ZiadAbdelati/waveshare-boost-gauge/docs/regression-ledger.md

# Regression ledger (full history)

The operating manual lives in [../AGENTS.md](../AGENTS.md). This file is the
verbatim chronological record of bugs, experiments, measurements and the
guards they produced; it was extracted from AGENTS.md on 2026-08-14 so the
manual could stay short while nothing was lost. Do not add new rows here unless
you are also reflecting the resulting invariant in the condensed guard rails in
AGENTS.md.

Many rows below are executable through the regression runners: the host suite
in `tools/tests/` (run via `python3 tools/test_suite.py`) and the hardware
release gates (`python3 tools/check_hardware_gates.py`). See
[`tools/tests/README.md`](../tools/tests/README.md) for the row -> test mapping.

The ledger table below has one row per entry: | Sequence | Symptom / finding | Root cause | Fix | Guard now required |.

## Chronological regression ledger

| Sequence | Symptom / finding | Root cause | Fix | Guard now required |
|---|---|---|---|---|
| iOS companion round 4: theme-specific settings moved to Themes-tab dropdowns, 5-minute logs window on both transports, landscape two-pane layouts (2026-08-26, iOS 26.3 simulator AF01E940 + host xcodebuild: 61 unit tests + 8 SimAcceptance green, Round4ScreenshotUITests portrait+landscape to /tmp/boostgauge-shots, vision QA PASS) | (1) Settings → Theme & demo still carried the three THEME-SPECIFIC toggles (Vault needle red, Vault needle tail, Big digit static bg) that `apps/PARITY.md` moved into the Themes-tab editor dropdowns; (2) the Logs graph defaulted to `limit=300` and then a background task re-fetched the FULL one-hour ring (`readLogSamples(limit: 18_000)`) — that payload times out over BLE into the 8-sample BGL1 fallback and an hour of dense sweep rendered as meaningless top/bottom bands; (3) every screen was single-column portrait-stacked, wasting the extra width in landscape. | The pre-PARITY Settings page combined global and theme flags; `LogsViewModel` was written when the app still offered a full-hour HTTP history surface (round-3 ledger), so it defaulted small then upgraded to 18,000; no orientation branching existed in the SwiftUI views (the Info.plist already declared landscape — the project had no orientation lock to lift). | (1) Removed the three toggles from `SettingsView.themeFlagsSection` and stripped `vaultNeedleRed`/`vaultNeedleTail`/`bigDigitStaticBg` from `SettingsViewModel` (published vars, `saveThemeFlags()` body, `applyThemeFlags()` decode) — the Theme & demo PUT now sends only demoMode/demoFastSweep/rotation/regionDBuf/teSync/teScanline/pixelShift(+interval) and can never clobber theme settings. The three settings already lived in the Themes editor dropdowns with their established labels (vault-tec: "Red needle"/"Counterweight tail", big-digit: "Static background"); bindings/save paths unchanged. (2) `LogsViewModel.load()` now fetches `GET /logs?limit=1500` (5 min at the 5 Hz log rate, `graphLimit`) as the PRIMARY on both paths — HTTP transport, or the derived HTTP host for BLE, or the BLE Control /logs route on the simulator — with NO 18,000 background fetch; the 8-sample BGL1 window (`readLogSamples(limit: 8)`) is a last-resort degraded error state ("BLE diagnostic window · 8 samples" + "5-minute history unavailable: …"). Copy updated: "Full history · N" → "Last 5 minutes · N samples". `SimBleTransport` now honors `?limit=` on `/logs` (no limit = the 18,000 ring; 1500 = the last 5 minutes) and `readLogSamples`/`readLog` always return the capped 8-sample window, mirroring the real Log characteristic. (3) Landscape via `@Environment(\.verticalSizeClass)`: StatusView lays the gauge card beside a TPMS/sensors/OBD2 stack in compact-vertical (landscape); ThemesView shows the circular preview in a 360 pt sidebar beside the theme List; Logs and Settings stay single-column. Same cards, colors, bezels, typography — no stretching. | Settings → Theme & demo is global/demo/debug flags ONLY (PARITY.md); theme-specific settings live exclusively in the Themes-tab editor dropdowns and the Settings save must never send them. The Logs graph fetches `/logs?limit=1500` on both transports and NEVER defaults to the 18,000 ring; the 8-sample BGL1 window is an error state only. Landscape layouts branch on `verticalSizeClass == .compact`; a capture quirk note for future sim work: rotating via `XCUIDevice.shared.orientation` makes the app lay out landscape (AX window 844×390) but the simulator framebuffer keeps the portrait buffer with the UI rotated 90°, so landscape screenshots must rotate the raw `app.windows.firstMatch.screenshot()` by 90° before review. |
| iOS companion round 5: single-series logs graph, graph readability (psi gridlines, time ticks, crosshair, window chips), width-relative landscape layouts (2026-08-26, iOS 26.3 simulators AF01E940 16e + C27D49FE Pro Max: build green, 65 unit tests + 10/10 SimAcceptance + 2/2 mock-backed UI tests green, Round5BScreenshotUITests portrait+landscape fresh captures to /tmp/boostgauge-shots/ios-round5b-*, Gemini vision QA PASS after one FAIL iteration) | (1) On a physical iPhone the logs graph drew TWO squiggly lines at a constant vertical offset; (2) the graph had no axis labels, no time ticks, no crosshair, and no window control — just a raw stroke; (3) round-4 landscape used fixed pt widths tuned on the small 16e sim, so on the Pro Max landscape Status/Themes content cramped into the left third, and the Themes landscape sidebar painted a different background below its pane boundary (a List-vs-custom-background seam). Vision QA additionally caught: landscape captures rotated the wrong way (180° off) and the five full "HH:mm:ss" time-tick labels collided on narrow portrait plots. | (1) The chart previously reduced each display column to a per-column MIN and MAX pair and stroked BOTH extrema as separate cyan lines — on the demo fast-sweep triangle (symmetric ±12 psi) the two extrema sit ~6 psi apart, so a dense sweep rendered as two parallel squiggles at constant offset. (2) The chart was a bare `Path` stroke with no axis furniture. (3) `StatusView`'s compact HStack and `ThemesView`'s 360 pt preview sidebar were content-sized or fixed-width, so they did not span a wide landscape screen; the Themes preview pane had no grouped-background treatment, so the List's own background ended at the pane boundary. The landscape raw window capture is stored by the simulator in a portrait buffer rotated 90°, and `sips -r 90` was the wrong direction (needs 270°). | (1) `LogPressureChart.series()` now reduces each column to ONE representative value (the column's last raw sample) and the chart strokes exactly one cyan line; psi is the only series drawn (peakPsi never enters the chart). Regression tests pin it: `testLogPressureChartSeriesIsOneValuePerColumn` (never a min/max envelope pair), `testLogPressureChartSeriesPreservesFastSweepExtremes` (full raw extent, no second track), `testLogPressureChartSampleIndexMapsColumnToRawSample`. (2) Graph readability added in `LogsView`: left psi gridlines with values (`chartDomain` snaps to nice steps, always includes 0), bottom time ticks (compact "HH:mm", collision-dropped when the plot is too narrow to fit five), a tap/drag crosshair showing psi + timestamp in a cyan pill that clears on release (fixture-pinned by `-e2eCrosshair` for screenshots), window chips 1m/5m/15m → `/logs?limit=300/1500/4500` with 5m default (`LogWindow`, `graphLimit` 1500). (3) Landscape: StatusView branches on `verticalSizeClass == .compact` into two `.frame(maxWidth: .infinity)` panes; ThemesView uses a width-relative preview pane via `containerRelativeFrame` (clamped 40% / 300-420 pt) beside the theme list, with `.scrollContentBackground(.hidden)` + `Color(.systemGroupedBackground)` on the preview pane so both panes share one grouped background (no seam). Landscape captures are host-rotated by `sips -r 270`. | The logs graph renders ONE psi series per display column — never a min/max envelope or a second peakPsi track, or the fast sweep draws twin parallel lines. The graph keeps the 5-minute default (`/logs?limit=1500`, never the 18,000 ring) and its window chips must stay 1m/5m/15m → 300/1500/4500. Time-tick labels must never overlap: compact "HH:mm" plus drop labels that collide on narrow plots. Landscape layout must be width-relative (GeometryReader/containerRelativeFrame/`.frame(maxWidth:.infinity)`) on BOTH device sizes — never fixed-pt panes — and any pane beside a List must share the List's grouped background so the shade never changes partway. The simulator landscape capture is a portrait buffer rotated 90°; host rotation must be 270°. Re-run: unit suite, SimAcceptance, and the Round5B screenshot capture before committing; verify fresh screenshots with the multimodal QA agent. |
| Android companion round 5: single-series logs graph, graph readability (psi gridlines, time ticks, crosshair, window chips) — iOS round-5 parity (2026-08-26, emulator-5554 simBle on demo fast-sweep triangle: compileDebugKotlin + testDebugUnitTest green with 56 unit tests incl. 9 new LogsChartReductionTest, assembleDebug + install green, portrait/landscape/crosshair captures to /tmp/boostgauge-shots/android-round5-logs-{portrait,landscape,crosshair}.png, Gemini vision QA PASS after one FAIL iteration on the landscape fold) | (1) The Android logs chart rendered the same two-line bug the iOS chart just fixed: it downsampled each display column to a per-column MIN/MAX pair and stroked BOTH the smoothed minima and maxima as separate cyan lines, so the demo fast-sweep triangle (symmetric ~±10-15 psi) drew as two parallel squiggles at a constant offset. (2) The chart had no psi gridlines/value labels, no time ticks, no crosshair, and no window control. (3) Round-4 Android chips were capped at {300,1500} and there was no 1m/5m/15m chip group or `/logs?limit=300/1500/4500` mapping; the graph also had no anchor-based absolute time labels. | Android `LogPressureChart` in `LogsScreen.kt` used `downsample()` returning `(mins, maxs)` per column and drew `trace(smoothMins,…)` AND `trace(smoothMaxs,…)` as two cyan `drawPath` strokes — the exact envelope pattern that renders as twin parallel lines under a dense sweep. There were no axis/gesture layers and `LogsViewModel` had no window enum or `/state` anchor for wall-clock labels. | (1) `LogPressureChart` now reduces each column to ONE representative value — the column's LAST raw sample (`chartSeries()`) — and strokes exactly one cyan path; `downsample`/`smoothEnvelope`/`smooth` deleted. Pinned by 9 new `LogsChartReductionTest` cases (one value per column, fast-sweep extremes preserved, sample-index mapping, nice-step domain, tick labels, collision-dropped axis ticks). Verified against the LIVE board fast sweep (`http://192.168.50.102/api/v1/logs?limit=1500`, raw -14.49/9.99 psi): 988 display columns, one value each, series extremes identical to raw — a single line, never an envelope. (2) Ported the iOS `LogsView.swift` furniture: horizontal psi gridlines with right-aligned value labels in the left gutter (`chartDomain` nice-step bounds, zero included), dashed zero line, bottom HH:mm time ticks collision-dropped when the plot is too narrow (46 dp min spacing), and a tap/drag crosshair (dashed cyan vertical line + dot + cyan pill "X.X psi · HH:mm:ss") that clears on release, anchored to absolute wall-clock via `repository.status` epoch/uptime/offset with a relative "-M:SS" fallback. `--ez e2eCrosshair true` fixture mirrors iOS `-e2eCrosshair` for deterministic captures. (3) `LogWindow` enum added (1m/5m/15m → 300/1500/4500, default 5m/1500) with cyan-highlighted capsule chips in the card header; source label reads the window scope. Chart geometry is density-consistent (single `plotRectPx` shared by draw and pointer mapping) so the crosshair column snap matches the drawn columns. | The logs graph renders ONE psi series per display column — never a min/max envelope or a second track, or the fast sweep draws twin parallel lines. Keep the graph's 5-minute default (`/logs?limit=1500`, never the 18,000 ring) and the chips at 1m/5m/15m → 300/1500/4500. Time-tick labels must never overlap (compact HH:mm + collision drop on narrow plots). The crosshair must clear on release and the psi gridlines/time ticks must stay legible in both orientations; Logs is a scrolling list in landscape, so captures must scroll the chart clear of the bottom nav bar (a swipe starting on the chart is consumed by the crosshair gesture, matching iOS). Re-run: Gradle compile/unit tests with `--rerun-tasks`, fresh emulator captures, and the multimodal QA agent before committing. |
| Android companion round 4: theme-specific settings moved out of Settings, 5-minute logs window on both transports, landscape two-pane layouts (2026-08-26, host + emulator-5554 simBle, vision QA) | (1) Settings → Theme & demo still carried the theme-specific toggles (Vault needle red, Vault needle tail, Big digit static bg) that PARITY.md moved into the Themes-tab editor dropdowns; (2) the logs graph defaulted to `limit=300` and BLE-without-LAN silently graphed the 8-sample BGL1 diagnostic window as if it were history; (3) all screens were single-column, wasting the extra width in landscape. | The pre-PARITY Settings page combined global and theme flags; `LogsViewModel` defaulted to 300 and `GaugeApi.getLogs` fell back to `readLog()` (8 samples) when the device-info STA IP was unreachable; no orientation branching existed in the Compose screens. | (1) Removed `vaultNeedleRed`/`vaultNeedleTail`/`bigDigitStaticBg` from `SettingsViewModel.FieldState` and the `saveThemeFlags` patch; Theme & demo now saves only demoMode/demoFastSweep/rotation/regionDBuf/teSync/teScanline/pixelShift(+interval). The three settings live only in the Themes editor dropdown with the iOS labels (Red needle, Counterweight tail, Static background — Android previously said "Needle tail"). (2) Logs default to `limit=1500` (5 min at the 5 Hz log rate, `LogsViewModel.LOG_WINDOW_SAMPLES`); chips capped at {300, 1500}; source label reads "Last 5 minutes · N samples". `GaugeApi.getLogs` on BLE prefers the LAN HTTP host from device-info, then a transport-served window (the emulator sim), else throws — an 8-sample BGL1 band is never graphed (error state only). (3) Landscape: Dashboard splits into two scrolling panes (hero+sensors | TPMS+OBD+error+footer); Themes becomes a square preview pane left of the scrolling theme list, capped to the pane's shorter side so it never overflows the short viewport; Settings stays single-column. Colors/bezels/typography unchanged. | Settings → Theme & demo is global/demo/debug flags ONLY; theme-specific settings appear exclusively inside the matching theme's editor dropdown with labels identical to iOS. The logs graph is the last 5 minutes (`/logs?limit=1500`) on BOTH transports and the 8-sample BGL1 window is a last-resort error state, never graph data. Landscape must use the extra width (side-by-side panes), never letterbox/stretch, and keep the portrait style identical. |
| iOS companion settings restructured to the canonical PARITY.md IA; sim transport made the scheme-default launch (2026-08-26, iOS 26.3 simulator AF01E940 + host xcodebuild, vision QA PASS) | The iOS Settings view had drifted from `apps/PARITY.md`: the psi range fields were duplicated on the "Display" page (Display should be brightness + dim schedule only), `appBle` had no spec home, and the default Xcode/simulator run showed no live data (no sim transport). Two latent defects surfaced while wiring it: (1) `project.yml` used `launchArguments:` (not a real XcodeGen key) so the scheme XML had an EMPTY LaunchAction command-line block; (2) when `commandLineArguments` was added to the top-level scheme, the BoostGauge TARGET's `scheme: testTargets:` block shadowed the top-level scheme, so the generated LaunchAction STILL had no `-e2eSimBle`; and once the arg finally landed, the 9 AppSessionTests broke because app-hosted unit tests inherit the scheme's Run-action launch args (`PROCESS_ARGS=...App|-e2eSimBle` proven in a scratch project), so `AppSession.init` saw `-e2eSimBle` and forced `SimBleTransport` for every test. SimBleTransport also lacked `tpms/config`, so the Settings root showed a spurious "TPMS: The selected gauge is no longer in range" error banner. | (1) XcodeGen only recognizes `commandLineArguments: {arg: enabled}` under run/test/profile; `launchArguments` is silently ignored. (2) A target-level `scheme:` block and a same-named top-level `schemes:` entry collide, and the target scheme wins (drops the run args). (3) `ProcessInfo.processInfo.arguments` in a hosted XCTest process contains the scheme's LaunchAction arguments, so E2E launch-arg flags leak into unit tests. (4) `SimBleTransport.get/send` handled only state/themes/config/calibration/logs — not `tpms/config`. | SettingsView: Display = brightness high/low + dim schedule + start/end + `appBle` (kept per "keep all bindings identical"; PARITY table omits it — intentional exception) + Save; Range = psiMin/psiMax/psiOverboost/zeroAngle + Save; TPMS BLE link moved off Theme & demo onto the TPMS page; root order Connection → Display → Range → Theme & demo → Clock & timezone → TPMS. project.yml: removed the redundant target-level `scheme:` block, added `run.commandLineArguments: {"-e2eSimBle": true}`, aligned target `IPHONEOS_DEPLOYMENT_TARGET` to 17.0 (the app already used iOS-17 `contentMargins`), regenerated with xcodegen (verified `argument = "-e2eSimBle"` in the scheme LaunchAction). AppSession init gates `-e2eSimBle`/`-hardwareBleE2E` on `NSClassFromString("XCTestCase") == nil` so hosted unit tests never inherit the sim/hardware E2E mode. SimBleTransport now serves GET/PUT `tpms/config`. SimAcceptanceUITests `testSettingsSubPagesAndTimezonePicker` updated to the new Display/Range/Theme&demo/TPMS pages (was asserting the removed "Gauge" page) and now also asserts root row ORDER and that TPMS BLE link lives only on TPMS; `SettingsAppBleUITests` navigates Display for the `appBle` toggle. | Keep the settings IA byte-for-byte with `apps/PARITY.md` (root order + exact titles; `tpmsBle` only on TPMS; `appBle` kept on Display as the single recorded exception). The scheme run args are `commandLineArguments` (never `launchArguments`), there must be no same-named target `scheme:` block shadowing the top-level scheme, and any `-e2eSimBle`/`-hardwareBleE2E`-style launch-arg flag MUST be ignored under XCTest (hosted unit tests inherit LaunchAction args). SimBleTransport must mirror the real API surface so the Settings root never shows a spurious not-in-range banner. Re-run: 61 unit tests green, full SimAcceptanceUITests green, vision QA on the four Settings screenshots PASS. |
| iOS companion themes-editor polish: expanded options panel aligned to the theme title, full-width Apply button, TPMS row icon (2026-08-26, iOS 26.3 simulator, vision QA PASS) | The expanded theme options (DisclosureGroup content) were visibly off-center: the panel content sat ~20 pt right of the theme title leading (x≈52 vs x≈32), the borderedProminent "Apply … options" button rendered as a content-hugging ~172 pt pill (`.frame(maxWidth: .infinity)` had no effect inside List DisclosureGroup content) centered in the shifted panel (x≈205 vs screen center 195), and "Reset to default colors" was left-aligned on a different axis below it. Separately the Settings TPMS row used a generic `car` glyph. | SwiftUI `List` indents `DisclosureGroup` content ~20 pt below the label, and a `Button` + `.frame(maxWidth: .infinity)` inside that content does NOT expand (the proposal resolves to the ideal width) — the pill only fills if the max-width goes on the button's LABEL. | `themeOptions` content gets `.padding(.leading, -20)` so the panel shares the theme title's leading axis; the Apply button uses `Button { } label: { Text(...).frame(maxWidth: .infinity) }` so the borderedProminent style fills the full panel (measured x 109..281 → 32..357); Reset stays flush-left on the same axis. Settings TPMS row icon changed `car` → `tirepressure`. SimAcceptance themes editor test still green (chevron, color wells, Apply button, no stray layout menu). Vision QA (rounds 1-3 + themes) PASS with zero defects. | Keep disclosure-content styling aligned to the title leading axis and make any full-width button apply `maxWidth: .infinity` to the label (not the button) inside List DisclosureGroup content. TPMS is a tire, not a car. Re-run: themes UI test + unit suite green before committing. |
| Android companion settings and theme preview parity pass (2026-08-26, host/emulator-verified) | Android settings previously combined Gauge controls, placed theme flags on Gauge, called the page TPMS & OBD2, and rendered the theme preview as a square. Clock sync also used a secondary row and descriptive copy. Two follow-ups surfaced during round-3 verification: the first canonical-render pass could land on a 0-size backing canvas (app.js resizes asynchronously), leaving the preview face solid black, and a duplicate inner pod treatment crept into `CanonicalGaugePreview`'s modifier chain, producing a doubled ring. | Android UI structure had not been split to the canonical `apps/PARITY.md` page inventory and the preview WebView had no circular pod treatment; the WebView's first `drawGauge` raced the app.js canvas resize (a later resize clears the 0-size canvas) and the rogue edit added a second pod inside the component modifier. | Android now exposes Connection, Display, Range, Theme & demo, Clock & Timezone, and TPMS in canonical order; theme flags and firmware-backed controls are grouped on their own page; clock sync is one full-width single-line "Sync timezone to gauge" button with an in-button saving spinner (timezone-only, phone zone like iOS); the preview is a padded circular pod (`ThemePreviewPod`: 1 dp dark rim + 8 dp `#0c0e12` ring + hairline rim, transparent corners, no shadow). `CanonicalGaugePreview`'s modifier is plain again (one pod, owned by the screen) and its `onPageFinished` re-runs the render at +400 ms/+1200 ms so the first paint is deterministic at the final backing size. Range field labels are the exact firmware keys (psiMin/psiMax/psiOverboost/zeroAngle); Theme & demo toggles use iOS wording; `appBle` toggle lives on Display (matches iOS; PARITY table omits it — intentional exception). | Keep Android page titles/order, field names, `tpmsBle` ownership, and circular transparent-corner preview aligned exactly with `apps/PARITY.md`; the preview pod ring lives ONLY in the screen composable (`CanonicalGaugePreview` modifier stays plain). Re-run Gradle compile/unit tests and emulator screenshot review after future UI changes. Evidence: `./gradlew compileDebugKotlin testDebugUnitTest assembleDebug` green (43 unit tests incl. `saveThemeFlagsRoundTripsNewFieldsThroughServer`), emulator-5554 simBle screenshots `/tmp/boostgauge-shots/android-round3-{themes,settings-root,display,range,themedemo,clock}.png`, Gemini visual QA PASS on all six after the render fix. |
| The DS3231 never became the clock authority: every read reported "time never set" even after a successful Sync, so the RTC always fell back to NVS (2026-08-17, built + flashed + hardware-verified) | After a clean software reboot (VCC never dropped) with a freshly seeded RTC, the boot log still showed `DS3231 detected at 0x68 (time never set - clock not trusted)` and `clock falls back to NVS/sync`; `/state.epochMs` was minutes stale on every reboot. This was true for the old DS3231 AND a replacement unit - so the chip was exonerated. | `boost_sensors_rtc_write()` wrote only the time registers (0x00-0x06); on the DS3231 writing the time does NOT auto-clear the oscillator-stop flag (status 0x0F bit 7). The seed path is gated on a clean read, so with OSF still set every read returned `ESP_ERR_INVALID_STATE` and the RTC never became trusted - it permanently fell back to the NVS epoch checkpoint. | `boost_sensors_rtc_write()` now clears OSF explicitly after the time burst: read status 0x0F, clear bit 7, write it back, all under the same bus-admin lock. Hardware-verified: after seed + software reboot the log reads `clock seeded from DS3231 (...)`, no OSF, no NVS fallback. (The earlier "battery doesn't hold time" conclusion was confounded by this bug - the RTC was losing its trusted state to a persistent OSF, not necessarily to a dead coin cell.) | A DS3231 write MUST clear the OSF bit explicitly (read-modify-write status 0x0F under the bus-admin lock); unlike some RTCs it is never auto-cleared by a time write, and a write that leaves it set keeps the RTC permanently on the NVS fallback. |
| The dashboard clock flickered 1 hour (17:44 <-> 18:44) while loading; `/state.timezoneOffsetMinutes` flip-flopped between the DST-effective and standard offset (2026-08-17, built + flashed + hardware-verified) | On web load the device clock readout rapidly alternated between an hour-apart pair of times, then settled. Polling `/state` showed `timezoneOffsetMinutes` flickering between the DST-effective value (-180 for a UTC-3 DST zone) and the stored standard (-240). | `s_state.timezone_offset_minutes` was written by four paths with conflicting semantics: `boost_model_refresh_status()` (16 ms loop) wrote the DST-EFFECTIVE value, but `boost_model_publish_sample()` (same 16 ms loop, right before) and the config-load/set_time paths wrote the STANDARD config value. Every tick publish_sample clobbered the effective value with standard and refresh_status overwrote it back, so `/state` GET (which just copies `s_state`) caught either - a sustained 1-hour clock flip in the UI. | `boost_model_publish_sample()` no longer touches `timezone_offset_minutes` (not a per-sample value; refresh_status owns it). `boost_model_set_time()` and the config-load path now write the effective offset via `boost_model_utc_offset_minutes_at(...)` so there is no standard-offset window after a sync or at boot. Hardware-verified: 30 rapid `/state` polls all report the single effective offset (-180), no flapping. | `/state.timezoneOffsetMinutes` is owned by `boost_model_refresh_status()` as the DST-EFFECTIVE value; the 16 ms `boost_model_publish_sample()` and the set_time/config-load paths must never clobber it with the stored standard offset, or the dashboard clock flickers 1 hour across DST. |
| Full-frame GIF push was ~10 ms over the wire floor (2026-08-17, built + flashed) | 466x466 full-frame push measured 21 ms in-loop against a ~13 ms wire floor; the perf push mean was 23.5 ms. Instrumented breakdown showed the byte-swap copy taking 16.2 ms (79% of the push) and DMA only ~4-6 ms. | The fused swap loop loaded/stored every pixel through `gif_u32_alias_t`, a `__aligned__(1)` typedef. Xtensa has no unaligned 32-bit load (`l32i` faults on a non-4-aligned address), so every nominal word access compiled to 4 byte loads + combines: ~10x the instructions of a plain memcpy (16.2 ms vs 5-7 ms for the same 434 KB stream). The `__aligned__(1)` alias is the anti-optimisation: it tells the compiler the pointer may be byte-aligned, so it can never emit word access. | Split the copy from the swap: one `memcpy` per strip (full-width strips collapse to a single contiguous copy; narrower strips keep per-row copies), then a tight 64-bit in-place byte-swap on the internal DMA buffer. The xfer buffers are now allocated with `heap_caps_aligned_alloc(8, ...)` (MALLOC_CAP_DMA alone only guarantees 4-byte alignment, which would make the direct `uint64_t*` access UB). A memcpy-per-8-byte variant of the swap measured ~2x worse (42 ms) from per-word call overhead and must not be reintroduced. Hardware-verified: full-frame push 21 ms -> 15.5 ms in-loop (copy 16.2 -> 7.9 ms, wire DMA ~6 ms), perf push mean 23.5 -> ~17.7 ms, cadence at 30 ms delay ~18.7 -> ~21 FPS. Colors unchanged, no panics, web healthy. | Do not reintroduce a per-pixel/per-word byte-swap through `gif_u32_alias_t` (or any `__aligned__(1)` type): on Xtensa it compiles to byte-wise access and costs ~10x a memcpy. The push strip copy must be memcpy-first then an aligned in-place swap on the internal DMA buffer. |
| GIF playback could run faster than the authored frame delay (2026-08-16, built + flashed) | Asked whether a GIF can play faster than intended: yes. The pipelined path set the timer period to `delay − last_push`, so a frame's on-screen time was `D − last_push + next_push`. A heavy full-frame push (large `last_push`) followed by a tiny delta push (small `next_push`) displayed that full frame for e.g. 13 ms against a 30 ms authored delay (~2.3x faster). A secondary race: `ms_delay_next` was read after `sem_next_decode` was given, so the Core-1 decoder could overwrite it with frame N+2's delay before the read. | The `D − last_push` compensation assumed every push takes the same time; variable push durations (full vs delta frames) made the compensation overshoot. | Deadline pacing: the next push now starts no earlier than `end_of_this_push + D`. Since the timer period is measured from the callback start and the just-completed push took `last_push_us`, the period is `D + last_push` — guaranteeing on-screen ≥ D (never faster; on average one push-duration slower, the accepted tradeoff). The frame delay is captured before waking the decoder. Hardware-verified: bulb.gif plays at its authored 30 ms cadence, 120/120 direct pushes, no panic. | The pacing guard is `period = D + last_push`, never `D − last_push`. Capture `ms_delay_next` before `xSemaphoreGive(sem_next_decode)`. |
| Post-audit fix round for the GIF playback branch (2026-08-16, built; hardware soak pending) | An independent audit of the `gif-playback-fps` diff found: (H1) the `initialize()` re-open teardown kept the double-free + fixed-15 ms decode-race the destructor fix had removed (latent — no caller re-opens a loaded widget); (H2) the `is_full_opaque` canvas-copy skip read the PREVIOUS frame's rect, so a partial/transparent frame after a full-opaque frame composited over a two-cycles-stale buffer; (H3) `sem_next_decode` was given before the push rect was read, so the Core-1 decoder could overwrite `gif->iX/iY/iW/iH` for frame N+2 while Core-0 pushed frame N+1 with a mismatched window; (M4) the LVGL fallback could not blend the RGB565_SWAPPED source (`LV_DRAW_SW_SUPPORT_RGB565_SWAPPED` = 0) so a refused direct push (e.g. regionDBuf toggled off, which frees the scratch strips) rendered a blank GIF; (M5) the fused LZW 8-pixel-wide stores could run up to 7 pixels past the framebuffer on the final string; (M6) an odd canvas origin (centered GIF < 466 px) made `r_fx` negative and the `read_fb` source offset wrap. | (H1) `initialize()` copied the pre-fix teardown; (H2) the skip keyed on stale geometry; (H3) the semaphore ordering race; (M4) the branch pre-swapped the palette to big-endian (RGB565_SWAPPED) but LVGL's sw renderer has no SWAPPED blend path, so the fallback path diverged from main; (M5) unbounded wide stores; (M6) round-down clamp below an odd origin. | (H1) `initialize()` now mirrors the destructor (snapshot fb0/fb1 before free, NULL `pFrameBuffer`, `decode_done` handshake). (H2) the canvas copy is now unconditional. (H3) the decoded rect is snapshotted into `gifobj->last_fx/fy/fw/fh` before `sem_frame_ready` and `invalidate_frame` takes the snapshot. (M4) reverted to a little-endian RGB565 framebuffer: palette loads store LE, the widget uses `LV_COLOR_FORMAT_RGB565`, and the direct push re-added the fused LE→BE byte-swap (restoring main's proven fallback; the swap cost is proportional to the dirty rect, so delta frames keep 60 FPS). (M5) framebuffers now carry a 16-pixel pad (`GIF_FB_PAD_BYTES 32`) while `imgdsc.data_size`/stride stay exact. (M6) the clamp rounds up to the next even >= origin and zero-area rects fall back to LVGL. Clean build. | The decoder must emit little-endian RGB565 (the direct push swaps; the LVGL fallback does not). The push must read the snapshot rect, not live `gif->iX/iY/iW/iH`. The canvas copy before each decode is unconditional. Fused wide stores stay within the padded framebuffer. Odd origins round up to even. Re-open teardown must use the `decode_done` handshake and snapshot-before-free. |
| Deleting the GIF crashed the board: it vanished, came back at max brightness, web down (2026-08-16, flashed + measured) | Clicking Delete in the web UI made the GIF disappear, then the board rebooted, the GIF auto-reloaded at boot brightness (100% during the day), and the web was unreachable during the reset. `DELETE /api/v1/media` panicked with `Guru Meditation` (double free) in `lv_gif_destructor`. | The dual-buffer pipeline sets `gif->pFrameBuffer = gifobj->framebuffers[idx]`, but `lv_gif_destructor` freed and NULLed `framebuffers[0]/[1]` BEFORE the ownership guard `framebuffer != framebuffers[0]` compared against them. With both pointers NULL the aliased `pFrameBuffer` slipped past the guard and was `lv_free`'d a second time -> double free -> panic -> reboot. A secondary race: the decode-task teardown used a fixed 15 ms delay, shorter than a mid-frame ~25 ms decode, so a frame in flight could touch freed framebuffers. | Snapshot `framebuffers[0]/[1]` ownership pointers before freeing them so the alias check stays meaningful, `gif->pFrameBuffer = NULL` before the pipeline frees (separate buffers still freed exactly once), and replace the 15 ms delay with a `decode_done` flag set by the decoder before `vTaskDelete` so the destructor waits out a full frame. Verified: DELETE returns 200 `present:false`, no panic in serial, board holds continuous uptime (200 s+) afterwards. | The destructor must never free an aliased pipeline framebuffer twice; snapshot ownership pointers before NULLing them and wait out any in-flight decode before freeing decoder-owned memory. A delete that reboots the board (GIF auto-reloads at boot brightness) is the failure mode to watch for in any future media-teardown change. |
| BLE disconnected retry loop saturated the radio and stalled the web when the stored peer was absent (2026-08-16, flashed + measured) | With `tpmsBle` on and the FD+ adapter not reachable (bench), the web UI periodically froze for seconds and HTTP latency spiked (p95 191 ms, max 291 ms, occasional timeouts); the physical screen briefly showed white/green streak artifacts during the worst window. Serial showed `connect failed: status=0x000d` then a 3 s discovery scan repeating every ~13 s. | The disconnected retry loop is fixed 10 s backoff + 3 s scan forever when the stored peer never answers, and the connect attempt runs a full 5 s. These periodic BLE bursts saturate the ESP32-S3's single 2.4 GHz radio, which also carries STA + SoftAP. (BLE code is identical to main; the aggression shows whenever the adapter is absent, e.g. bench, not when connected in the car.) | Exponential inter-scan backoff (`OBD_RECONNECT_MS 10000`, `OBD_RECONNECT_MAX_MS 120000`): after each failed scan/connect cycle the delay doubles (10 → 20 → 40 → 80 → 120 s cap), resetting to 10 s on any connect and on a manual re-enable. A dropped *connected* link keeps the fast 10 s retry. Measured with BLE on: p95 191 → 118 ms, max 291 → 169 ms, 0 timeouts. The prior GIF worktree regression (decode task priority starving httpd/ws on Core 1) is separate and fixed in `f548306`. | An unreachable stored peer must back off exponentially (cap ~2 min) so an absent adapter stops hammering the radio; present peers are still found within one scan period and a dropped connected link keeps a fast retry. Do not reintroduce a fixed ~13 s scan loop for the disconnected state without re-measuring web latency. |
| Fused Turbo LZW + direct big-endian RGB565 emission + Core 1 decode pinning (2026-08-16, flashed + measured) | Decode was taking ~25.2 ms due to separate 8-bit LZW decompression into `pTurboBuffer` followed by a second memory pass in `DrawCooked()` (converting 217 KB to 434 KB in PSRAM). Direct push was also taking ~18.5 ms due to scalar byte swapping in `boost_display_push_bitmap()`. | (1) Two sequential PSRAM passes (write indices -> read indices -> write RGB565) incurred unnecessary PSRAM cache line fills. (2) `boost_display_push_bitmap` performed per-pixel byte swapping instead of 32-bit paired transfers. (3) `gif_decode_task` was competing with LVGL on Core 0. | (1) Pre-swapped the 256-entry palette to big-endian RGB565 wire format during palette load. (2) Fused Turbo LZW dictionary emission directly into 16-bit RGB565 framebuffer writes (`LZWCopyBytesFused`) on full-width opaque frames, eliminating the second memory pass. (3) Replaced scalar byte swaps in direct push with 32-bit direct `memcpy` into `s_region_xfer_bufs`. (4) Pinned `gif_decode_task` to Core 1 at priority 5 and preserved the 40,960 B BLE DMA internal RAM pre-init guard. Hardware verified on 466x466 fixture (1,889,384 B, 101 frames): decode mean 24.3 ms (15.5 ms on deltas), push dropped 18.5 ms -> 13.8 ms (at the ~13.5 ms physical QSPI floor), 0 push fallbacks, 0 panics, cadence guard passing (dyno-cell demo 61 FPS). | Fused LZW palette emission applies to contiguous full-width opaque frames; partial/transparent frames retain `DrawCooked()` fallback. Direct panel push requires big-endian wire format RGB565. Keep Turbo LZW table allocations in PSRAM to prevent starving BLE/DMA internal memory pool. |
| Turbo LZW + 32-bit paired stores + dual-core pipelined decode accelerates GIF playback to 30+ FPS (2026-08-16, flashed + measured) | GIF playback on the 466x466 fixture was decode-bound at ~37.3 ms per frame, limiting serial direct-push playback to ~18 FPS regardless of transfer throughput. | (1) Standard LZW decode performed per-pixel reverse stack walks and linked-list traversals across PSRAM memory. (2) `DrawCooked()` used individual 16-bit stores for every pixel. (3) `DecodeLZWTurbo` was previously compiled out because upstream turbo required a `pfnDraw` callback with 2 planes. (4) Decode on Core 1 was serialized with panel DMA transfers. | (1) Enabled `GIF_SUPPORT_TURBO` in `boost_gif_dec.h/.c` adapted to direct-to-framebuffer `DrawCooked()`. (2) Allocated `pTurboSymbols` (16 KB) and `pTurboLengths` (8 KB) from fast internal RAM (`MALLOC_CAP_INTERNAL`) for single-cycle table access. (3) Accelerated `DrawCooked()` with 32-bit paired pixel stores (`uint32_t`) and 8-byte batch reads (`INTELLONG64`). (4) Implemented dual-core pipelining: a background `gif_decode_task` on Core 0 decodes frame N+1 into double-buffered PSRAM canvas (`framebuffers[2]`) while Core 1 transfers frame N to panel via DMA. Measured on hardware: decode dropped 37.3 ms -> 25.2 ms (-32%, and down to 13.1 ms on deltas), push 16 ms, 119 direct pushes per 120 frames, 0 fallbacks. | Turbo LZW symbol/length tables (24 KB) must stay in internal RAM for single-cycle access. Double-buffered framebuffers in PSRAM allow Core 0 decode to overlap Core 1 DMA panel transfers without data hazard. |
| Direct-push delta GIF frames suffered horizontal image shifting and streaking (2026-08-16, flashed + measured) | While full-frame GIF colors were correct, occasional partial/delta frames caused the image to visibly jump horizontally (shift to the left) and leave visual streaking artifacts across the panel. | The CO5300 AMOLED QSPI controller hardware requires CASET (column) and RASET (row) window boundaries to be 2-pixel word aligned (even x1/y1 and odd x2/y2 in inclusive coordinates, or even x0/y0/x1/y1 in exclusive coordinates). In the LVGL render path, `rounder_event_cb()` enforces this on all invalidated areas. The direct-push bypass in `boost_gif.c` passed unrounded delta frame coordinates (`img_area.x1 + fx`, `fw`, etc.) straight to `boost_display_push_bitmap()`. When a delta frame had an odd column or row start, the CO5300 hardware window misaligned with the 32-bit QSPI pixel stream, shifting the pixel data horizontally by 1 pixel. | `main/gif/boost_gif.c` now rounds the dirty rectangle coordinates to even `x1/y1` and odd `x2/y2` (matching `rounder_event_cb` and clamping to canvas bounds), computing `r_fx, r_fy, r_fw, r_fh` so that both the panel window and the `src` offset into `pFrameBuffer` are strictly 2-pixel aligned. Pushed exclusive coordinates `dirty.x1`, `dirty.y1`, `dirty.x2 + 1`, `dirty.y2 + 1` are all guaranteed even. Hardware verified: 119/120 direct pushes, 0 fallbacks, clean playback with zero horizontal shifting or streaking. | Any direct panel push path must strictly obey the CO5300 2-pixel even/odd boundary constraint (`dirty.x1` even, `dirty.x2` odd / exclusive `x1` even). Never send unrounded delta/partial coordinates directly to `esp_lcd_panel_draw_bitmap()`. |
| Direct-push GIF frames arrived color-scrambled with artifacts ("horror edit"); occasional single correct frame per loop (2026-08-16, flashed + measured) | First hardware run of `boost_display_push_bitmap()` showed fully corrupted colors and random flashing on the GIF; once per animation loop one frame looked correct. | The adapter bridge byte-swaps every RGB565 pixel to big-endian before the panel sees it (`lvgl_bridge_v9.c` `display_bridge_v9_flush_default`: `lv_draw_sw_rgb565_swap` for `ESP_LV_ADAPTER_PANEL_IF_OTHER` + RGB565, applied BEFORE the `custom_draw_bitmap` hook). The CO5300 QSPI wire format is big-endian RGB565; the GIF decoder's framebuffer is little-endian (`GIF_PALETTE_RGB565_LE`). The direct push bypassed the bridge entirely and sent little-endian pixels straight to the panel - red/blue channels swapped and the 5-bit green field misaligned. The once-per-loop correct frame was the `force_full_invalidate` LVGL fallback (which goes through the bridge swap). This is also why `region_dbuf_writeback()` must NOT swap: its strips arrive pre-swapped from the hook. | `boost_display_push_bitmap()` now byte-swaps each 20-line scratch strip after the row copy (before `esp_lcd_panel_draw_bitmap`), leaving the source framebuffer untouched little-endian LVGL image data. Hardware-verified: colors correct, 119/120 direct pushes, 0 fallbacks; push mean 18.2-18.7 ms (up from 15.7-17.6 pre-swap; the per-pixel swap costs ~2.6 ms/full frame), decode unchanged ~38 ms. | Any path that feeds `esp_lcd_panel_draw_bitmap()` directly MUST byte-swap RGB565 to big-endian first (or prove the source is already swapped); the LVGL/region-dbuf strips are pre-swapped by the bridge, direct sources are not. When adding a direct panel path, A/B against the bridge's flush (`display_bridge_v9_flush_default`) for format, stride compaction, and swap - the hook receives transformed data, not raw LVGL buffers. | | The 466x466 fixture (`IMG_5325-ezgif.com-optimize.gif`, 1,889,384 B, 101 frames, 98% full-frame dirty rects) played at 14-20 renders/s through the LVGL widget path (baseline, README). The user asked for 30 FPS minimum, 60 if possible. | Per-frame cost was serial on the LVGL task: (1) `GIF_playFrame` decode ~36.4-37.7 ms (LZW + palette LUT + PSRAM framebuffer composition), (2) LVGL render re-blit of the frame rect into internal-DMA strips (~3.16 Mpx/s measured, ~69 ms/217k px full-frame equivalent budget share), (3) QSPI transfer 13.6 ms floor. The re-blit is redundant: the decoder's framebuffer already holds panel-ready RGB565 for exactly the frame rect. | New `boost_display_push_bitmap()` in `main/boost_display.c` (exported in `boost_display.h`): pushes an RGB565 rect straight from the caller's buffer (arbitrary row stride) to the panel in the same 20-line chunks + one `te_wait_for_region_spans()` TE wait as `region_dbuf_writeback()`, reusing the region-dbuf internal DMA scratch strips (no new internal RAM; refuses with `ESP_ERR_NOT_SUPPORTED` when region-dbuf strips are unallocated, rotation != 0, or args are invalid, so the caller falls back to LVGL). `main/gif/boost_gif.c` `invalidate_frame()` now tries the direct push first under the same bounded-placement conditions as the bounded LVGL invalidation (1:1 blit, no rotation/scale); success skips the LVGL invalidation entirely, failure falls back. Timing instrumentation added (`perf:` rate-limited log): decode us and push us means/last per 120-frame window. **Measured on hardware**: 119/120 direct pushes, 0 fallbacks; decode mean 36.4-37.7 ms, push mean 15.7-17.6 ms (vs 13.6 ms pure-transfer floor; TE wait included); ~18.7 FPS on this worst-case 98%-full-frame fixture (vs 14-20 baseline). Upload 1,889,384 B in 9.52 s; delete/resume verified (gauge 61 FPS post-teardown); dyno-cell demo cadence guard min 57 / median 61 PASS; serial clean (no `ESP_ERR_NO_MEM`, no `send color data failed`). | Direct push is valid ONLY under: display lock held (LVGL task context during media), rotation 0, 1:1 bounded placement, region-dbuf scratch strips allocated. Off-by-one contract: x1/y1 end-EXCLUSIVE (a first flash measured 115/120 fallbacks because `+fw+1` sent 467 > 466 and every full-width frame fell back - the perf log caught it). Decode is now the dominant cost; the next levers are pipelining decode against push and turbo LZW, both requiring this instrumentation. The `perf:` line must stay available (BOOST_GIF_LOG_DIRTY_RECT) for any future playback work. |
| Wall clock depended on Wi-Fi; a DS3231 on the sensor bus now makes it battery-backed offline (2026-08-17, OTA via /api/v1 + API-verified on hardware) | The clock only ever came from a browser Sync over Wi-Fi; unreliable connectivity left the device on a frozen NVS clock with the dim schedule disabled. User fitted a DS3231 (0x68) on the sensor I2C bus (GPIO18/17, port 0). | There was no RTC/NTP anywhere: `boost_model_set_time()` (web `POST /api/v1/time`) was the only settimeofday source, and a power cycle froze the NVS epoch because the monotonic checkpoint dies with it. The DS3231 is a third device on the already-owned sensor bus. | DS3231 driver lives in `boost_sensors.c` (same bus, reset, admin lock, 100 kHz): `boost_sensors_rtc_read/write`, probe 0x68 in `detect_sensors()` (idempotent handle teardown before re-detect), OSF/BCD/range validation so a fresh part never seeds `2000-01-01`, 24-hour-mode burst writes. `boost_model_seed_clock_from_rtc()` (new) seeds `settimeofday`, sets `s_clock_trusted = true` and refreshes the NVS epoch checkpoint as a warm fallback; `main.c` runs sensors init + seed BEFORE `boost_model_boot_brightness()`/`boost_display_start()` so a night boot with an RTC comes up dim with no Wi-Fi. `boost_model_set_time()` additionally writes the RTC, making Sync the calibration action. No-RTC/OSF/read-failure falls back to the previous frozen-NVS + untrusted behavior. Web UI: `timezoneOffsetMinutes` (DS3231 keeps UTC) and Sync Time remain; the cockpit numeric offset box is now a fixed-offset Time zone dropdown (39 entries, `tools/embed_web.py` regenerated) that is set once and is no longer overwritten by the browsers live offset on refresh. | The DS3231 (0x68, sensor bus) is the battery-backed clock authority when present; its read must reject OSF/garbage/implausible time and the seed must run before boot brightness is decided. Never move sensors/seed back after `boost_display_start()`, and keep `s_clock_trusted` false for a frozen NVS restore so the no-RTC path still boots bright. Re-verify over `/api/v1` after OTA: `epochMs` current with no sync; `sensors/scan` lists 0x68; a night-boot dims without Wi-Fi; `POST /time` then power-cycle still shows current time (RTC persisted). **Verified 2026-08-17:** OTA boots v0.7.1-65-gb14e8e4; `sensors/scan` lists 0x68; `epochMs` matches the host within a second with no browser sync; the dim schedule engaged (brightness 25%) when the window was temporarily bracketed around now, then restored; `POST /time` then reboot re-seeded from the RTC (delta <1 s) proving the write path. A stale `POST /time` from a browser with a 10-min-slow clock wrote the RTC 611 s off and the next boot seeded that stale value - the RTC only stores what the last Sync wrote, so the dashboard dropdown is the fix for the timezone, and a clock check before Sync is the user side. ADS1115 (0x48) was absent from the bus at this verification while 0x68/0x76 were present - unrelated wiring, noted for the other session. |
| A browser with a 10-min-slow clock wrote the DS3231 ~611 s off and the next boot seeded that stale time; the RTC "trusted whatever wrote it" (2026-08-17, built; OTA/API verification pending) | A browser whose system clock was 10 minutes slow sent `POST /api/v1/time` on a dashboard refresh; the device accepted it, wrote the DS3231, and the next boot seeded the stale epoch, leaving the whole clock 611 s wrong. The RTC is the battery-backed authority, so a wrong client was silently corrupting it. | `boost_model_set_time()` validated only `epoch_ms > 0`; the RTC WRITE path had no plausibility or authority check, while the READ path already rejected OSF/garbage/<2023. Any `POST /time` (refresh auto-sync or manual Sync) could therefore write any epoch to the RTC. | `boost_model_set_time()` now enforces the shared `BOOST_RTC_EPOCH_MIN_MS` floor (>=2023) and, when a valid DS3231 is present and readable, rejects a client epoch more than `BOOST_RTC_SYNC_TOLERANCE_MS` (5 min) from the RTC with `ESP_ERR_INVALID_STATE`, mapped by `time_post` to HTTP 409 `clock_rejected` - evaluated BEFORE settimeofday/NVS/RTC write, so a rejected sync corrupts nothing. OSF/unreadable/absent RTC falls through (first seed / battery change). The DS3231 drifts ~63 s/year, so a >5-min client gap is a wrong client, not a correction; corruption within the window self-heals on the next correct sync, beyond it pull the battery to reset OSF. Web `syncTime` maps `clock_rejected` to a clear message. | The RTC is the WRITE authority once valid: reject any client sync more than 5 min from it (409 `clock_rejected`, before the system clock/NVS/RTC are touched); accept any plausible epoch only when the RTC is OSF/unreadable/absent. Re-verify: wrong epoch -> 409 + RTC unchanged; correct epoch -> 200 + RTC recalibrated; fresh part -> seeds. |
| I2C bus diagnostics: the ADS "dropped off" the scan without hardware changes, and a rapid scan burst wedged httpd (2026-08-17, source; OTA/API verification pending) | `/api/v1/sensors/scan` went `found:[]`, then `["0x48","0x68","0x76"]`, then `["0x68","0x76"]` with no hardware touched; later a burst of rapid scans left the board ping-alive but httpd-dead (not rebooting). | (1) The 4-ACK scan filter is a weak witness on this documented-marginal bus (a real device measured 0-4/32 ACKs, row 98) and the reader hammers the ADS at 62.5 Hz, so the ADS is the systematically most-likely false negative; an intermittent bus sampled 3x reads exactly like this. (2) `i2c_master_bus_reset()` takes no internal lock, and the DS3231 read/write were the only bus users outside the bus-admin mutex, so a recovery reset could FSM-abort a mid-burst RTC transaction. (3) `bus_recover()` ignored the ADS/BMP re-config returns - a failed ADS reconfig silently reads 0 V "successfully" (fresh timestamps, no fault). (4) Presence was a single-probe boot lottery never re-probed, so a device absent at boot stayed absent until reboot. (5) The scan held the bus-admin lock for up to ~22 s on a hung bus (112 x 4 x 50 ms), so queued scans starved the single httpd task. | (1) Scan capped to `SCAN_TIME_BUDGET_US` (5 s) so a hung bus cannot wedge httpd. (2) `boost_sensors_rtc_read/write` now hold the bus-admin mutex (bounded 500 ms `RTC_LOCK_WAIT_MS`), serializing against reset/scan like every other non-reader path. (3) `bus_recover()` logs re-config failures (a silent 0 V false-good is now surfaced) and calls `reprobe_absent()` to re-probe devices that were absent at boot - presence is no longer frozen forever. | Every I2C path outside the reader must hold the bus-admin mutex (the reset takes no lock); the live scan is a weak witness and must be time-capped so it cannot wedge httpd; recovery must honor re-config returns and re-probe absent devices. Re-verify over the API: a long scan on a hung bus returns within ~5 s and httpd stays responsive. |
| A DST-region user must re-pick the offset twice a year because the timezone was a fixed offset; the device now stores a POSIX TZ string and localtime() handles DST (2026-08-17, source; host build; OTA/API verification pending) | The timezone was a single fixed `timezoneOffsetMinutes`; a user in a DST region had to re-pick their zone each season, and the device clock/dim schedule/CSV were 1 h off during DST. | All UTC->local conversion did manual minute arithmetic with one fixed offset, so it could not know DST. The firmware had no timezone concept beyond that integer. | `boost_config_t` gains `timezone_tz[48]` (POSIX TZ string, e.g. `EST5EDT,M3.2.0/2,M11.1.0/2`), migrated in place from the prior layout (`boost_config_v2_t`); `boost_model_apply_timezone()` does `setenv("TZ")+tzset()` at boot and on change. The dim schedule and CSV now use `localtime_r()`, so DST is automatic. Because newlib has no `tm_gmtoff`/`timegm`, the effective offset is derived by comparing localtime vs gmtime via days-from-civil (`boost_model_utc_offset_minutes_at`); `/state` reports it (DST-aware) for the dashboard clock, while `/config` keeps the stored standard `timezoneOffsetMinutes` for the dropdown. The web dropdown carries the POSIX TZ string per option (US/CA/Europe/AU/NZ DST rules verified against GNU date; non-DST zones synthesize `UTC±H`); `/time` and `/config` accept `timezoneTz`. Legacy configs without a TZ string fall back to a synthesized fixed offset. Web assets + mock_server regenerated. | The timezone is a POSIX TZ string applied via `setenv("TZ")+tzset()`; every UTC->local conversion (dim schedule, CSV, effective offset) must go through `localtime()`/`localtime_r()` - never manual offset arithmetic - and the effective offset must be derived without `tm_gmtoff`/`timegm` (compare localtime vs gmtime). Re-verify on hardware: `POST /time` with an Eastern TZ string shows the correct DST-effective `timezoneOffsetMinutes` in `/state` and the right local CSV timestamps. |
| MX-5 ND TPMS DIDs answered but were rejected as `undecoded`; the parser assumed a two-byte value (2026-08-15, flashed + measured) | On the Miata (CAN) the TPMS module answered every `22 2A xx` read with a valid UDS positive response, but no tire data reached the dashboard. Serial showed `DID 2A05: undecoded '622A058C'`. | The module answers these DIDs with a SINGLE data byte (`0x62 DID-hi DID-lo value`, a 4-byte response), while `boost_tpms_protocol_parse_uds_response()` hard-required `length == 5` (two-byte raw value). The `RAW_TO_KPA 1.373` scale (=350/255) is correct for the byte: 0x8C=140 -> 192 kPa ~= 28 psi. | `boost_tpms_protocol_parse_uds_response()` now accepts both `length == 4` (one-byte value, raw = `payload[3]`) and `length == 5` (two-byte value). `tools/test_tpms_protocol.c` gained a 4-byte case and the former 4-byte "wrong length" case became a 3-byte rejection. Verified on the car: `DID 2A05 = 127`, `2A07 = 131`, `2A06 = 143`, `2A08 = 145` (~25-29 psi, plausible for a stationary cold car). | The MX-5 ND TPMS pressure DIDs return a one-byte value; the parser must not hard-require a two-byte raw. Re-verify on the car that all four DIDs decode to plausible kPa/psi. |
| SoftAP starved by the zero-backoff STA reconnect loop; the dashboard was slow/unreachable on AP-only (2026-08-15, flashed + measured) | With a saved SSID out of range, the web UI over the SoftAP was very slow to load; once the STA associated, the AP was fast again. Serial showed `STA disconnected reason=201` every ~2.8 s. | AP and STA share one radio; the disconnect handler called `esp_wifi_connect()` immediately on every `WIFI_EVENT_STA_DISCONNECTED`, so an out-of-range SSID looped `scan -> fail -> reconnect` and repeatedly yanked the radio off the AP channel, starving the AP's beacons. | A one-shot FreeRTOS timer back-off (`WIFI_RECONNECT_DELAY_MS 10000`): the disconnect handler now resets the timer instead of reconnecting directly, and `IP_EVENT_STA_GOT_IP` stops it. The initial boot connect and user-initiated reconnect/config-change stay immediate. Measured: `reason=201` spacing went ~2.8 s -> ~10-15 s. | The STA auto-reconnect must back off (never reconnect immediately on every disconnect) or a persistent out-of-range SSID starves the SoftAP; the timer is the only auto-retry path, user-initiated paths stay immediate. |
| `demoFastSweep` did not survive a reboot; the Settings linear-sweep choice silently reverted to the organic waveform (2026-08-15, host build) | The dashboard demo selector offers Off / Demo / Demo + linear sweep, but the linear-sweep arm was transient: every boot came up on the organic sine sweep regardless of what the user last selected, while every other setting in the same panel persisted. | `s_fast_sweep` lived only in `boost_sim.c` and `boost_sim_init()` explicitly reset it to `false` every boot; nothing in the theme NVS store read or wrote it, and the web PUT only poked the runtime flag (`boost_sim_set_fast_sweep()`) with no `persist()`, so the choice was never saved. | The flag stays in `boost_sim.c` (single source of truth); `boost_theme.c` owns persistence exactly like `demo_mode`. New NVS key `demo_fast_sweep` in the same `boost` namespace, written in `persist()` from `boost_sim_fast_sweep()` and loaded in `boost_theme_init()` (applied via `boost_sim_set_fast_sweep`). `boost_sim_init()` no longer resets the flag, so the boot-time load (main.c runs `boost_theme_init()` at line 101 before `boost_sim_init()` at line 128) survives into ticking. New `boost_theme_set_demo_fast_sweep()` is the single write path (runtime set + persist); the web PUT calls it instead of poking the sim directly, and the GET already reads `boost_sim_fast_sweep()`. Stored and toggled independently of `demo_mode` - it only has an effect while demo mode is on. Comments updated in `boost_sim.h/.c`, `boost_web.c`, `web/settings.html` (hint no longer claims transient) and `tools/bench_fast_motion.py` (cleanup still restores the organic waveform after a run); web assets regenerated. | `demoFastSweep` must persist across reboot exactly like `demo_mode` (NVS `demo_fast_sweep`, loaded by `boost_theme_init` before the sim ticks). Never reintroduce a `s_fast_sweep = false` reset in `boost_sim_init()` - the boot value comes from the theme store load. Keep the two flags separate; a persistence change to one must not couple the other. |
| Mode-01 PIDs read 0 on the K-line Camry mule; header switching applied CAN IDs to ISO 9141-2 (2026-08-14, flashed + measured) | In the 2003 Toyota Camry (ISO 9141-2 K-line, engine running) the FD+ links up and `ATRV` reads ~13.5 V, but rpm/speed/coolant all read 0 in the web UI. Serial (USB-JTAG `/dev/ttyACM0`) showed the ELM init completes, the `0100` prime **succeeds** (`protocol primed: 0100='4100BE1FA811'`), and then every mode-01 PID and TPMS DID returns `NO DATA` forever. | The prime runs on the ELM's auto-detected default header, which is correct for K-line. But the poll loop then unconditionally switches the header to `ATSH 7DF` for mode-01 PIDs (and `ATSH 720` for TPMS DIDs). `7DF`/`720` are ISO 15765 CAN identifiers; issued as `ATSH` on ISO 9141-2 they replace the correct K-line header with garbage, so the ECU never answers and every request returns `NO DATA`. The init-time `ATDP` also read `AUTO` because it was queried before `ATSP0` had locked anything, so the code had no locked-protocol signal to gate on. | The header switch is now **CAN-only**. `boost_obd.c` re-queries `ATDP` once after the `0100` prime (the point where the protocol is actually locked) and sets `proto_is_can = strstr(reply, "CAN") != NULL`. Only when `proto_is_can` does the loop set `ATSH 720`/`ATSH 7DF`; on a legacy K-line/J1850 bus it keeps the auto-detected default header for the mode-01 PIDs (so the Camry reads rpm/speed/coolant) and skips the Mazda TPMS DID phase entirely (no such module on that bus; `pending_mask` never fills, so TPMS correctly ages to STALE/DISCONNECTED). `proto_is_can`/`proto_checked` reset on link drop so a reconnect re-detects. The Miata path (CAN) is byte-for-byte unchanged. | The header-switch guard must key off the LOCKED protocol (an `ATDP` after the prime), never the init-time `AUTO` read; and `ATSH 7DF`/`720` must never be sent on a non-CAN bus. **Verified on the Camry** (built + flashed on a native ESP-IDF 5.5.1 Linux host, USB-JTAG): `ELM protocol locked: AUTO, ISO 9141-2 (CAN=0)` then live decodes — `PID 010C = 667.8..708.5` rpm (idling), `0105 = 85.0` coolant, `010D = 0.0` speed (parked), `010F = 55.0` IAT, `0111 = 15.7` throttle, `0110 = 3.7` MAF; only `010B`/`012F` return `NO DATA`, matching the Camry's `BE 1F A8 11` support bitmask (MAP/fuel genuinely unsupported). Still required before claiming the MX-5 works: re-run on the ND (CAN) to prove the TPMS DIDs still decode with `ATSH 720`. |
| Boot dim schedule trusted a frozen clock; a board synced last night booted dim the next day (2026-08-14, built) | User powered up during daytime and the panel came up dim, outside the dim-schedule hours. | The dim schedule evaluated the wall clock via `epoch_ms_now()`, but across a full power cycle that clock is only a frozen NVS restore: `load_config` advances the saved epoch by the monotonic delta only when `now_mono_ms >= saved_mono_ms`, which a power cycle always fails (the RTC timer resets), so the clock stays pinned at the last Sync. A board last synced at night therefore read as "night" the following afternoon and booted at `brightness_low`. | `s_clock_trusted` (file-static bool) is set true only by `boost_model_set_time()` (a browser Sync) or by a boot restore whose monotonic delta survived (soft reset). `boost_model_schedule_wants_low()` returns false when `!s_clock_trusted`, so an unknown/frozen clock defaults to bright and the schedule engages only after the next Sync (the cockpit refresh auto-syncs, or manual Sync Time). `epoch_ms_now()`, CSV timestamps and `/state.epoch_ms` still report the best-effort restored clock, unchanged. | A dim-schedule decision must never treat a frozen NVS-restored clock as authoritative; the only times the schedule may trust the clock are after a Sync this session or a monotonic-preserving soft reset. Re-verify on hardware: power up during the day after a prior night-time sync -> boots bright; power up at night -> bright until the dashboard syncs, then dims. The night-boot "brief bright until Sync" is the accepted cost of no RTC/NTP, not a regression to patch over. |
| Two-finger hold → AP-join QR; CST9217 two-point touch vendored; panel boots dark then ramps (2026-08-14, flashed; on-glass pending) | User wanted a two-finger tap-and-hold to summon an AP-join QR, distinct from the 1 s hold-to-dim, a fresh boot that obeys the dim schedule without a bright/white flash, and a faster boot. | (1) The first two-finger attempt failed on glass because the read was wrong: the stock `waveshare/esp_lcd_touch_cst9217` driver caps the CST9217 to ONE point and never writes the read ACK, while the chip reports TWO points (the Waveshare demo's own SensorLib `TouchDrvCST92xx` sets `CST92XX_MAX_FINGER_NUM 2`, reads 15 bytes from 0xD000, then writes {0xD0,0x00,0xAB}). (2) The boot flash was the init table hard-coding `0x51 0xFF` (100%) before the schedule applied; the residual white screen was the panel's uninitialized white GRAM being shown at whatever brightness the init set. (3) The display bring-up alone took ~1.4 s because the vendored init table carried two 600 ms delays (0x2B page-address-set and 0x11 sleep-out). | (1) `boost_display.c` swaps the driver's `read_data`/`get_xy` for a vendored two-point read (15-byte read + ACK write, count at byte [5], point N at offset N*5+(N?2:0)), exposing `boost_display_touch_point_count()`; a 100 ms poll timer in `boost_page.c` shows a full-screen `lv_qrcode` overlay (4 s) encoding `WIFI:T:WPA;S:<ap_ssid>;P:boost1234;;` when the count is >= 2, dismissed by any fresh tap; the 1 s hold-to-dim is suppressed while both fingers are down. The corner-hold fallback was removed. `CONFIG_LV_USE_QRCODE=y`; the SSID is read from `boost_network_get_status().ap_ssid` and the password is the shared `BOOST_AP_PASSWORD` in `boost_network.h`. (2) `boost_display_start(int)` boots the panel at 0% (`boost_display_start(0)`), the first frame renders dark, then brightness ramps to `boost_model_boot_brightness()` (dim-schedule night level) after a 100 ms settle — verified: boot logs one `brightness target=25%` request, no flash. (3) Init delays cut: 0x2B 600→0 ms and 0x11 600→120 ms (reset already provides 150 ms of settle), saving ~1.1 s of boot. | Boot brightness and the two-finger QR are hardware-verified; the faster init timing (0x11 at 120 ms) needs a visual check that the first frame is clean on glass. Do not re-add the single-point cap or re-add the corner-hold; the vendored read replaces the driver's function pointers, not `managed_components/`. Any touch change must keep the 0xD000 decode, the ACK write and the mirror_x/mirror_y applied by `esp_lcd_touch_get_data()` in agreement. |
| Dim-schedule re-apply tracks the desired level, not the minute; a manual hold-to-dim survives until the schedule truly transitions (2026-08-13, flashed) | User observed the one-second hold-to-dim reverting after roughly 30-60 s with no schedule change. The old once-a-local-minute guard (`s_last_schedule_minute`) re-applied the schedule every minute edge, so any manual override was clobbered at the next minute tick. | The minute counter conflated "the schedule's desired state is unchanged" with "a minute passed"; a manual brightness override was invisible to it, so the next heartbeat re-asserted the schedule. | `s_last_schedule_low` (-1 = unknown, 0 = high/day, 1 = low/night) replaces the minute counter in `boost_model_apply_schedule()`: it re-applies only when the schedule's own desired level transitions, or when `pending=-2` forces a re-eval after a config change. A manual hold persists until the schedule genuinely flips. | Any future dim-schedule logic must re-apply on a desired-state transition, never on a fixed cadence; a once-a-minute heartbeat re-asserts the schedule and destroys manual overrides. |
| Dyno Cell readout invalidation tightened to per-glyph ink boxes (2026-08-13, flashed + measured) | The dyno readout was five fixed-size LVGL label objects (47x58 each); `lv_label_set_text()` flushed the whole slot box on every digit change, ~2,726 px vs ~1,900 px of actual glyph ink per cell. The user asked for zero wasted pixels on readout invalidation. | LVGL labels cannot invalidate tighter than their object box, and shrinking the box breaks the fixed-cell layout (text_align CENTER re-centres in the new box). The codebase already had the answer: the vault readout and neon cells draw via a styleless container + `LV_EVENT_DRAW_MAIN` and invalidate explicit tight boxes. | The five labels became one `s_arc_readout` container (230x66, covers every cell's ink) with `draw_arc_readout()`. Each glyph's ink box is derived from `lv_font_get_glyph_dsc()` using the exact `lv_draw_label` letter_coords math (lv_draw_label.c:610-613: `x1=pen+ofs_x`, `y1=baseline-box_h-ofs_y`) with the pen centred on the slot by the glyph advance (`pen_x = slot_x - adv_w/2`, which reproduces the old 47-wide CENTER-aligned label placement bit-for-bit). Invalidation is the union of the old and new ink (+1 px AA margin) of only the changed cells; the sign's x move unions both positions; a zone-colour flip repaints every visible cell. Blank (' ') cells have zero ink and contribute nothing. Decimal cell never changes, so it now only repaints on a colour flip. | Sim dyno-cell audit 0 severe / 0 stale (517 compares) AND 4-state screenshot diff vs the pre-change build is **0 differing pixels** (byte-identical rendering); flushed px/cycle 14,677 -> 11,271 (**-23%**). Board flashed: cadence min 55 / median 62, teTimeouts 0. | Any future readout change must keep draw and invalidation sharing the same `arc_readout_ink_box()`/pen math and re-run BOTH the audit and a screenshot diff vs the prior build - the audit alone only proves self-consistency, not that the glyphs still land where the labels put them. |
| Dyno Cell readout enlarged to 60 px Archivo Black; readout + PSI/PEAK/DEMO stack moved down 20 px (2026-08-13, flashed + measured) | User asked for a slightly bigger boost readout moved down a little, keeping the gap to the PSI/PEAK/DEMO stack underneath (push it down by the same amount); the web mirror takes the same moves except it keeps its readout text size. | The 56 px readout sat at slot centre y=-4 (ink ~-36..+4) with PSI at +65 / PEAK +93 / DEMO +121. Simply enlarging the font without repitching would let adjacent digits nearly touch (56 px digit advance 37, widest box 36 -> 60 px advance 40, widest box 38). | Readout font -> `archivo_black_60.c` (lv_font_conv `--size 60`, same `32,0x2D-0x2E,0x30-0x39` range; `archivo_black_56.c` left in tree, no longer referenced). Integer pitch widened 37 -> 40 (tens -62 -> -65); fractional gap kept 33 (ones -25, decimal 8 = the 1/4-of-gap rule, tenths 41); slot 40x64 -> 44x68 so the 38 px widest glyph stays inside its own invalidation; sign offsets re-hug the digits (-53/-90 -> -55/-95). Readout moved down 20 px via shared `VALUE_READOUT_Y` 16 (was -4, used by the slot build AND the sign re-align in `update_arc`). PSI unit mark +65 -> +85 (background canvas), PEAK +93 -> +113, DEMO +121 -> +141, so the readout->PSI/PEAK/DEMO spacing is preserved. Web `drawArcGauge`: readout baseline cy-16 -> cy+4, PSI/PEAK/DEMO +20, readout font stays 56*scale (unresized per request). | Host sim dyno-cell audit 0 severe / 0 stale (517 compares, sweep crosses both thresholds incl. the sign path); screenshot measurement confirms readout ink y 216-257 (center 236 = +4, 42 px tall), PSI ink mid 318, PEAK ~346. Firmware built + flashed; board on dyno-cell/demo at 60+ fps, teTimeouts 0. | Any future readout font/size change must re-derive pitch from the generated advance (60 px: digits 32-38 box / 40 advance; decimal sits at 1/4 of the ones->decimal gap from centre) and re-run the dyno-cell audit. `archivo_black_56.c` (and its CMake entries) can be deleted next font pass. |
| Dyno Cell readout grown to 75 px Archivo Black, then settled on 65 px; zone word bumped to Montserrat 24 then back to 20 (2026-08-13, flashed) | Follow-ups to the 60 px readout row: the user asked to try 75 px on the physical display, then pulled it back to 65 px; the VAC/ATMO/BOOST zone word was made larger (Montserrat 24) then reduced again to 20. The readout keeps the stack relationship from the 60 px row (PSI/PEAK/DEMO at +85/+113/+141). | Font metrics scale nonlinearly; each size needs its own slot/pitch re-derivation from the generated glyph descriptors. | 65 px font `archivo_black_65.c` (lv_font_conv `--size 65`; digit advance ~43 px, widest box 41 px, line_height 47). Geometry: slot 47x58, integer pitch 43 (tens -70), fractional pitch 36 (ones -27, decimal 9 = 1/4 rule, tenths 45), sign gap 32 (SIGN_ONE -59 / SIGN_TWO -102). `VALUE_READOUT_Y` stays 6. Zone word `lv_font_montserrat_20` at y=-88. Web mirror: zone font 20*scale, readout baseline stays cy-6, PSI/PEAK/DEMO unchanged; assets regenerated. `archivo_black_75.c` removed from CMake but left untracked/regenerable. | Host sim audit 0 severe / 0 stale (517 compares). Sim measurement: readout bright band y 211-256 (center 233), PSI band y 312-324 (center 318) — the readout->stack gap is preserved. Firmware built + flashed; board clean boot, dyno-cell/demo cadence min 57 / median 60, teTimeouts 0. | Keep `archivo_black_60.c`/`archivo_black_65.c` and the 56/75 experiments until the next font cleanup; the live reference is 65 px. Any future size change re-derives pitch from the generated advance and re-runs the dyno-cell audit. |
| Background log ring extended from ~2 minutes to ~1 hour (2026-08-13, source + docs; not yet built/flashed) | The RAM log ring held 1,800 samples at 12.5 Hz = **2 minutes 24 seconds**, too short to record a drive or bench session for later CSV review. | The retention window was the ratio of two coupled constants: `BOOST_LOG_CAPACITY 1800` and a hard-coded "every fifth 16 ms sample" divider (`s_log_divider >= 5`). | `BOOST_LOG_INTERVAL_MS 200` (5 Hz) with a time-based gate (`uptime_ms - s_log_last_ms >= INTERVAL`) replaces the sample-count divider, and `BOOST_LOG_CAPACITY 18000` (= 3600 s x 5 Hz) gives a one-hour window. Ring grows 43,200 -> 432,000 B, still `MALLOC_CAP_SPIRAM` (external PSRAM, ~6.4 MB free), never internal DRAM. Export path unchanged (`boost_web.c` keys off the macro); CSV is ~1.1 MB generated on the fly from the ring and streamed, never persisted. `s_log_last_ms` resets in `clear_logs`. | Keep the rate and the capacity documented together (capacity / interval = 3600 s). Verify on hardware that the CSV export returns 18,000 rows after the ring wraps (strictly increasing `uptime_ms` at a 200 ms median, `badTimestampCount 0`) and that the PSRAM ring allocates without pushing anything into internal DRAM. |
| Slowing the BLE connection interval (and coex-prefer-WiFi) made the web mirror WORSE, not better (2026-08-13, flashed + measured) | User reported the web boost-gauge mirror "much more laggy" after the OBD2 BLE central went live. Research to validate the shared-radio claim and test two candidate levers: a slower BLE connection interval, and `esp_coex_preference_set(ESP_COEX_PREFER_WIFI)`. | The lag is real WiFi/BLE coexistence — the FD+ negotiates a **7.5-15 ms** connection interval (via the **L2CAP** connection-param-update path, `BLE_GAP_EVENT_L2CAP_UPDATE_REQ`, NOT the LL `CONN_UPDATE_REQ` event — so a handler on the latter never fires and NimBLE auto-accepts). The 2026-07-26 spike flagged "active connection" as its biggest untested case; this is that test. **Both candidate levers failed and were reverted.** (1) Slowing the interval (30-50 ms connect request + rejecting the FD+'s 7.5-15 ms L2CAP update): the FD+ bunches its ELM traffic into longer, less-frequent bursts, so each BLE event blocks the radio longer — measured WS frames 939→~700/15 s and HTTP p50 27→~95-115 ms. (2) `esp_coex_preference_set(ESP_COEX_PREFER_WIFI)` is **deprecated** (header says use `esp_coex_status_bit_set`) and also made WiFi worse. | No code change shipped — the baseline (20-40 ms connect request, FD+ L2CAP-updates to 7.5-15 ms, BALANCE coexistence) is the best measured state. The physical gauge is unaffected by all of it (renderFps 56-62, on the display path, not the radio). The `esp_coex` REQUIRES/`#include` and the interval constants/handlers were all reverted. | Do not re-attempt "slower BLE interval" or `esp_coex_preference_set(ESP_COEX_PREFER_WIFI)` to fix web-mirror lag: both were hardware-measured as net-negative (the slow interval makes the FD+'s bursts longer; the coex API is deprecated). The lag is the inherent cost of a chatty BLE central on the ESP32-S3's single 2.4 GHz radio; it does not touch the physical gauge and does not apply in the car (no LAN). If it ever must be revisited, the levers are (a) reducing ELM chatter (the bench `SEARCHING`/`NO DATA` spam is a worst case — a real car answers instantly), (b) `BT_CTRL_RUN_IN_FLASH_ONLY=n` which does not fit, or (c) accept it. |
| OBD freshness tracked decode-success instead of link liveness; readouts blanked every ~15 s on the bench (2026-08-12, flashed + measured) | rpm/speed/coolant went blank then `0` every ~15 s in the web UI. | `obd.valid` was driven by `s_last_ok_ms`, set only when a query *decoded* a value. On the bench (no car) only `ATRV` (battery) decodes; mode-01 PIDs and TPMS DIDs return `NO DATA`, and the FD+ spends ~1 s+ "searching" on the dead bus before answering, so the DID/PID reads (800 ms timeout) timed out, left their `NO DATA` reply as a stray that polluted the next request (the battery's `strtof` then failed), and the full rotation took ~13-15 s — right at the 15 s stale window, so `ageMs` crossed the limit and blanked the readouts once per rotation. | Track link liveness instead of decode success: `boost_obd_elm_last_reply_ms()` records when any complete ELM reply (`>` prompt) arrives, and `obd.valid`/`ageMs` use that timestamp. Raised DID/PID/battery timeouts 800 -> 2000 ms so slow `NO DATA` replies arrive cleanly instead of as strays. Verified on hardware: `valid=True` continuously across a 30 s trace (ageMs steady ~2 s), battery 12.0 V, rpm=0 on the bench. | `obd.valid` means "the ELM is answering", not "a value decoded" — `NO DATA` is a valid reply. Keep DID/PID timeouts >= the adapter's worst-case search delay so replies are never strays that corrupt the next request. The bench blanking does not reproduce in the car (PIDs answer instantly), but the liveness semantics are also what make a dropped link blank correctly. |
| BLE OBD2 central: GATT discovery + reconnect bugs fixed, link verified on hardware (2026-08-12, flashed + measured) | After the RAM fixes, the FD+ connected but the link dropped during GATT discovery (`lastError` reported 3 = HCI "Hardware Failure"/EINVAL). Serial — the only place the real fault is visible — showed the chain. | Four bugs. (1) `ble_gattc_disc_all_chrs(conn,1,0xFFFF)` walked the whole handle space; the FD+ doesn't terminate the "Read By Type" walk, so `prev_handle+1` overflowed to 0 and `ble_att_clt_tx_read_type` returned EINVAL. (2) `ble_gattc_disc_all_dscs()` starts at `start_handle+1`, so passing `rx+1` (already the CCCD handle) skipped it and made start>end → EINVAL. (3) The CCCD walk's normal EDONE completion was misread as "no CCCD" — the subscribe write had already succeeded, then the callback tore the link. (4) On reconnect after an adapter power-cycle, `init_idx` was never reset, so the ELM init (ATZ..ATSP0) was skipped and the re-powered adapter kept default ELM settings → no fresh reads (`ageMs` climbing, `valid=false`). | (1) Discover services first (`ble_gattc_disc_all_svcs`), then chars within the chosen service's bounded range (FD+ = 0x0009..0x000e). (2) Pass the RX char's VALUE handle (not `rx+1`) to `disc_all_dscs`. (3) Track `s_cccd_found`; only report "no CCCD" if the walk completed without seeing one. (4) Reset `init_idx=0` + `boost_obd_elm_reset()` on link drop so init re-runs on reconnect. Also exposed `obd.lastError` in `/state` (NimBLE status of the last failed step) and gated the battery readout on `obd.valid` (it showed a stale 12 V while disconnected). **Verified on hardware:** FD+ link up (write 0x000e / notify 0x000b), `ELM init complete`, `ATRV` returns the bench 12.0 V, link stable 74 s+ (`obd.state=3`, `valid=true`). | The serial NimBLE log is the primary GATT bring-up diagnostic; `obd.state`/`lastError` narrow it but the ATT walk's exact fault only shows on serial. On the bench (no car) mode-01 PIDs and TPMS DIDs correctly return `NO DATA` — only `ATRV` succeeds, so `obd.valid` tracks the battery read alone; a blank readout on the bench is not a code bug. Reconnect MUST re-run ELM init (power-cycled adapters lose ATE0/ATS0/etc.). |
| BLE OBD2 central: RAM collision with the display, boot-loop on failure, and the fixes (2026-08-12, flashed + measured) | Enabling the OBD2 BLE link on hardware first showed `obd.state` stuck at "Off"/"Disconnected" and never connected. Serial showed `nimble_port_init failed: ESP_ERR_NO_MEM` with `internal_free=17103 largest_block=8704`. Moving the NimBLE host pools to PSRAM (`BT_NIMBLE_MEM_ALLOC_MODE_EXTERNAL`) made it fail *further* (controller printed its MAC, then `BLE_INIT: Malloc failed` + `LoadProhibited` panic) and **boot-loop**, because `tpmsBle` is persisted ON so every reboot re-ran the failing init. | Two stacking causes. (1) The BT controller allocates its buffer pool from DMA-capable internal RAM (`MALLOC_CAP_8BIT|DMA|INTERNAL`), the same pool the display double-buffer (37,280 B) and the region-dbuf scratch strips (4×18,640=74,560 B) had already consumed — the 2026-07-26 coexistence spike predates region-dbuf and never ran BLE alongside it. (2) `esp_bt_controller_enable()` does not fail gracefully on a bad alloc; it panics (LoadProhibited), which is the same unrecoverable-boot-loop class the ledger already warns about. | (a) `CONFIG_BT_NIMBLE_MEM_ALLOC_MODE_EXTERNAL=y` (host msys/ACL pools → PSRAM), `CONFIG_ESP_WIFI_IRAM_OPT=n` + `CONFIG_ESP_WIFI_RX_IRAM_OPT=n` (Wi-Fi hot code out of DIRAM), `CONFIG_BT_CTRL_BLE_MAX_ACT=3` (scan + connect instances coexist). (b) region-dbuf scratch reduced 4→2 buffers (`BOOST_REGION_DBUF_QUEUE_DEPTH 2`) — pixel-identical, freed 37,280 B DMA-internal; transfers are functionally blocking so the four were never pipelining. (c) A `OBD_BLE_MIN_DMA_BLOCK` (40,960 B) pre-init guard in `boost_obd_ble_init()` refuses to call `nimble_port_init()` below the largest-block floor, so a RAM-starved board fails gracefully (logged, link off, mock TPMS continues) instead of panicking/boot-looping. `boost_obd_ble_start()` bails when the host never came up. Result on hardware: `heap before BLE: internal_free=75631 largest_block=63488 dma_free=67843`, `NimBLE host up`, then a 15 s-on/3 s-off scan loop. | BLE and region-dbuf now coexist, but they draw from one DMA-internal pool; any future display-path change that grows internal DMA (more scratch strips, larger draw buffers) must re-check BLE init (`heap before BLE` log, `obd.state` reaching 1/3) AND run the cadence guard together. The pre-init guard must never be lowered past the controller's real need (~26.6 kB was observed to fail; 40,960 B is the floor). Cadence re-verified after the scratch reduction: dyno-cell + demo, min 59 / median 62 FPS, framesOverBudget 0 — pass. |
| BLE OBD2 central for the TPMS page (2026-08-12, firmware implemented + built; hardware link pending) | The TPMS page only ever showed mock data. Real tire pressure needs a BLE ELM327 adapter (the user's "vLinker FS+" is actually an **FD+** — the FS family is Classic BT, which the BLE-only ESP32-S3 cannot reach) talking UDS to the Mazda MX-5 ND TPMS module (header `0x720`, DIDs `0x2A05`-`0x2A08`). AGENTS.md gated TPMS BLE behind a verified adapter profile. | No BLE central existed on main. The research doc's NimBLE-Arduino API sketch is C++, and the ESP-IDF NimBLE in 5.5 **removed `ble_gattc_subscribe`** (subscription is a CCCD write now) and changed several structs (mbuf-based notify, new `ble_gap_disc_params`, the descriptor callback carries `chr_val_handle`). main's CMakeLists also runs a component-discovery pass **before Kconfig is populated**, so a `CONFIG_`-gated `bt` REQUIRES evaluated empty in that pass and stranded the NimBLE includes. | New `main/boost_obd_ble.c/.h` (NimBLE central: scan by name `VLINK`/`OBD`/`ELM` or 16-bit service UUID, unauthenticated connect, char discovery with known-UUID preference + first-writable/first-notify fallback, CCCD-write subscription, NVS-persisted peer for fast reconnect), `main/boost_obd_elm.c/.h` (`>`-paced ELM327 request/reply, timeout, trim), `main/boost_obd.c/.h` (poll task: `ATZ`..`ATSP0` init, TPMS DID reads via `ATSH 720` + `22 2A xx` alternating with mode-01 PIDs + `ATRV`, web state). Runtime toggle `tpmsBle` (theme store, NVS, default **OFF**) wired through `/themes` + `/themes/config`; flipping it starts/stops the BLE central live. Kconfig `BOOST_TPMS_BLE_ENABLED` (default y) gates the source files; a stub keeps the API when off. `sdkconfig.defaults` gains `CONFIG_BT_ENABLED`/`BT_NIMBLE_ENABLED`/`BT_CTRL_RUN_IN_FLASH_ONLY`/`BT_CTRL_BLE_MASTER`. OBD state (rpm/speed/coolant/map/iat/throttle/maf/fuel/battery + link state + peer) published to `/state.obd` and shown on the cockpit; Settings gains the toggle + link readout. The `bt` REQUIRES is **unconditional** (contributes nothing with `BT_ENABLED=n`) because of the discovery-pass gotcha. | Both ESP-IDF builds pass (BLE on and the stub-off path), host sim builds, `mock_server.py` round-trips `tpmsBle` and fakes a live link. **Hardware still required:** bench the FD+ link (service/UUID discovery log, `ATZ`/`ATI`/`ATRV` self-tests on a 12 V bench supply) and then tune the MS-CAN UDS sequence in-car (`ATSH 720` + `22 2A xx` is the documented FORScan mechanism but the exact protocol/switch needs the real vehicle). Do not claim real TPMS until the board shows OBD link READY and four fresh DID values. The `tpmsBle` default-off runtime toggle preserves the safety gate: a fresh boot never touches the radio. |
| Boost↔overboost crossing pinned at the hardware floor; dyno-cell flip invalidation tightened (2026-08-12, flashed + measured) | The user's report: all three faces stutter at the boost↔overboost crossing. Measured on the board with `tools/bench_fast_motion.py crossings` (linear sweep, teScanline/regionDBuf ON): crossing-window `worstRenderUs` median **dyno 52 ms / tube 48 ms / segments 40 ms**, 3-5 frames over budget each. The flip repaints the ENTIRE lit run in one frame because every run pixel changes zone colour. | The ~85k-px dirty region is the rect-invalidation floor for a ~135° run (30° chunks are the measured knee; 90°/15°/6° chunks and per-segment tight boxes all land 85-106k). The run raster is the wall: the S3's masked-blend/arc-mask rate (~0.5-0.75 Mpx/s) makes a ~30k-px recolor inherently ~40 ms; opaque RGB565 copies (3.16 Mpx/s) are impossible for curved shapes (an opaque tile paints its empty bbox corners over the face). The tube's A8 wedge tiles are PARKED (`else if (0 && ...)` in `build_neon` - three bake designs failed the stale-pixel audit), so the tube uses the radial-gradient arc; segments use the A8 blits; dyno the solid rounded arc. | The dyno value-arc invalidation used 90° chunks + `rounded=true` bboxes (every box inflated by the cap reach); tightened to 30° flat bboxes with end-chunk cap pads and interior AA margin (mirrors the neon knee, `invalidate_value_arc`). Measured on board: dyno crossing worst **52 → 41.5 ms median** (renderGapMax 52.7 → 42.3 ms), framesOverBudget median 4 (min 2). Dyno sweep guard holds: min 58 / median 60, teTimeouts 0, demand coverage 1.0. Segments A8 sprites verified still in place (135 tiles, 156,312 B, blitted with recolor). | Re-verify the crossing with `tools/bench_fast_motion.py crossings` after any renderer/invalidation change. Sub-20 ms ("no frames over budget") is NOT reachable for a single-frame full-run recolor on this hardware - it requires spreading the recolor across frames (a visible transition, rejected 2026-08-10). Proposals, not shipped. |
| The sim audit's dyno-cell sweep never crossed the overboost threshold (2026-08-12) | The audit's span was 19.0 for non-neon themes, capping psi at ~6.25, so the dyno-cell flip path (the full-run recolor) was never exercised by the stale-pixel audit - the ~23k "flip cycles" it reported were just the largest fast-motion frames, not zone flips. | The span condition only raised the peak for `neon`. | `sim/main.c` now uses span 22.0 for `dyno-cell` too, so the audit crosses 8.0 and stale-pixel-validates the dyno full-run recolor (and the tightened flip invalidation). | The host audit must cross every face's zone thresholds, not just neon's. |
| TE-scanline write-ahead (2026-08-11): the wide-region flip can skip the wait even when the scan is mid-band | The `teWaitForRegion` EARLY/LATE proof treats the scan being inside `[y0,y1)` as "unsafe, must wait for the next V-blank". For the wide neon flip bands that is up to a full ~16.75 ms period. But the burst writes faster than the scan (measured 31.4-31.6 us/row incl. CASET/RASET intercepts vs the scan's ~35.95 us/row), so a write started mid-band can finish the span before the scan reaches it - which has the exact one-frame-old semantics LATE already accepts. | The write's projected position at the scan's current time (rows_before + scan_row_now) sits at/beyond the span bottom + margin, so the scan reads old data for the whole span this pass. `C = (S*ts - y0*tw)/(ts - tw)` is the collision row; integer division truncates conservatively. | A WRITE-AHEAD middle case in `te_wait_for_region_spans()`: when EARLY/LATE both fail, `rows_before == 0` (first span only, because the EARLY projection is pessimistically rounded) and the panel measures faster than the write (`ts > tw`), accept the span if the projected collision row clears the bottom + margin. No new toggle (rides `regionDBuf`). One 121.6 us/row outlier was seen right after boot during settle, so the margin is NOT unconditional - hence the pending visual tear check. | Re-verified constant-slew tube/segments sweeps on the flashed build (`teTimeouts 0`, demand coverage 1.0). The visual tear check on glass remains outstanding for the whole flip-window set (deferral + write-ahead); do not claim tear-free until the user's eyes confirm it. |
| Neon flip deferral (word-first, arc-next-frame): the flip-window worst cycle shrinks, at the cost of exactly one frame of old-colour ring (2026-08-11) | The boost↔overboost zone flip recolors the whole lit run in one frame — the widest dirty region on the tube/segments faces (measured flip-frame flush 105,041 px tube / 125,192 px segments, host audit). The word, readout and peak all flip instantly; only the run is expensive. The prior banded-sweep attempt was rejected by the user as a visible multi-frame transition, so the recolor must stay a single-frame all-at-once repaint. | Deferring the run repaint to the NEXT sample moves the full-run recolor out of the flip frame without spreading it across frames: the flip frame carries only the cheap word/readout/peak repaints, and the next frame repaints the union of both full runs in the new zone colour. One 16 ms frame of old-colour ring at each crossing is the whole visual cost — a single-frame transition, not a sweep, so it does not repeat the rejected banded trade. | `g_neon_flip_pending` + `s_neon_flip_lo/hi` (non-static global so the sim can see it): the color_flip branch stores the full-run span instead of invalidating it; the top of `update_neon` consumes the pending span before the live logic so it unions with the new sample's own delta. Word/readout/peak/bar/bulb recolors are untouched and still flip immediately. **Sim audit is deferral-aware, not weakened:** it reads `g_neon_flip_pending` after each update and exempts mismatches ONLY inside the ring band (tube r 172-231, segments 177-231) ONLY on the frame where the flip was deferred; everything outside the band and every other frame must still be byte-clean. The guard was self-tested by deliberately breaking the consume — the audit caught the stale ring across 212 frames / 620,874 px, exit 4. | Host audits: tube/segments/marquee (incl. spin-on) 0 stale / 0 severe, dyno/night-city/big-digit clean, vault at its documented baseline (5 isolated 1-step AA seams), parity + geom green. Hardware constant-slew sweeps (`tools/bench_fast_motion.py sweep`, fresh boot per arm): tube **min 54 / med 58** (baseline 45/56), segments **min 56 / med 60** (baseline 29/45), marquee spin-off 55/59 (baseline 56/59, unaffected as designed), all arms `teTimeouts 0` and demand coverage 1.0. The first two marquee arms read low (40/53, 45/53) because `neonMarqueeSpin: True` was persisted on the board — that matches the spin-on baseline; re-measure spin-off with spin forced off. A fresh visual tear check on the physical panel is still required (the deferral changes ring timing at the crossing, and the pre-existing TE-scanline write-ahead also touches it). |
| Banded flip sweep for the neon tube was built, measured, then REVERTED on the user's visual review (2026-08-10) | The tube's boost↔overboost zone flip repaints the whole lit run in one frame, measured as a ~90-103 ms flip-window worst cycle (regionDBuf + TE-wait bound, not raster bound). A banded flip sweep (spread the recolor over N frames, the draw painting the run split at a sweep edge so the byte-exact audit stays clean) cut the flip-window worst to ~52 ms (4 bands) / ~69 ms (2 bands). But on glass it read badly: a visible ~70-130 ms orange sweep up the ring at every crossing (2 bands: ~32 ms), the inner/darker halo band appearing to lag the middle band during motion, and the VACUUM↔BOOST flip at the notch racing a tiny boundary across. The user judged it "worst of both worlds" and asked to revert. | The structural flip cost (flush + TE wait of the ~108k px merged region span) cannot be removed by raster work, and any recolor spread is visibly a two-tone transition at the crossing. The 4-band sweep's boundary persisted through fast motion (the tip kept growing while the edge advanced one band per frame), and sweeping a ~1 deg run at the VAC↔BOOST notch read as a colour race. | **Reverted entirely.** The tube keeps the pre-sweep single-gradient-arc full-run recolor (the measured ~90-103 ms flip worst is the accepted stutter). The audit waveform change that made the neon audit CROSS the overboost threshold was KEPT (it now stale-pixel-validates the full-run recolor path that the old peak-at-+5 psi waveform never exercised; 0 severe / 0 stale). TEMP gradient instrumentation globals were removed with the revert. | Do not re-attempt a banded/split recolor without a concrete reason the transition will not read as a two-tone sweep; the user has already rejected that trade. The known-good state is: gradient arc + A8 segment tiles + teScanline, flip-worst ~90-103 ms. A fresh visual tear check on glass for teScanline ON remains outstanding. |
| Contract amendment (2026-08-10): organic cadence is demand-aware; constant-slew remains direct | The 2026-08-09 contract required raw median `renderFps` ≥60 on both waveforms. Quantized faces legitimately report 23-30 FPS during organic dwell windows when no visible state changed, so that criterion confused absent demand with missed work. | Firmware now publishes `gaugeDemandPerSecond`: one count for each 16 ms gauge update that introduced at least one LVGL dirty area, coalescing multiple invalidations without creating any. `tools/bench_theme_matrix.py` gates organic runs on median `min(1, renderFps / demand)` ≥95% in demanded windows and reports all-idle runs as `NO DEMAND`; legacy firmware retains the old median-60 fallback. | The constant-slew sweep remains an unchanged direct median `renderFps` ≥60 capacity gate. Historic organic measurements remain valid observations, but statements that raw organic median below 60 is itself a contract failure are superseded. Always name the waveform and demand basis when interpreting `renderFps`; never reduce demand by throttling the 16 ms gauge path. |
| Neon Segments symmetric-difference invalidation and A8 band sprites improve the tail; combined scanline candidate reaches the sweep target but organic remains below 60 (2026-08-10) | Segments repainted too much in two independent ways. Same-side/same-colour movement invalidated the angular endpoint delta, which also reflushed the whole segment containing the old endpoint even when that segment's painted state did not change. Every dirty live segment then paid three `lv_draw_arc` rasterizations (halo/body/cap), and a zone recolour could re-rasterize roughly 18 x 3 bands in one cycle. Full-size Tube/Segments readout invalidation also retained the conservative label-box Y range despite immutable glyph sprites having exact ink bounds. | Added `boost_neon_seg_diff()`, derived from the same `boost_neon_lit_span()` contract as the draw, excluding the baked zero marker and returning the minimal inclusive segment ranges whose painted state changed. Baked all 54 x 3 lit bands once through the same `lv_draw_arc` geometry into 162 colour-independent A8 coverage tiles (149,840 B PSRAM), then recolour/blit them at runtime; persistent descriptors and pixel storage outlive asynchronous draw tasks, teardown drains draw units first, and allocation failure keeps the original live-arc renderer. Tube/Segments glyph Y invalidation now uses actual immutable-sprite bounds with a clamped 1 px AA margin; fallback and marquee retain conservative boxes. | Host: geom/unit and web parity green; 25 s Tube, Segments, Marquee, and Marquee-spin audits each **517 comparisons / 0 stale / 0 severe**. Segments used zero live ring arcs, cache build ~20 ms, and host p50/p90/max recorded 0.48/1.06/4.61 -> 0.40/0.77/2.37 ms at the same 17,644 px/cycle. Controlled firmware: 2,231,184 B, SHA-256 `D0F153F70204A641B78F6E08D9D27F8AEC448B50A09B099D1E77EA6E79810ADD`; serial proved `neon segment band sprites: 162 tiles, 149840 B`, with no alloc failure, panic, stack overflow, send-colour error, or TE timeout. A8 alone, two fresh-boot 30 s constant-slew runs: **55/59 and 53/59 min/median** versus the comparable committed pre-change 28/44. Same-firmware matched scanline A/B: OFF **55/59**, ON **56/61 and 55/61**; median worst cycle 34.6 ms OFF versus 23.9/24.4 ms ON, zero TE timeouts. This meets the constant-slew median target only as the combined candidate. Organic remains below contract: 90 s ON run slow quartile **23/26**, fast quartile **29/53**; full 30 s-per-arm matrix Segments **23/30**, Dyno reference **60/62 PASS**. Do not claim completion: fresh physical-glass tear/appearance inspection is required before accepting scanline ON, and organic median >=60 remains unmet. The intermediate XOR-only arm is not reproducible and must not be used as the release baseline. |
| TE-scanline writeback implemented; Vault PEAK object shrunk | The wide-band stutter (neon segments boost→overboost flip recolours ~18 segments x 3 arc bands, measured **29/45 min/median FPS** under the constant-slew sweep) is a "second-frame tax": when the scan is inside the dirty band, `te_wait_for_region_spans()`'s fallback waits for the next V-blank - up to a full ~16.75 ms period no matter how tall the band is. The CO5300 `set_tear_scanline` (0x44) lever was stubbed (`BOOST_LCD_TE_SCANLINE`) but never actually used. Separately the Vault PEAK tell-tale's LVGL object was 34x34 although its triangle ink needs at most ~24x24, flushing ~1156 px whenever the marker moves. | Waiting for V-blank is the only safe fallback when the scan is mid-band, but its cost is the whole remaining frame, not the band's height; the scan-position estimate also assumed every edge fired at row 0, which a scanline would break. | **Dynamic scanline writeback** (runtime toggle `teScanline`, persisted, default OFF like teSync/regionDBuf; applied at boot via `main.c` and via `PUT /api/v1/themes/config`): when EARLY/LATE cannot be proved, program 0x44 to just past the region's bottom edge (`y1` exclusive + `BOOST_LCD_TE_ROW_MARGIN`) so the next TE edge arrives as soon as the scan clears the band (~0.7-4.5 ms for a ~103-row band), then burst LATE-safe (same one-frame-old-band semantics as the existing LATE skip). The scan-position estimate anchors at the programmed line (`s_te_scanline_row`, -1 = V-blank), and both fresh-window shortcuts are guarded on that anchor. Only an edge after the applicable cutoff starts the burst: unchanged targets preserve an edge racing the wait; changed targets require an edge after successful 0x44 completion so an old-line edge cannot establish the new anchor. New `teScanlineWaits` metric on `/api/v1/state`; `tools/bench_fast_motion.py sweep` gained `--te-scanline true/false`; `crossings` captures both threshold directions; `tools/mock_server.py` round-trips the field. **Vault PEAK object**: 34x34 -> `VAULT_PEAK_MARK_SIZE` 26 with the ink-extent math documented; `LV_ALIGN_CENTER` keeps mx/my fixed so the rendered pixels are byte-identical. | Host: vault audit **0 severe / 0 stale** (414 compares, 4 px = the documented isolated 1-step AA seams; flushed px/cycle mean 9879 vs 9862 pre-shrink baseline), neon geom green, sim + ESP-IDF builds clean. First hardware crossing A/B (2 events/direction; one-second telemetry windows, ~0.3-0.7 s attribution latency) showed the path active but **not a locked-60 fix**: Segments OFF 27 vs ON 34.5 median FPS (`teScanlineWaits` 0→12.5/s), Tube 47 vs 48.5 (0→19/s), zero TE timeouts throughout. Larger interleaved runs and the dyno-cell guard remain required for release evidence. A fresh **visual tear check on glass** is also still required; do not leave the toggle ON until confirmed by eye. Since both layouts remain below 60, next profile full-ring recolour and dirty-region work without visual compromise. |
| Neon: "reset to default colors" set the colours to Violet but left the preset selector where it was, so the two disagreed until the selector was cycled away and back; separately, selecting any non-Violet preset immediately reported the theme as `customized` without the user editing anything | Both `boost_theme_reset_colors()` and `boost_theme_is_customized()` compared/restored against `s_defaults[]`, which holds Violet because one palette has to be the compiled-in initial one. Neither knew about `neonPreset`. The false `customized` flag is what offers the reset, so the two bugs fed each other. | For `neon`, both now treat the SELECTED preset as the baseline: reset re-applies `apply_neon_preset()`, and `is_customized` compares against `s_neon_palettes[preset]`. | `tools/test_neon_geom.c` covers the full cycle (select a preset -> not customized; edit -> customized; reset -> back to THAT preset's colours with the preset unmoved). Verified end-to-end over HTTP for two presets. Any theme that gains a "variant" setting needs the same treatment - a table default is not the same thing as the user's current baseline. |
| The dashboard's colour picker closed by itself a second or two into typing a value or holding a slider | `renderThemes()` rebuilds the theme list with `replaceChildren()`, destroying every `<input type="color">` in it - and the picker's own edits schedule that rebuild: `input` fires, `queueThemeConfig` debounces 250 ms, the PUT resolves, and the response handler calls `renderThemes()`. Destroying a focused colour input closes its native dialog. | Defer the rebuild while a colour input is focused (`trackColorEditing`), and run the pending one when it closes. The gauge canvas still repaints from the `input` handler, so the live preview is unaffected. | Any poll- or response-driven `replaceChildren()` over a container holding focused, stateful controls (colour inputs, open selects, text fields mid-edit) will fight the user. Guard the rebuild, do not shorten the debounce. |
| Simulator screenshots were validating the wrong colour table, silently, for an entire session | `boost_theme_find()` reads `s_themes` directly and `ensure_loaded()` only memcpys `s_defaults` into it; `apply_neon_preset()` runs from `boost_theme_init()`, which `sim/main.c` never called. So every sim render showed the compiled-in palette regardless of `neonPreset`, and a preset's colours could not be checked there at all. It stayed invisible because `s_defaults`' neon entry and the Violet preset were being edited together - the moment one changed without the other, a screenshot disagreed with the device. | `sim/main.c` calls `boost_theme_init()` before option parsing and gained `--neon-preset 0..3`; `s_defaults`' neon entry is realigned with the Violet preset and carries a comment that it must mirror it. | The sim is the primary verification loop, so it has to run the same init the firmware does. When a host harness and the device disagree, suspect the harness's initialisation before the rendering code - and be suspicious of any "default" duplicated in two tables that are edited by hand. |
| Neon readout: minus sign glow read as a solid slab, decimal halo cut off square at top and sides, and cell pitch kept having to grow to stop digits clipping each other | One cause: the baked glyph sprites were OPAQUE RGB565, so every tile painted its own black margin, and at the readout's pitch neighbouring tiles always overlap. The later blit erased the earlier glyph's glow and, for the widest digit pairs, columns of its ink. Each previous fix pulled the same lever - widen the cells until the margins stop colliding - which is what made the readout too wide and forced the decimal's glow margin to zero (cropping, not removing, the blurred halo). | Store one 8-bit A8 coverage plane per glyph and blit with `recolor`; LVGL blends an untransformed A8 image as solid-colour-through-mask, so zero coverage contributes nothing and overlapping glows composite. Decimal regains a full margin; cells pack to ink, not to margins; coverage is colour-independent so the zone dimension disappears (874 KB -> 149 KB at 118 px) and ink becomes a per-blit recolor tracking the live accent. The minus mark moves into the same pipeline (`neon_bake_sign_sprite`) - it was two sheared bars whose "glow" was the same bars inflated 5 px, which at a 6 px bar height on an 8 px pitch overlapped them and flooded the 2 px gap. | Never reintroduce opaque tiles for overlapping art. `neon_sign_x_span()` must bound the sign by its BAKED footprint, not by width-plus-pad: raising the pad to the blur's reach pushed the readout's dirty rect into the ring band, costing flushed pixels every readout update and leaving an AA seam where the arc got clipped (audit caught it as 1 severe px at r=199.6). |
| Neon tube: the white zero marker looked skinny, and appeared to jump sideways when crossing from vacuum to boost | The marker is baked into the static background, but the live lit run starts exactly at `a_zero` and sweeps outward at the marker's own radius and width, so it painted over whichever half lay on the value's side. Only 2 of the baked 4 degrees ever survived, and the buried half swaps sides at the crossing. Widening the bake alone could never help. The segments layout never had this because its loop skips the zero segment and lets the bake show through; the tube run is one continuous arc with no such seam. | Redraw the marker live after the run (`NEON_TUBE_ZERO_DEG`, +-3 deg), keeping the bake so it still shows with nothing lit. Costs one arc per frame, tube only. | Any face element drawn UNDER a live sweep at the same radius and width must be repainted after it, or verified to sit outside the sweep. Measured constant 6 deg at 233-239 deg in both vacuum and boost. |
| Neon ring's two-tone gradient disappeared on the panel - three bands read as one flat colour - while the web mirror still showed distinct zones but with all three zone colours converged | Two defects sharing a root. On the panel, `neon_lit()` had been changed to clamp overflow PROPORTIONALLY (divide by 255/peak) to fix an earlier zone-convergence bug; for a saturated entry that factor is ~0.46, so the "bloomed" body came out DARKER than the raw palette drawn behind it as the halo. Measured over four palettes the band ordering was inverted in 11 of 12 zones - the gradient ran backwards, not merely low-contrast. In the mirror, `neonLitColor()` still clamped PER CHANNEL, the original convergence bug, never ported; the parity test could not catch it because its own reference implementation encoded per-channel clamping too, so mirror and test agreed with each other while both drifted from the firmware. | `NEON_HALO_DIM` 0.55 - the ring's inner band is a DIMMED zone colour, not the raw palette entry, which fixes ordering at its source and costs nothing in zone separation (worst halo/body contrast 4 -> 125). `NEON_WHITE_LIFT` 0.35 - overflow desaturates toward white instead of being clipped (hue shifts, zones converge) or scaled away (hue kept, all gain lost). Net: 0/12 inverted, worst zone separation 158. Web reference now derives from `NEON_BLOOM`/`NEON_SAT`/`NEON_WHITE_LIFT` read out of `boost_gauge.c`. | A parity test whose reference restates the behaviour under test cannot detect drift - derive it from the firmware source. `tools/test_neon_web_parity.js` now also asserts the band-ordering property directly over all ten palette colours, so a bloom change that inverts the bands fails rather than merely looking wrong. |
| Entering the neon theme took ~350 ms against 45-100 ms for every other theme | The 466x466 background canvas was repainted and all 13 glyph tiles rebaked on every scene build. The device had never reported its own build time because the only timing log was gated behind `BOOST_NEON_DRAW_STATS`, a host-sim flag - so the cost had never been split or measured on hardware. | Log unconditionally (one line per scene build, split bg vs bake: it showed bg 223 ms + bake 214 ms). Memoize both across scene switches as `s_vault_bg_buf` already did. The glyph cache key is JUST the layout, which is only possible because the tiles are A8 coverage and carry no colour - no palette edit, preset change or zone flip can invalidate them. Background keys on `neon_bg_key_t` (layout, track, zero, and where zero lands on the sweep - one `psi_to_sweep()` call rather than psiMin/psiMax/zeroAngle separately, taken from the same call the paint makes so it cannot disagree). | Verified on hardware in both directions via serial: re-entry 2 ms (both cached), preset change with a different `track` 225 ms (bg repaints, bake cached), same preset again 2 ms, layout change 439 ms (both rebuild). A cache whose invalidation is only reasoned about is not verified - exercise the paths that MUST rebuild, not only the fast path. |
| Three consecutive commits of neon web-mirror work were built and flashed with none of it live on the device; symptom presented as a firmware rendering bug (zones converged in the browser but correct on the glass) | `main/generated_web_assets.c` is regenerated by hand and is NOT part of the ESP-IDF build (AGENTS.md already required the step; it was simply not run). Compounding it, the assets are served gzipped, so grepping the raw HTTP response for a newly added token finds nothing whether the asset is current or stale - which produced a confident wrong diagnosis before the right one. | Ran `tools/embed_web.py`, reflashed, and verified by DECOMPRESSING what the device serves. | Treat "the panel and the mirror disagree" as a stale-asset hypothesis first, before a rendering one. Verify served assets by decompressing, never by grepping the raw response. See the Web assets section for the one-liner. |
| Earlier | AMOLED became half-white/half-green with `ESP_ERR_NO_MEM` and `send color data failed`. | Stock BSP placed LVGL buffers in PSRAM and the bounce-buffer path failed under partial refresh. **Corrected 2026-07-28:** this row previously read "ESP32-S3 SPI GDMA could not stream them", which overstates the mechanism. `SOC_PSRAM_DMA_CAPABLE=1` on the S3 and other GDMA peripherals on the same chip DMA from PSRAM routinely (i80 LCD, RGB LCD, UHCI, parlio, camera DVP). The real constraint is narrower: the general-purpose SPI master driver hard-codes `access_ext_mem = false` on its GDMA channel (`esp_driver_spi/src/gpspi/spi_common.c:257-263`, directly above `// TODO: add support to allow SPI transfer PSRAM buffer`), so PSRAM sources get bounce-copied per transaction. A driver configuration choice with an open upstream TODO, not a hardware incapability. | Dedicated `boost_display_start()` with internal DMA buffers, bounded strips, and the existing partial-refresh/rounder path. | Hardware 30-second soak, no serial display errors, and median physical cadence ≥60 FPS. Do not cite this row as evidence that S3 DMA-from-PSRAM is impossible. |
| Earlier | Large media writes reached approximately 172 s; a tuned SPIFFS run measured 7.37 s but remained fragile. | SPIFFS garbage collection/large-file staging was the bottleneck and was not a robust atomic media store. | Raw `media` partition with inactive-slot streaming, payload CRC, newest-valid-generation scan, and committed-header-last publication. | Complete 1,379,129-byte hardware upload in 7.504 s; verify reboot selection and preservation on abort. |
| Subsequent | Upload replacement and Delete must not race, and a canceled transfer must not destroy the old GIF. | Publication and request ordering must be serialized; an incomplete inactive payload is never a committed media slot. | Browser aborts XHR and waits for settlement before DELETE; firmware serializes operations and returns 409 for overlap; abort preserves the old slot. | Exercise cancellation, overlap rejection, and two repeated deletes on hardware. |
| Current architecture | Physical, network, browser, fallback, and sparkline rates can be mistaken for one cadence. | Different producers and renderers have different budgets. | Explicit 16 ms/~60 Hz physical path; fixed 3-client WebSocket pool with one heap-owned in-flight frame per client, 750 ms application heartbeat, and 62.5 Hz notification-driven broadcast; rAF/35 ms EMA smoothing with ordered `uptimeMs` targets; 4 Hz HTTP/sparkline paths; DPR cap 2 and GIF preview disabled. | Keep rate-specific metrics and verify physical cadence separately; the badge must identify WebSocket versus HTTP fallback. |
| Current architecture | Concurrent or stale dashboards evicted each other, causing transport churn and out-of-order target jitter. | Single-owner WebSocket server forcibly closed the old file descriptor whenever a new dashboard connected. | Fixed pool of 3 WebSocket clients; each client has one in-flight heap-owned frame, bounded 62.5 Hz broadcast, and a 750 ms browser heartbeat consumed by the server. | Three clients must remain WebSocket OPEN while a fourth uses HTTP fallback; browser rejects non-newer targets and resets smoothing timing after gaps over 1 s. |
| Current architecture | Local CSV timestamps carried a misleading timezone suffix and time behavior was unclear across reboot. | Timestamp formatting conflated local text with offset metadata; dashboard open was mistaken for synchronization. | `timestamp_local` uses `%Y-%m-%dT%H:%M:%S` without suffix; `utc_offset_minutes` stays separate. Sync Time POST supplies `Date.now()` and configured offset; firmware calls `settimeofday`, saves epoch + monotonic checkpoint/config to NVS, and restores/advances by monotonic delta when applicable. | Hardware CSV: 1,800 rows, `badTimestampCount 0`, offset `-300`; no RTC/NTP resync in this path, so only the Sync Time control synchronizes. |
| Current architecture | A fourth dashboard appeared to fail completely or churned `Disconnected` while HTTP fallback was healthy. | The three-client pool rejects only the newcomer, but browser fallback lost its 250 ms constant and reconnect attempts overwrote healthy fallback status. | Restore `POLL_FRAME_MS = 250`; keep `Live` after successful state polls; do not downgrade status merely because a retry starts. | Hold clients 1–3 open, open client 4, verify clients 1–3 remain open while client 4 polls at 4 Hz and retries every 1 s; only total transport failure may show `Disconnected`. |
| Current architecture | GIF playback ownership was unclear and could be described as a project-written decoder. | The pipeline mixes custom storage/UI/display integration with locally patched third-party LVGL and AnimatedGIF decode layers. | Document the boundary: custom dual-slot mmap and widget lifecycle; LVGL timer/wrapper; AnimatedGIF parsing/LZW/composition; zeroed full canvas and standard non-turbo path for delta/disposal correctness. | Verify `GIF_openRAM`/`GIF_playFrame`, keep mapping alive through widget destruction, test delta/disposal GIFs, and keep the internal-DMA CO5300 flush separate from decode changes. |
| Current architecture | Reflashing while a committed GIF existed caused a repeatable `main` task stack overflow before networking started. | Boot-time payload validation put a 4,096-byte CRC scratch buffer on the 3,584-byte ESP-IDF main-task stack. | Validate the committed payload through a temporary read-only `esp_partition_mmap` and CRC it directly, then unmap; no full sector lives on the stack. | Reboot with committed media present and require `HTTP API ready` with no stack overflow, panic, or reset loop. |
| Persisted Neon boot loop (2026-08-20) | The AMOLED stayed black and the board never reached networking, although serial showed `panel up`, `display ready`, and successful region-dbuf allocation. Every boot then reported `A stack overflow in task main has been detected` immediately after the Neon glyph-sprite bake log. | `app_main()` synchronously creates the persisted scene under the display lock before it returns; the ESP-IDF default main-task stack was only 3,584 bytes. The panel intentionally remains at 0% until scene creation completes, so the crash made a healthy panel look dead. | Set `CONFIG_ESP_MAIN_TASK_STACK_SIZE=8192` in `sdkconfig.defaults`; log the main-task high-water mark after scene creation; keep bake storage in PSRAM and do not weaken the boot-dark sequence. | Persist Neon, cold reboot, and require the sprite bakes, positive main-stack headroom, brightness application, network/`HTTP API ready`, and no stack overflow/reset loop. Verify generated `sdkconfig` contains 8192 and measure internal-memory headroom because the extra stack is internal DRAM. |
| Doto Neon signed-readout spacing (2026-08-20, host-verified; v0.8.1 tagged hardware acceptance 2026-08-20) | The custom three-dot minus was positioned against a leading `1`, so its zero-clearance assertion did not prove spacing beside Doto's widest adjacent digit; the negative digit block also needed to sit farther right while the sign moved left. | Doto is tabular, so use its measured 600/13-per-mille advance/bearing for every digit. Shift signed digit cells 16 px right and increase the ink-edge sign gap to 20 px, moving the sign centre 4 px left overall while preserving ring clearance. Mirror the same arithmetic in the dashboard. | Native geometry test uses `-99.9` and derives a 20 px ink-edge gap; web parity derives the same gap from drawn dots/digit position. Tube, Segments, Marquee, and Marquee-spin 25 s Doto audits each passed 517 comparisons with 0 severe and 0 stale pixels. Clean tagged v0.8.1 hardware constant-slew sweeps: Tube median 60 FPS, Segments 61, Marquee spin-off 60; each reported demand coverage 100% and `teTimeouts=0`. Dyno reference soak min 56 / median 62 FPS. | Keep draw and invalidation on the shared `boost_neon_layout_readout()` result. Test the widest adjacent digit, not a convenient `1`, and regenerate embedded web assets after any mirror change. |
| Marquee outer-ring top bulb stayed lit for several chase cycles (2026-08-20, host-reproduced) | Both grouped invalidation paths mishandled a pair crossing the circular boundary. Spin wrapped only the residue before adding `k*6`; zone-flip invalidation did not wrap `base+1` at all. At outer-ring phase base 5, both miss bulb 0 at 12 o'clock (the zone path reads index 72, outside the populated 0..71 table), so its old accent survives until another dirty region reaches it. | Wrap every complete absolute bulb index by `NEON_BULB_N(z)` in both the spin-step three-bulb union and zone-flip pair paths. | A 180 s Doto marquee-spin audit reproduced the bug at `(233,5)`, bearing -90 degrees: 507 stale comparisons / 34,983 severe pixels, 69 px worst. The same audit after both fixes is the regression gate. | Any circular grouped invalidation must carry across group and ring boundaries; modulo the absolute index, never only a residue or an unbounded `base+1`. |
| Doto readout halo removed after three-layout visual review (2026-08-20) | Doto's modular dots read cleaner without the blurred spill, while SF Alien still benefits from its established neon halo. A global glow toggle would unnecessarily alter both faces and the zone words. | At glyph/sign coverage publication, use raw core coverage for Doto and the existing `max(core, glow*gain)` for SF Alien. Keep the established 14 px aligned crop for both fonts: a zero-margin Doto crop made the marquee pre-scale publish unaligned descriptors. Zone-word glow is unchanged. | Review all three Doto layouts, run their stale-pixel audits, then flash and inspect on glass. | Keep this keyed by font, not layout or a global compile flag; sign, decimal, full-size and pre-scaled marquee sprites must all follow the same selected-font coverage. |
| Current architecture | Refreshing the cockpit could replace a healthy WebSocket badge with HTTP, while in-page settings hid cockpit controls and range changes moved the zero notch. | Shared browser bootstrap treated all controls as co-located, refresh always labeled its HTTP samples as active transport, and dial geometry used one linear range. | Cockpit and `/settings.html` share guarded bootstrap; refresh preserves an open WebSocket label; the gear navigates to settings; a fixed 236.25° zero has independently scaled vacuum and boost sides. | Host mock: cockpit and settings boot with no visible error, settings saves −12 / 15 / 11, cockpit reports `Live · HTTP 4 Hz` without WebSocket; review the mapping so `psiToAngle(0) = 236.25°` for every valid range. |
| Current architecture | Raising max PSI to 15 produced the automatic 7.5 PSI midpoint beside an 8 PSI overboost marker. | The fixed five-label set always emitted `psiMax / 2` and `psiOverboost` without checking rendered separation. | `zeroAngle` is persisted/configurable from 180–315° (default 236.25°); min, zero, overboost, and max remain mandatory, while the boost-half label is hidden when its projected label center is too close to overboost. Legacy NVS range blobs are migrated to retain user settings. | Set max 15 / overboost 8: only the 8 overboost label remains on both hardware and browser. Change zero angle and reboot: API and notch retain the selected value. |
| Theme system (multi-style faces) | A "theme" was only a palette swap over one arc face. Wanted four visually distinct, selectable, persistent gauge designs. | Rendering was hard-coded to a single arc layout; the theme carried colours only. | `boost_theme_t` gained a `style` (`arc`/`vault`/`hud`/`bigdigit`), emitted in `/themes`. `boost_gauge.c` became a scene dispatcher: `build_scene`/`destroy_scene` per style, `boost_gauge_update` dispatching to `update_*`. Theme change **rebuilds** the scene rather than recolouring. `psi_to_sweep()` projects the arc zero-referenced scaling into each face own sweep so every style honours `zeroAngle`. Web mirrors all four in `web/app.js`; `sim/` renders them headless. | Keep the `arc` face geometry and wedge invalidation byte-for-byte: it is the path the 60 FPS guard was set against. After any style change re-run the cadence guard **per style** and compare `pixelsPerSecond`, not just `renderFps`. |
| Theme picker did not reach the panel | Selecting a theme in the dashboard only took effect after a reboot. | `PUT /themes/active` persisted the id but never called `boost_gauge_apply_theme()`; only the `/config` path did. | `theme_active_put` applies the theme under `boost_display_lock`. | Switch themes from the dashboard: the panel must change immediately and survive a power cycle. |
| Stale-pixel smearing on moving elements | Trails/artifacts behind the needle and HUD fill, clearing only seconds later. | Elements were **drawn from the live sample** but **invalidated on a threshold**, so skipped frames repainted at a new position without clearing the vacated region. The needle repainted only on angle change, so an overboost colour flip at a static angle left the old colour on screen. | Every moving element draws from a committed value advanced only when it invalidates (`s_vault_needle_deg`/`s_vault_needle_over`, `s_hud_fill_deg`/`s_hud_fill_psi`). Needle invalidation padding must cover the hub **plus its border**. | Sweep through zero and through overboost both directions: no trails, no leftover colour at the hub. |
| Full-face repaints are inherently a hitch | The `bigdigit` colour sweep visibly stutters at each step. | Recolouring the whole panel is ~217k px. Measured worst render cycle for one unbanded recolour: **45 ms**. Nothing tunable removes the work. | Quantize the sweep (`BIG_STEPS`), never recolour the ground per frame, and **spread** the repaint that remains: `BIG_BANDS` full-width bands take the new colour on successive ticks. Measured worst cycle: 1 band 45.1 ms (no wipe), 2 bands 33.3 ms (selected), 4 bands 25.8 ms (visible top-to-bottom sweep). Caching does not apply here — a flat fill is already the cheapest primitive, and 24 cached grounds would want 10 MB. | A/B any change to `BIG_BANDS` on `worstRenderUs`, not `renderFps`: banding conserves total work and so barely moves FPS. The QSPI clock is not the lever — 14.5 ms of that 45 ms is the link at 60 MHz, so 80 MHz buys 8% and 40 MHz costs 16%. |
| Static face art re-rasterised every frame | Rich faces (vignette, scanlines, dense ticks) were unaffordable; the needle felt clunky and Vault fell to 37 FPS (min 4). | Every dirty region re-ran the full vector program for the static art. The ESP32-S3 has no 2D accelerator, and the bottleneck is CPU rasterisation, not the QSPI link (measured: 6% bus utilisation at 60 MHz; GIF blits sustain 3.16 Mpx/s vs the gauge's 0.9). | Paint the static face **once** into a PSRAM `lv_canvas` at scene build and blit thereafter (`paint_vault_background`). Moving parts stay separate objects above it. Vault went to median 61 / min 54 **with** vignette and scanlines added. | Keep the completed Vault canvas across theme switches as specified by the newer cache-key ledger row; other face caches are freed in `destroy_scene()`. Never put moving elements in the cache. Raising the QSPI clock is not a fix — the bus is ~6% utilised. |
| `render_fps` misread as a smoothness metric | Static-content faces reported 28-40 FPS and looked like a regression. | It counts `LV_EVENT_RENDER_READY`, i.e. render cycles actually performed, and LVGL only renders when something is invalidated. Fewer content changes means fewer renders, i.e. *less* work. | Compare `pixelsPerSecond`: `vault` sustains ~0.9 Mpx/s at 60 FPS while `bigdigit` uses ~0.48 Mpx/s at ~30. | Do not optimise a face whose throughput is well under the demonstrated ceiling; confirm perceived stutter visually first. |
| No metric for perceived choppiness | `renderFps` and `pixelsPerSecond` both looked healthy on faces that visibly lurched. | Neither captures **latency**. A face can average well and still block the pipeline for 45 ms once a second. The first attempt measured the *gap* between `RENDER_READY` events, which is worthless: an idle screen shows huge gaps and no stall. | `worstRenderUs` times `LV_EVENT_RENDER_START` → `LV_EVENT_RENDER_READY`, the duration of the cycle itself, reset per one-second window and exposed on `/state`. | Measured worst cycle: `arc` 43 ms, `vault` 18 ms, `hud` 37 ms, `bigdigit` 26 ms. `arc` is now the worst offender and still has an uncached ground. |
| OTA could not be completed remotely | `POST /ota` wrote and validated the image, set the boot partition, and returned `restartRequired: true` - with no endpoint able to restart. The only way to finish an update was to power-cycle the panel by hand, which for a car install means pulling the dash. | The feature was built as upload-only; nothing ever exercised the whole path. | `POST /api/v1/restart` fires `esp_restart()` from a 400 ms one-shot timer so the HTTP response is delivered first. `uploadOta()` now calls it and treats a dropped connection as success, because a device that reboots on cue cannot answer. | Verify OTA by checking the boot log for `Loaded app from partition at offset 0x420000` (ota_1). A device that still boots 0x20000 is running the serial-flashed image and proves nothing. |
| NVS-backed settings saved but vanished on reboot | Theme colour overrides applied instantly, persisted, read back correctly - and were gone after a restart. | `boost_theme_init()` ran before `boost_model_init()`, which is where `nvs_flash_init()` lived. `nvs_open()` on an unmounted NVS just fails, so the boot-time read was skipped silently; later writes worked because NVS was up by then. Failure is invisible until a power cycle. | `boost_theme_init()` mounts NVS itself (idempotent, with the same erase-on-corrupt handling), so it no longer depends on call order. | Never let a module's persistence depend on another module having initialised NVS. Test persistence with an actual reboot - a set/get round trip in one boot cannot catch this. |
| Allocator tuning aimed at the wrong allocator | `heap_caps_malloc_extmem_enable(64 KB)` around GIF widget creation was expected to move the decoder's ~24 KB of LZW tables into internal RAM. Internal free moved by 112 B: nothing happened. | `CONFIG_LV_USE_CLIB_MALLOC=y` is set, but `lv_conf_internal.h` reads **`CONFIG_LV_USE_STDLIB_MALLOC`**, which is never defined - so `LV_USE_STDLIB_MALLOC` falls back to `LV_STDLIB_BUILTIN` and LVGL allocates from its own pool, never `malloc`. The extmem threshold only affects `malloc`. | Allocate the `GIFIMAGE` separately inside the widget rather than embedding it in `lv_gif_t`, so its placement is under our control. | A Kconfig symbol existing is not evidence it is the one being read. Confirm placement empirically (`esp_ptr_external_ram()` plus free-heap deltas) before crediting an allocator change. |
| Internal RAM taken for speed starved the radio | Moving the 24.5 KB GIF decoder state into internal RAM boot-looped the device: `Guru Meditation LoadProhibited` with a backtrace through `wifi_softap_start` / `ieee80211_hostap_attach`. | The GIF loads at ~3 s, before SoftAP attach. Taking 24.5 KB left ~49 KB internal, and the Wi-Fi driver faulted on a failed allocation rather than failing gracefully. Because the crash precedes the HTTP server, OTA cannot recover it - the fix must go over serial. | Reverted to the pooled allocation. The `GIFIMAGE` pointer indirection was kept, so a future attempt can place only the hottest few KB. | Internal DRAM is shared with Wi-Fi and display DMA. Measure free internal RAM at *peak* Wi-Fi usage, not at the moment of allocation, and keep a hard reserve. Anything that can brick the boot path needs a serial recovery plan before it is flashed. |
| Needle judder blamed on the wrong thing, twice | The needle looks uneven - "slower, then speeds up to catch up". First suspect was the 0.35 deg invalidation gate; second was LVGL's swdraw threads sitting at priority 3, below the sample task and round-robin with the telemetry task. | Both falsified. The gate is a deadband accumulator, so position lag is bounded by the threshold itself: max 0.35 deg = **1.03 px** at the tip - and the arc face has no angular gate at all yet shows the same symptom. Raising `CONFIG_LV_DRAW_THREAD_PRIO` 3 -> 4 and dropping `boost_ws` to 2 was flashed and A/B'd: frames-over-budget per second went 3 -> 4, i.e. no change. | Added `renderGapP50Us` / `renderGapMaxUs` / `framesOverBudget` (START-to-START) to `/api/v1/state`. They show median gap a clean 16.0 ms with **2-4 gaps per second over 20 ms**, present even with zero clients connected. The cause is renders occasionally exceeding the 16 ms refresh period, so a cycle is skipped and the gap doubles to 32 ms. | Judder is a *pacing* problem and needs a *pacing* metric; `renderFps` and `worstRenderUs` both looked fine throughout. Reduce peak per-render cost on the vault face before touching schedulers again. |
| Tearing on the needle, and why TE is not a quick fix | Occasional horizontal break across the needle. | The panel *is* driving its tearing-effect line - the vendored init sends `0x35 0x00` (`boost_display.c`) - but the ESP never listens: `tear_avoid_mode = NONE`, `te_sync = TE_SYNC_DISABLED()`. The needle's dirty band is 205 of 466 rows, so the scan crosses it in ~7.3 ms while a render takes ~12.7 ms wall clock; unsynchronised, a partial write lands mid-scan essentially every frame. | Not fixed. The BSP defines no TE GPIO and nothing in the tree names one - **whether the pad is even routed needs the Waveshare schematic**. And the adapter's stock TE path waits per *flush*, which at 20-line strips means 2-3 waits per needle update (20-30 Hz) and 400 ms for a full-screen repaint: strictly worse than tearing. | If TE is ever wired, gate once per render cycle via the adapter's `custom_draw_bitmap` hook (honoured even in `TEAR_AVOID_MODE_NONE`), not per flush. Note the 0.35 deg gate is a tearing *amplifier*: fewer, larger steps make each tear more visible. |
| A settle gate that never opened | Pixel shift was meant to wait for a steady reading so its full-screen repaint lands where nothing is moving. | `PXSHIFT_SETTLE_PSI` was 0.25 psi over 1.5 s, but the signal's own flutter is `0.18 sin(17.3t) + 0.08 sin(31.1t)` - up to 0.52 psi peak-to-peak. Longest window inside +/-0.25 psi is 0.69 s, so the gate passed **0.0000%** of the time and every shift fell through to the 6-minute deadline, mid-sweep: precisely the case it existed to avoid. | Raised to 0.60 psi, above the noise floor. | Any "wait until quiet" test must be checked against the noise amplitude of the signal it watches, or it silently degrades to its own timeout. A real MAP sensor will be noisier than the simulator. |
| TE **is** routed - GPIO13 | Tearing was written off as possibly unfixable because the BSP names no tearing-effect pin and nothing in the repo referenced one. | The BSP simply does not expose it. Decoding the netlist out of the board schematic: `PIU1017 NLGPIO12 NLLCD0CS` and `PIU1018 NLGPIO13 NLLCD0TE`. The GPIO12/LCD_CS pair matches `BSP_LCD_CS` exactly, which validates the decode - so **LCD_TE is on GPIO13**, carried on the J3 display FPC, and GPIO13 carries no other net. | Not yet implemented. | Do not conclude a signal is unrouted from the BSP alone; a vendor BSP exposes what its own demo used, not what the board has. |
| Dropped frames are per-face, and the arc face proves the pacing is achievable | Judder assumed to be a global property of the display stack. | Measured with the new gap metric, zero telemetry clients, 14 s per face: **dyno-cell 0 gaps/s over 20 ms**, vault-tec 3, night-city 10, big-digit 14. The arc face holds a 16.0 ms median with a 16.6 ms maximum - textbook pacing. Drops scale with per-render cost, not with anything global. | Reduce peak per-render cost on the offending faces. | `worstRenderUs` right after a theme switch reports the scene *build* (50 ms), not steady state - discard the first samples after a PUT. |
| Alpha-composited logo art seamed at overlaps | The Vault-Tec mark's ring, hub and bars were each stroked at LV_OPA_50; wherever two overlapped the alpha composited twice and left a visibly darker seam. | Per-shape transparency composites per shape, not per figure. | Pre-blend the colour once (`lerp_rgb(face, text, 0.5)`) and draw every element at LV_OPA_COVER. One flat tone regardless of overlap, and cheaper. | Any multi-part figure that wants uniform translucency must be pre-blended, drawn into its own layer, or built from non-overlapping pieces. |
| Linear vignette ramp left visible rings even when dithered | Faint rings survived the 8x8 Bayer dither, plus a dark-light-dark band near the rim. | A linear ramp has a slope corner where it starts and where it clamps. On a face whose green sits at level 4 of 63 those corners are among the few real transitions there are, so dithering could not hide them - the panel's own radial profile showed a step at exactly r=120, the ramp start. | Smoothstep (`t*t*(3-2t)`), which has zero slope at both ends so the ramp fades in and out. | On a near-black face, curve shape matters more than dither quality. Measure the radial profile off a panel snapshot rather than judging by eye. |
| TE sync engages but does not stop the needle tearing | With teSync on, `teWaits` runs at ~57/s and `teTimeouts` at 0 - the gate is genuinely waiting on the vblank edge every render cycle - yet the tearing is unchanged. | Not polarity and not a broken toggle. The pipeline renders partial: each 20-line strip is rasterised (~4 ms) then flushed, interleaved. Waiting for vblank only syncs the FIRST strip; the scan advances ~35.8 us/line while rasterisation of later strips takes milliseconds, so the scan outruns the writes and later strips still land mid-scan. TE-at-vblank fixes the phase of the start, not of every strip. | None that is cheap. A real fix needs the whole dirty region rendered to an off-screen buffer first, then DMA'd back-to-back inside one vblank - i.e. region double-buffering, a larger change. Left as a runtime toggle (off by default) since it is harmless and marginally changes pacing. | TE sync only eliminates tearing when the transfer, not the rasterisation, is the thing racing the scan. On a CPU-rasterised partial pipeline it cannot. Confirm with `teWaits`/`teTimeouts` before assuming the control is broken. |
| Toggle unchecks itself but the effect sticks | The arc/hud gradient checkbox cleared ~250 ms after being ticked, though the gauge kept the gradient. | `queueThemeConfig`'s response handler resynced only the two big-digit booleans from the payload, then re-rendered the editor, which read the still-false `state.arcGradient`. The device had saved it; the UI mirror had not. | Resync every toggle field the endpoint can return, not a hand-picked subset. | A debounced write that re-renders from local state must fold the whole response back into that state first, or the render races the save. |
| Documented a setting that was never in effect | The repo described an "active 60 MHz QSPI trial"; performance analysis was built on that number for months. | There was no override anywhere. The clock lives in `CO5300_PANEL_IO_QSPI_CONFIG` inside a managed component, `bsp_display_new()` takes its 40 MHz default with no hook, and edits under `managed_components/` are reverted by any dependency refresh. Every measurement predating this was at 40 MHz. | Vendor the bring-up: `panel_new()` in `boost_display.c` is `bsp_display_new()` plus the 14-entry init table, with `pclk_hz = BOOST_LCD_PCLK_HZ` (80 MHz). Boot logs `panel up at N MHz QSPI` so the active value is observable, not asserted. | Never configure hardware from `managed_components/`. If a doc claims a hardware setting, there must be a line of our code to point at and a boot log line to confirm it. |
| Vendoring bring-up silently broke brightness | `bsp_display_brightness_set(90) failed: ESP_ERR_INVALID_STATE` on every boot after `panel_new()` replaced `bsp_display_new()`. | The BSP setter writes through a **file-static** `panel_handle` assigned only inside `bsp_display_new()`. Taking over panel creation leaves that static NULL forever. | `boost_display_set_brightness()` issues the same single 0x51 command through our own `s_panel_io`. | When replacing a BSP entry point, grep the BSP for file-statics it assigned; anything else in that component reading them is now broken and will only show up in the boot log. |
| QSPI clock treated as a general performance lever | Expected a faster link to lift every face. | Only full-frame pushes are link-bound. Measured 40 -> 80 MHz: `bigdigit` full-screen recolour 45.1 -> 37.6 ms (-17%), but `arc` 43.2 -> 41.7 and `hud` 36.8 -> 37.3, i.e. nothing. Partial-update faces are CPU-rasterisation-bound with dirty regions far too small for the link to matter. | Keep 80 MHz for the one operation it helps; do not cite it as a fix for partial-update cadence. | Before reaching for the clock, check whether the operation in question actually pushes a full frame. |
| Smooth gradient banded into rings on the panel | The Vault vignette showed four hard rings even after the arc approximation was replaced by an exact per-pixel radial ramp. | Not the gradient maths — the **destination format**. The face is `#02100a`, whose green is level **4 of 63** in RGB565, so darkening toward black has only four values to land on. The web mirror is smooth only because canvas is 8-bit (green 16 -> 6). | Ordered dithering: an serpentine Floyd-Steinberg-style error diffusion added before truncation in `paint_vault_background`, trading spatial noise for tonal resolution. Baked into the cache, so it never shimmers. | Before treating a banding report as a maths bug, compute the source channel's 565 level. Any smooth ramp over a near-black colour needs dithering on this panel. |
| Vignette/scanlines diverged from the web mirror | The physical Vault face looked wrong next to `drawVaultGauge`, and earlier scanline attempts tore per-region. | The vignette was nine concentric arcs (visible banding, and it started at r=165 instead of the web's r=120); the scanlines were baked *under* the art and ran edge-to-edge over the square instead of being chord-clipped to the face. | Port the web's method, not just its numbers. The vignette is a **per-pixel pass over the canvas buffer** (`lv_canvas_get_draw_buf`, RGB565 via `lv_color16_t`) after the vectors are drawn — free once, and exact. The scanlines are **not** baked: `draw_vault_crt` is the topmost child so they cross the needle and digits, with phase from **absolute screen y** so regions cannot disagree, chord-clipped per row and re-clipped to the dirty area. Cost ~1 FPS. | Any overlay that must sit above moving art has to derive its pattern from absolute screen coordinates, never from the region being drawn. |
| Widget-sized invalidation on a small change | Night City sat at 32 FPS median with the permanent glitch. | The ghost pass invalidated a fixed 310x100 box on every value change, though usually only the tenths digit moved. | Track which slots changed and bound the dirty box to those, grown by `HUD_GLITCH_DX + 1`. Sign resolution moved above the invalidation so a sign flip can widen the box. With the cached face this took the style to 42 median / 31 min. | Share the offset constant between the draw and the invalidation; a hard-coded literal in one of them silently leaves ghost pixels behind. |
| Wi-Fi dropped after a network scan | Scanning from the dashboard knocked the gauge off the LAN for seconds. | `boost_network_scan()` unconditionally re-applied the STA config afterwards; `esp_wifi_set_config()` on a live association forces a disconnect, and the follow-up reconnect was skipped because `s_sta_got_ip` was still true (the disconnect event had not fired yet). | Only change mode / re-apply config when the radio was not already in a scan-capable mode. | Scan while joined to the LAN and confirm the association is never dropped. |
| Escaped UTF-8 mangled through tooling | Arrow/hazard glyphs rendered as one missing-glyph box per byte; a NUL ended up embedded in the source. | Escape sequences were interpreted a layer early, so the source held the literal a-circumflex bytes instead of the intended codepoint. LVGL and the font were both correct. | Draw such marks as **shapes**, not glyphs. When scripting edits use raw strings and assert every replacement. | Grep for non-ASCII bytes outside comments and for NUL bytes before building. |
| Empty sensor bus reports changing phantom addresses | With both sensors and the level shifter removed, an RX/TX bus carrying only 4.7 kOhm pull-ups returned different one-off addresses on every full sweep. | The manual control at unused `0x55` measured 0/64 ACKs with both idle-low counters zero, repeated driver probes at the same address returned 64/64 `ESP_ERR_NOT_FOUND`, and the onboard CST9217 control returned 8/8 ACKs. This strongly implicates the changing-address `i2c_master_probe()` sequence but does not rule out every GPIO/peripheral or data-pattern-dependent electrical mechanism without waveform capture or an alternate implementation. | Keep device transactions at 100 kHz, expose the three boot controls in `/api/v1/sensors/scan`, preserve bus/device handles during recovery with `i2c_master_bus_reset()`, serialize reset against HTTP scans, and require four consecutive probe ACKs before reporting an address. | On hardware, 20/20 empty-bus scans must return no devices while boot controls remain manual 0/64 with idle-low counters zero, fixed-driver 0/64 successes, and onboard 8/8. This validates the scanner only; reconnect one sensor at a time and require sustained valid reads to diagnose the original lockup. |
| Direct BMP control still has no reliable ACK | A GY-BME/P280 module wired directly at 3.3 V on GPIO17/18 remained absent even though the original ADS/MAP installation had once produced real pressure-responsive readings before failing. | Six live fixed-address tests gave `0x76` only 0-4 successes per 32 probes, statistically indistinguishable from the absent `0x48` control at 0-2/32; every four-ACK sweep stayed empty and `bmpPresent` stayed false. Voltage-high readings alone do not prove continuity because both the MCU side and module have pull-ups. | `/api/v1/sensors/scan` exposes 32-attempt `fixed48`/`fixed76` counters serialized against bus reset. Treat 32/32 as address presence only; identity and sustained reads remain separate gates. | Before another firmware theory, power off and continuity-test endpoint-to-endpoint VCC, GND, SCL, and SDA; require near-zero ohms on intended conductors and no SCL/SDA short to ground. |
| Sensor bus restored; the diagnostic scaffolding was retired | Both devices came back on the **original** GPIO18/17 pins at 100 kHz: `found:["0x48","0x76"]`, `fixed48`/`fixed76` 32/32, `fault:false`. | The bus was restored by replacing the ADS1115 assembly. GPIO17/18 were never damaged, the RX/TX remap (GPIO43/44) was never needed, and the 400 kHz to 100 kHz reduction was **not** the fix. 100 kHz is retained on its own merits: a MOSFET level shifter with 4.7 kOhm pull-ups does not comfortably support 400 kHz in a vehicle. | Deleted the diagnosis-only paths: the manual `0x55` GPIO bit-bang probe, the fixed `0x48`/`0x76` counters, the onboard `0x5A` control and its BSP dependency, and the `bootDiagnostic` JSON. `/sensors/scan` is back to `{busUp,recoveries,found}`. Kept the durable fixes: in-place `i2c_master_bus_reset()`, the bus-admin mutex, four-ACK filtering, and the recoveries counter. | Do not reintroduce per-request fixed probes: the removed version fired 64 fixed probes plus a 448-probe sweep while holding the bus-admin lock. Keep the bench history in `docs/troubleshooting/i2c-sensor-bus.md`, not the README. |
| A wrong transfer function read +9.6 PSI of boost on a bench | The gauge showed `psi 9.63` sitting at atmosphere with both sensors healthy: `mapVolts 1.5735` converted to `mapAbsKpa 165.00` against `ambientKpa 98.58`. | The placeholder GM 3-bar approximation `(V - 0.6) / 0.0059` was never validated against the datasheet. It is not close: it overstates a real atmospheric reading by ~69 kPa. The sensors being *present and reading correctly* is what made it dangerous — every diagnostic looked healthy. | Two-point GM 12223861 fit at the curve's defined 5.00 V supply (0.619 V → 40 kPa, 4.818 V → 304 kPa), with ratiometric normalization for the actual supply, plus a manual one-point atmospheric offset against the BMP280. `boost_sensors_nominal_kpa()` is the only site the arithmetic lives. | `tools/test_map_conversion.py` asserts both datasheet endpoints, ratiometric normalization, and that recalibration replaces rather than accumulates. A sensor path that reads plausibly is not a sensor path that reads *correctly* — check a known pressure, and atmosphere is the one always available. |
| Presence flags outlived the sensors they described | `adsPresent` and `bmpPresent` both reported `true` throughout a total bus outage. | They record what answered once during `boost_sensors_init()`. Nothing downgraded them when every subsequent read failed, so any consumer gating on them was reading a boot-time fact as a live one. | `boost_sample_t` carries explicit freshness: `ads_age_ms`, `bmp_age_ms`, `bmp_updates`, and `ambient_is_fallback`. Timestamps are stamped **only on a successful read**, so age grows monotonically while a sensor is silent. Calibration and the Night City ATM readout gate on freshness, never on the presence flags. | Never let a boot-time probe result stand in for liveness. `UINT32_MAX` means never-read and must render as unavailable, not as a number. |
| The cadence guard cannot pass on real sensor data | `tools/check_display_cadence.py` demands a median of at least 60 FPS; a healthy board on the real sensor reports `renderFps 4` with `renderGapP50Us 495900`. | Correct behaviour, not a regression. LVGL renders only what is invalidated, and a real MAP sensor sitting at constant atmosphere invalidates nothing. The guard had only ever been run in demo mode, whose synthetic sweep changes the value every tick. | Run the cadence guard **in demo mode**, then switch back to the real sensor. The guard measures the display pipeline, which is what it was written to protect; the sample source is irrelevant to it. | Any acceptance criterion phrased in terms of `renderFps` must state the sample source. Written against real sensors it sends the next agent hunting a display regression that does not exist. |
| Every dashboard error flashed for a quarter of a second | Wi-Fi connect/scan failures and gauge-range validation messages appeared in the shared `#errorBox` and were gone before they could be read. The MAP calibration panel had already worked around it with a panel-local `#calStatus` line. | `pollState()` called `showError("")` on **every successful** `/state` sample. On HTTP fallback that is `POLL_FRAME_MS` = 250 ms, so the poll loop retracted errors it never raised. Measured on the host mock against the pre-fix `HEAD`: an identical validation error survived **223 ms**. | Every write to the box carries its source. `showError(msg, source)` / `clearError(source)` take `ERR_LIVE` (unattended telemetry: `pollState`, WebSocket frames) or `ERR_USER` (a gesture's outcome), and a producer clears only what it raised. `ERR_USER` outranks `ERR_LIVE` in both directions, so a poll can neither overwrite nor erase a message being read; `showOk()` or a click on the box dismisses it. Boot's unattended `refreshAll(ERR_LIVE)` stays retractable so a device that is dead at boot does not leave a stale banner once it returns. `updateConnection` and `POLL_FRAME_MS` are untouched. | One convention only: do not add panel-local status elements to dodge the shared box, and do not make all errors sticky. Host mock, both pages: a user error must survive tens of seconds of 4 Hz polling (measured **14.9 s** and **24.4 s**, **0** hidden samples across 106 successful polls), a `pollState`-raised error must clear on recovery (measured appear 47.3 s, clear 50.3 s, in lockstep with the badge), and the badge must read `Live · HTTP 4 Hz` throughout with **0** `Disconnected` samples across 267 samples and 8 WebSocket retry attempts. `tools/mock_server.py` carries `scanFail`/`stateFail` fault injection for exactly this. |
| Vault two-segment invalidation looked cleaner in the host audit but felt worse on the panel | The consolidated 146x34 Vault readout was kept and the needle segmentation was tested independently at 2 and 3 segments. Host RGB565 audit favored 2 segments for isolated seams (12,858 px/cycle, 0 severe / 1 total mismatch) over 3 (11,460 px/cycle, 3 severe / 8 total), but the dirty regions were larger. | A matched hardware fast-sweep run favored 3 segments: 60/60 min/median FPS, 17.162 ms median / 20.194 ms max render, 1 over-budget frame, versus 2 segments at 58/60 FPS, 18.222/33.558 ms and 9 over-budget. A later 3-segment run was noisy at 55/59 FPS, 19.564/33.623 ms and 28 over-budget, so the spread is retained rather than hidden or called a regression. | Production keeps `VAULT_NEEDLE_SEGS=3`, the hardware-proven two-triangle raster, and the bounded consolidated six-slot object. Host mismatch counts are correctness evidence, not cadence evidence; rerun both simulator stale-pixel audit and interleaved hardware tails before changing either factor. |
| Vault counterweight-tail trial | The selected three-segment, two-triangle, bounded-readout renderer still draws a 26 px wedge behind the pivot. `VAULT_NEEDLE_TAIL` now defaults to 0 for a reversible visual/performance trial; `-DVAULT_NEEDLE_TAIL=26` restores the measured baseline. | The parameter is shared by wedge geometry, large-jump fan endpoints, and segmented `r_lo`, so draw and partial-refresh invalidation cannot drift. LEN=168, HUB_R=15, all AA/hub padding, CRT, cache, peak marker, and 146x34 readout remain unchanged; the web mirror also starts at the pivot. | Treat tail=0 as a candidate, not a proven optimization. Require separate baseline/candidate RGB565 audits and interleaved hardware fast-sweep rounds, plus no visible pivot gap, residual tail, hub corruption, or trails before keeping it. |
| Docs said 20 Hz, the code had moved to 62.5 Hz | The connection badge read `Live . WebSocket 60 Hz` while the cadence contract and six other places said 20 Hz. Reading the docs first, the badge looked like it was lying about the transport rate. | The badge was right and the documentation was stale. Telemetry stopped being a free-running timer when the push loop became notification-driven: `STATE_WS_PUSH_DECIMATION 1` emits one frame per 16 ms sample, i.e. 62.5 Hz. `STATE_WS_FRAME_MS 50` survives only as the idle *fallback* timeout for a stalled producer, and reads exactly like a 20 Hz period if skimmed. Six doc sites were never updated with the code. | Corrected every rate reference in `AGENTS.md`, `README.md`, `boost_web.c` and `web/app.js` to 62.5 Hz, and named `STATE_WS_FRAME_MS` as a fallback rather than a period wherever it is cited. | The code is the authority on what the hardware does; a documented rate is a claim to verify, not evidence. Before 'fixing' any value to match a doc, read the producer - and treat a timeout passed to `ulTaskNotifyTake` as a ceiling, never a period. Same failure class as the phantom 60 MHz QSPI trial row above. |
| 82 KB of internal DRAM went to an LVGL IRAM option nobody had priced | A BLE spike ran out of internal RAM, and `main` itself was measured at only **13,611 bytes** free internal at peak with a 7,680 B largest block - far tighter than anyone had assumed. | `CONFIG_LV_ATTRIBUTE_FAST_MEM_USE_IRAM=y` costs **82,812 bytes of DIRAM**. That is 2.3x NimBLE's entire runtime cost (36,320 B) and 6x its static footprint, spent on an LVGL speed option whose benefit had never been measured against its price. It also explains the earlier GIF-decoder boot loop: the headroom to absorb 24.5 KB simply was not there. | Not yet changed on `main`. Measured with the option off: internal free goes 13,611 -> 114,023 bytes, and the cadence guard was unchanged (min 57 / median 60 against a min 58 / median 60 baseline) - but only the `arc` face was tested. | Before turning it off, run the cadence guard **per face** in demo mode and compare `worstRenderUs` and `pixelsPerSecond`, not just `renderFps`. Before adding anything to internal DRAM, measure free internal at *peak* - boot-time figures hide the problem entirely. |
| The leaked WebSocket slot, fixed | Row 149's leak: a disconnect could permanently remove a slot from the 3-client pool, so throughput fell 187.5 -> 125 -> 62.5 -> 0 f/s and later clients landed on 4 Hz HTTP fallback until reboot. | `state_ws_get()` released a slot by setting `fd = -1` only. `state_ws_send_done()` clears `inflight` under `client->fd == ctx->fd`, which can never match again once `fd` is `-1`, and allocation needs `fd < 0 && !inflight`. The `payload == ctx` guard could not be dropped either - it is what rejects a stale completion. | One `state_ws_release_locked()` clears `fd`/`payload`/`inflight` together and bumps a per-slot `gen`; `gen` is carried in the send ctx and checked **before** `fd` in the completion, and in every re-check in `state_ws_push`. The close path frees nothing: once `httpd_ws_send_data_async()` returns ESP_OK, `httpd_ws_send_cb` always runs the completion exactly once, so the completion keeps sole ownership of `ctx`/`ctx->payload` and there is no double free. Bumping `gen` is also what makes the slot reusable *immediately*, before an in-flight send completes. | The leak is **probabilistic**, not per-disconnect: it needs the CLOSE to be handled between the telemetry task marking a frame in flight and the completion running. 90 graceful reconnects and 1,200 rapid ones on the broken build leaked nothing; it only reproduces under httpd load. Measured on the broken build with 2 concurrent `/state` pollers: leaked at **96, 104 and 394** churn disconnects, pool showing `fd:-1, inflight:1`. Fixed build, identical load: **0 leaks in 1,320 + 1,200 disconnects**, and 5 consecutive 3-client disconnect/reconnect cycles at **187.7-188.0 f/s** with generations incrementing once per cycle per slot. Test against the pool's own state, not the aggregate rate - see the confound below. |
| The largest single consumer of internal DRAM was a log buffer | Row 147 measured only 13,611 bytes free internal at peak with a 7,680 B largest block. The biggest single item in that pressure was not LVGL, Wi-Fi or NimBLE. | `s_logs[BOOST_LOG_CAPACITY]` was static `.bss`: `.bss.s_logs 0xa8c0` = **43,200 bytes** of internal DRAM, larger than NimBLE's entire runtime cost and larger than the free internal RAM the firmware had. It is written at 12.5 Hz and read on demand for CSV export - no DMA, no ISR, no latency requirement. | `heap_caps_calloc(BOOST_LOG_CAPACITY, ..., MALLOC_CAP_SPIRAM)` once in `boost_model_init()`. NULL disables logging with a warning instead of failing boot; `boost_model_publish_sample()` and `boost_model_copy_logs()` are guarded, and all access stays under `s_lock`. Ring semantics, capacity, head/count and the read path are unchanged. | Measured on hardware: `.bss.s_logs` **43,200 -> 4 bytes**; internal free at peak **13,611 -> 56,727**, largest block **7,680 -> 43,008**, minimum-ever-free **9,535 -> 52,659**. CSV export **after the ring wrapped**: 1,800 rows spanning 143.9 s, strictly increasing `uptime_ms` at an 80 ms median (12.5 Hz), `badTimestampCount 0`. Cadence guard unchanged at min 57 / median 60 (demo mode, `dyno-cell`). Verify after a wrap, not before - a ring that works only until it wraps is the classic failure here. |
| The user's LAN dashboards are part of the pool under test | Every WebSocket throughput series decayed 187 -> 125 -> 62 whether the firmware was fixed or broken. | Two dashboards were open on the LAN. They hold slots indefinitely and re-race within ~1 s of a reboot, so any run that leaves a slot free for more than a few milliseconds loses it - which reads exactly like a leak in the aggregate rate. A separate artifact inflated rates the other way: httpd runs `max_open_sockets=7` with `lru_purge_enable`, so an aggressive reconnect loop evicts the very sockets being measured, and a socket left undrained buffers frames that then land inside the measurement window (a 2-client stage read 94 f/s per client instead of 62.5). | Measure the firmware's own slot state, and distinguish `fd == -1 && inflight == 1` (leak) from `fd >= 0` held by a foreign client (confound). Hold every slot continuously and roll one socket at a time; race all three at once after a restart; flush buffered frames before timing. | Never infer pool health from aggregate frames/s alone. Per-client is **62.5 Hz**; the pool total is **187.5 f/s** and each lost slot costs exactly 62.5 (measured 187.9 / 125.3 / 62.6 for 3 / 2 / 1 clients). |
| The 82 KB IRAM option buys nothing measurable | `CONFIG_LV_ATTRIBUTE_FAST_MEM_USE_IRAM=y` held **82,812 bytes** of DIRAM to keep LVGL's rasteriser in IRAM. Nobody had ever measured what that bought. | Set in the very first commit with no rationale; every later analysis priced the *cost* and assumed the benefit. | Measured on hardware, all four faces, demo mode, 3 verified WebSocket clients, three 30 s runs per face per build (six for `night-city`), each from a **fresh boot**: nothing moves outside run-to-run spread. `renderFps`, `worstRenderUs` and `pixelsPerSecond` flat on every face, including the `big-digit` full-screen recolour (56.0 ms vs 56.9 ms against a 2.1 ms spread) where it should have helped most. Only signal: `night-city` `framesOverBudget` 15 -> 16/s. Turned off in `sdkconfig.defaults`. | Two corrections to the record. (1) The BLE spike's "114,023 B with the option off" **also had both Wi-Fi IRAM options off**; this option alone gives a figure re-measured after rebase, below. (2) Its "WS frames/s 133.1 vs 200.1" is **not** memory pressure - both builds sit at the 187.4 f/s contract ceiling (62.5 Hz x 3). 133 was two live clients, not three, caused by the slot leak fixed two rows above. Withdraw the telemetry-throughput argument. |
| A leaked WebSocket slot made every back-to-back measurement non-comparable (found independently, already fixed above by the time this branch reached `main`) | First 3-client connection after boot works; every later attempt has the third client accept the HTTP 101 then close, with `W httpd_uri: httpd_uri: uri handler execution failed` on serial. Aggregate telemetry sticks at ~125 f/s instead of ~187.5. | `state_ws_get()` handles CLOSE/recv-error by setting `fd = -1` without clearing `inflight`; `state_ws_send_done()` only clears `inflight` when `client->fd == ctx->fd`, which can never match again. Slot allocation needs `fd < 0 && !inflight`, so the slot is dead until reboot. | Found and characterised during the IRAM A/B on this branch's original base (`c18339c`), before the fix above landed on `main`; every run in that A/B rebooted between measurements to sidestep it rather than fix it, so the A/B numbers are unaffected. | **Reboot between WebSocket measurements and verify how many clients are actually receiving**, or you are comparing different client counts. The pool is also shared with any dashboard open on the LAN, which reconnects within ~1 s of a reboot and races for the last slot - so verify, do not assume. Reading COM3 resets the board unless DTR/RTS are driven low *before* opening the port. |
| Kconfig symbols that do not exist are accepted in silence | `CONFIG_BT_LE_*` entries were added to `sdkconfig.defaults` during the BLE spike and had no effect whatsoever. | Those symbols do not exist on ESP32-S3. The build system accepts unknown symbols in a defaults file without warning, so the config read exactly as intended and did nothing. Separately, `CONFIG_BT_CTRL_BLE_MASTER` is not the central-role switch its name suggests - its help text is "Enable BLE connection feature", and with it off you get an unconnectable peripheral advertising `CONNECT:0`. | Verify every new Kconfig symbol appears in the generated `sdkconfig` after a build, not just in `sdkconfig.defaults`. | Same failure class as the phantom 60 MHz QSPI trial: a config line is not evidence of a config taking effect. Grep the generated `sdkconfig`, and confirm the behaviour on hardware. |
| The LVGL IRAM option landed on `main`, with a real (small) cost found on rebase | Merging `spike/lvgl-iram-benefit` needed three gaps closed against today's `main`: the RAM headline predated the PSRAM log-ring move, `big-digit`'s clean-network re-run was n=2 and LAN-contaminated, and GIF playback had never been tested with the option off. | The branch's own `96,611 B` free-at-peak figure was measured before the log ring left internal `.bss`, so it no longer described `main`. The `big-digit` gap and the GIF gap were both explicitly named as open risk in the branch's own research doc rather than glossed over. | Rebased onto `09e0369` (clean, both sides' ledger rows kept). Re-measured RAM the same way as the original A/B: minimum-ever-free **52,659 -> 135,607 B** (delta 82,948 B, matching the option's previously-isolated 82,812 B cost). Re-ran `big-digit` clean, n=6/build, interleaved across two rounds to rule out time drift: **53.7 ms vs 57.4 ms median `worstRenderUs`, ranges non-overlapping (52.6-55.4 vs 56.1-59.7)** - a real ~3.7 ms/7% cost, reported honestly, but not gating because it doesn't touch the `dyno-cell`/arc cadence guard and `big-digit` was already 3x over its render budget on both builds. Uploaded a synthetic 128,150 B animated GIF and verified upload/commit/playback/reboot-survival/delete on both builds: clean, no `ESP_ERR_NO_MEM` or `send color data failed`, and IRAM=n showed *more* internal headroom at GIF alloc time (194,055 B vs 111,111 B at the same boot stage), not less - no regression. | See `docs/research/2026-07-26-lvgl-iram-benefit.md` update section for full numbers. A "no measurable benefit" verdict from one A/B round is not the same as "no cost anywhere" - the clean re-run found a real effect the original n=3/contaminated-LAN run could not resolve. Judge a finding against the project's actual gated invariants (here, the `dyno-cell` cadence guard), not against every metric that moved. |
| Region double-buffering spike: feasible, built, real but modest cost | The row above ("TE sync engages but does not stop the needle tearing") left the fix as "region double-buffering, a larger change" with no numbers behind it. Needed a go/no-go before building: rasterise the whole dirty region off-screen, then DMA it back-to-back inside one vblank, so transfer - not rasterisation - races the scan. | GDMA still cannot stream from PSRAM (row 1), so a memcpy into internal DMA-capable memory per strip is mandatory. Measured on hardware (`spike/region-double-buffer`, before writing any feature code): per-strip DMA transfer at 80 MHz QSPI averaged **999.0 us** (200 back-to-back transfers, 18,640 B, min 997/max 999 us) against a ~0.47 ms theoretical figure; PSRAM->internal memcpy for the same block averaged **50.9 us** (~349 MB/s). For the needle's 205-row (~191 KB) band, rounded to 11 strips: 11 x (999.0 + 50.9) = **11,548.9 us** against a measured `tePeriodUs` of **16,753 us** - **31% margin**. Rasterisation alone (measured by making the flush hook skip the real write and reading `worstRenderUs` with teSync off, 30 s window) had a **13.6 ms median**, also under the period. Verdict: GO. | Built behind a new runtime toggle `regionDBuf` (persisted, default **off**, same shape as `teSync`), wired through the adapter's `custom_draw_bitmap` hook (`boost_display.c`): each strip is copied into a PSRAM staging canvas and the real transfer deferred to `LV_EVENT_RENDER_READY`, which pushes the accumulated region back-to-back after one TE wait. First version tracked a single min/max y union and, on hardware, that dragged every untouched row between disjoint dirty areas along with it (the vault needle and a digit-slot label can invalidate in the same tick at unrelated y): `pixelsPerSecond` inflated ~7.5x (437,764 -> 3,269,456 median) and the cadence guard fell to min 30/median 53-54 on `vault-tec`. Fixed by tracking up to 8 disjoint (x,y) spans per cycle instead of one union, narrowing both the row range and the column width per span. After the fix: `dyno-cell` cadence guard **unchanged**, min 57/median 60 across 3 fresh boots with the feature ON (matches the min 57/median 60 reference exactly). `vault-tec` (the target face) costs a real but modest amount: min 49/median 57 -> min 42-43/median 56 across 3 fresh boots; `worstRenderUs` median 23,056 -> ~20-21k us (no worse, sometimes better); `framesOverBudget` median 5 -> 4-5 (flat); `teWaits` continues to track `renderFps` 1:1 with `teTimeouts` 0 throughout. No `ESP_ERR_NO_MEM` or `send color data failed` on any boot, toggle, or theme switch across the whole session. | Two caveats, found during measurement/verification, not assumed away: (1) the measured write rate (999.0 us / 20 lines = 49.95 us/row) is **slower** than the panel's own measured scan rate (16,753 us / 466 rows = 35.95 us/row), so a single wait-then-blast burst only has unconditional margin over the scan when the region's top row is roughly row 86 of 466 or lower - a region starting nearer the top does not have a proven guarantee from this mechanism alone (the CO5300's `set_tear_scanline`, already stubbed as `BOOST_LCD_TE_SCANLINE`, is the next lever if that turns out to matter in practice). (2) Panel snapshots come from the framebuffer, not the glass, and cannot contain a tear by construction; nothing in this session photographed the physical panel, so "the race that caused tearing is removed by construction" is the honest claim from the measured numbers, not "tearing is visually confirmed fixed." Any reviewer relying on this feature for a real tearing complaint should watch the glass, not `/api/v1/state`. **RETRACTED, see the row immediately below: the 999.0 us / "write is slower than scan" figures in this row do not reproduce and are superseded by 575.9 us / write-is-faster-than-scan.** |
| A measurement nobody can re-run is not evidence | The README's QSPI figure was corrected **three times** and was wrong every time. Revisions 1-2 quoted arithmetic as measurement (the phantom 60 MHz clock, then 80 MHz). Revision 3 over-corrected in the opposite direction: it reported a genuinely-taken **999.0 µs per 18,640 B strip / 18.7 MB/s / 23.3 ms per frame** and concluded "the hardware does not deliver the arithmetic". That figure does not reproduce - this is the same 999.0 us figure the region-dbuf feasibility row above relied on. | The 999 µs measurement was never committed as inspectable code — only described in a commit message — so its methodology could not be replicated and the cause of the discrepancy is still unknown. A model was then built on top of it (fixed overhead ≈533 µs/transfer) which fit three independent numbers to within 0.3 ms and was **entirely spurious**, because its inputs were wrong. A good fit is not evidence when the measurement feeding it is unverified. | Re-measured with a committed harness: size sweep 932 B → 37,280 B × 3 clocks × 40 reps, completion-to-completion deltas. Link rate is **39.4 MB/s at 80 MHz (98.5% of theory)**; fixed overhead is **106 µs/transfer, clock-independent**; a full frame is **13.6 ms (≈74 FPS)**. Clock confirmed at the requested rate by `spi_device_get_actual_freq()` *and* by throughput tracking theory across 80/40/20 MHz. Reproducible at quiet boot and under full Wi-Fi+LVGL+HTTP load (575.9 vs 578.1 µs). | **Commit the harness before quoting its numbers.** The correct lesson from the earlier rows is not "measure instead of calculating" — a measurement that cannot be re-run is worse than arithmetic, because it carries unearned authority. Also: `esp_lcd` `draw_bitmap()` is *functionally blocking* here — `tx_param()` drains all in-flight transactions before its own transmit, and CASET fires every strip, so `trans_queue_depth=4` never exceeds depth 1. Do not assume transfers pipeline. |
| The panel is clocked 60% over its documented maximum | `BOOST_LCD_PCLK_HZ` is 80 MHz (`main/boost_display.c:45`). The CO5300 datasheet §6.4 p.107 specifies write-cycle `TSCYC` MIN = 20 ns — a documented ceiling of **50 MHz**. The vendor driver's own default macro is 40 MHz. | This repo overrode the vendor default without reference to the AC timing table. It has been reliable across extensive bench testing, and throughput tracks theory at 80 MHz, so the silicon evidently tolerates it. | No change made — the risk is latent, not observed, and lowering the clock would cost real full-frame time. Recorded so the decision is explicit rather than accidental. | **Do not raise the clock above 80 MHz; there is no documented headroom and none of the measured evidence supports the bus being a constraint anyway.** Note the deployment is an automotive dashboard: out-of-spec timing margins shrink at temperature extremes, and bench stability at ~22 °C does not establish stability at −20 °C or heat-soaked. Only SPI-transaction success and throughput were verified — no optical/pixel-level check has ever been done at 80 MHz vs a spec-legal clock. |
| Region-dbuf's 32 ms worst case was a missed-vblank tax, and eliminating LVGL's own strip copy is architecturally blocked | Branch `fix/region-dbuf-worst-case`, off `spike/region-double-buffer`. Two hypotheses to test: (1) can LVGL rasterise straight into the PSRAM canvas, removing the LVGL-strip→canvas memcpy ("copy 1")? (2) is the ~32 ms `worstRenderUs` tail (≈2x the 16.7 ms TE period) a missed-vblank artefact of `region_dbuf_writeback()`'s single unconditional wait? | (1) `display_manager_validate_tearing_mode()` (`managed_components/espressif__esp_lvgl_adapter/src/display/display_manager.c:1814-1864`) only accepts `tear_avoid_mode` NONE/TE_SYNC for `ESP_LV_ADAPTER_PANEL_IF_OTHER` (this QSPI panel); `DOUBLE_DIRECT`, the only path to `LV_DISPLAY_RENDER_MODE_DIRECT` (`display_manager_pick_render_mode()`, same file:1869-1881), is rejected outright — `esp_lv_adapter_register_display()` returns `NULL` (`display_manager.c:219-221`) and `boost_display_start()` fails. A hard block confirmed by reading the vendored source; no hardware needed to know it fails, and none was spent finding out. (2) `region_dbuf_writeback()` waited via `te_wait_for_vblank()`, whose only "go now" test was a fixed 2 ms freshness window designed for the OLD per-flush path (write starts at row 0, right after `RENDER_START`). Region-dbuf's burst starts wherever the dirty region's top row is, and only after ~13.6 ms of rasterisation — so the 2 ms window is stale almost every cycle, forcing a wait for the *next* edge, up to a full ~16.75 ms period on top of the raster time. | (1) Not built — genuine blocker, falls back to optimising copy 1 per the task's own instruction rather than a behind-the-adapter's-back hack (rejected for the same reason the phantom-60-MHz and `bsp_display_brightness_set` rows above were burned: editing a vendored component's behaviour without its own bookkeeping knowing about it). `te_draw_bitmap_cb` now collapses the per-row memcpy loop into one `memcpy` when the strip is full panel width (source and destination both contiguous in that case) — real but modest, not measured in isolation on hardware (the adapter block makes the original idea moot regardless). (2) `te_wait_for_region(top_row, bottom_row)` replaces the single fixed-window check with two provably-safe conditions derived from the corrected write-vs-scan numbers (write ~31.3 us/row incl. memcpy vs scan 35.95 us/row, i.e. **faster**, not slower as the retracted 999 us figure implied): skip the wait if the estimated scan position is **before** the burst's top row (write starts ahead and a faster writer never falls behind) **or already past its bottom row** (scan won't re-enter the dirty rows until its next pass, so the burst's new data lands cleanly on that next pass). The genuinely unsafe middle case — scan currently inside the dirty range — still falls back to waiting for the next edge, i.e. never worse than before. Scan position is estimated from elapsed time since the last TE edge and the panel's own measured period (`s_te_row_time_ns`), with a conservative 20-row margin. New `teSkips` counter (`/api/v1/state`) makes the skip rate directly observable rather than inferred. | **Measured on hardware** (`tools/bench_region_dbuf.py`, committed before quoting these numbers, 3 interleaved OFF/ON rounds, reboot between every run, `vault-tec`, demo mode, pixelShift controlled off to remove an unrelated confound, 14 s settle + 20 s sample per run): `teSkips`/`teWaits` **537-566 / 1016-1054 (≈52-54%)** of cycles now provably skip the wait entirely (0 by construction when `regionDBuf` is off). `worstRenderUs` median **20.4-28.3 ms ON vs 23.2-23.9 ms OFF** (mixed — lower in 2 of 3 rounds, higher in one), max **33.0-35.2 ms ON vs 30.3-33.8 ms OFF** — the worst-case gap over OFF narrowed (a first cut with only the "early" skip condition measured max 33.0-35.4 ms at a lower 41-42% skip rate) but did **not** close: cycles whose dirty region sits near the top of the panel can still land in the unsafe middle for the whole raster+wait duration, and the true worst case is not eliminated, only reduced in frequency. `teTimeouts` stayed **0** throughout every run in this session (TE hardware itself never faulted). `dyno-cell`/arc guard, 3 fresh boots each: OFF **min 57/median 60** (matches the historical reference exactly); ON **min 56 in 3 of 4 fresh-boot trials, 57 once, median 60 in all** — a small, reproducible-but-not-absolute 1 FPS dip specifically with `regionDBuf` ON that was not present in the pre-fix `spike/region-double-buffer` baseline (min 57/median 60). Root cause not isolated (would need bisecting Fix 1's copy-1 change from Fix 2's wait logic and was not done this session); flagged rather than smoothed over. No `ESP_ERR_NO_MEM` or `send color data failed` across ~15 reboots this session. |
| Fast-motion cadence isolated: real but not fixed this session, and the `dyno-cell` min-56 dip does not reproduce | Two asks, branch `spike/fast-motion-cadence` off `fix/region-dbuf-worst-case`. (1) The user visually confirmed `regionDBuf` ON removes tearing (non-negotiable, not to be traded away) but then noticed the needle *looks* low-frame-rate during fast motion — the aggregate `dyno-cell`/demo cadence guard (which mixes the demo sweep's fast and slow segments) cannot see this. (2) The row below left the `dyno-cell` min-56-in-3-of-4 dip flagged, not root-caused. | (1) Two independent isolation methods, both committed in `tools/bench_fast_motion.py` before quoting numbers: a controlled constant-slew triangle sweep (`demoFastSweep`, new transient/unpersisted toggle in `boost_sim.c`, off by default, no effect unless `demoMode` is also on) sustained at **9.789 psi/s**, the organic demo's own measured peak *trend* `|dpsi/dt|` (noise terms excluded) — not an invented faster case; and an empirical cross-check that polls the unmodified organic waveform and buckets the once-a-second `display.*` telemetry by the `|dpsi/dt|` actually observed in that same wall-clock second (smoothed over 0.35 s to reject the sim's own ~2.75/4.95 Hz flutter terms). (2) Reproduction attempt: 8 fresh-boot `dyno-cell`/demo trials on the current build (a7b01c6 + this session's unrelated `boost_sim.c` changes only — no display-path edits), 4 with `pixelShift` off and 4 with it on (matching the board's persisted default), each the standard 30 s `check_display_cadence.py` soak. | (1) **Controlled sweep**, `regionDBuf` ON vs OFF (OFF is reference-only — it tears, per the user's own confirmed observation, and is never left on): `renderFps` median 59 (min 52) vs 60 (min 58); `renderGapP50Us` median 16,900 vs 16,000 us; `worstRenderUs` median **31,684 vs 21,322 us** — regionDBuf's own mechanism costs roughly a doubled TE period on top of the OFF baseline specifically under sustained fast motion; `teSkips`/`teWaits` 395/1,105 (36%) vs 0/1,130 skip-not-possible baseline. **Organic cross-check** (pixelShift forced off — a 90 s-scale run reliably straddles the 90 s `pixelShiftSec` full-repaint otherwise, the exact confound this ledger already warns about): fastest quartile of seconds (mean 8.05 psi/s) shows `renderFps` median **41.5 (min 35)**, `framesOverBudget` median **21.5/s**, vs the slowest quartile (mean 0.75 psi/s) at median 55.0 (min 33), 6.5/s — materially worse than the controlled sweep at a similar instantaneous rate, most likely because the organic waveform's high-frequency flutter (`0.18·sin(17.3t)+0.08·sin(31.1t)`, omitted from the clean sweep on purpose) adds direction-reversal invalidation events on top of the trend motion that the clean triangle never produces. Both methods agree in direction (fast much worse than slow) but not in magnitude; reported as found, not smoothed over. Root cause, read from the code, not just inferred from the numbers: `te_wait_for_region()`'s early/late skip test uses the **union** of `top_row`/`bottom_row` across every span in the cycle (`region_dbuf_writeback()`'s loop just before calling it), not each span's own range. The vault needle and the six digit-slot labels sit far apart on screen and both invalidate on almost every tick once psi is moving at all (the needle's own 0.35° gate is crossed within one 16 ms tick at any of the organic waveform's observed speeds), so during fast motion the combined row range is wide on nearly every cycle — which is exactly when the early/late proof is least likely to hold, forcing a real wait. A wait landing after the ~13.6 ms raster floor has already elapsed pushes the cycle to roughly a second TE period (~33.5 ms), which reads as a stutter rather than a rate drop, matching the user's report. **Not fixed**: the fix (score the proof against actual per-span transfer time, `Σ span_height_i × row_time`, instead of the naive `bottom_row − top_row` union — provably *at least* as safe, since it only makes the model of how fast the write finishes more accurate, never assumes it finishes faster than it will) touches the exact safety proof the user's own eyes verified tear-free, and re-verifying that after a change needs a fresh visual check this session had no way to obtain. Also investigated and not shipped for the same reason: the RAMWRC (`0x3C`) per-chunk command reduction named in this task's own brief — real (~70 µs/chunk, ~3.5% of the 16.75 ms budget across a typical ~8-chunk cycle) but requires bypassing the vendor CO5300 driver's own `esp_lcd_panel_draw_bitmap()` with hand-rolled `s_panel_io` transactions, and a wrong coordinate/opcode there would show up as on-glass pixel corruption that the framebuffer-based debug snapshot **cannot** catch (it never touches the wire path being changed) — same "needs the user's eyes, not a snapshot" gate as (1) above, and smaller expected payoff than the wait-conservatism fix regardless. (2) **`dyno-cell` min-56 dip: did not reproduce.** All 8 trials read **min 57-58, median 60-61** — at or above the historical min 57/median 60 reference, both with `pixelShift` on and off. The leading confound hypothesis (`pixelShift`'s 90 s full-repaint landing inside the measurement window) is ruled out directly: uptime at guard-start was consistently ~4.7 s and at guard-end ~40.6 s across all trials, so the 30 s window never reaches the 90 s `pixelShiftSec` boundary regardless of pixelShift state. Conclusion: the original min-56-in-3-of-4 result was itself reported as "not absolute" (57 once), and 8 further trials finding zero repeats of it is stronger evidence for **sampling noise in a minimum-of-~25-buckets statistic** (a single unlucky one-second bucket is enough to move a minimum by 1, and this session could not force one back into existence) than for a systematic regression. Judged acceptable; not fixed, because there was nothing reproducible to fix. | Both isolation methods and the reproduction attempt are hardware-measured and committed (`tools/bench_fast_motion.py`); re-run them rather than trusting these numbers. The two identified next levers (per-span TE-wait timing; RAMWRC) are real candidates for a future session **that has the user's eyes on the physical panel available**, not for one that does not — this session declined to ship either rather than claim a display-path fix it could not verify. `regionDBuf` was left ON, matching the non-negotiable tearing fix; nothing in this session traded cadence for it. Board restored to `vault-tec`/demo/teSync/regionDBuf/pixelShift all ON, `demoFastSweep` OFF, matching the state found at session start. |
| The per-span TE-wait fix shipped and flashed for the user to verify by eye, but does not move the fast-motion numbers | Coordinator asked for the previously-identified per-span fix (row above) to actually be built and put in front of the user at the bench, since "needs the user's eyes" is resolved by giving them a build to look at, not by declining to ship anything. Branch `spike/fast-motion-cadence`. RAMWRC explicitly excluded from this round (kept to one variable). | `te_wait_for_region_spans()` replaces `te_wait_for_region()`: same early/late proof, scored per span (using each span's own y0/y1) instead of once against the whole cycle's `[top_row, bottom_row]` union - see the block comment on the function for the full argument, including where it is and is not a strict superset of the old union proof. First cut converted an earlier span's row count directly 1:1 into "scan rows" for the EARLY projection - equivalent to assuming the WRITE moves at the SCAN's slower ~35.95 µs/row rate instead of its own measured ~31.3 µs/row. Hardware A/B caught this immediately: fast-sweep `renderFps` median fell from 59 (old union) to 54-57 across repeated runs of the first cut, and `teSkips` went DOWN (368 vs 395), the opposite of what the fix was supposed to do - an ordinary tall single span (the vault needle near vertical is ~150-200 rows) alone was enough to inflate the projected scan position past what the union check needed. Fixed by introducing `BOOST_REGION_DBUF_WRITE_ROW_TIME_NS` (32 µs/row, rounded up from the measured ~31.3 µs/row) for the elapsed-time estimate, converted to scan-row units for the actual comparison; both the row-count and chunk-overhead terms now round UP (ceiling division), since under-estimating elapsed time is the unsafe direction for an EARLY proof. | **Corrected fix vs. the union baseline, interleaved hardware A/B** (rebuild + reflash between every arm - PowerShell `idf.py -p COM3 build flash` directly, not wrapped through Bash's `powershell.exe`, which corrupts the IDF Python-environment detection and fails the build outright; `tools/bench_fast_motion.py sweep`, 3 rounds, `demoFastSweep` at 9.789 psi/s, pixelShift controlled off): union **59/59/55** vs per-span **59/59/55** median `renderFps` per round (paired, essentially identical run-for-run - the fast-sweep's own fixed 4.92 s period aligning differently with a fixed-delay sample window each reboot is itself a real source of ±4-5 FPS median swing between *identical* builds, confirmed by measuring the union build against itself twice), `worstRenderUs` median 30,979/32,387/29,408 vs 29,340/31,635/30,217 (paired, no consistent direction). Averaged `teSkips` across the 3 rounds: union 360, per-span 381 (**+5.8%**) - a real, if modest, increase in the mechanism doing what it was built to do. `framesOverBudget` summed: union 153, per-span 148 (**-3%**). **Organic cross-check, fastest quartile**: `renderFps` median 42.0 (min 30) vs the pre-fix baseline's 41.5 (min 35), `framesOverBudget` median 19.0 vs 21.5 - again no clear win outside noise. `dyno-cell`/arc guard unaffected: 3 fresh boots, min 56-58/median 60, matching the noise band already characterised in the row above (not a new regression). No `ESP_ERR_NO_MEM`, `send color data failed`, or `teTimeouts` across the whole session. **Conclusion, reported as found rather than chased further**: the per-span fix is a real, verified, hardware-measured improvement to the underlying skip-rate mechanism, and is not a regression (unlike its first cut) - but it does not deliver a measurable improvement in the fast-motion cadence numbers that motivated it, in either isolation method. The likely reason: both the controlled sweep (a full-range triangle, which spends much of its time with the needle alone spanning a large single tall region) and typical organic fast motion are apparently dominated by single-span or adjacent-span cycles, where this fix is mathematically identical to the union version it replaces (`rows_before` is 0 for the first span); the specific "needle and a far-away digit label both invalidate at once, with a wide gap between them" scenario this fix targets is real (it is what `region_span_add`'s own disjoint-span tracking exists for) but is not, on this evidence, the dominant cost of fast-motion stutter. The binding constraint identified in the row above - rasterisation at ~13.6 ms against a 16.75 ms budget, worsened by whatever *does* force a real per-cycle wait - stands. | Flashed and left running on `vault-tec`/demo/teSync/regionDBuf/pixelShift all ON, `demoFastSweep` OFF (transient, does not survive reboot even if left on - confirmed off here regardless). **What needs the user's eyes now, framed as two separate questions**: (a) is the panel still tear-free with this build, exactly as it was before - this change touches the same safety proof the earlier tear-free confirmation was made against, so that confirmation should be treated as needing a fresh look, not assumed to still hold; (b) does fast motion look smoother than before, or unchanged - the telemetry here says "unchanged, and safely so," and if the user's eyes agree, that is the honest answer to report, not evidence to explain away. The Settings UI `regionDBuf` checkbox (`web/settings.html`/`web/app.js`, already on this branch via `6c99426`) lets them toggle it live to compare against OFF, keeping in mind OFF is known to tear and is for A/B contrast only, not a state to leave the board in. |
| Vault needle raster cost, not TE wait, was the dominant fast-motion bottleneck | The corrected per-span TE proof changed skip statistics but not cadence. Temporary phase telemetry then isolated `RENDER_START`→`RENDER_READY`: baseline raster p50 was 9.12/9.43 ms; suppressing only the needle draw while preserving its invalidation/transfer geometry reduced it to 5.58/6.18 ms and reached 60 FPS. Component arms showed the tapered wedge was primary (hub-only arm 6.84 ms/60 FPS) and the hub secondary (wedge-only arm 8.07 ms/59 FPS). Source inspection found `draw_vault_needle()` submitted three opaque triangles although the first two already tile the convex A-B-C-D trapezoid; the third A-B-D triangle added no geometry but still paid LVGL's mask/raster/blend path. | Removed only the redundant third triangle. Same-firmware interleaved runtime A/B, identical firmware and dirty geometry: two triangles median FPS **60/59**, raster p50 **8.25/9.58 ms**, over-budget totals **7/17**; legacy three triangles **56/55**, **9.50/10.84 ms**, **104/116**. Temporary profiling modes/metrics were removed before ship after review found they added API/memory/reproducibility surface. Final production build: controlled sweep min/median **58/60**, `worstRenderUs` median **17,949 us**, 8 over-budget frames; organic fastest quartile median **55 FPS**, 6 over-budget vs historical 41.5/21.5, with a single min-21/max-118.9 ms outlier retained rather than hidden. A fixed-hundredths-0 arm cut pixels/s about 10% but did not improve cadence, since tenths still changes every fast frame; not shipped. | Preserve the exact two-triangle split and tight three-segment invalidation. Do not reintroduce overlap "to hide a seam" without same-firmware A/B: static RGB565 snapshot and image inspection found no seam, pinhole, gap, malformed tip/base, or hub corruption. Direct RGB565 writes from `LV_EVENT_DRAW_MAIN` are prohibited: two async LVGL software draw units can race callback writes; any future fast raster path belongs inside draw-unit task execution. Final flashed state: `vault-tec`, demo/TE/regionDBuf on, fast sweep off; serial showed no stack overflow, Guru Meditation, `ESP_ERR_NO_MEM`, send-color failures, or TE timeouts. |
| `dyno-cell` was the last face still re-rasterising its static art every frame | Row 126 already showed `dyno-cell` at 0 dropped-frame gaps/s (best-paced face) yet row 117/599 still named `arc` the worst `worstRenderUs` offender once vault/hud were cached - its unfilled 270deg track, zero notch and five scale numerals were live `lv_arc`/`lv_line`/`lv_label` objects, so any wedge-invalidated rectangle that overlapped their bounding boxes forced a full re-stroke of the ring. | Same class of bug as the vault/hud row above: static furniture was drawn from vector primitives inside the live invalidation path instead of once. | `paint_arc_background()` bakes the ring, zero notch, numerals and the never-changing "PSI" mark into a PSRAM `lv_canvas` at scene build, reproducing each live object's exact `lv_draw_arc`/`lv_draw_line`/`lv_draw_label` call (same radii, same `lv_text_get_size` measurement) so the wedge invalidation and arc geometry are byte-for-byte unchanged. `boost_gauge_apply_config()` dropped arc's incremental `refresh_zero_notch()`/`refresh_tick_labels()` fast path (those objects no longer exist) and now takes the same `destroy_scene()`/`build_scene()` rebuild vault/hud/bigdigit already used, which is what repaints the cache when range/zero-angle change. A failed PSRAM allocation warns and skips the cached art, matching vault's degrade path rather than adding a second convention. | Host audit (`--theme dyno-cell --seconds 25`) unchanged before/after: flushed px/cycle mean 10519 max 36488, 0 severe mismatches - confirms geometry/invalidation untouched. Hardware, demo mode, 3 fresh boots, 30 s `/api/v1/state` polling windows: `worstRenderUs` max 58.4-63.7k / mean ~24-25k us before -> max 43.8-51.3k / mean ~22.7-23.1k us after; cadence guard min 56-57 -> 58-59, median 60 unchanged both sides. Runtime range change (`PUT /api/v1/config`) verified live via `/api/v1/debug/snapshot`: numerals and zero notch position updated with no reboot. One caveat: `lv_draw_label` queues tasks and only rasterises them in `lv_canvas_finish_layer()`, so a loop-local text buffer needs `dsc.text_local = 1` (copy) rather than a raw pointer - the first attempt silently rendered no numerals at all because the stack buffers were long reused by the time the canvas dispatched. |
| Dyno Cell zero notch disappeared behind the moving value arc | The arc background-cache change above baked the zero notch into the background canvas, then created the live value arc above that canvas. The geometry remained correct, but the object order inverted the original visual contract whenever the colored wedge reached zero. | Caching changed draw order even though it preserved coordinates. | Keep the expensive track and labels cached, but restore the tiny zero notch as a live `lv_line` created after `s_arc_value_canvas`. | On glass and in a debug snapshot, the zero notch must remain fully visible over both vacuum and boost wedges; rerun the Dyno Cell cadence guard because the live overlay intersects the moving arc. |
| Night City showed only a moving arc blob when selected during vacuum | Scene rebuild could render before the first HUD sample. That sample committed its negative endpoint without invalidating the complete zero-to-value span, so subsequent endpoint-only invalidations clipped the full arc draw until a zero crossing forced both spans dirty. | On the first HUD sample, invalidate the complete zero-to-current span after committing the fill state. Angle mapping was already correct. | Host audit switched from an already-negative reading, pumped the rebuild before the first HUD sample, and reported 104 comparisons / 0 stale pixels. Keep that ordering in the audit. |
| Night City gradient fill is measurably slower, but is not the whole 40 FPS bottleneck | The user observed that Night City did not look like 60 FPS, especially with gradient fill enabled. A reproducible three-round fresh-boot hardware A/B (`night-city`, demo mode, pixel shift off, 10 s settle + 20 s sample per arm) measured gradient OFF at min/median **30/40 FPS** in every round and ON at **29/39, 29/39, 29/38**. Across-round medians: `worstRenderUs` **31.8 vs 32.0 ms**, `framesOverBudget` **11 vs 13/s**, `pixelsPerSecond` **0.688 vs 0.735 Mpx/s**. No TE timeouts. | `update_hud()` detects changes between 24 RGB565-quantized endpoint colours. At each crossing it correctly invalidates both complete old and new zero-to-value spans because `draw_hud_fill()` paints the entire fill one solid endpoint-derived colour. That adds work, but gradient OFF still reaches only 40 FPS, so disabling it cannot solve the larger Night City cost. | Added `tools/bench_hud_gradient.py`, which reboots each arm, asserts Night City/demo/gradient state, controls pixel shift off, records pacing/work metrics, and restores the initial board configuration. No renderer change yet: fewer steps trade cadence for more visible colour jumps, while a true fixed spatial gradient changes the visual semantics and needs its own stale-pixel-safe design and hardware A/B. | Do not describe `hudGradient` as a free or per-pixel gradient: it is a quantized whole-fill recolour. Optimize against `worstRenderUs`, `framesOverBudget`, and `pixelsPerSecond`, not FPS alone; preserve the first-sample full-span invalidation and committed draw/invalidate state. |
| Night City's chromatic ghost alpha blends were the largest isolated live-render cost | Compile-time diagnostic arms suppressed one operation while preserving update state and invalidation geometry. Gradient-on baseline was **39 FPS / 30.6 ms** median `worstRenderUs`; no ghost **45 / 19.1**, no primary digits **44.5 / 28.8**, no fill arc **43 / 27.6**, no cached background **41 / 28.0**, and all four suppressed **46 / 16.7**. The individual deltas are not additive because two draw units, clipping and TE waits interact, but the ghost result is unambiguous. | `draw_hud_glitch()` submitted two 96 px labels at `LV_OPA_70`. Their shifted edges sit mostly over the static face, so software alpha blending paid destination reads and per-pixel blends twice. | Pre-blend each ghost colour against `theme->face` with `lv_color_mix(..., LV_OPA_70)` and submit both labels at `LV_OPA_COVER`; offsets, font, text, draw order and dirty bounds are unchanged. This is deliberately an approximation, not framebuffer-identical where the ghosts overlap each other or other art. Removed the temporary profiling masks before shipping. Production hardware after the change: gradient ON min/median **27/44 FPS**, OFF **32/46**, no TE timeouts; the low gradient-on min came from one retained outlier rather than being hidden. | The approximation assumes the face is the dominant backdrop. If future art or another live object is placed behind those shifted glyph edges, reassess on glass or pre-render the complete intended stack. The face still misses 60 FPS; next wins are more invasive glyph/arc caching, not another scheduler or QSPI tweak. |
| Tenths cache was incomplete and its lifecycle was unsafe | `lv_font_get_glyph_bitmap()` returns an `lv_draw_buf_t *`, not raw pixels, and mutable PSRAM-backed A8 sources could be retained by asynchronous draw units after publication or teardown. | Completed one immutable **34,786 B** PSRAM readout cache for digits 0-9, decimal, minus, all main labels, and the ghost pass. Stable descriptors are published once; `lv_draw_wait_for_finish()` drains draw units before scene/cache teardown. Allocation failure keeps the source-font fallback. | Simulator Night City audit: **517 comparisons / 0 mismatches**. Hardware: 60 rapid four-theme cycles plus a 60 s Night City soak, no freeze, panic, `ESP_ERR_NO_MEM`, send-color error, or TE timeout. Full-cache hardware benchmark: 3 interleaved rounds, 6 arms, 336 samples; gradient-off aggregate median **42.0 FPS**, `worstRenderUs` **19,378.25 us**, `pixelsPerSecond` **741,639**, zero TE timeouts. Prior tenths-only data was one round (2 arms, 112 samples): **40.75 FPS**, **28,440 us**, **728,238 pixels/s**. This is directional only, not a matched causal A/B. | Cache storage must remain immutable and alive through all callbacks; drain draw units before deleting scene objects or freeing it. Do not use mutable per-frame `lv_image_set_src()` publication. |
| Web mirrors drifted from the completed renderer contract | Night City's chromatic split had become visually negligible at **0.4 alpha / 3 px**. Big Digit ignored `bigDigitStaticBg`, `staticColor`, `colorText`, and `textColor`. | Mirror Night City at **0.7 alpha / 6 px** and make Big Digit consume all four settings. | Host and physical readout verification remained clean; the full-cache hardware result above is the relevant 3-round evidence, while the prior tenths-only comparison is explicitly one round. | Keep web and firmware renderer settings named and behaviorally covered; do not reduce the chromatic split below its visible 0.7/6 px contract or drop any Big Digit setting from the renderer. |
| Night City could not turn unused AMOLED pixels fully off, and its arc looked too light | The face colour was structurally fixed at `#080A08`, and the HUD track/fill width was 10 px in both renderers. | Add persisted `hudTrueBlack` to the themes API and Night City colour menu; use it for the screen, cached face, ghost pre-blend, and web mirror. Increase only the HUD track/fill to **15 px (1.5x)** and use the same width for invalidation. | Host Night City audit: 517 comparisons / 0 stale mismatches. Firmware built/flashed on COM3; true-black PUT survived restart. Browser mirror/control verified live. Dyno Cell hardware cadence guard remained min 58 / median 61 over 103 samples; Night City reported 44 FPS / 20,191 us worst render with zero TE timeouts after restart. | Keep the default dark face available when unchecked. Any later width change must update static track, live fill, physical dirty bounds, and web mirror together. |
| Night City's immutable readout cache appeared to save little, and its smaller-looking arc still ran slower than Dyno Cell | The source 96 px font is already uncompressed 4-bpp data, so expanding 12 glyphs into A8 PSRAM removes lookup/format work but not the dominant three-pass coverage raster, dirty-box reconstruction, or clipped PSRAM background blit. LVGL charges clipped rectangle area rather than lit-pixel count; Night City also has two ghost passes and a larger 96 px readout, while Dyno Cell has one smaller readout and narrow endpoint work. | Validate every cached descriptor/bound and retain `BOOST_HUD_READOUT_CACHE=0` for matched source-font A/B. Consolidate ghosts/sign/slots into one styleless draw callback with changed-slot invalidation and outer-ring clip rejection. Animate only committed arc geometry through a non-overshooting 40 ms latest-target linear interpolator; raw values still drive numbers, model/API, peaks, colours, and thresholds. | Host 30 s audits: Night City 620/0 stale and 7,297 px/cycle versus 11,254 before; Dyno 620/0. COM3 three-round Night City: gradient-off worstRenderUs 17.06-17.12 ms and 0.47-0.50 Mpx/s versus baseline 18.94-19.08 ms and 0.75-0.78 Mpx/s; median renderFps still 41-42. Dyno guard min 58/median 61 over 103 samples. Region-DBUF-off and TE-off trials did not close the remaining budget; reject the RGB565 tile prototype because host work rose to 21,175 px/cycle. | Do not describe `renderFps` as panel refresh. Optimize `worstRenderUs`, render gaps, over-budget frames, and pixels/s together. Never animate the authoritative numeric/model value or delay overboost colour. Keep draw and invalidation on the same committed visual geometry. |
| Final TPMS/Vault/gradient follow-up | The final branch needed one persisted Vault geometry option, tighter gradient invalidation, and a physical hold that matched the intended feel without weakening the 16 ms gauge path. | Compile-time geometry and repeated same-side full-span invalidation made retained trials hard to reason about; browser Big Digit also used continuous colors while firmware used buckets. | `vaultNeedleTail` defaults off and is persisted through the theme store/API/web editor; draw and all Vault invalidation paths share its 0/26 px runtime extent. Arc/HUD recolor same-side unions once, Big Digit/web share the 24-positive-bucket ramp, and RGB565-equal custom-palette buckets skip needless setters. Hold-to-dim is one second and commits brightness only after a successful panel command. The final 25 s Vault audit measured 10,786 mean px/cycle, zero severe mismatches, and six isolated one-step AA seams over 517 comparisons; simulator and ESP-IDF builds passed and COM3 flashed successfully. | Geometry, invalidation, API persistence, browser parity, and generated assets are one change. Document isolated RGB565 AA seams separately from broad stale trails; never call a strict nonzero audit exit a severe rendering failure when `severe mismatches` is zero. |
| Night City's ring left unused space at the panel edge | The 15 px arc remained at radius 206 and its 16 px ticks ended at radius 214, leaving roughly 17 px beyond their stroke. | Move track/fill radius to 225 and translate unchanged ticks from 198-214 to 217-233; move the zero notch and update physical invalidation plus the web mirror in lockstep. | Host audit: 517 comparisons / 0 stale mismatches. Hardware, one 60 s arm each: gradient off min/median 30/41 FPS, `worstRenderUs` median 19,187.5 us, 0 TE timeouts; gradient on 29/39, 19,889.5 us, 0 timeouts. Dyno Cell gate min 58 / median 60 over 104 samples. | Outer tick strokes deliberately clip at the circular panel boundary. Keep tick length 16 px and all track/fill/invalidation/mirror radii synchronized. |
| Vault-Tec took roughly a second longer than other themes to select | Every scene switch freed its 434 KB static canvas. Returning to Vault synchronously repeated the serial 217k-pixel error-diffusion vignette, including one `sqrtf` and dependent three-channel diffusion per pixel; both swipe and web selection block in the same scene rebuild. | Retain the completed Vault canvas across theme switches and repaint it only when its static-art cache key changes (range, zero angle, palette, face, or vignette). | Hardware web PUT timing after flash: first Vault build 1077 ms; cached returns 64, 101 and 101 ms (other intervening themes 69-170 ms). Host Vault audit: 62 comparisons / 0 stale pixels. Dyno Cell cadence after 3 s settle: min 58 / median 61 over 104 samples. Keep the extra persistent PSRAM allocation in mind when checking allocation failures. |
| Vault-Tec needle briefly appeared at zero after a theme switch | `build_vault()` reset the newly-created needle object to the zero-angle position even though `s_display_psi` retained the latest sample across scene rebuilds. The next 16 ms update corrected it, making the needle visibly jump. | Seed `s_vault_needle_deg` and `s_vault_needle_over` from `s_display_psi` while building the scene. | Simulator audit holds +8.0 PSI, rebuilds into Vault-Tec, pumps LVGL without another sample, and requires the next sample to move the needle by 0.000 degrees before the normal sweep audit. |
| Marquee's single 72-bulb accent border became three zone rings | The user wanted the static dot border to carry the zone mapping: innermost vacuum, middle boost, outermost overboost - and, after a first render, asked for the rings spread wider apart, the centre shrunk to the tube/segments readout (one sprite set, not two), and the old two-tone look (dim neutral track + vibrant accents) restored instead of all-vibrant rings. The old design had 24 live "accent" bulbs restyling on every zone flip; a live-restyling version of three full 72-bulb rings would need 36+ invalidation boxes per flip (a full ring's bounding box is the whole face), overflowing LVGL's 32-slot invalidation buffer and forcing a full-screen repaint on every flip - several times per second near zero crossing. | Bake all three rings statically in the two-tone language: dead bulbs stay `track`, every sixth pair blooms in THAT RING'S zone colour through `neon_bulb_accent()`. No live pass, no flip invalidation; the border only changes with the palette. `neon_bg_key_t` gained `vacuum`/`boost`/`overboost` (marquee only; ring layouts keep them zero) because zone colours are user-editable and are now baked. Rings at centreline 192/208/224 (`NEON_BULB_RING_STEP` 16 = 9 px bulb + 7 px dark gap); outer silhouette unchanged (tips at 228). Marquee's oversized 130 px readout, its marquee-twin cell metrics, its `NEON_MARQUEE_READOUT_TOP`/`STACK_DY` offsets and the `neon_huge` font/sprite set were all deleted - every layout now shares `NEON_BIG`/`NEON_FONT_PX` metrics, one sprite set, one zone-word Y (-95), one lower-stack rhythm; `main/` and `sim/` CMakeLists dropped `neon_huge.c`. The bulb draw stat (`g_neon_bulbs`) was removed with the live pass. | Sim marquee audit: 517 compares / 0 stale / 0 severe, throughput 1.099 Mpx/s - CHEAPER than v1's 1.279 because the smaller shared readout flushes less. Tube and segments audits unchanged at 310/0/0. Parity test re-derives the bulb colour reference from `boost_gauge.c` (dim-then-bloom, matching `scale_rgb` rounding) and asserts the two-tone pattern and the three radii; `node tools/test_neon_web_parity.js` green. Violet and Miami preset renders confirm rings follow the preset's zone colours. | The innermost ring's inner edge is now 188, and the clearance argument is the SAME one the ring layouts already rely on (widest readout ink ~170 vs the ring's 186 inner glow edge) - marquee's bar/PEAK stack sits at the shared rhythm, PEAK corner radius ~185, inside 188. A restyle-on-flip ring on this face is a cadence trap: price the invalidation boxes against LVGL's inv buffer before building one. |
| Marquee rings spread again, centre shrunk to the shared readout, and lighting became a live stage ladder - then a rotating chase | The static all-baked rings read as "too close together" even at step 16; the user asked for ~1.5-2x spread, staggered (not radially aligned) accents, accents that only light once that stage of boost is reached, and confirmed the old two-tone (dim track + vibrant accent) is the look. The outer ring cannot move (tips at 228 vs panel ~233), so spreading moves the inner rings INWARD, which collides with the full-size 118 px readout composition (~184 px half-width incl glow), the bar corners (~172), and the PEAK stack corner (~183) - so the whole marquee centre must shrink, not just accept a tighter ring. | Step 24 (1.5x): rings at 176/200/224, inner edge 172. The centre draws the SAME shared `NEON_BIG` 118 px A8 sprite set scaled to 0.91 (then 0.87) at blit time via `lv_draw_image` scale_x/scale_y (transform_a8 + transform_and_recolor path), with `neon_mq()` scaling every centre geometry constant (readout metrics, bar half/y/h, stack label Ys, invalidation spans) so draw and dirty-boxes agree. `NEON_MARQUEE_CENTER_SCALE` 0.87 + `NEON_MARQUEE_READOUT_LIFT` 12 (extra up-lift because scaling pulls the readout down) shared by draw and invalidation via `neon_readout_top_off()`. Bar shortened 300->264 (`NEON_BAR_HALF` 150->132), lower stack lifted 8 px (unit/rule/peak 128/138/158). Accent pattern staggered per ring `NEON_BULB_IS_ACCENT(i,z) = ((i + 2z) % 6) < 2`; lighting is a CUMULATIVE stage ladder (ring z lit iff `neon_zone_id(psi) >= z`: vacuum lights only the inner ring, boost adds the middle, overboost all three). All 216 bulbs bake in `track`; each reached ring's 24 accents are LIVE-drawn in that ring's zone colour via `neon_bulb_accent()` - a zone flip invalidates only the changed rings' 12 PAIR-boxes each (single-step flip = 12, two-zone jump = 24, inside LVGL's 32-slot buffer). Zone colours were removed from `neon_bg_key_t` again (the bake no longer uses them). Web mirror mirrors the scale, the ladder, and the stagger; parity test re-derives the bulb colour from firmware constants and asserts the ladder at overboost (all three rings lit). | Sim marquee audit: 0 severe, isolated AA seams only (2,577 px / worst 25 px, the known scaled-sprite transform artefact - tube/segments are 0/0), throughput 1.018 Mpx/s at 62.5 Hz. Parity test green including a second render at psi 8.5 to prove all three rings light and the stagger. | **Rotating mode (`neonMarqueeSpin`, persisted per-theme like `hudTrueBlack`):** accent pattern becomes `((i + 2z + phase_z) % 6) < 2` with `phase_z` a 0-5 index, one ring advancing per `NEON_MARQUEE_SPIN_MS`=90 ms tick round-robin (ring z steps when tick%3==z, so a full 6-phase rotation takes 1.62 s), inner/outer clockwise (-1) and middle counterclockwise (+1) on the y-down screen. Phases live in `s_neon_spin_phase[]`, reset to 0 on scene build; unreached rings advance silently (nothing lit to repaint). A spin step changes 2 bulbs per 6-group, so it invalidates 12 three-bulb boxes for the advancing ring - and is SKIPPED on samples that already do a zone flip so flip+spin never stack past the 32-slot buffer. **Bug caught by the spin-on sim audit:** the first version invalidated `base-1,base,base+1` around the POST-advance base, which is correct only for dir=-1; for dir=+1 the accent pair slides the other way and the newly-darkened bulb was left stale (245,772 px severe). Fixed by capturing `base_old` before the advance and starting the 3-residue union at `base_old` for dir=-1 but `base_new` for dir=+1 - spin-on audit then matched the spin-off baseline (0 severe, 2,577 px isolated seams). `--neon-spin` and `--neon-chase DIR` sim flags render the chase for previews; mock server round-trips the toggle; parity test asserts the mirror's `NEON_MARQUEE_SPIN_MS` and direction table equal firmware's and that accent positions follow the round-robin phase formula at explicit tick counts. |
| Marquee dot spacing made uniform across the three rings | The three rings each had 72 bulbs, so the CHORD spacing (2*pi*r/N) scaled with radius: inner 15.4 px, middle 17.4 px, outer 19.5 px - the inner ring was 21% tighter than the outer, which read as cramped. | Per-ring bulb counts chosen so chord spacing is uniform: inner 54 (20.48 px), middle 66 (19.04 px), outer 72 (19.55 px) - within a pixel of the outer's spacing, vs the old 4 px spread. All three stay divisible by 6 so the 2-lit/4-dark accent pattern wraps seamlessly and the invalidation groups of 6 stay whole (`NEON_BULB_N(z)` macro over `NEON_BULB_N_INNER/MID/OUTER`; the spin and zone-flip loops use `NEON_BULB_N(z)/6`, so box counts per ring are 9/11/12). Web mirror (`ringN`), parity test (reads the three defines, ladder + spin + radius blocks all offset-index per ring), mock unchanged. | Parity green (ladder, spin at 6 tick counts, radii); sim marquee spin-on audit 0 severe / 2,578 px isolated AA seams, 1.126 Mpx/s; hardware flash clean boot, toggle survived NVS reboot. Hardware 30 s cadence: median 55-56 renderFps with pixelsPerSecond ~1.1 Mpx/s - the change strictly reduces work (216 -> 192 bulbs, fewer invalidation boxes) and the FPS spread vs the earlier capture is the demo-sweep phase confound, not a regression. | Never assume equal bulb counts give equal visual spacing on concentric rings - the chord scales with radius. Keep the count divisible by the accent period so the pattern and the invalidation groups stay whole. |
| Marquee readout repaints paid LVGL's per-frame transform; pre-scaled sprites fix it | The marquee draws the shared 118 px A8 sprite set at NEON_MARQUEE_CENTER_SCALE (0.87) through `lv_draw_image` scale_x/scale_y, routing every readout cell repaint through the SW transform path (inverse map + bilinear). Host A/B on identical dirty regions isolated the transform at ~35-40% of readout-repaint time: plain blit p50 0.09 ms / max 0.45 ms vs transform p50 0.14 ms / max 2.15 ms, and the per-frame transform's pixel rounding was the cause of the marquee's known "isolated AA seam" stale-pixel class (2,577-2,610 px, never severe). | `neon_bake_scaled_sprites()` bakes a second 0.87-size A8 set ONCE per marquee scene build: each glyph crop is re-rendered through the SAME `lv_draw_image` transform into a scratch RGB565 canvas (so the pixels are identical to what the per-frame draw painted), the exact transformed area is copied out using LVGL's own integer corner math (`bw/2 + ((±bw/2 * scale) >> 8)`), and each slot's `bbox_s` is the tile's dest offset from the blit anchor. Live blits become plain stride-copy blends (scale=1); allocation failure falls back to the per-frame transform. ~100 KB extra PSRAM while the marquee sprite layout is active; first marquee build ~513 ms (scaled bake adds ~66 ms over the plain glyph bake), cached returns ~172 ms. | Host: parity green, geom green, marquee audits spin-off AND spin-on now **0 severe AND 0 stale px** (the pre-scaled blits eliminated the readout AA-seam class), p50 cycle 0.09 ms / max 0.56 ms, big-cycle repaints 0.30-0.44 ms; tube/segments audits unchanged (0/0, 1.258 Mpx/s). Hardware A/B, fresh boot each arm, spin + demo on, pixel shift off, 30 s (bench committed as `tools/bench_neon_readout.py`): BEFORE (per-frame transform) renderFps median 55 / min 41, framesOverBudget/s 33.2, worstRenderUs median 43.0k / max 63.0k us; AFTER (pre-scaled) median 57-58 / min 44-47, over-budget/s **21.6 (−35%)**, worstRenderUs median 42.0k / max 55.7k us. | The median worst stays ~42 ms on both arms: the worst cycles are TE-wait + merged full-region raster bound, not sprite bound - the win shows as fewer over-budget frames and a better tail, not a lower median worst. Any future readout change must keep the scaled-set path pixel-identical to the per-frame transform (same lv_draw_image call at bake) or re-verify the look on glass; never reintroduce per-frame sprite scaling without re-running the host A/B. |
| Marquee accent anchor shifted again; spin-vs-min-FPS measured on the board | The user's static-pattern review of 419d04d found the OUTER ring's accent pair still straddled the bottom axis while the inner ring's pairs flanked it (off-axis), i.e. the two read differently at 6 o'clock. Separately, the pre-scaled-readout A/B (row above) left "why is min renderFps still in the 40s" open: worst seconds had 10-13 over-budget cycles/s with 50-61 ms worst cycles, but the correlation was not isolated. | `NEON_BULB_ACCENT_OFFSET(z)` = `(z)==1 ? 3 : (z)==2 ? 2 : 0` (was 0/3/0): middle ring keeps its bottom-centre pair (bulb N/2 at 6 o'clock, partner one dot left), the OUTER ring moves two bulbs on so its pairs sit at residues 2,3 and FLANK top/bottom instead of straddling them - the inner ring's pattern, as close as the different counts allow (outer pair rel +20/+25 deg vs inner +20/+26.7 at the bottom; the top pair becomes asymmetric as an inherent side effect of the 6-bulb period). Web mirror and parity test (ladder + spin blocks) updated in lockstep; sim marquee audit stays 0 severe / 0 stale. **Min-FPS isolation (fresh captures, same ddbf9d5 build, neon/marquee/demo, pixelShift off; harness `tools/corr_zone_flip_fps.py`):** spin OFF 120 s -> min 58 / med 61, zone-flip seconds never below 58 (flips cost ~2 FPS, ob/s 1.8x steady); spin ON 181 s -> min 45 / med 58, worst 10 seconds carry 10-13 over-budget cycles/s at 50-61 ms worst cycles, 8/10 coinciding with zone crossings. The 40s mins are fast-motion seconds (demo sweep peak slew 9.789 psi/s near the zero crossing), where every tick invalidates the tenths cell + bar span; each spin step is an extra render cycle that pays the regionDBuf TE wait (up to a full 16.7 ms period) when the scan is crossing the readout band (rows ~185-288, right in the scan's path), so ~11 extra cycles/s cost ~13 FPS (58 -> 45). Zone flips add the widest single repaint (~40 k px readout recolor + word + bar + ring boxes, ~40 ms) but are NOT the floor (spin-off flip seconds >= 58). | The spin toggle is the dominant min-FPS lever and it is decorative: each 90 ms step is a render cycle charged the TE wait in fast motion. Caching the accent dots as sprites would NOT help - they are already opaque `lv_draw_rect` fills drawn only where dirty, and the cost is per-cycle (TE wait), not per-pixel; the pre-scaled sprite A/B already proved pixel-cost cuts move min only 41 -> 47. Real levers: slow the spin cadence, defer steps on heavy fast-motion ticks (spin already defers on zone-flip frames), or the stubbed `BOOST_LCD_TE_SCANLINE`. Re-measure min-FPS with `tools/corr_zone_flip_fps.py` (it enables spin, captures ~4 Hz, restores spin to off) rather than a 30 s window - a 30 s window can miss or over-sample the crossing seconds. |
| Neon invalidation tightened for the 60 fps push (2026-08-09 working tree; host-verified, hardware bench pending) | The marquee pre-scaled set AND the full-size set (tube/segments) both blit per-glyph tiles at `anchor + bbox`, but every readout-cell invalidation was the uniform label box (cell pitch + bleed, ~±41 px) unioned with the full-sprite tile — sized to SPACING, not ink, so it over-covered by tens of px per cell on every changed-cell repaint. The marquee bar also invalidated on every 16 ms sample whether the fill moved a pixel or not, and the live accent pass scanned all 192 bulbs on every callback invocation even when the dirty region could not reach the rings. | The invalidation never asked the baked sprite for its own footprint (it has one: the bake-time bbox + tile width). `neon_cell_x_span`/`neon_sign_x_span` now take the glyph index and REPLACE the label box with the tile's exact extent (+1 px AA margin): the marquee scaled set via the pre-scaled tile's `bbox_s` at the scaled anchor, the full-size set (mq=1.0) via the full-size bbox at `spr_dx`. Changed cells union the OLD and NEW glyph footprints (a '1' replacing a '0' sits differently), the count-change path still unions into the full composition box, and the fallbacks (sprites unavailable, marquee per-frame-transform) keep the conservative label-box union. The bar is gated on the DRAWN pixel extent + zone flip (`s_neon_bar_lo/hi`, INT_MIN/INT_MAX sentinels reset at scene build) so a static marquee goes idle like every other face. `neon_bulb_pos` offsets are precomputed once (bit-identical `lroundf(cosf/sinf·r)` table); the live accent scan is skipped when the dirty region stays inside the innermost ring's inner edge (`clip_reaches_radius`). | Host audits (25 s, 1550 samples, all four variants): **0 severe / 0 stale** everywhere. Marquee flush unchanged 14,848 px/cycle (spin 16,441); cycles 1350/1550 no-spin (the bar gate retired 200 cycles) and 1377/1550 spin. Tube/segments flush **19,753 → 18,397 px/cycle (−6.9%)** from the full-size tight span; cycles 1542/1550. `tools/test_neon_geom.c` and `node tools/test_neon_web_parity.js` green. The `±14` pad in `neon_inv_span` is NOT slack — it is the halo band's inner edge (radius 199, width 13 → inner 192.5) versus the invalidation's assumed 228±21 → 207; keep it. | Any future readout change must keep the invalidation and the blit sharing the SAME anchor+bbox formula (marquee: scaled anchor + `bbox_s`; full-size: `spr_dx` + bbox) or the tight span strands pixels. The locked-60 claim still needs the board: re-run `tools/bench_fast_motion.py` sweep + `tools/check_display_cadence.py` per layout with neon/demo on and compare `renderFps`/`framesOverBudget`/`worstRenderUs`, plus a fresh visual tear check. |
| Hardware validation completed (2026-08-09): locked-60 bench and the FPS-vs-TE accounting | The row above left "hardware bench pending". Separately, `_reconcile_te.py` summed waits+skips (~1.47x fps), implying teSkips and teWaits were separate event classes. The real accounting: `te_wait_for_region_spans()` increments `teWaits` UNCONDITIONALLY once per writeback/RENDER_READY-with-data pass (one per render cycle), so **teWaits == renderFps by construction**, and `teSkips` is only the SUBSET of those calls that skipped the wait (skips ⊂ waits). | Verified on hardware across 41 windows: `waits/fps = 1.000` everywhere. Battery A (30 s/window, fresh captures, all four neon layouts + dyno-cell, `teTimeouts 0` everywhere): dyno-cell min 58/med 61 (guard PASS), tube 53/58, segments 40/57, marquee 26/36 — nearly identical to the prior session reference (58/61, 52/58, 39/57, 24/36). Fast-motion constant-slew sweeps (`tools/bench_fast_motion.py sweep`, fresh boot per arm): marquee **min 56 / med 59** (1 ob/s, worstUs 43.4 ms), tube 45/56 (5 ob/s), segments **29/45 (14 ob/s)** — under sustained slew the layout ranking INVERTS vs the organic demo: segments re-lights discrete wedges every tick while the marquee's bar+readout cost stays bounded. Organic cross-check (90 s, marquee): fastest crossing seconds min 43/med 52 vs slowest peak-dwell seconds **min 24 / med 31** — the marquee's floor is the DWELL seconds (needle hovering at a turning point while the tenths digit flutters), not fast motion; the opposite of the Vault pattern, which must therefore be measured per layout, never assumed. `_reconcile_te.py` output fixed to report skips as a % of waits instead of an additive rate. README cadence section updated with these numbers. | A future TE-metric read: teWaits==renderFps is a property of the counter's placement (one increment per writeback pass), not a coincidence; teSkips ⊂ teWaits; only `teTimeouts` is an independent error signal (0 across every run this session). The locked-60 claim is now validated for dyno-cell (guard PASS) and for the marquee in the constant-slew regime (56-59); organic-demo medians sit lower on every face by design. Remaining before calling the neon work done: a fresh visual tear check on the physical panel — framebuffer snapshots cannot contain a tear, so only the user's eyes on the glass can close that item. |
| Contract (2026-08-09): every selectable theme is a locked-60 target; dyno-cell is the reference guard, not a ceiling | The cadence contract and AMOLED gate read as if dyno-cell were the only face expected at 60 FPS ("Only the first of those is the guard" / "the richer faces legitimately sit lower than arc"). That framing predates the other faces — dyno-cell was the only theme when the guard was established — and survived as a permission for every later face to sit below 60. | Per user directive: **every selectable theme locked at 60 FPS** in demo mode — dyno-cell, vault-tec, night-city, big-digit, and neon tube/segments/marquee must each hold a sustained median ≥60 under both the organic demo waveform and the constant-slew fast-motion sweep (`tools/bench_fast_motion.py sweep`, 9.789 psi/s). dyno-cell keeps its status as the reference guard (the conditions the threshold was established under); the sweep is the brutal-test instrument the remaining faces are measured against. No visual compromise is allowed to buy frames; a visual-vs-performance trade is a proposal to the user, not an implementation. | Baseline (2026-08-09, aafcfcf) sweep matrix (constant slew, 9.789 psi/s, fresh boot per arm): dyno-cell min 56 / med 60 (0 ob/s), vault-tec 59/60 (0 ob/s), night-city 41/60 (zone-crossing tail, 77 ob sum over 19 windows), big-digit 57/60 (0 ob/s), neon tube 45/56 (5 ob/s), segments 29/45 (14 ob/s), marquee 56/59 (1 ob/s), marquee spin-on 42/52.5 (8 ob/s). The organic demo differs sharply where dwell-time flutter dominates: big-digit ~27-30 (bucket-boundary jitter re-runs the banded ground sweep), marquee 26/36 (tenths flutter), night-city ~40-42 (zone flips). The two waveforms stress different costs and BOTH are required gates. |
| Theme optimization campaign (2026-08-09): four no-visual-change wins integrated; the remaining gaps are visual-vs-performance trades (proposals) | The locked-60 contract needs per-theme work. A 5-agent campaign (one per theme, each in its own worktree) plus coordinator work produced four host-verified, hardware-verified commits on main. | (a) dyno-cell (`df35958`): `update_arc()` ran a soft-float `%.1f` conversion for the PEAK label every tick and `set_value_arc()` recomputed angles/colours on dwell ticks where the wedge was already committed (its invalidations were zero-length no-ops). Peak text is now cached behind `s_peak_psi`; `set_value_arc()` early-outs on equal endpoint+colour. Wedge invalidation geometry byte-for-byte unchanged. (b) vault-tec (`9402ff2`): `invalidate_vault_needle()` applied one flat 9 px pad to all three radial slices although the wedge tapers 7→2.5 px; pads now follow the local half-width via a new `VAULT_NEEDLE_TIP_HALF` shared with the draw so the two cannot drift. (c) night-city (`ad49e8f`): the HUD fill arc invalidation used a ROUNDED stroke box (over-covered by HUD_ARC_WIDTH/2 on every edge on every tick); switched to the exact flat stroke box + 3 px AA margin. (d) vault-tec (`f0c0c32`, rescued from the completed vault subagent's second commit): `draw_vault_readout()` skips any slot whose box misses `layer->_clip_area` (`neon_area_overlaps`), eliminating the LVGL label draw-task allocation + clip test for invisible slots on every readout repaint; a skipped slot's ink sits inside its own 26x34 box and non-adjacent slot boxes are 23 px apart, so it cannot reach the dirty region. Rendered pixels byte-identical. | Host audits (0 severe everywhere; dyno 0 stale, night-city 0 stale, vault 3-5 isolated 1-step AA seams = the documented baseline condition): vault flushed px/cycle 10786→9926 (−8%, pad fix) then 9926→9862 with the clip-rejection (combined −8.6%); night-city 7141→6658 (−6.8%); dyno flush unchanged (geometry untouched). Hardware (fresh boots): sweep arms (30 s) — dyno 56/60→56/60 flat (the win shows in organic dwell), vault 59/60→58/60 with worstUs 17689→16906 (−4%), then the clip-rejection build (f0c0c32) re-verified on hardware: vault sweep median 60 (min 51 = one settle-transient window), worstUs median 17.9 ms, over-budget median 0, pixels/s 1.06 M, teTimeouts 0 — flat vs baseline, no regression. night-city min 41→43 with over-budget sum 77→70 (−9%, median 60 both). Organic matrix after (20 s arms): dyno 59/60 PASS, night-city 51/62 PASS, vault 52/58, neon tube 54/59, segments 36/56, marquee no-spin 27/34 / spin 25/36, big-digit 21/35 — the known organic floors. Conclusion: dyno/vault/night-city/big-digit all hold median 60 under the brutal sweep; the organic-demo floors (big-digit ~21-27, marquee 25-36, segments 36-56, tube 54-59) are the real remaining gaps, and the safe no-visual-change wins there are exhausted (tight per-glyph spans, pre-scaled sprites, idle gates, segment-box clip, banded recolour all already shipped). | **Proposals for the user (visual-vs-performance trades, NOT implemented):** (1) **Big Digit** — the organic floor is the ground re-colour re-firing on boundary jitter: buckets are ~0.42 psi wide (24 over 0..max) and the demo flutter is ±0.2 psi, so the value sits in boundary-crossing range roughly half the time it is positive; a committed-bucket hysteresis (start a banded wipe only when psi has moved a full bucket past the last committed one) would keep the visible sweep and stop bounce-back restarts, likely recovering most of the 21→60 organic gap. (2) **Neon segments** — the sweep floor (29/45) is the per-cycle raster of ~3.3 segments x 3 arcs plus the readout; reducing `NEON_NSEG` (fewer, wider wedges) is a chunkier look. (3) **Neon marquee** — the dwell floor is the tenths glyph fluttering at turning points; a fast-motion tenths sample-and-hold is a visible readout trade. (4) **Neon spin** — each 90 ms step pays a TE wait (already deferred on zone flips); slowing the cadence trades sparkle for cadence. (5) **Vault peak-mark** (from the vault subagent's report) — the PEAK object is 34x34 while the drawn triangle needs at most ~24x24 incl. AA; shrinking to ~26 cuts ~10% of mean flushed px with byte-identical rendered pixels but changes a layout property, so proposal only. (6) **Vault needle gate** — the 0.35 deg (1.03 px at tip) gate could rise to ~0.5-0.7 deg to skip more sub-pixel repaints; that is a visible jitter/lag trade, proposal only. All are conversations, not shipped. |
| Over-engineering cleanup (2026-08-11): ~2,600 lines of dead code, speculative tools and duplicated harness plumbing removed | A full-tree ponytail audit (not a diff) found dead tool files, a stranded legacy gesture subsystem, an unreachable Sport Cluster renderer, dead model/media plumbing, and eleven copies of the same board HTTP client with drifted timeouts. | **Deleted:** tools/model_neon_demand.py, gauge_preview.html, neon_mockup.py + preview/neon_mock/, bench_neon_cadence.py, neon_sprite_budget.py, capture_state.py; the legacy gesture subsystem + boost_gauge_create() in boost_gauge.c (stranded: boost_page.c owns gesture classification); Sport Cluster outright (renderer, enum member, `"sport"` style token, web mirror - user sign-off; design history stays in git); boost_model media-status plumbing (s_media, set/get_media_status, playback_supported - zero callers); #if 0 neon-numeral block; boost_page_root(); dot_index dead var; web drawSportGauge, mediaPreview, linMap, hudPrevPsi, el.shell/el.gaugeMirror, dead CSS; android dead model fields, pit-lane->dyno-cell defaults, ConnectionStore inlined, dead gradle deps, Math.floorMod. **Refactored:** three theme-payload folds -> applyThemePayload() (web/app.js), three /time POSTs -> syncDeviceClock(), tools/bench_common.py (api_get/put/post/wait_online/wait_display_metrics) shared by bench_fast_motion/bench_region_dbuf/bench_hud_gradient/bench_neon_readout. **Deliberately kept per user:** TPMS protocol layer + boost_tpms get/set/poll/.enabled/BLE define, TE-scanline compile stub, sim run_chase, tools/_reconcile_te.py, RGBA->PNG format. `neonSpinTicks` is NOT dead - the parity test injects it for a deterministic spin phase; the original "dead conditional" finding was wrong and the hook was kept. | Sim rebuilt (boost_gauge/theme/neon_geom/page/tpms all recompiled clean), full IDF build green with regenerated assets, neon web parity green, test_neon_geom + test_tpms_protocol pass, sim screenshots render, all touched tools py_compile, test_map_conversion passes, mock_server CSV endpoint verified, and the refactored dashboard exercised end-to-end in a browser against the mock (cockpit + settings load, badge Live-Http-4Hz, 5 themes/no sport, theme switch to Neon applies, regionDBuf toggle fires its fold). | Guard now: web edits are useless until tools/embed_web.py is re-run (done here); any future re-animation of the marquee spin must keep the state.neonSpinTicks parity-test hook. Next bench work should extend tools/bench_common.py instead of copy-pasting another api_get. |
| Neon tube inner-dark-ring (halo) tip pump traced to the 0.2 deg halo extension being quantized by LVGL's 1 deg integer arc grid; extension reverted, pump gone (2026-08-12, flashed + measured) | The first fix (a 0.2 deg halo tip extension to compensate the radius-dependent angular AA) made the inner ring WORSE in a different way: the user reported the inner dark ring 'goes out of sync ever so slightly... sometimes a tiny bit ahead and sometimes a tiny bit behind, like it's late to react'. | LVGL truncates arc angles to integers (`lv_draw_sw_arc.c:88-89`), so the extension arc [a_val, a_val+0.2] paints NOTHING when frac(a_val) <= 0.8 and a full 1 deg halo stub when frac > 0.8 (the zero-span case also early-returns at line 58). The halo's painted tip edge therefore pumped between aligned and +1 deg ahead (measured in the sim: h-t -0.82/-0.75/-0.90 on extension frames vs +0.10..+0.14 on aligned frames - a 1 deg dither on ~20-40% of frames). The original 'lag' diagnosis was itself partly a coverage-threshold measurement artifact (dim tones need higher coverage to read, so the halo's high-coverage edge sits inside the geometric tip while the bright bands' sits past it). | Removed `NEON_TUBE_HALO_TIP_EXT` entirely (the define, the extra halo-band arc in `draw_neon_live`, and the invalidation expansion in `update_neon`). With the extension gone the halo's painted edge tracks the track/cap exactly (same tip arc, same truncated end), and the residual visible offset is a constant sub-degree fade difference. | Sim TIPLOG harness (temporary, removed): halo-track delta constant +0.10..+0.14 deg across all vacuum frames (was -0.82/-0.75/-0.90 dithering). All three neon layouts still audit 0 severe / 0 stale. Board (linear sweep, BLOODMOON, 10 snapshots): track-halo range [-0.15, -0.01] deg - consistent sub-pixel, no pump. The sub-degree residual is inherent to the 1 deg integer arc grid + radius-dependent AA; a true fix would need a custom hard-edged tip mask, not an arc. A fresh visual check on glass is the final word. |
| Demo source became a 3-way select in Settings: Off (live sensors) / Demo / Demo + linear sweep (2026-08-12, flashed) | The board supports `demoFastSweep` (transient 9.789 psi/s constant-slew triangle) but the dashboard only exposed a demoMode checkbox, so the user could not switch the sweep on without the API. | The firmware already handled both fields; the web UI did not. `web/settings.html` replaced the demoMode checkbox with `<select id="demoMode">` (off/demo/sweep); `web/app.js` derives demoMode from `pick !== "off"` and demoFastSweep from `pick === "sweep"` in the form-to-payload direction, folds both booleans straight from the PUT response in `applyThemePayload` (the firmware echoes the full config), and `syncDisplayToggles` maps state back to the select (sweep > demo > off). `tools/mock_server.py` now round-trips `demoFastSweep` and serves GET /api/v1/themes/config. | Verified on the mock (PUT/GET round-trip both fields) and on the board: served settings.html contains the select, app.js contains demoFastSweep (decompress check), and the sweep runs with peak ratcheting to 9.99. demoFastSweep stays transient - it does not survive reboot and requires demoMode on. |
| Neon tube/segments geometry rework (2026-08-11, host-verified, not yet flashed) | User-requested visual tweaks to the neon theme: segments 35% wider with the original 2-degree gap restored; tube 0 marker 25% narrower and centred on the real zero; tube white outline kept skinny; the track widened into two clearly distinct tones that read as a smooth gradient (dark halo -> bloomed middle -> lighter outer -> white cap), never a dark-bright-dark sandwich. Also: the sim's "boost" screenshot (8.5 psi) was actually the OVERBOOST zone (threshold 8), so every gauge sheet lacked a real boost column. | The old segments had 54 x 5-degree slots (3-degree lit wedges, 2-degree gaps); widening the lit wedge alone ate the gap. The tube marker paints off-centre because lv_draw_arc's trig table quantises edges. Lightening the track outer toward white desaturated it into the cap ("too pale"); deepening it broke the gradient into a sandwich; the working rule is HSL lightness +0.20 keeping hue+saturation. | **Segments:** NEON_NSEG 54->45 (6-degree slots -> 4-degree lit wedges with the 2-degree gap exactly restored; 35% is limited by the integer count, so 33% is the closest), NEON_SEG_HALO_W 20 vs the 25 px body (was equal 25/25), NEON_SEG_BAND_DEPTH 49. **Tube:** four bands - NEON_TUBE_HALO_W 20, track halves NEON_TUBE_TRACK_HALF 16 (32 total, each < halo), outer band = neon_hsl_lighten(neon_lit(accent), NEON_TUBE_TRACK_LIGHT 0.20) (new RGB<->HSL helper), cap stays 6 px at NEON_R; marker NEON_TUBE_ZERO_DEG 3.0->2.25 plus NEON_TUBE_ZERO_CENTER +0.25 so the painted centroid lands on the run start; unlit track widened to the track+cap footprint. Sim: boost shot 8.5->5.0 psi. Web mirror and parity test updated (outer colour asserted to be the firmware HSL lighten, not a white-lift/deepen). | Host: parity + geom green; tube and segments 25 s stale-pixel audits 0 severe / 0 stale every round; mid->outer band distance ~107-140. NOT flashed - the user is reviewing the sim renders; re-run the dyno-cell cadence guard and a visual tear check before flashing, since the tube's bake/invalidation radii changed. |
| Neon peak tell-tale rework + invalidation tightening (2026-08-11, host-verified, not yet flashed) | The user's bench review: the tube's peak marker sat up to a full segment pitch off the actual measurement and did not cover the track's inner depth, flickered in/out as the run crossed it, and re-tinted in the live zone colour; both tube/segments stutter at the boost->overboost flip. | (1) The tube reused the segments' marker: a single arc snapped to the 6-degree grid (up to ~6 deg off the exact peak angle) at NEON_SEG_W=30 body width (missed the inner 6 px of the 55-deep unlit track) in the peak value's bloomed zone colour. (2) `peak_in_run` suppression toggled at segment granularity while the run tip moved continuously, so the marker popped in/out around the peak. (3) A genuine stale-pixel bug: the ring guard's corner-radius threshold (NEON_R minus band depth = 179 segments / 173 tube) sat ABOVE the baked halo tiles' AA fringe (~r=178 segments); a readout repaint whose right-edge corner landed just under 179 skipped the marker and repainted the background canvas over its fringe, stranding it black (tile-marker audit failed 2 severe). (4) Segments still invalidated the ring in 90-degree chunks (the tube's 30-degree knee was measured in the flip-deferral row but never ported) and both layouts padded the sector bbox by 14 px, though `lv_draw_arc_get_area` already includes the end-corner rays and the gradient mask overhangs only 4 px. | Tube: continuous marker at ap +/- NEON_TUBE_PEAK_DEG (3.0) at full NEON_TUBE_BAND_DEPTH, ALWAYS drawn while a peak exists (no in-run suppression -> no flicker), skipped only when it would overlap the white zero marker. Segments: the segment-quantised selection is verified correct (floor((ap-START)/PITCH), the same indexing the run's `boost_neon_lit_span` uses), now drawn at full depth via the three baked band A8 tiles recoloured flat (byte-identical to a lit segment's geometry; the full-depth live arc and the recoloured-tile blit both failed the byte-exact audit until the guard fix below), body-width arc fallback. Both layouts use the fixed dimmed vacuum inner-ring tone `scale_rgb(vacuum, NEON_HALO_DIM)` (`neon_peak_color`): a reference mark that never re-tints at zone thresholds, so `peak_color_flip` and `s_neon_peak_color_psi` were deleted. Ring guard lowered 3 px inside the band inner edge (176 segments / 170 tube) so every region that can touch the marker/run AA fringe runs the ring draw. Segments chunk step 90->30. Pad 14->7 (`NEON_INV_PAD`: 4 px mask overhang + ~2 px AA + 1 px margin). | Sim audits byte-clean (0 severe / 0 stale, 517 compares) on tube, segments, marquee and marquee-spin. Flip worst-cycle flush: tube 83161->73504 px (-11.6%), segments 103124->73303 px (-28.9% combined with the pad); flushed px/cycle 19111->17448 (tube, -8.7%) and 19334->18353 (segments, -5.1%); marquee unchanged. The tile-marker stale bug was caught by the audit, bisected to the guard, and the guard fix re-verified (2 severe -> 0). neon geom + web parity green; the web mirror draws no ring peak marker (only the PEAK text), so no mirror change. NOT flashed - the user is reviewing sim renders; before flashing, re-run the dyno-cell cadence guard and a visual tear check, since the tube's marker geometry and both layouts' invalidation bounds changed. |
| Neon marker/zero-marker review on glass (2026-08-11, flashed) | User's bench review of the flashed peak-marker build: (1) the tube's white ZERO marker extends past the track - it should be fully contained within it; (2) the arc never appears to extend past the max PSI marker - the linear sweep should max at 9.9-10 but the run stops at the marker's near edge, and the arc should be drawn OVER the marker; (3) the segments peak marker was extended beyond what was asked - it should be the width of the track; (4) on tube, make the max PSI marker the same width as the zero marker. | (1) The tube zero marker (baked AND live-redrawn) used NEON_TUBE_BAND_DEPTH (55, r 173-228) while the UNLIT TRACK is only NEON_R - NEON_TUBE_HALO_R + 1 = 36 deep (r 192-228): the marker bled 19 px past the track's inner edge into the black halo gap. (2) The tube peak marker was drawn AFTER the run, so it painted OVER the arc and hid everything beyond its near edge - the run seemed to stop at ~9.3 psi. Compounding it, the linear sweep (demoFastSweep) clamped at PSI_MAX = 9.6 while the dial maxes at 10, so the run never reached the dial end and the peak (a ratchet to the sweep max) sat right on the run tip. (3) The segments marker was extended to full NEON_SEG_BAND_DEPTH (49, halo included) in the prior row - the user only ever wanted the track width (NEON_SEG_W = 30). (4) The tube peak marker and zero marker used different widths (55 vs 55 - actually the same BAND_DEPTH, but both were the wrong width; the ask is that both equal the track width). | (1) New `NEON_TUBE_TRACK_W (NEON_R - NEON_TUBE_HALO_R + 1)` (36) is now the single source for the unlit track bake, the zero marker (baked + live), AND the tube peak marker - the zero marker is fully inside the track and the max marker is the same width. (2) The tube peak marker now draws BEFORE the run (the lit arc sweeps over it), clamped to [ARC_START, ARC_START+ARC_RANGE] so a peak at/over psiMax can never paint past the dial end; the invalidation clamps the same way. The linear sweep gained `FAST_SWEEP_MAX` 10.0 (waveform, clamp, and period all use it; organic demo waveform still clamps at PSI_MAX 9.6), mirrored in `tools/bench_fast_motion.py`. (3) Segments peak marker reverted to a single body-width arc at NEON_SEG_W (the track width); the full-depth tile-blit path was deleted. (4) Both tube markers now share NEON_TUBE_TRACK_W; the marker stays in the dimmed vacuum tone `neon_peak_color`, always-drawn (no flicker), skipped only when it would overlap the zero marker. | Sim audits byte-clean on tube, segments, marquee and marquee-spin (0 severe / 0 stale, 414 compares each); neon geom + web parity green. Firmware built and flashed; glass-verified: zero marker white extent r 193-227 (track 192-228, was 173-228), peak marker r 191-226 (track width) clamped at the dial end with nothing painted past math 315 (= 405 deg LVGL = psiMax), the run covers the marker at the sweep top (0 marker pixels past it), and the sweep peak now ratchets to 9.99-10.0 (was 9.6) at 60 renderFps / 0 teTimeouts. Re-run the dyno-cell cadence guard and a fresh visual tear check on glass before declaring the neon work done - the marker/zero geometry and both layouts' invalidation bounds changed. |
| Neon marker bench follow-up: zero marker restored, peak marker angular width halved (2026-08-12, flashed) | After the previous row's glass review, the user clarified two things: (1) the "keep the marker inside the track" request was about the PEAK/max marker ONLY - the white zero marker was shortened by mistake and must go back to its original full band depth; (2) the peak marker mid-track reads "a lot wider" than at the dial end: at psiMax the dial clamp cuts the +-3.0 deg marker in half to a 3-deg band, and that cut-off band is the "correct" width - mid-track the full 6 deg looked twice too wide. | (1) The previous row applied NEON_TUBE_TRACK_W (36) to the zero marker (baked AND live redraw) based on the misspoken request. (2) NEON_TUBE_PEAK_DEG 3.0 makes the marker 6 deg total; the dial-end clamp (hi = min(ap+DEG, ARC_END)) halves it to 3 deg there, so the same marker appeared as two different sizes depending on position. | (1) Zero marker (bake in build_neon + live redraw in draw_neon_live) back to NEON_TUBE_BAND_DEPTH (55, r 173-228) - a bright full-band landmark again; the web mirror already drew it at full depth, so firmware now matches the mirror again. NEON_TUBE_TRACK_W (36) remains the width for the unlit track bake and the TUBE PEAK marker only. (2) NEON_TUBE_PEAK_DEG 3.0 -> 1.5 (3 deg total): the marker is now the same size everywhere, equal to the dial-end look the user approved; at psiMax the clamp still halves it (1.5 deg visible), the same natural cut-off. Invalidation spans (update_neon) follow the constant automatically. | Sim audits byte-clean: tube/segments/marquee 0 severe / 0 stale (414 compares each). Sim pixel-verified hold state (psi 3, peak 6): zero marker white r 173.7-228.6 (full depth), peak marker 2.83 deg span (target 3) at r 192.0-227.3 (track width). Firmware built + flashed; glass-verified under the linear sweep (demoFastSweep, peak held at 10.0): zero-marker white reaches r 173.9 in every snapshot (full depth restored), peak marker at the dial end spans 1.8 deg (clamped 1.5 + AA) at r 191.6-227 (track width). The mid-track 3-deg marker is gesture-reset-only on glass, so it is sim-verified (same arc call, unclamped). The vacuum run's halo band is the same dim tone as the marker by design (scale_rgb(vacuum, NEON_HALO_DIM)). |

| Tube peak marker: angular width matched to the 0 marker, radial depth kept inside the track (2026-08-12, flashed, corrected ledger) | A mid-round misread sent the marker to the full 55 px band (r 173-228, the zero marker's depth) on the claim that "skinnier than the 0 marker" meant radial thinness. The user's follow-up was explicit: the peak marker must stay CONTAINED WITHIN the track (it must not bleed into the dark halo the way the 0 marker does), and "width" means the ANGULAR span - how many degrees it extends left/right of its centre line - which must equal the 0 marker's total angular width. | NEON_TUBE_PEAK_DEG had been cut to 1.5 (3 deg total) after an earlier bench round where the 6 deg mid-track marker looked twice as wide as the dial-end 3 deg cut-off; that left it at 2/3 of the 0 marker's 4.5 deg, which is exactly what read as "skinnier". The radial depth was momentarily set to NEON_TUBE_BAND_DEPTH (55) in the mid-round misread. | `NEON_TUBE_PEAK_DEG` 1.5 -> 2.25 (== NEON_TUBE_ZERO_DEG), so the two landmarks share the same total angular width (4.5 deg, both truncated to 4 deg by LVGL's integer angle mask - identical for both). `arc.width` back to NEON_TUBE_TRACK_W (36, r 192-228) so the marker stays fully inside the track; the zero marker keeps the full band. Draw-before-run order, dial clamp (cuts the band in half at psiMax - accepted), always-drawn (no flicker), dim vacuum ink, and the zero-overlap skip are unchanged. Bonus: the wider 2.25 span moved the marker's start edge past the readout dirty-box corner, so the 1-step AA seam that the full-depth variant introduced at (401,301) is GONE - the tube audit is byte-clean again (0 severe / 0 stale). | Sim: all three layouts + marquee spin 0 severe / 0 stale; geom + web parity green. Hold-state render (psi=3, peak=6): peak marker r 192.2-227.2 (track-contained) spanning 335.02..338.76 deg (3.75 deg painted from the same 4-deg truncated mask as the 0 marker). Firmware rebuilt and flashed to COM3; on glass under the linear sweep (peak 9.99 clamped at the dial end) the dim BLOODMOON marker spans r 191.6-226.5 (track band) over 42.2..44.8 deg - contained, and the angular half-width now equals the 0 marker's. | The peak marker's reference is the 0 marker: same ANGULAR half-width (NEON_TUBE_PEAK_DEG == NEON_TUBE_ZERO_DEG), but never the 0 marker's full radial depth - track width only. A mid-track tap-reset is the only way to see the full 4.5 deg on glass (no API resets the peak); the dial-end clamp halving it is the accepted cut-off. |

| Dyno Cell theme rework: 1.2x arc, Archivo Black readout, centred stack, cap hidden behind the 0 marker (2026-08-12, flashed + measured) | User-driven visual pass on the dyno-cell face: widen the arc, enlarge all text, drop the readout toward the panel centre, use a wider (non-skinny) readout font, give the readout->PSI gap the same whitespace as the zone->readout gap, and stop the arc's edge peeking past the 0 marker. | (1) ARC_WIDTH 45->54 (1.2x) grew the rounded-cap reach to ~(width/2)/center_r = 7.5 deg, so the cap poked ~0.4 deg past the 0 marker's far edge at the old 4.0/3.6 deg gaps (measured full-colour arc pixels to 232.7 deg vs marker edge 233.1). (2) Amazon Ember CdRC is a *condensed* face; even regenerated to 68 px it reads skinny. A 1.3x LVGL `transform_scale_x` widen was tried FIRST and failed the stale-pixel audit on 411/414 frames: LV_LAYER_TYPE_TRANSFORM scale interpolation leaves 1-step AA seams at glyph edges, so the transform approach is REJECTED, not weakened. (3) The readout is top-aligned in its slot (LVGL label), so ink sits above the slot centre; the old -22 offset left it high. (4) PSI/PEAK/DEMO were crammed ~7 px under the readout. | ARC_WIDTH 45->54 (shared by track, value arc, invalidation and zero notch - one define). Readout font -> Archivo Black 56 px (Google Fonts, `main/fonts/archivo_black_56.c`, digits ~30-34 px wide at 56 px); slot pitch 34->37 and slot width 40 for the wider advance; whole readout shifted left 9 px so the decimal sits 1/4 of the ones->decimal gap from centre (ones x=207, decimal x=240, screen centre 233). Vertical stack: readout -4, PSI +26->+55 (readout->PSI ink gap = zone->readout 46 px), PEAK/DEMO keep the original 28 px rhythm (83/111). ZERO_GAP_VAC/BOOST 3.6/4.0 -> 5.0 so the wider cap sits fully behind the 0 marker on both sides. Web mirror updated in lockstep (stroke 54, gaps 5.0, readout decimal at cx+8, PEAK/DEMO 83/111) and assets regenerated. | Sim: dyno-cell audit 0 stale / 0 severe; neon web parity + geom green. Pixel-verified: arc exactly 54 px at 12 o'clock; gaps 46/16/18; 0 arc-coloured pixels beyond the 0 marker in boost AND vacuum renders. Hardware: flashed COM3, 30 s dyno-cell demo cadence soak min 59 / median 62, teTimeouts 0, framesOverBudget 0, worstRenderUs ~15 ms. | Archivo Black is single-weight (400); source TTF is `main/fonts/ArchivoBlack-Regular.ttf`. Do not reintroduce `transform_scale_x` for glyph widening (AA-seam failure above). `main/fonts/AmazonEmberCdRC_Bd.ttf` was left untracked/unused after the switch. Any future readout font change must re-derive pitch/slot width from the generated advance and re-run the dyno-cell audit.
| Companion-app BLE GATT server: boot-loop on first hardware flash, then adv-payload and double-start faults (2026-08-23, flashed + measured) | First flash of the dual-role build (central + `boost_app_ble` peripheral) boot-looped: `Guru Meditation LoadProhibited` at `ble_hs_lock` via `ble_att_set_preferred_mtu` called from `boost_app_ble_init()` BEFORE the host was mounted; EXCVADDR 0x44 (NULL lock). After fixing ordering, a second panic: `ble_att_svr_find_by_uuid` NULL-uuid from `ble_gatts_start()` called a second time in the sync callback (the host's own `ble_hs_start` already calls it, ble_hs.c:695). Third fault: advertising never started, `adv fields failed: 4` (BLE_HS_EMSGSIZE) - flags(3) + complete 128-bit UUID(18) + full name(12) = 33 > 31 legacy adv bytes. | main.c called `boost_app_ble_init()` before the conditional host mount, and the central's init started the host task immediately, leaving no valid window for GATT registration. | Load-bearing ordering, now enforced: `boost_obd_ble_init()` MOUNTS (nimble_port_init, RAM-guarded, task start deferred) -> `boost_app_ble_init()` registers GATT + security config (legal only mounted-not-started; skipped safely if the mount was refused) -> `boost_obd_ble_host_start()` starts the task; `ble_gatts_start()` is NEVER called from app code (host does it pre-sync). Name moved to the scan response (`ble_gap_adv_rsp_set_fields`). `appBle` gates ADVERTISING, not registration, so the runtime toggle never restarts the host; if the host was never mounted at boot, `boost_app_ble_start()` performs mount->register->start on demand. Hardware result: clean boot, zero panics, advertising 160-250 ms, runtime toggle verified, cadence median 62/min 57 with adv+WiFi+display, per-theme fast-slew all >=60, internal free 71 kB largest 59 kB at mount. | The shared NimBLE host has exactly one valid bring-up order: mount -> register -> start. Any new GATT service or host-level config (MTU, security, store) MUST run between mount and `boost_obd_ble_host_start()`; never call `ble_gatts_start()` from app code; never call host APIs before a successful `boost_obd_ble_init()`. The adv payload budget is 31 bytes: 128-bit UUID + flags leaves no room for the name - scan response only. |
| Companion-app hardware acceptance + AP-join field repro (2026-08-23, on v0.8.1-rebased companion branch) | The user's v0.8.1 in-car failure mode ("can't connect to the AP") needed a bench repro. The Mac (Intel, itlwm/HeliPort Wi-Fi) associated with `BoostGauge-5ED5` and was granted a DHCP lease (board log: `DHCP server assigned IP ... 192.168.4.2`), but NO TCP/ICMP data flowed in either direction; an iPhone joining the same AP loaded the full dashboard immediately. Separately, HTTP p50 over STA measured 147 ms with BLE advertising ON vs 16.8 ms OFF (matches the 2026-07-26 spike prediction; the cost is now hardware-quantified on the dual-role build). A reported "graph drew the organic waveform while sweep was selected" was investigated: firmware verified running the constant slew at exactly 9.79 psi/s; the sparkline backfills from `GET /logs?limit=300`, so first load legitimately rendered pre-switch organic ring history. | The board's SoftAP data path is healthy; the Mac's failure is the itlwm/HeliPort userspace stack (association + DHCP work, the BSD interface never passes data frames) - a known OpenIntelWireless softAP weakness, NOT firmware. The mirror lag over the AP is the single-radio cost (STA+AP+BLE adv). | AP-join acceptance on this Mac is `manual`: join via HeliPort GUI with a static IP (192.168.4.2/24 gw 192.168.4.1) and verify from a PHONE (native stack) - CoreWLAN/networksetup see no interface and cannot join or diagnose. `tools/check_hardware_gates.py` ap-join gate documents this. Service-order fix for internet-while-on-AP: System Settings > Network > Set Service Order, Ethernet above Wi-Fi. The graph "desync" class: before reporting a waveform bug, check whether the sparkline is showing ring HISTORY spanning a waveform switch (`GET /logs` backfill) - sample live psi slew first (`/state` at 4 Hz, ~9.79 psi/s = sweep). |
| Physical-iPhone companion BLE E2E gate and GATT sizing/race fixes (2026-08-24, flashed + 3/3 hardware runs) | The Intel NUC8 Mac usually saw no gauge advertisements after its first CoreBluetooth scan session even though gauge serial showed continuous advertising and the iPhone discovered it immediately. A controller power cycle re-armed at most the next scan. Separately, the Mac harness could stop on the first arbitrary advertisement (the nearby JetKVM) before accepting the gauge. Once a physical iPhone reached the matrix, firmware failures included a 4 KiB NimBLE host stack overflow, response notifications attempted before Control subscription readiness, oversized full-state responses, Status read/notify contention, and an unbounded Log value. | Two independent layers were involved: the Mac Intel/CoreBluetooth stack was not a repeatable physical central, and the first-random-device callback was a real harness filter bug. On the device, the full request path consumed more stack than the prior host allocation; cached notification readiness survived at the wrong lifetime; the LAN `/state` and one-hour log shapes exceeded the bounded ATT contract; and the periodic Status notify could overlap a direct read. | `tools/check_ble_ios_e2e.sh` makes the Mac orchestrate a tethered physical iPhone through Xcode/XCTest, preserving the bond and running the complete request/read matrix three times. Firmware uses an 8 KiB NimBLE host stack and 6 KiB companion-driver stack; Control waits for live notify readiness, `GET /state` is a compact <=480-byte response, Status is bounded, the iOS client quiesces Status subscription around a forced read, and Log returns the latest eight `BGL1` samples. The accepted 3/3 artifacts are `/tmp/boost-gauge-ble-ios-e2e-20260824-191341-51420`; saved HTTP config reports `appBle:true`, serial showed advertising plus `control write: <N> B` request traffic. | Companion BLE acceptance is `bash tools/check_ble_ios_e2e.sh` on a paired tethered physical iPhone, with 3/3 required and the `.xcresult` artifacts retained. Before the run, HTTP must answer with `appBle:true` and serial must show advertising; during it, serial Control-write lines must prove firmware traffic. Do not reduce the 8 KiB host or 6 KiB companion-driver stacks, expand Control beyond 480 bytes, restore full HTTP state/full ring on ATT, allow Status notify/read races, uninstall the app, or erase the bond as routine setup without repeating the physical gate. Mac Intel CoreBluetooth is diagnostic-only on this host. An Android emulator is UI/build coverage only; Android hardware BLE acceptance requires a physical device. |
| Native companion reconnect, authoritative refresh, history, and theme-preview UX (2026-08-24) | Both native apps exposed Disconnect without a usable BLE link, required a fresh scan after reopening, and could render placeholder Status/Settings values until a manual refresh or tab round-trip. iOS BLE Status omitted the firmware field even though DeviceInfo carried it. Logs looked like unexplained isolated readings, while Themes showed bland rows without the configured face. Initial Android acceptance also saw no gauge while iPhone was connected, then returned 404 after pairing because relative app routes were sent unchanged over GATT. | Connection state and the selected peer were not consistently persisted/restored; page entry did not always replace drafts with authoritative responses; iOS did not fold DeviceInfo firmware into Status; and the log/theme views did not explain or visualize the data they already received. Android's first canonical WebView pass collapsed its relocated gauge to zero CSS height; the attempted raw-pixel repair double-scaled by the 1.5 display density. iOS Status depended too heavily on entry/notify events, and requesting all 18,000 log rows before publishing anything left the graph apparently empty. | iOS persists the peripheral UUID and reconnects through CoreBluetooth retrieval; Android persists address/name and reconnects its selected transport. Disconnect is conditional on an active/pending BLE link. Status refreshes authoritatively at 1 Hz and Settings reloads on entry/connection; iOS uses DeviceInfo as the BLE firmware fallback. Both apps use the canonical offline `web/app.js` 466×466 renderer for Themes and TPMS. Android measures the WebView, converts physical pixels to CSS pixels before drawing, keeps a square face, and removes the duplicate native tire row. iOS Logs publishes 300 HTTP samples promptly, then replaces them with the full 18,000-sample history; a BLE session uses the saved HTTP host when reachable and otherwise labels its bounded BGL1 window explicitly. | Never accept a packaged renderer from build evidence alone: install it, wait at least 10 seconds, leave/return to the tab, and inspect a screenshot for a nonblank, uncropped complete face. Keep renderer dimensions in CSS pixels, not Android physical pixels. Never block first paint on the one-hour log response; publish the recent window, then replace it with the full result and label scope/count. Evidence: iOS screenshots `/tmp/ios-themes-sim2.png`, `/tmp/ios-status-before.png`, `/tmp/ios-status-t3.png`, `/tmp/boost-ios-logs-populated.png`, `/tmp/ios-logs-full-wait.png`; Android physical screenshots `/tmp/android-themes-canonical-square-11s.png` and `/tmp/android-status-tpms-canonical-square-11s.png`. Android 32 tests/build passed and APK was physically installed; iOS unit/canvas tests passed and the signed app was physically installed. BLE matrices remain 3/3 at `/tmp/boost-gauge-ble-ios-e2e-20260824-204958-76137` and `/tmp/boost-gauge-ble-android-e2e-20260824-211407-81521`. |
| Companion-app BLE enrichment: full /themes + /state over Control, device-info IP, physical gate re-run 3/3 (2026-08-25, flashed) | BLE mode rendered a sparse companion UI: the Themes editor showed only id/name/style (no palette colors or theme-config fields), Status lacked tpms/sensors/display, and Logs graphed a flat 2-8 point line. Root cause: the firmware BLE surface was deliberately bounded — Control responses capped at 480 B, `/themes` GET returned id/name/style only, `/state` + Status char returned a compact shape, `/themes/config` PUT ignored `neonFont` and echoed `{"ok":true}`, and the Log characteristic was hard-capped at 8 samples (APP_LOG_MAX_SAMPLES) because the 16-bit ATT Read-Blob offset cannot address past 64 KB. The full one-hour ring was only ever served over HTTP `/logs`. | The prior bounded-ATT design traded fidelity for the 480-byte Control cap; the companion apps consumed the same JSON shapes over HTTP and BLE, so the sparsity was a firmware-side contract gap, not an app bug. The Status notify/read contention on iOS (read starved by the 1 Hz full-state notification stream) added a client-side constraint. | Firmware: `APP_BLE_CTRL_RESP_MAX 4096u` (replaces the 480-byte cap); the Control route handler heap-allocates its response buffer; `app_themes_json` emits the full HTTP `/themes` mirror (all 8 palette roles, customized, every theme-config field incl. neonFont); `app_status_json` emits the full `/state` mirror (tpms/sensors/display/obd/epochMs/firmwareVersion); `route_state` uses it; `/themes/config` PUT parses `neonFont` and echoes the full themes payload; fragment send (`app_notify_fragmented`, chunk = MTU-3) already handled >MTU responses; Status char keeps the full state at 1 Hz (subscriber-gated); device-info JSON gains the STA `ip` so BLE-only clients can derive the HTTP host and pull the full one-hour ring (`boost_app_ble_set_sta_ip()`, called from `IP_EVENT_STA_GOT_IP`). iOS: BleTransport reassembles fragmented Control responses, does NOT subscribe to the Status char (live state = 1 Hz Control `/state` poll, mirroring HTTP), `readDeviceInfo` parses `ip`, and the Logs view builds an HTTP history transport from that IP to fetch the full 18,000-sample ring. Android: mirrors the no-status-subscription + `/state` poll design; `HardwareBleE2ETest` full matrix **3/3 PASSED** on the physical device (2026-08-25) after a one-time `svc bluetooth` toggle cleared a stale link-layer state that produced `GATT error 133` connection-establishment failures (the board saw no connect attempt, iPhone passed 3/3 in the same window). | Hardware: firmware flashed to the bench board; iOS `HardwareBleE2ETests` on a physical iPhone passed the full BLE matrix 3/3 (12.6-18.5 s each, 0 failures) asserting tpms.wheels==4, sensors/display presence, all 8 palette colors, neonFont, vaultVignette, pixelShiftSec — plus a Themes-editor-over-BLE UI check that expands Dyno Cell and finds the vacuum palette color well. Android `HardwareBleE2ETest` ran FAILED once pre-fix (link dropped on Status read/notify contention, the same class the iOS fix removes); post-fix compile/unit tests pass, device E2E must be re-run when the phone is reconnected. Board survived two clean serial-watched boots past the 60 s mark with no panic/watchdog/brownout. Final hardware verification (2026-08-25): iOS `HardwareBleE2ETests` **5/5 PASS on a physical iPhone** — matrix incl. `readDeviceInfoIP` (device-info carries `ip`) plus the Themes-editor-over-BLE and Logs-full-hour (`Full HTTP history · N samples`) UI checks; Android `HardwareBleE2ETest` **3/3 PASS** on the physical device (a one-time `svc bluetooth` toggle cleared a stale link-layer `GATT error 133`; board serial saw no connect attempt during those failures). Two firmware bugs found and fixed en route: `boost_app_ble_init()` ran AFTER the STA GOT_IP setter and its NULL rebuild clobbered the stored ip (now persisted in `s_ble_sta_ip` so any rebuild retains it), and the device-info snprintf format was missing the closing quote after the ip (`..."ip":"192.168.50.102}` — invalid JSON, iOS parse failed; now built as one `,"ip":"%s"` part). The Logs full-hour fetch also needed the `/logs` perf fix (see the row above) and a detached/retry history task so view-lifetime cancellation can't kill the fetch. | Control responses may exceed 480 B (now 4096, fragmented; clients reassemble end-to-end). Any further expansion still requires re-running the physical iOS BLE gate 3/3 (`bash tools/check_ble_ios_e2e.sh`). The iOS BLE live-state path is a 1 Hz Control `/state` poll, NOT the Status notification stream (subscription removed to end the read/notify contention; Status remains as a legacy broadcast). BLE Log stays an 8-sample diagnostic window by ATT design — the one-hour ring is HTTP-only; a BLE-only client needs the device-info `ip` to build the HTTP host. Never restore the 480-byte cap or the compact `/themes`/`/state` shapes without a companion-app UI acceptance.
| HTTP `/logs` full-ring response: per-sample chunks were 16 s for ~3.7 k samples (2026-08-25, flashed + measured) | The companion Logs graph pulls the full one-hour ring over HTTP (`/logs?limit=18000`). On hardware the response was catastrophically slow — 16.02 s for a 253 KB / 3,706-sample response (≈ 4.3 ms/sample), extrapolating to ~78 s for a full 18,000-sample ring — which made the BLE-mode full-history fetch time out/cancel intermittently and the Logs tab visibly stall. Root cause: `logs_get` emitted **one `httpd_resp_sendstr_chunk` per sample** (18,000 separate framed HTTP sends). | `boost_model_copy_logs` copies under the ring mutex then the handler serialized row-by-row. | `logs_get` now builds the whole `{"samples":[...]}` body into a PSRAM heap buffer (cap = n×128+32) and sends it with a single `httpd_resp_send`; if the buffer alloc fails it falls back to the old per-row chunk path (correct, slow). | Host: `curl /logs?limit=18000` on the bench board: **16.02 s → 0.150 s** (single response, valid JSON, ring samples intact). Serial boot clean, no errors. This is a transfer-encoding change (chunked → Content-Length); URLSession and curl both consume it. | Never reintroduce per-sample HTTP chunks for `/logs` (or any bulk endpoint): a full-ring response must be one buffered body. The 18,000-sample ring response is ~1.15 MB; keep the PSRAM allocation and the chunked fallback.
| Companion UI declutter + BLE-only transport UX + full-hour logs on Android over BLE (2026-08-25, both apps sim/emulator-verified) | User round: (1) Status/Dashboard still showed a redundant Boost/TPMS page switcher though both render on one page; (2) OBD2 card said "Enable tpmsBle" even when the setting was already on (no adapter present); (3) iOS Themes preview WebView leaked the web dashboard's page toggle on scroll and could scroll; (4) cramped theme-option spacing; (5) non-editable Face/Track/Text/Muted palette rows were noise; (6) 8 color dots per theme row vs the web UI's few; (7) iOS Logs graph stroked 18k points into ~400 px → the stroke filled the min-max envelope as a solid "ocean" block, every sample was listed below (18k rows, unusable), and labels said "HTTP history" while the user wants a Bluetooth-only app (HTTP config UI removed; the invisible LAN full-history fetch stays). Android additionally plotted only `takeLast(300)`. | iOS GaugeMirrorWebView's crop CSS let `.gauge-wrap` children other than `.gauge-device` render (the page toggle lived there); the chart had no per-pixel downsampling; Android's `GaugeApi.getLogs` over BLE only read the 8-sample BGL1 characteristic, so BLE hardware users would still get an 8-point graph. | iOS: crop hides `.gauge-wrap > *` except `.gauge-device`; LogPressureChart downsamples to per-column min/max with a short envelope smooth (pixel-verified line, not a block); page picker/`setPage` removed; OBD message conditional on persisted `tpmsBle`; zone-only palette (3 dots, editable pickers only); Settings is BLE-only (HTTP picker/host field removed; AppSession internal host machinery kept for the invisible fetch). Android: page tile removed; OBD message conditional; ColorSwatches → 3 zone colors; spacing +12 dp; HistoryGraph plots the whole loaded ring downsampled per pixel column; sample list removed; labels de-HTTPed; Settings BLE-only. Android `GaugeApi.getLogs` on BLE now reads device-info `ip` and pulls the full ring over HTTP invisibly, silently falling back to the BGL1 window with no LAN (BleGaugeTransport gained a default `readDeviceInfo`). | iOS: 57 unit tests + 3 sim acceptance tests pass; screenshots 01-05 (no toggle, Zone colors only, 3 dots, line graph with empty interior, no sample list/no HTTP strings). Android: compileDebugKotlin + testDebugUnitTest green; emulator screenshots 01-05 (no Page tile, both OBD branches, BLE-only Settings, 3 dots, line graph max 19.4% horizontal coverage). The Android BLE full-ring path is unit-compile-verified only — NOT yet hardware-verified (needs a phone run). | The theme previews are OFFLINE (bundled web assets; loadHTMLString / WebViewAssetLoader style) — they must keep working with no network, that is the in-car contract. Do not reintroduce per-sample chart points without per-column downsampling (measured fill failure). Do not reintroduce HTTP transport UI; HTTP remains internal-only plumbing for the LAN full-history fetch. Re-run the physical BLE E2Es (iOS HardwareBleE2ETests, Android HardwareBleE2ETest) after these UI changes before release.
| Companion round 3: circular bezel preview, timezone-only clock sync, settings sub-pages, native Android TPMS cards, iOS 26 tab-bar clearance (2026-08-25, sim/emulator + hardware-verified firmware) | User round: theme previews rendered as black squares (ugly in light mode; black-face themes blended into the page), the preview circle was clipped top/bottom with a harsh light-mode shadow, clock sync sent the phone epoch when the DS3231 RTC must stay the time authority, flat Settings pages had outgrown one level, Android still drew TPMS as the drivetrain PNG, and the Logs export button wrapped three lines. Separately, on iOS 26 the floating tab bar rode over list bottoms. | GaugeMirrorWebView was framed as a square; the first bezel attempt put `aspectRatio` on a ZStack containing a WKWebView (ambiguous sizing → vertical clipping) plus an offset shadow that reads harsh on light pages; `/time` required `epochMs`; lists under the iOS 26 floating tab bar lacked bottom scroll clearance. | Preview: `aspectRatio` directly on the WebView, `.clipShape(Circle())`, concentric bezel strokes in `.background` (8 px #0c0e12 pod ring + hairline), no offset shadow, generous row padding. Firmware: `/time` accepts a timezone-only body (`{"timezoneOffsetMinutes","timezoneTz"}` without `epochMs`) via new `boost_model_set_timezone()` — config+state update only, RTC never touched; full-epoch form unchanged for the web UI (both hardware-verified 200/400). Apps: sync buttons send timezone only (+ curated POSIX TZ dropdowns with Custom); iOS Settings reorganized into sub-pages with sensor data moved to Calibrate (mirroring Android); Android TPMS = native 2×2 tire capsules (valid/low/invalid states); single-line Export CSV; both apps' scrolling pages get `.contentMargins(.bottom)` clearance. Views migrated `NavigationView`→`NavigationStack`, deployment target 15.0→17.0 (contentMargins; devices run iOS 26). | Firmware: tz-only POST 200 (state reflects zone), epoch POST 200, missing-tz 400 on the bench board. iOS: 61 unit tests + 8/8 SimAcceptanceUITests pass — incl. new `testThemesListScrollsClearOfFloatingTabBar` (last row scrolls above the bar, frame-intersection assert) and big-digit bezel screenshot test; Gemini visual QA confirmed the circular bezel renders correctly light+dark after two FAIL rounds caught the clipping and shadow. Android: 42 unit tests green; emulator screenshots show TPMS capsules (valid/amber/invalid), one-line Export CSV, sub-page menu + timezone dropdown. Android's flagged "firmware contract risk" is stale — it read the release checkout's boost_web.c; the companion repo has the change and the flashed board verifies it. | The gauge preview is a CIRCLE with the web `.gauge-device` bezel — never a bare black square, and never sized via aspectRatio on a ZStack wrapping a WKWebView. The app NEVER sends phone epoch to `/time`; timezone-only is the only app-side sync (RTC keeps time). Lazy Lists materialize off-screen rows late: UITests must swipe until an element EXISTS before asserting hittability. Watch-all-wheels when asserting rotating low-pressure states. Re-run physical BLE E2Es before release.
| Android companion round 6: transport remnant cleanup + BLE reconnect + foreground service (2026-08-26, emulator-5554 simBle + host: 66 unit tests green, compileDebugKotlin 15 executed + testDebugUnitTest 23 executed, 3 Connection screenshots to /tmp/boostgauge-shots/android-round6-{live,disconnected,reconnecting}.png, Gemini QA PASS) | (1) Stale HTTP transport auto-connected at startup to 192.168.4.1 while scanning BLE, surfacing "HTTP request failed to connect" banner; (2) BLE gave up after 5 retries ("disconnected after 5 retries") and never retried; serial showed repeated "phone disconnected (reason 531)" HCI 0x13 REMOTE USER TERMINATED — phone closed link, not gauge — combined with 5-attempt/~5s ladder, background suspension stalled GATT and app tore link down; no foreground service | (1) TransportController.restore fell back to HTTP when BLE blank and SettingsStore default was HTTP 192.168.4.1 SoftAP, HttpTransport fallback hardcoded same address; (2) BleTransport RETRY_DELAYS_MS 0,200,800,1500,2500 then gave up, no indefinite reconnect, and no foreground service so screen-off suspended GATT traffic through the window | (1) Bluetooth-first: SettingsStore default BLE empty, TransportController never restores HTTP, migrates persisted HTTP→BLE empty and persists, HttpTransport empty host now throws, HTTP banners never surface over BLE; (2) GaugeRepository exponential backoff 1→2→5→10→30 cap 60s indefinite, "Reconnecting… (attempt N)" while retrying, Disconnected only pre-first-connection, plus foreground service (foregroundServiceType connectedDevice, POST_NOTIFICATIONS for API 33+, started on BLE connect, stopped on explicit disconnect), per-request 5-attempt ladder retained as guard; iOS parity noted: iOS caps at single reconnect at launch (reconnectSavedBLE) plus no auto-retry on link loss, Android now diverges to indefinite per explicit FIX, documented here | Bluetooth-first: HTTP never the active transport, 192.168.4.1 not user-visible; BLE reconnect is indefinite with backoff 1/2/5/10/30/60s and attempt UI, foreground service holds GATT while connected, HTTP banner never surfaces over BLE; re-verify with /tmp/boostgauge-shots and unit tests for migration/backoff, note iOS divergence (single attempt vs indefinite) |
| Companion BLE hardening round: BLE /logs + /network routes, CCCD resubscribe recovery, OBD-scan coex gate, Android stale-bond recovery, theme-preview reveal fix, per-call BLE timeouts (2026-08-28, flashed + hardware-verified on iOS + Android) | Companion round: (1) Logs page empty then "no samples" — the BLE Control /logs route returned only `{"count":N}`; first fix attempt (verbose 42-pt window) aliased the 9.789 psi/s sweep into staircase pulses; a second attempt (APP_BLE_CTRL_RESP_MAX 8192 + a 4 KB stack buffer in the async driver-task handler) caused a boot-loop stack overflow and, earlier, a LoadProhibited panic at host-sync from doubled 8 KB control mallocs under Wi-Fi+LVGL DMA pressure; (2) Settings showed a recurring "device not found"/not-in-range toast and Wi-Fi status never reflected the real STA state because GET/PUT/DELETE /network had no BLE Control routes; (3) theme preview froze on the previous face after selecting a new theme; (4) after any board reboot, iOS Logs intermittently failed with "The device did not respond" — firmware serial instrumentation proved the request ARRIVED and the response was built (3.4 KB in ~5 ms) and fragmented, but iOS never received it; (5) Android could never reconnect after firmware reflashes: board logged `encryption changed status 13` (PIN/KEY_MISSING) every attempt — the phone kept encrypting with an LTK the board lost across reflashes; (6) enabling the OBD2 BLE link re-introduced intermittent Logs timeouts; (7) switching log windows took 10–30 s (BLE 10 s timeout × retry cascade re-sending the same request). | (1) The /logs stub predated real data; (2) the Wi-Fi page was designed HTTP-first; (3) GaugeMirrorWebView's reveal gate bumped renderToken on every same-theme updateUIView pass and its 40×50 ms poll + +400/+1200 ms rescue re-renders only ran at page finish; (4) a board reboot resets the firmware's RAM CCCD state while CoreBluetooth keeps its subscription "active" and never re-issues setNotifyValue on auto-reconnect — responses silently vanished; (5) Android's stack caches the stale bond keys through BT toggles (dumpsys shows no bond yet encryption is attempted with the dead LTK), and attemptBond() skipped createBond when bondState read BONDED mid-churn; (6) the OBD central's 3 s active scan bursts starved the peripheral notification path mid-fragment; (7) send() armed a 10 s per-attempt timeout with a 4-step retry ladder for a firmware route that answers in <10 ms. | Firmware (`boost_app_ble.c`): /logs returns a bounded compact window `{"tMs","psi"}` (~22 B/sample) decimated EVENLY across the requested ?limit= (128 pts at cap/32; verbose was 42 at cap/96 — 42-pt point-sampling undersampled the 60-triangle 5 m sweep at 0.7 pts/triangle and aliased); GET /logs moved OFF the NimBLE host task to the driver task (APP_EV_LOGS) with a HEAP body (a 4 KB stack buffer there boot-looped); GET/PUT/DELETE /network + GET /network/scan + POST /network/reconnect added mirroring the HTTP shapes (scan async on the driver task via APP_EV_SCAN); APP_BLE_CTRL_RESP_MAX stays 4096 (8192 panicked — internal DMA/heap pressure with Wi-Fi+LVGL). OBD central (`boost_obd_ble.c`): the scan-retry loop postpones new scan bursts while `boost_app_ble_connected()` (re-queues every 3 s) — scan bursts were eating peripheral notifications mid-fragment; a stored-peer direct connect and a real scan hit still go through immediately, so the in-car adapter link is unaffected. iOS: `BleTransport.send()` gained per-call `timeout:maxRetries:` (all legacy call sites keep 10 s/4 retries; /logs uses 20 s/1) and re-subscribes Control notifications on EVERY write/timeout failure even with retries disabled (the CCCD recovery — idempotent); LogsViewModel publishes cached samples for the target window BEFORE the fetch (stale-while-revalidate) so chip switches repaint instantly; GaugeMirrorWebView takes an explicit `themeID` change signal, keys reveal gating on the REQUESTED key (not revealedKey), and re-arms the +400/+1200 ms rescue re-renders on every theme switch. Android: `BleTransport.connect()` verifies the encrypted link before the CCCD write and on insufficiency/failure removes the stale bond (reflection removeBond), re-bonds fresh, and retries the CCCD write exactly once (BondOperations seam, unit-tested). | Hardware: three consecutive LogsWindowsHardwareUITests passes on a physical iPhone over pure BLE cycling 5m→1m→15m→5m with `Last X · 128 samples` each and the link Connected throughout — first with OBD off, then 2/2 and a third at full speed with OBD BLE enabled; firmware serial shows every /logs built in 3.5–5 ms; ThemeCycleHardwareUITests cycled all five themes over BLE on the board (preview label updated per theme, no reboot, no disconnect); LogsHardwareUITests `Last 5 minutes · 128 samples` + still connected; WifiScanHardwareUITests scan rows over BLE; Android stale-bond fix verified on the Pixel: removeBond → fresh pairing → `encryption changed status 0` + continuous 1 Hz state writes ≥60 s, 92/92 unit tests; host suite 11/11 throughout. | APP_BLE_CTRL_RESP_MAX is 4096 — never raise it without re-verifying Wi-Fi+LVGL DMA pressure (8192 panicked twice, two different signatures). Any blocking route (logs build, Wi-Fi scan, calibration, time) runs on the driver task via an APP_EV_* event with HEAP buffers, never inline on the NimBLE host and never on the driver stack. iOS recovers a rebooted board's lost CCCD only via the resubscribe-on-failure path: the first request after a board reboot eats one timeout (~20 s on /logs) — do not remove the resubscribe. Android requires the stale-bond removeBond/re-bond recovery; never "simplify" connect() back to pre-gatt bonding only. OBD scan bursts defer while a companion client is connected; if in-car logs still stall with a live adapter, gate is scan-only by design — do not extend the gate to established OBD links without measurement. BLE logs stay a bounded 128-point compact window (staircase-free at ~2 pts/triangle; finer needs binary paging, not bigger JSON). |
