ZiadAbdelati/waveshare-boost-gauge/preview/sim/gauge_sheet.png

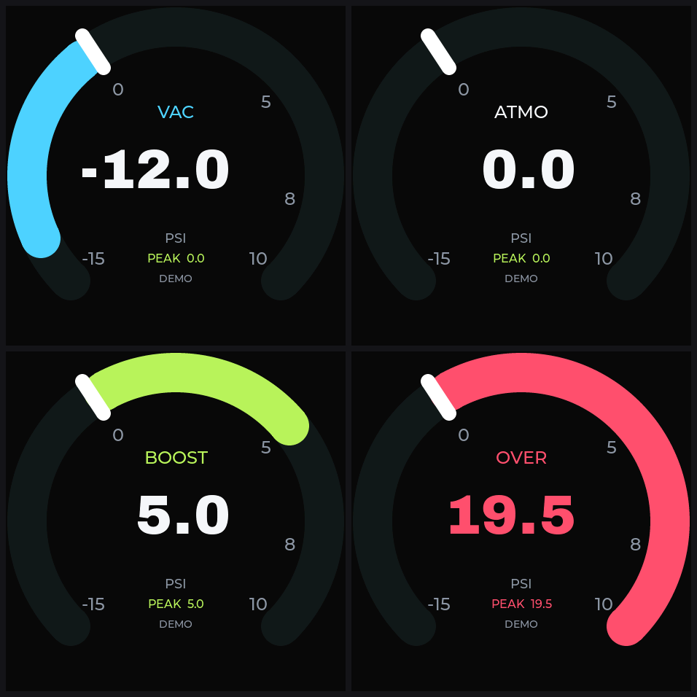
preview/sim/gauge_sheet.png
