ZiadAbdelati/waveshare-boost-gauge/preview/sim/gauge_sweep.gif

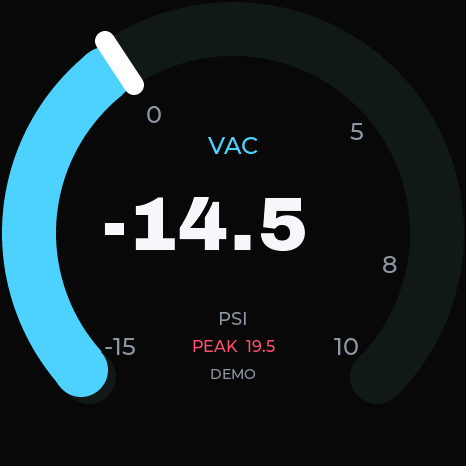
preview/sim/gauge_sweep.gif
