ZiadAbdelati/waveshare-boost-gauge/preview/sim/zero_join_vac.png

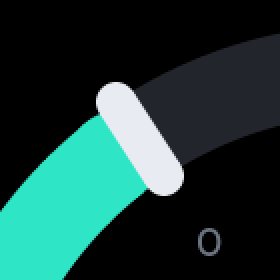
preview/sim/zero_join_vac.png
