ZiadAbdelati/waveshare-boost-gauge/web/tpms_powertrain.png

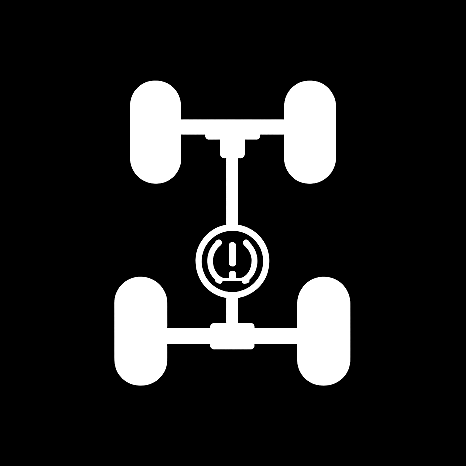
web/tpms_powertrain.png
