ZiadAbdelati/waveshare-boost-gauge/main/boost_gauge.c

#include "boost_gauge.h"

#include <math.h>
#include <stddef.h>
#include <stdint.h>
#include <limits.h>
#include <stdio.h>
#include <stdlib.h>
#include <string.h>
#include <time.h>

#ifdef ESP_PLATFORM
#include "freertos/FreeRTOS.h"
#include "esp_log.h"
#include "esp_timer.h"
#include "boost_media_store.h"
#include "esp_heap_caps.h"
#include "esp_memory_utils.h"
#else
#define ESP_LOGI(tag, fmt, ...) printf("[I][%s] " fmt "\n", tag, ##__VA_ARGS__)
#define ESP_LOGW(tag, fmt, ...) printf("[W][%s] " fmt "\n", tag, ##__VA_ARGS__)
#define ESP_LOGE(tag, fmt, ...) printf("[E][%s] " fmt "\n", tag, ##__VA_ARGS__)
#endif

static double neon_now_ms(void)
{
#ifdef ESP_PLATFORM
    return (double)esp_timer_get_time() / 1000.0;
#else
    return (double)clock() * 1000.0 / (double)CLOCKS_PER_SEC;
#endif
}
#include "lvgl.h"
#include "boost_brightness.h"
#include "boost_neon_geom.h"
#ifdef ESP_PLATFORM
#include "boost_model.h"
#include "boost_display.h"
#include "boost_sensors.h"
#else
static inline void boost_display_gauge_update_begin(void) {}
static inline void boost_display_gauge_update_end(void) {}
#endif
#if LV_USE_GIF
#include "gif/boost_gif.h"
#endif

/* The cached face lives in PSRAM on device, plain heap on the simulator. */
#ifdef ESP_PLATFORM
#define BG_ALLOC(n) heap_caps_malloc((n), MALLOC_CAP_SPIRAM | MALLOC_CAP_8BIT)
#define BG_FREE(p)  heap_caps_free(p)
#else
#define BG_ALLOC(n) malloc(n)
#define BG_FREE(p)  free(p)
#endif

#ifndef M_PI
#define M_PI 3.14159265358979323846
#endif

/*
 * Multi-style gauge face.
 * ----------------------
 * A theme selects a `style`, and each style is a separate LVGL scene with its
 * own build/update/teardown. Changing theme tears the scene down and rebuilds
 * it. Only the moving parts invalidate per frame; static art (ticks, chevrons,
 * scanlines) is drawn by a face object that LVGL clips to the dirty region.
 *
 * The `arc` style is the original verified face and is preserved byte-for-byte
 * in its geometry/invalidation logic â€” it is the one gated by the 60 FPS
 * hardware cadence guard.
 */

#define COLOR_VOID   0x000000
#define FACE_BG      COLOR_VOID

#define DEFAULT_PSI_MIN       (-15.0f)
#define DEFAULT_PSI_MAX       (10.0f)
#define DEFAULT_PSI_OVERBOOST (8.0f)
#define DEFAULT_ZERO_ANGLE    236.25f
#define ARC_START     135
#define ARC_END       45
#define ARC_RANGE     270

#define DISP_SIZE     466
#define ARC_DIAMETER  462
#define ARC_WIDTH     54
#define ZERO_LINE_W   20
/* The arc's rounded caps extend ~(width/2)/center_r = 7.5 deg past the nominal
 * span. The 0 marker only covers +-~2.5 deg, so the 45 px-era gaps (4.0/3.6)
 * let the wider 54 px arc's cap poke ~0.4 deg past the marker's far edge.
 * Raised to 5.0 so the cap sits fully behind the marker again on both sides. */
#define ZERO_GAP_VAC_DEG   5.00f
#define ZERO_GAP_BOOST_DEG 5.00f
#define TICK_FONT     (&lv_font_montserrat_24)
#define TICK_RADIUS   160.0f
#define VALUE_SLOT_HEIGHT  58
/* Archivo Black (Google Fonts, single weight) is a wide heavy display face,
 * so the readout needs no size hack to stop looking skinny. At 65 px its digit
 * advance is ~43 px and the widest glyph box is 41 px; the integer pitch below
 * is 43 and the fractional pitch 36. */
#define VALUE_SIGN_X_ONE  (-59)   /* minus directly left of a single left-of-decimal digit */
#define VALUE_SIGN_X_TWO  (-102)  /* ... or of the tens digit when there are two */
#define VALUE_TENS_X       (-70)
#define VALUE_ONES_X       (-27)
#define VALUE_DECIMAL_X    9
#define VALUE_TENTHS_X     45
#define VALUE_READOUT_Y    6      /* readout slot centre (moved up 10 px from 16) */
/* Arc readout cells. s_arc_slot_text[] indexes these; the sign's x is dynamic
 * (it hugs the tens digit when the tens cell is occupied). */
enum {
    ARC_SLOT_SIGN = 0,
    ARC_SLOT_TENS,
    ARC_SLOT_ONES,
    ARC_SLOT_DEC,
    ARC_SLOT_TENTHS,
    ARC_SLOT_COUNT,
};
/* Top of the readout's line box, face-local: the old label objects were
 * VALUE_SLOT_HEIGHT-tall boxes centred at VALUE_READOUT_Y, and label ink
 * starts at the box top. Kept so the custom-draw readout lands byte-identically. */
#define ARC_READOUT_LINE_TOP (VALUE_READOUT_Y - VALUE_SLOT_HEIGHT / 2)
/* Container bounds that cover every cell's ink box (+AA margin); a tighter box
 * would let lv_obj_invalidate_area() clip the sign cell's far edge. */
#define ARC_READOUT_W 230
#define ARC_READOUT_H 66
#define WELL_SIZE     DISP_SIZE

/*
 * AMOLED burn-in countermeasure.
 * -----------------------------
 * One face is shown for hours at a time at 85-92% brightness with high-contrast
 * art pinned to fixed pixels â€” tick rings, "VAULT-TEC", reticle brackets, the
 * readout outline. Blue emitters age fastest, then green, then red, so those
 * shapes are exactly what would ghost. The whole scene therefore hangs off a
 * single container (`s_root`) that is nudged a pixel or two every so often,
 * which spreads each static edge over four columns and four rows.
 *
 * Range is [-2, +1], not a symmetric +/-3. The outermost art is drawn at an
 * OUTER radius of 231 about (233,233) on a 466 px panel (lv_draw_arc takes
 * `radius` as the outer edge), so it already reaches column 464 and row 464:
 * exactly one free pixel to the right/bottom and two to the left/top. A wider
 * excursion clips the vault bezel ring and the dyno-cell value arc against the
 * glass, which is far more visible than the aging it would have prevented.
 * Verified extents at full deflection: value arc 0..465, vault bezel 0..465,
 * vault ticks 7..458, hud ring 37..440. Nothing leaves the panel.
 *
 * The offsets walk a ring rather than a raster so consecutive steps are never
 * more than ~1.4 px apart, and so the sequence never dwells near one place.
 * Every dy in {-2,-1,0,1} appears, which is also every phase of the vault's
 * 4-row scanline overlay â€” without that the three rows between scanlines would
 * carry full duty forever and burn in as stripes.
 */
#define PXSHIFT_MIN         (-2)
#define PXSHIFT_MAX         (1)
static const int8_t k_pxshift[][2] = {
    {  0,  0 }, {  1, -1 }, {  1, -2 }, {  0, -2 },
    { -1, -2 }, { -2, -1 }, { -2,  0 }, { -1,  1 },
};
#define PXSHIFT_STEPS (sizeof(k_pxshift) / sizeof(k_pxshift[0]))

/* 90 s a step, so the eight-step ring closes in 12 minutes. Minutes, not
 * seconds: a step is a full-screen repaint, and one of those per minute is a
 * rounding error against the frame budget while still being far faster than
 * emitter aging. */
/* Period is user-set (settings page -> Display -> Pixel shift); see
 * BOOST_PXSHIFT_SEC_* in boost_theme.h for the range and the default. Read
 * per tick rather than cached, so a change over the API takes effect on the
 * next sample without a scene rebuild. */
/* A step dirties all 217k pixels â€” about 45 ms, three dropped frames. Held
 * back until the reading has been steady for a moment so the hitch lands where
 * nothing is moving; mid-sweep it would read as a stutter in the needle. */
#define PXSHIFT_SETTLE_MS   1500u
/* Above the signal's own noise floor. At 0.25 this never released: the demo
 * source alone carries 0.18 sin(17.3t) + 0.08 sin(31.1t), up to 0.52 psi
 * peak-to-peak, so the longest window inside +/-0.25 psi is 0.69 s against a
 * 1.5 s requirement - the gate passed 0.0000% of the time and every shift fell
 * through to the deadline, mid-sweep, which is exactly what it exists to
 * avoid. A real MAP sensor is noisier still. */
#define PXSHIFT_SETTLE_PSI  0.60f
/* ...but a signal that never settles must not starve the shift forever. */
/* A fixed grace, not a multiple of the period: the period is the user's own
 * choice now, and "every 90 s" that can silently mean every six minutes is
 * not the setting they asked for. 30 s is long enough to catch an idle
 * moment in ordinary driving and short enough that the worst case is still
 * recognisably the interval on the label. */
#define PXSHIFT_GRACE_MS    30000u

/* LVGL angles: 0 = east, clockwise (y down). Top of the face is 270. */
#define VAULT_A0   152.0f   /* 270 - 118 */
#define VAULT_A1   388.0f   /* 270 + 118 */
/* Dial pushed out toward the bezel; the needle stops short of the tick ring so
 * the two never share a dirty region. */
#define VAULT_TICK_OUT       224
#define VAULT_TICK_MAJOR_IN  194
#define VAULT_TICK_MINOR_IN  206
#define VAULT_NUM_R          170.0f
#define VAULT_NEEDLE_LEN     168
/* Optional counterweight geometry. The persisted theme preference resolves this
 * to either 0 or 26 px; draw and invalidation must always use the same value. */
#define VAULT_NEEDLE_TAIL_LEN 26
#define VAULT_NEEDLE_HALFW   7
/* Tapered-wedge tip half-width, shared by the draw (triangle tips) and the
 * invalidation (per-slice pad) so the two can never drift apart. */
#define VAULT_NEEDLE_TIP_HALF 2.5f
#define VAULT_HUB_R          15
/* Sits just inside the bezel ring (r=231, width 3, so its inner edge is at
 * 229.5): the tell-tale must stop where the green circle starts, not cross it. */
#define VAULT_PEAK_R         220
/* Size of the peak tell-tale's LVGL object box. The drawn triangle's vertices
 * sit at +-8 px along the radial axis and +-7.5 px tangential, so the ink's
 * furthest corner is sqrt(8^2 + 7.5^2) ~= 10.97 px from the centre (~22 px
 * across); with AA that needs at most ~24 px. The box was 34x34 for years,
 * flushing ~34x34 = 1156 px whenever the marker moved; 26 keeps a 2 px AA
 * margin over the worst-case ink extent and is byte-identical on the glass
 * (LV_ALIGN_CENTER keeps the centre fixed, so mx/my in draw_vault_peak_mark()
 * are unchanged). */
#define VAULT_PEAK_MARK_SIZE 26
/* CRT overlay, mirroring the web canvas: a smooth radial darkening that starts
 * just past half radius, plus scanlines every 4th row clipped to the face. The
 * web draws both last, so they sit over the needle and digits too. */
#define VAULT_VIGN_R0        50.0f
#define VAULT_VIGN_R1        233.0f
#define VAULT_VIGN_MAX       0.60f
#define VAULT_FACE_R         231.0f
#define VAULT_SCAN_STEP      4
#define VAULT_SCAN_OPA       41 /* 0.16 * 255 */
/*
 * How many radial boxes the swept needle is invalidated in.
 *
 * The needle is a thin spoke, so its axis-aligned bounding box is mostly empty
 * air: at 45 degrees a 194 px spoke 14 px wide needs a 165 x 165 box, ~27k px
 * of which about 3k carries ink. Everything downstream is charged per box
 * pixel, not per lit pixel:
 *   - the cached face is re-blitted across the whole box;
 *   - lv_draw_sw_triangle() rasterises each of the three needle triangles over
 *     (triangle bbox AND clip area) and applies three line masks per row across
 *     the full row width, so a fat clip costs three times the box;
 *   - draw_vault_crt() emits one chord-clipped row per VAULT_SCAN_STEP rows
 *     across it;
 *   - and the panel is flushed with it.
 * Invalidating the spoke as a chain of small boxes cuts all four at once and
 * cannot change a pixel: the drawing code is untouched, only the dirty region
 * it gets clipped to.
 *
 * Measured on a host bench over a 900-render sweep, configured like the
 * firmware (466x466 RGB565, 20-line partial draw buffer, the CO5300 even/odd
 * area rounder, tile_cnt 2) - flushed px per render, panel flushes per render,
 * and host raster time:
 *     1   29913 px   4.42 flushes   0.143 ms
 *     2   15652 px   3.06 flushes   0.112 ms
 *     3   14043 px   3.99 flushes   0.116 ms
 *     4   13469 px   4.81 flushes   0.137 ms
 * (the shipped single box was 25126 px / 3.97 / 0.142 ms before the tail and
 * bulge coverage fixes below widened the one-box case.)
 * Past three the boxes stop shrinking - the fixed half-width padding dominates
 * - while the per-box object walk and an extra panel flush keep being paid.
 * Two is the pick if panel flush setup turns out to cost more than ~0.5 ms per
 * 1600 px composited. Set to 1 to restore the single whole-spoke box.
 */
#ifndef VAULT_NEEDLE_SEGS
#define VAULT_NEEDLE_SEGS    3
#endif
/* Vault-Tec mark: a ringed hub with three cog bars each side, sized to tuck
 * between the BOOST-O-METER line (y=-78) and the needle hub. */
#define VAULT_LOGO_Y         (-62)
#define VAULT_LOGO_R         15
#define VAULT_LOGO_RING_W    5
#define VAULT_LOGO_HUB_R     6
#define VAULT_LOGO_BAR_W     5
#define VAULT_LOGO_BAR_DY    10
#define VAULT_LOGO_BAR_IN    12
#define VAULT_LOGO_BAR_SHORT 34
#define VAULT_LOGO_BAR_LONG  45
#define HUD_A0     154.0f   /* 270 - 116 */
#define HUD_A1     386.0f   /* 270 + 116 */
#define HUD_BRACKET_X 126
/* Chromatic split of the ghost pass. Shared with the invalidation so the dirty
 * box can never be narrower than the pixels the ghosts actually touch. */
#define HUD_GLITCH_DX 6
/* The readout callback is clipped to this object. Keep the bounds in face-local
 * coordinates: draw_hud_readout() still emits absolute screen coordinates via
 * px_icx()/px_icy(), while the parent scene can move for burn-in protection. The
 * extra invalidation margin is included so lv_obj_invalidate_area() does not
 * silently clip the old/new union at the object edge. */
#define HUD_READOUT_OBJ_X1 (-162) /* left ghost edge: -156 - HUD_GLITCH_DX */
#define HUD_READOUT_OBJ_X2 (117)  /* right slot invalidation edge: 82 + 28 + 7 */
#define HUD_READOUT_OBJ_Y1 (HUD_VALUE_Y - 42)
#define HUD_READOUT_OBJ_Y2 (HUD_VALUE_Y + 42)
#define HUD_READOUT_OBJ_W  (HUD_READOUT_OBJ_X2 - HUD_READOUT_OBJ_X1 + 1)
#define HUD_READOUT_OBJ_H  (HUD_READOUT_OBJ_Y2 - HUD_READOUT_OBJ_Y1 + 1)

/* Share Tech Mono (readouts) and Saira Condensed (labels) stand in for the
 * Consolas/Bahnschrift pairing used by the web mirror; both are OFL, so they
 * can ship in the firmware image. Compiled for host too so the simulator is
 * font-faithful. */
LV_FONT_DECLARE(alvida_big);
LV_FONT_DECLARE(font_mono_16);
LV_FONT_DECLARE(font_mono_40);
LV_FONT_DECLARE(font_cond_14);
LV_FONT_DECLARE(font_cond_18);
LV_FONT_DECLARE(font_cond_22);
LV_FONT_DECLARE(font_cond_96);
LV_FONT_DECLARE(archivo_black_65);
LV_FONT_DECLARE(font_wide_22);
LV_FONT_DECLARE(font_wide_32);
LV_FONT_DECLARE(neon_big);
LV_FONT_DECLARE(doto_big);
LV_FONT_DECLARE(neon_label);
#define BIGDIGIT_FONT  (&alvida_big)
#define F_MONO16 (&font_mono_16)
#define F_MONO40 (&font_mono_40)
#define F_COND14 (&font_cond_14)
#define F_COND18 (&font_cond_18)
#define F_COND22 (&font_cond_22)
#define F_COND96 (&font_cond_96)
#define F_WIDE22 (&font_wide_22)
#define F_WIDE32 (&font_wide_32)
#define HUD_VALUE_FONT F_COND96
#define NEON_BIG   (&neon_big)
#define NEON_BIG_DOTO (&doto_big)
#define NEON_LABEL (&neon_label)
#define HUD_READOUT_GLYPH_COUNT 12

/* Production uses the immutable glyph cache. Set to 0 only for a matched,
 * compile-time source-font A/B; there is deliberately no runtime switch. */
#ifndef BOOST_HUD_READOUT_CACHE
#define BOOST_HUD_READOUT_CACHE 1
#endif
#if BOOST_HUD_READOUT_CACHE != 0 && BOOST_HUD_READOUT_CACHE != 1
#error "BOOST_HUD_READOUT_CACHE must be 0 or 1"
#endif

/* Pre-rendered opaque glyph sprites for the neon readout, baked once per zone
 * colour at scene build and blitted with lv_draw_image() (LV_OPA_COVER, no
 * recolor) instead of re-running lv_draw_label() every frame. Default on;
 * set to 0 for a matched compile-time A/B against the live-label path. */
#ifndef BOOST_NEON_GLYPH_SPRITES
#define BOOST_NEON_GLYPH_SPRITES 1
#endif
#if BOOST_NEON_GLYPH_SPRITES != 0 && BOOST_NEON_GLYPH_SPRITES != 1
#error "BOOST_NEON_GLYPH_SPRITES must be 0 or 1"
#endif

static const char *TAG = "boost_gauge";

/* ---- shared scene state -------------------------------------------------- */
static lv_obj_t *s_well;
/* Parent supplied by boost_page; the active screen remains the legacy default. */
static lv_obj_t *s_scene_parent;
static boost_gauge_style_t s_built_style = BOOST_STYLE_ARC;

/* Every scene object is a child of this; moving it moves the whole face. It is
 * styleless and exactly screen-sized, so it costs one bounds test per redraw
 * and paints nothing. Offsets survive a theme rebuild deliberately: restarting
 * the ring on every theme change would park the new face back at (0,0). */
static lv_obj_t *s_root;
static int32_t s_px_dx;
static int32_t s_px_dy;
static uint8_t s_px_step;
static uint32_t s_px_step_ms;
static uint32_t s_px_settled_ms;
static float s_px_ref_psi;

/* ---- arc style ----------------------------------------------------------- */
/* Static furniture (unfilled track ring, scale numerals, "PSI" unit mark) is
 * rasterised once into a PSRAM canvas at scene build, the same win vault/hud
 * got. The zero notch stays live above the moving wedge so the wedge cannot
 * cover it. */
static lv_obj_t *s_arc_bg;
static uint8_t *s_arc_bg_buf;
static lv_obj_t *s_arc_value_canvas;
static lv_obj_t *s_zero_notch;
/* One styleless draw object owns the five value cells (sign, tens, ones,
 * decimal, tenths). Tight per-glyph ink-box invalidation replaces five
 * fixed-size label objects whose 47x58 boxes flushed more pixels than the
 * glyph ink every time a digit changed. */
static lv_obj_t *s_arc_readout;
static char s_arc_slot_text[ARC_SLOT_COUNT][2];
static lv_color_t s_arc_readout_color;
static bool s_arc_readout_color_valid;
static lv_obj_t *s_peak_label;
static lv_obj_t *s_mode_label;
static lv_obj_t *s_zone_label;
static int16_t s_arc_sign_x;

/* ---- vault style --------------------------------------------------------- */
/* Fixed readout slots (montserrat_40: digit advance ~23 px, '.' ~11, '-' ~15)
 * so the value never slides horizontally as digits change. */
enum {
    VAULT_SLOT_SIGN = 0,
    VAULT_SLOT_TENS,
    VAULT_SLOT_ONES,
    VAULT_SLOT_DOT,
    VAULT_SLOT_TENTHS,
    VAULT_SLOT_HUNDREDTHS,
    VAULT_SLOT_COUNT,
};
/* Share Tech Mono advances a uniform 21.6 px at 40 px. */
/* IBM Plex Mono advances a uniform 24 px at 40 px. Every slot is always
 * filled (sign + 2 integer digits + 2 decimals), so the readout is centred
 * by construction and can never shift as the value changes. */
static const int k_vault_slot_x[VAULT_SLOT_COUNT] = { -60, -36, -12, 12, 36, 60 };

static lv_obj_t *s_vault_bg;
static uint8_t *s_vault_bg_buf;
typedef struct {
    float psi_min;
    float psi_max;
    float psi_overboost;
    float zero_angle;
    uint32_t face;
    uint32_t text;
    uint32_t muted;
    uint32_t overboost;
    uint8_t vignette_pct;
    bool valid;
} vault_bg_key_t;
static vault_bg_key_t s_vault_bg_key;
static lv_obj_t *s_vault_crt;
static lv_obj_t *s_vault_peak_mark;
static float s_vault_peak_deg;
static lv_obj_t *s_vault_needle;
static lv_obj_t *s_vault_window;
/* The six fixed readout labels share one draw object. This keeps LVGL from
 * walking six independent label objects on every needle dirty region while
 * retaining each slot's exact area and text alignment. */
static lv_obj_t *s_vault_readout;
static char s_vault_slot_text[VAULT_SLOT_COUNT][2];
static lv_color_t s_vault_readout_color;
static bool s_vault_readout_color_valid;
static lv_obj_t *s_vault_peak;
static lv_obj_t *s_vault_alert;
static lv_obj_t *s_vault_alert_marks;
static float s_vault_needle_deg;
/* Track the body colour independently of angle so a colour-only setting change
 * clears the old pixels even when the needle is stationary. */
static bool s_vault_needle_red;
static bool s_vault_needle_over;
#define VAULT_NEEDLE_RED 0xFF3B30u

/* ---- hud style ----------------------------------------------------------- */
/* Right-aligned fixed slots (hud_big 76 px: digit advance ~51, '.' ~17,
 * '-' ~29). Decimal and tenths are pinned; integer digits grow left. */
enum {
    HUD_SLOT_TENS = 0,
    HUD_SLOT_ONES,
    HUD_SLOT_DOT,
    HUD_SLOT_TENTHS,
    HUD_SLOT_COUNT,
};
/* Saira Condensed 96: digit advance ~46 px, '.' ~21.5, '-' ~29. */
/* IBM Plex Sans Condensed BoldItalic 96: digit 52 px, '.' 27, '-' 34. */
static const int k_hud_slot_x[HUD_SLOT_COUNT] = { -50, 2, 42, 82 };
#define HUD_SIGN_ONES_X (-45)
#define HUD_SIGN_TENS_X (-97)
#define HUD_VALUE_Y     (-2)
/* A BMP280 that answered at boot but stopped responding must not leave a stale
 * number on the corner readout, so the ATM line gates on read age, not on the
 * boot presence flag alone. */
#define HUD_BMP_FRESH_MS 2000u

static lv_obj_t *s_hud_face;
static lv_obj_t *s_hud_bg;
static uint8_t *s_hud_bg_buf;
static lv_obj_t *s_hud_fill;
/* The complete 96 px readout is one styleless draw object. Keeping the ghosts
 * and primary glyphs in one callback makes their order explicit while the
 * object's invalidation remains one exact old/new union. */
static lv_obj_t *s_hud_readout;
static char s_hud_slot_text[HUD_SLOT_COUNT][2];
static char s_hud_sign_text[2];
static int s_hud_sign_x = HUD_SIGN_ONES_X;
static lv_color_t s_hud_readout_color;
static bool s_hud_readout_color_valid;
/* The Night City readout uses a scene-owned immutable font. Its ten digits,
 * decimal point and minus sign are expanded once from the packed source font,
 * then read concurrently by LVGL's software draw units without changing image
 * sources at runtime. */
typedef struct {
    lv_font_t font;
    lv_font_glyph_dsc_t glyph[HUD_READOUT_GLYPH_COUNT];
    uint32_t offset[HUD_READOUT_GLYPH_COUNT];
    uint8_t *pixels;
    size_t pixels_size;
} hud_readout_font_t;
static hud_readout_font_t s_hud_readout_font;
/* Angle/value the fill was last painted at. Drawing and invalidating must
 * agree: a skipped invalidation with a moved draw leaves stale pixels. */
static float s_hud_fill_deg;
static float s_hud_fill_psi;
static float s_hud_fill_color_psi;
static bool s_hud_fill_valid;
static char s_hud_val_str[12];
static lv_obj_t *s_hud_map;
static lv_obj_t *s_hud_pk;
static lv_obj_t *s_hud_sys;
static lv_obj_t *s_hud_tag;

/* ---- bigdigit style ------------------------------------------------------ */
static lv_obj_t *s_big_bg;
static lv_obj_t *s_big_minus;
static lv_obj_t *s_big_tens;
static lv_obj_t *s_big_ones;
static lv_obj_t *s_big_dot;
static lv_obj_t *s_big_tenths;
static lv_obj_t *s_big_unit;
static lv_obj_t *s_big_zone;
static lv_obj_t *s_big_peak;
static int s_big_bg_step = -1;
static int s_big_text_step = -1;
static uint32_t s_big_text_color;
/* Ground recolour is spread across these bands, one per update tick. */
#define BIG_BANDS 1
static lv_obj_t *s_big_band[BIG_BANDS];
static int s_big_band_next = BIG_BANDS;
static uint32_t s_big_band_color;

/* ---- neon style ---------------------------------------------------------- */
/* Arc `radius` in LVGL is the stroke's OUTER edge, not a centreline - so this
 * is exactly how far from centre the brightest pixel of the ring sits. Panel
 * radius is 233; 228 leaves a 5px margin to the bezel, matching marquee's own
 * outermost bulb ring's tips (centreline 224, tips at 228) closely enough to
 * carry no new risk. The tube's lit depth is NEON_TUBE_BAND_DEPTH (55, inner
 * edge 174) and the segments' NEON_SEG_BAND_DEPTH (49, inner edge 179); the
 * widest readout (-12.0, measured ink reaching ~170px at the current
 * NEON_FONT_PX / NEON_SLOT_W / NEON_SIGN_W) clears both. */
#define NEON_R          228     /* ring centre radius */
#define NEON_SEG_W      30      /* segment stroke width */
#define NEON_TUBE_W     26      /* nominal tube stroke width (halo is its own literal now) */
/* Segments: 45 wedges at a FIXED 6-degree pitch (4 lit + 2 gap). The pitch is
 * an exact division of the 270 sweep (45 x 6 = 270, no bare track at the
 * ends), and it must be whole degrees because LVGL rasterizes arcs at
 * whole-degree resolution: a fractional slot (270/41) rendered as a visible
 * mix of 4 and 5 degree wedges. Every segment boundary below is a whole
 * degree, so the ring is uniform. */
#define NEON_NSEG       45
/* Glow reach. The mockup's bloom was a gaussian blur composited additively,
 * which this pipeline cannot afford per frame - alpha is its most expensive
 * operation. It is approximated with concentric OPAQUE strokes of falling
 * brightness: NEON_GLOW_OUT px outside the ring and the inner band px inside
 * the body. Both feed the clip guard and the invalidation bounds, so widening
 * the glow automatically widens the dirty region. */
#define NEON_GLOW_OUT   0       /* no outward bleed: the segment is three flat bands */
#define NEON_CAP_W      6       /* white tip, the outermost of the four tube bands */
/* The inner (dimmed) band is the SAME width as the bloomed body, extending
 * inward from the body's inner edge - so the lit three-tone band is
 * symmetric about the body and its full depth is 2W - CAP. The unlit track
 * stays at the body width W with the same outer edge. One formula feeds the
 * draw, the bakes, the invalidation and the web mirror so they cannot drift. */
/* The inner (dimmed) band used to match the body width, so the lit depth was
 * 2W - CAP; the tube's halo is its own literal now (NEON_TUBE_HALO_W 20) and
 * the segments' is NEON_SEG_HALO_W 20 against a 25 px body. */
#define NEON_SEG_HALO_W     20
#define NEON_SEG_BAND_DEPTH (NEON_SEG_HALO_W + (NEON_SEG_W - NEON_CAP_W + 1) + NEON_CAP_W - 2)  /* 49 */
/* The tube's lit run is FOUR bands, one more than the segments: white cap
 * (skinny, back at NEON_R), then the TRACK split into two tones - the outer
 * half is lighter than the inner half, which keeps the current bloomed body
 * colour - and the innermost dark halo, which stays as it was. The track
 * half-width NEON_TUBE_TRACK_HALF is deliberately less than the halo
 * thickness (16 < 21), so the whole track (32) is less than twice the halo.
 * All radii are the band's OUTER edge (LVGL), abutting with the +1s. */
#define NEON_TUBE_TRACK_LIGHT 0.26f    /* outer half: HSL lightness step (keeps hue+saturation) */
/* The middle band is the bloomed accent scaled to 0.88 so the OUTER half has
 * chroma headroom. The bloom keeps hue+saturation at 1.0 and already pushes
 * the bright zone colours (yellow, magenta, cyan) near the top of the RGB
 * range, so lightening them toward the cap collapses into white - the "too
 * pale" wash. Scaling the middle down ~12% keeps it vivid while giving the
 * lighten step room to land as a clearly lighter, still-hued band. */
#define NEON_TUBE_MID_SCALE 0.88f
#define NEON_TUBE_TRACK_HALF 16        /* each track half, < NEON_TUBE_HALO_W (20) */
#define NEON_TUBE_HALO_W     20        /* innermost dark ring (was NEON_BODY_W = 21) */
#define NEON_TUBE_TRACK_OUTER_R (NEON_R - NEON_CAP_W + 1)                    /* 223 */
#define NEON_TUBE_TRACK_INNER_R (NEON_TUBE_TRACK_OUTER_R - NEON_TUBE_TRACK_HALF + 1)  /* 208 */
#define NEON_TUBE_HALO_R        (NEON_TUBE_TRACK_INNER_R - NEON_TUBE_TRACK_HALF + 1)  /* 193 */
/* Full lit depth on the tube: 228 outer to 174 inner = 55 px. The halo's
 * inner edge is haloR - haloW + 1, so depth = NEON_R - that + 1. */
#define NEON_TUBE_BAND_DEPTH (NEON_R - NEON_TUBE_HALO_R + NEON_TUBE_HALO_W)
/* Unlit track width on the tube (track + cap footprint, excluding the dark
 * halo): 228 - 193 + 1 = 36. This is the width of the unlit track bake AND
 * of the tube peak tell-tale: the peak marker must stay fully contained
 * within the track (user's 2026-08-11/12 bench requirement - it must NOT
 * bleed into the dark halo the way the white zero marker does). The zero
 * marker draws the full lit depth (NEON_TUBE_BAND_DEPTH, 55). The lit run
 * also paints the full depth. */
#define NEON_TUBE_TRACK_W (NEON_R - NEON_TUBE_HALO_R + 1)
/* The dark remainder between lit wedges. 2.0 is the ORIGINAL gap, kept
 * exactly: with the fixed NEON_SEG_PITCH below the lit wedge is 4.0 and the
 * gap 2.0, and both stay whole degrees so the ring renders uniformly. */
#define NEON_SEG_GAP    2.0f
/* Fixed segment pitch (slot = lit + gap), and the grid offset that centres
 * NSEG x PITCH within the 270-degree sweep. NEON_SEG_START is the leading
 * edge of segment 0's slot; each segment's LIT wedge is
 * NEON_SEG_START + i*PITCH + GAP/2 .. + NEON_SEG_LIT. */
#define NEON_SEG_PITCH  6.0f
#define NEON_SEG_LIT    (NEON_SEG_PITCH - NEON_SEG_GAP)                       /* 4.0 */
#define NEON_SEG_START  ((float)ARC_START + ((float)ARC_RANGE - NEON_SEG_PITCH * (float)NEON_NSEG) * 0.5f)  /* 135.0 */
static inline float neon_seg_start(int i)
{
    return NEON_SEG_START + (float)i * NEON_SEG_PITCH + NEON_SEG_GAP * 0.5f;
}
/* Tube run tiles: the continuous run is drawn as a_zero-aligned A8 wedge
 * tiles (NEON_TUBE_TILE_STEP each) plus a live arc for the partial tip, so a
 * zone flip that recolours the whole run repaints as blits instead of
 * rasterising the full run four times. Each tile is baked OVERLAP past both
 * edges and the tip arc starts the same overlap early, so adjacent AA
 * fringes always land under a neighbour's full-coverage interior and the run
 * reads as one continuous band. */
#define NEON_TUBE_TILE_STEP   (ARC_RANGE / (float)NEON_NSEG)   /* 270/45 = 6.0 (tube tiles only; not the segments' pitch) */
/* The tube tiles carry NO angular AA (they are cut from a full-ring radial
 * bake in neon_bake_tube_sprites), so they tile exactly with no overlap; the
 * live tip arc starts at the tile boundary. This constant is the tip
 * overhang and the clip-box extent and stays 0. */
#define NEON_TUBE_TILE_OVERLAP 0.0f
/* Radial-gradient arc image margin (px each side of the band). The image must
 * hold the baked band's own AA fringes (r=NEON_R + 1) plus the arc's slightly
 * larger mask, so the gradient arc is drawn at radius NEON_R + NEON_GRAD_MARGIN
 * and width NEON_BAND_DEPTH + 2*NEON_GRAD_MARGIN: the mask then clips far
 * outside the band and the image's own baked edges supply the ring's AA
 * uniformly (a bare 2*NEON_R image cut the cap's outer AA off at the axes). */
#define NEON_GRAD_MARGIN 4
/* Numerals sit INSIDE the ring. Outside would put them within ~13 px of the
 * glass on a 466 px round panel, where the bezel and the curve eat them. */
#define NEON_LABEL_R    134     /* scale numeral radius */
/* Slot/dot/sign kept close to proportional with NEON_FONT_PX, raised together
 * when the font grew 108->118 (regenerated metrics: line_height 76->83,
 * widest glyph ink 77->84). NEON_SLOT_W is the cell pitch - it must clear the
 * widest glyph's ink width (84) or adjacent opaque digit sprites overlap and
 * paint over each other; 88 leaves a 4 px margin above that floor. SIGN_W
 * is 42 rather than the exactly-proportional 43: at 43 a specific psi
 * trajectory through the audit's 20 s sweep produced a 1-step antialiasing
 * seam against the ring - purely a sub-pixel rounding coincidence at that
 * exact sign width, gone at 42 or 44, kept at 42 for the extra clearance
 * margin. */
#define NEON_SLOT_W     88
/* The decimal's cell, and the readout's main spacing lever.
 *
 * It was 45 for a glyph whose ink is only 22 px wide - 23 px of padding, more
 * than the digit cells carry in proportion. That was not a design choice: with
 * opaque tiles the decimal's neighbours had to be held far enough away that
 * their black margins could not reach its ink, and the decimal, sitting
 * between two of the widest glyphs on the face, was the most boxed-in cell of
 * all. It is also where the eye reads the readout's spacing from, since
 * "8.5" has no two digits adjacent to each other - so that padding is exactly
 * what made the readout look too widely spaced.
 *
 * A8 coverage removed the constraint, so this is now set from ink: 34 leaves
 * 6 px either side of a 22 px glyph. The digit cells are NOT tightened to
 * match - at 88 pitch two of the widest digits (ink 84) already clear each
 * other by only 4 px, so the digits are at their ink limit and the decimal
 * was the only slack left. */
#define NEON_DOT_W      34
#define NEON_SIGN_W     42
/* The negative readout (-12.0) is the widest the face ever gets. Measured on
 * the rendered screenshot at 118 px: readout ink reaches ~170 px against the
 * segments' 179 px inner edge (NEON_R 228 minus NEON_SEG_BAND_DEPTH 49),
 * clearing by ~9 px. */
#define NEON_FONT_PX    118
/* Half the slack the draw box adds around each cell. The box must be at least
 * the glyph's ADVANCE wide, because lv_draw_label centres on the advance and a
 * narrower box clips: 0.780 em is the widest advance in this face, so 84 px at
 * 108 and 120 px at 154. 18 gives boxes of 100 and 128, clearing both. It was
 * 30, which made a 124 px box for an 84 px glyph - and the readout is 64% of
 * segments' dirty area per cycle and 83% of marquee's, so that slack was the
 * single largest avoidable cost on the face. */
#define NEON_CELL_BLEED 18
#define NEON_SIGN_GAP   8       /* from the glyph's ink edge, not the cell's */
/* The minus mark's glow is NOT a constant here any more. It used to be a
 * second pass of the bar geometry inflated by a fixed 5 px, which at a 6 px
 * bar height on an 8 px pitch overlapped the two bars and filled the gap
 * between them solid. The mark is now baked through the same box blur as the
 * digits (neon_bake_sign_sprite()), so its reach is NEON_SPR_GLOW_MARGIN like
 * every other sprite's, and the two match without tuning. */
/* Marquee shares the ring layouts' readout metrics (NEON_FONT_PX /
 * NEON_SLOT_W / NEON_DOT_W / NEON_SIGN_W / NEON_SIGN_GAP / NEON_READOUT_TOP)
 * and the same lower-stack rhythm - it used to carry its own 130 px font and
 * wider cells, but the three-ring border needs the room that oversized
 * readout occupied, and one sprite set serving every layout is cheaper in
 * PSRAM and in scene-switch time than two. */
/* Top of the readout's draw box, per layout. lv_draw_label() draws from the TOP
 * of its area, so this - not a centre - is what positions the digits, and it is
 * also what the sign's vertical centre is derived from. Each is set so
 * top + line_height/2 keeps the same vertical anchor the old font used
 * (-1px off face centre for segments/tube, -26px for marquee) now that
 * line_height changed. */
#define NEON_READOUT_TOP     (-42)
/* The neon readout's font, and every metric measured off that typeface rather
 * than chosen for the face. The readout is baked to A8 coverage sprites at
 * scene build, so switching fonts only needs a rebake - but the cell pitch,
 * decimal width, sign geometry and the digit advance tables all come from the
 * font, so they live here with it instead of as free-floating constants. */
typedef struct {
    const lv_font_t *font;
    int slot_w;      /* digit cell pitch, clears the widest digit's ink */
    int dot_w;       /* decimal cell width */
    int sign_w;      /* sign mark width */
    int sign_gap;    /* from the first glyph's ink edge, not the cell's */
    int negative_shift; /* move signed composition right for left-ring clearance */
    int font_px;     /* render size the font was generated at */
    int cell_bleed;  /* draw-box slack around each cell */
    int readout_top; /* vertical anchor; top + line_h/2 keeps the face centre */
    bool sign_is_dots; /* true: three Doto modules; false: SF bars */
    const boost_neon_digit_metrics_t *metrics;
} neon_font_style_t;

static const neon_font_style_t k_neon_sf = {
    .font = NEON_BIG,
    .slot_w = NEON_SLOT_W,
    .dot_w = NEON_DOT_W,
    .sign_w = NEON_SIGN_W,
    .sign_gap = NEON_SIGN_GAP,
    .negative_shift = 0,
    .font_px = NEON_FONT_PX,
    .cell_bleed = NEON_CELL_BLEED,
    .readout_top = NEON_READOUT_TOP,
    .sign_is_dots = false,
    .metrics = &boost_neon_sf_metrics,
};
static const neon_font_style_t k_neon_doto = {
    .font = NEON_BIG_DOTO,
    .slot_w = 68,      /* 61 px digit ink + margin at 126 px */
    .dot_w = 26,       /* 11 px dot ink + balanced visual gaps */
    .sign_w = 42,      /* three 10 px period modules with 6 px gaps */
    .sign_gap = 20,      /* 20 px beside any tabular digit; shifts sign 4 px left */
    .negative_shift = 16,
    .font_px = 126,
    .cell_bleed = 18,  /* clears the 75.6 px advance */
    .readout_top = -42, /* Doto line_height 85; centre on the face */
    .sign_is_dots = true,
    .metrics = &boost_neon_doto_metrics,
};

/* Which readout font is active right now. */
static const neon_font_style_t *neon_font(void)
{
    return (boost_theme_neon_font() == BOOST_NEON_FONT_DOTO)
        ? &k_neon_doto : &k_neon_sf;
}
/* One vertical rhythm for the lower stack, used by every layout: unit mark,
 * hairline rule and peak readout at fixed offsets from the centre. Marquee
 * shifts the whole block down as a unit rather than re-spacing it, so the three
 * layouts read identically - it needs the shift because its bar occupies the
 * space the other two leave empty above the unit mark.
 *
 * Moved down 40px as a unit (was 96/106/126) - the ring layouts had 55px+ of
 * empty panel below the old peak line before hitting the bezel, so there was
 * plenty of room to drop the whole assembly a good bit while preserving the
 * internal spacing (unit->rule 10px, rule->peak 20px). */
#define NEON_UNIT_Y     128
#define NEON_RULE_Y     138
#define NEON_PEAK_Y     158
/* The lower stack (unit mark, rule, peak) sits at one rhythm on every
 * layout, including marquee - the marquee-specific downward shift went away
 * with the oversized readout, and the bar at NEON_BAR_Y clears the unit mark
 * with the shared offsets. The whole assembly was lifted 8 px (136->128 /
 * 146->138 / 166->158) so the peak reads comfortably clear of the marquee's
 * inner ring. */
/* Marquee's linear bar, shared by the bake, the draw and the invalidation so
 * they cannot drift apart. Shortened from 150 so it reads as a ruler under
 * the digits rather than extending past them. */
#define NEON_BAR_HALF   132
#define NEON_BAR_Y      68
#define NEON_BAR_H      16
/* Zero mark on the bar, the linear equivalent of the ring's white zero segment.
 * Drawn live rather than baked because the fill passes over it and has to leave
 * it visible. Shorter and wider than the first pass (4x36): 7x27 reads as a
 * stout capsule marker instead of a thin sliver, closer in proportion to the
 * bar it marks (NEON_BAR_H 16). Capsule ends unchanged (LV_RADIUS_CIRCLE). */
#define NEON_BAR_TICK_W 7
#define NEON_BAR_TICK_H 27
/* Half-width, in degrees, of the tube layout's white zero marker.
 *
 * This is drawn TWICE and both have to use it. The marker is baked into the
 * static background so it survives with nothing lit, but the live tube run
 * starts exactly at a_zero and sweeps outward at the marker's own radius and
 * width - so it paints over whichever half of the marker lies on the value's
 * side. That left only half the marker visible (2 degrees of the 4 it was
 * baked at), and, because the buried half swaps sides at the zero crossing,
 * the surviving half appeared to JUMP sideways between vacuum and boost. That
 * is the shift on the panel, and it is also why widening the bake alone never
 * looked any wider. The fix is to redraw the marker live after the run, which
 * costs one arc per frame in this layout only. 3 gave a 6 degree marker; 2.25
 * makes it 25% narrower (4.5 degrees) as a visual tweak.
 *
 * The arc rasterizer does not paint an angle span exactly symmetric about its
 * midpoint: lv_draw_arc's trig-table quantises each edge to the nearest table
 * entry. Measured on the sim's atmo render, an uncompensated [zero-2.55,
 * zero+2.55] marker paints its centroid at 235.495 while the run that sweeps
 * out of the notch starts at ~236.00 (both ~0.25-0.75 deg shy of the nominal
 * 236.25) - so the marker read ~0.5 deg toward the vacuum side of the visible
 * zero. NEON_TUBE_ZERO_CENTER (+0.25 deg) shifts the drawn span so the
 * painted centroid lands on the run start; re-measured after the fix at
 * 235.981 vs the run start 236.00. The web mirror does NOT apply it: canvas
 * arcs are symmetric, so its marker is already centred on the true zero. */
#define NEON_TUBE_ZERO_DEG    2.25f
#define NEON_TUBE_ZERO_CENTER 0.25f
/* Half-width, in degrees, of the tube layout's peak tell-tale. The marker is
 * drawn from the CONTINUOUS peak angle - no segment snapping - and centred
 * exactly on it, so no NEON_TUBE_ZERO_CENTER-style compensation is needed
 * (that offset exists because the RUN that sweeps out of the notch starts at
 * a quantised edge; the peak marker has no anchored neighbour). The old
 * segment-quantised marker sat up to a full 6-degree pitch off the actual
 * measurement, which is what read as the tube never reaching the marked
 * point. Half-width 2.25 matches the white zero marker's NEON_TUBE_ZERO_DEG
 * exactly, so the two landmarks have the same TOTAL angular width (4.5 deg)
 * - the user's definition of the peak marker's "width" is how many degrees
 * it extends left/right of its centre line, and the 2026-08-12 bench
 * comparison against the 0 marker was about that angular span, not the
 * radial depth. The marker's RADIAL depth stays NEON_TUBE_TRACK_W (36,
 * contained in the track); only the angular span matches the zero marker. At
 * psiMax the dial clamp cuts the drawn band in half, the same natural
 * cut-off the user accepted at the end of the track. */
#define NEON_TUBE_PEAK_DEG 2.25f
/* Invalidation padding around the exact arc sector bbox: the tube's gradient
 * mask runs 4 px inside the geometric inner edge (NEON_GRAD_MARGIN) plus ~2 px
 * arc-mask AA fringe plus 2 px margin. See the use site for the full argument. */
#define NEON_INV_PAD 7
/* Bulb border. Three concentric rings, one zone each - innermost vacuum,
 * middle boost, outermost overboost. The dots are two-tone: most bulbs are
 * baked dead track, and every ring carries 24 ACCENT bulbs (every sixth pair)
 * that LIGHT UP LIVE - ring z's accents are coloured with that ring's OWN
 * zone colour only once the reading has REACHED that zone (zone id >= z). At
 * rest only the innermost ring shows colour; rev into boost and the middle
 * ring lights; hit overboost and all three are lit. So the border reads as a
 * stage ladder while staying two-tone at idle.
 *
 * The accent phase is ANCHORED per ring (NEON_BULB_ACCENT_OFFSET(z)): the
 * inner ring keeps its pairs at 0,1 (top centre), the OUTER ring is shifted
 * two bulbs on so its pairs sit OFF the vertical axis (flanking top and
 * bottom rather than straddling them) - the same pattern the inner ring
 * shows, as close as the different bulb counts allow. The middle ring's
 * pairs sit at the bottom centre - bulb N/2 is exactly at 6 o'clock and
 * carries the pair's FIRST residue, with its partner one dot
 * counterclockwise, so the pair leans left. The outer ring reads as one
 * ladder with the inner, and the middle ring's bottom pair marks the
 * boost stage.
 *
 * Invalidation on a zone flip is bounded: only the ACCENT bulbs (24 per
 * ring, 12 adjacent pairs) change colour, so one ring costs 12 pair-boxes and
 * even a two-zone jump (both rings 1 and 2) stays at 24 boxes - under LVGL's
 * 32-slot invalidation buffer. The dead track bulbs never change.
 *
 * NEON_BULB_R stays the outermost ring's centreline, so every old silhouette
 * measurement (tips at 228, margin to the bezel) still holds for it. The
 * 24 px centreline step (1.5x the 16 px the earlier spread used; 32 is the
 * 2x option, one constant away) is 9 px bulb + 15 px dark gap, wide enough
 * that the three rings read as three rings at arm's length. Zone-to-ring
 * mapping is 0 = innermost (vacuum) .. 2 = outermost (overboost), which is
 * why the ring index and the zone id are the same number. */
#define NEON_BULB_RINGS   3
#define NEON_BULB_RING_STEP 24
#define NEON_BULB_RING_R(z) (NEON_BULB_R - ((2 - (z)) * NEON_BULB_RING_STEP))
#define NEON_BULB_R     224
/* Bulb count PER RING. All three must stay divisible by 6 so the 2-lit/
 * 4-dark accent pattern wraps seamlessly and the invalidation groups of 6
 * stay whole. The counts are chosen so the CHORD spacing (2*pi*r/N) is
 * uniform across rings: outer 72 (chord 19.55), middle 66 (19.04), inner
 * 54 (20.48) - versus the old equal-72 counts, whose inner ring was 21%
 * tighter than the outer (15.36 vs 19.55). Multiples of 6 that bracket
 * the exact spacing are 54/66/72; the residual spread is under a pixel. */
#define NEON_BULB_N_INNER 54
#define NEON_BULB_N_MID   66
#define NEON_BULB_N_OUTER 72
#define NEON_BULB_N(z) ((z) == 0 ? NEON_BULB_N_INNER \
                       : (z) == 1 ? NEON_BULB_N_MID : NEON_BULB_N_OUTER)
#define NEON_BULB_HALF  4
/* Static accent anchor per ring: (i + offset) % 6 < 2. Ring 0 keeps offset 0
 * -> pairs at 0,1 (top centre, bulb 0 at 12 o'clock). Ring 2 is shifted two
 * bulbs on -> offset 2, so its pairs land at 2,3 and sit OFF the vertical
 * axis, flanking the top/bottom rather than straddling it - the same pattern
 * the inner ring shows, as close as the different bulb counts allow. Ring 1
 * uses offset 3 -> pairs at 3,4, and with NEON_BULB_N_MID = 66 its pair
 * (33,34) sits at the bottom centre (bulb 33 is exactly at 6 o'clock,
 * partner one dot counterclockwise). The optional marquee chase adds a
 * per-ring phase that advances one ring per spin tick (see s_neon_spin_phase
 * below) - the pattern repeats every 6 bulbs, so a ring has exactly 6 phase
 * states and one advance moves every accent pair by a single bulb. */
#define NEON_BULB_ACCENT_OFFSET(z) ((z) == 1 ? 3 : ((z) == 2 ? 2 : 0))
#define NEON_BULB_IS_ACCENT(i, z) (((((i) + NEON_BULB_ACCENT_OFFSET(z) + s_neon_spin_phase[z]) % 6) + 6) % 6 < 2)

/* Marquee border chase (neonMarqueeSpin, persisted in the theme store). One
 * ring advances per tick, round-robin, so a spin step costs the SAME 12
 * pair-boxes as a zone flip and never more than one ring's worth - advancing
 * all three at once would need 36 boxes and overflow LVGL's 32-slot
 * invalidation buffer, forcing a full-screen repaint. Ring z advances on
 * ticks where tick % 3 == z, so all three rotate at the same angular speed
 * (one ring per 3 ticks), just offset in time. The pattern period is 6, so
 * each ring has 6 phase states - one advance = one bulb of motion. Direction
 * per ring: inner and outer clockwise, middle counterclockwise. */
#define NEON_MARQUEE_SPIN_MS   90
#define NEON_SPIN_DIR_INNER    (-1)  /* clockwise  */
#define NEON_SPIN_DIR_MID      (1)   /* counterclockwise */
#define NEON_SPIN_DIR_OUTER    (-1)  /* clockwise  */
static int8_t s_neon_spin_phase[NEON_BULB_RINGS];
static uint8_t s_neon_spin_tick;      /* round-robin: ring (tick % 3) advances */
static uint32_t s_neon_spin_last_ms;  /* lv_tick_get() at the last advance   */
static const int8_t s_neon_spin_dir[NEON_BULB_RINGS] = {
    NEON_SPIN_DIR_INNER, NEON_SPIN_DIR_MID, NEON_SPIN_DIR_OUTER,
};

/* Committed marquee bar fill extent: pixel x of the zero end and of the
 * value end, as drawn. The bar invalidation is gated on these (plus a zone
 * colour flip) instead of firing on every 16 ms sample - when neither end
 * moved by a full pixel and the zone colour is unchanged, the painted bar is
 * pixel-identical, so repainting would only flush the same box at 62.5 Hz
 * forever. That is what lets the marquee go idle at a static reading like
 * every other face. Reset to impossible sentinels at scene build so the
 * first update after a rebuild always repaints. */
static int s_neon_bar_lo = INT_MIN;
static int s_neon_bar_hi = INT_MAX;

/* Precomputed bulb centre offsets, shared by the bake, the live draw and both
 * invalidation paths. The old per-call neon_bulb_pos() ran two trig calls and
 * a rounding per bulb, and the live draw plus every spin/zone-flip callback
 * invocation scans every accent bulb - so that cost repeated once per dirty
 * region. The offsets depend only on the ring constants, so they are computed
 * once and the per-bulb call becomes one table load and an integer centre
 * add. Bit identical: same lroundf(cosf/sinf(rad) * r), same centre. The
 * array is sized to the OUTER ring's count (the largest) and only the used
 * prefix of each ring is filled. */
static int16_t s_neon_bulb_ox[NEON_BULB_RINGS][NEON_BULB_N_OUTER];
static int16_t s_neon_bulb_oy[NEON_BULB_RINGS][NEON_BULB_N_OUTER];
static bool s_neon_bulb_table_ready;

/* Residue where ring z's accent pair starts at its CURRENT spin phase:
 * (i + NEON_BULB_ACCENT_OFFSET(z) + phase) % 6 < 2 lights residues base and
 * base+1. Shared by the live draw (via NEON_BULB_IS_ACCENT) and BOTH
 * invalidation paths (zone flip and spin step) so they cannot disagree about
 * where the accents are. */
static int neon_accent_base(int z)
{
    return ((6 - NEON_BULB_ACCENT_OFFSET(z) - s_neon_spin_phase[z]) % 6 + 6) % 6;
}

/* The marquee's centre draws the active readout sprites at 0.87 scale
 * so the composition (readout, bar, stack) fits inside the spread rings: the
 * innermost ring's inner edge is 224 - 2*STEP - 4 = 172, and the full-size
 * readout ink+glow reaches ~184, so the whole centre scales about the face
 * centre by this factor. One sprite set, drawn smaller - not a second font. */
#define NEON_MARQUEE_CENTER_SCALE 0.87f
/* Extra lift for the marquee readout only, on top of the center scale - the
 * scale pulls everything toward the face centre, so without it the readout
 * would sit LOWER at 0.87 than it did at 0.91. Lifting it keeps the bar and
 * the peak/psi stack below with more room to breathe. */
#define NEON_MARQUEE_READOUT_LIFT 12

static void *s_neon_bg_buf;
/* Everything paint_neon_background() reads, so a repaint happens exactly when
 * one of them changes and not on every scene build. Mirrors vault_bg_key_t. */
typedef struct {
    uint8_t layout;
    uint32_t track;
    uint32_t zero;
    /* Where zero lands on the sweep, which is the ONLY way the psi settings
     * reach the background - it places the white zero segment and nothing
     * else. One number instead of psiMin/psiMax/zeroAngle separately, and it
     * cannot disagree with what the paint actually computes because it is the
     * same call. */
    float zero_sweep;
} neon_bg_key_t;
static neon_bg_key_t s_neon_bg_key;
static bool s_neon_bg_key_valid;
static bool s_neon_bg_reused;
static lv_obj_t *s_neon_bg;
static lv_obj_t *s_neon_face;
static lv_obj_t *s_neon_zone;
static lv_obj_t *s_neon_unit;
static lv_obj_t *s_neon_peak;
static float s_neon_psi;          /* committed value the art is drawn from */
static float s_neon_peak_value;
/* The value the committed *colour* came from. Tracked separately because the
 * zone colour changes at thresholds, not continuously: when it flips, every
 * lit segment restyles and the whole run has to be repainted, not just the
 * segments the value moved across. Mirrors s_arc_color_psi. */
static float s_neon_color_psi;
/* Colour-flip deferral (word-first, arc-next-frame): the zone word updates on
 * the flip frame (cheap, now that its invalidation box is cropped to the word
 * sprite and no longer reaches the ring), and the full-run recolor is deferred
 * to the next sample. The flip frame therefore carries the word + readout +
 * peak but NOT the arc repaint, so its dirty region is smaller. DELIBERATE
 * one-frame visual lag (the ring shows the old zone colour for one frame after
 * the word flips) - NOT byte-identical, so the sim stale-pixel audit reports
 * those transition frames as mismatches by design. */
bool g_neon_flip_pending;
static float s_neon_flip_lo, s_neon_flip_hi;
/* Segment index currently carrying the peak tell-tale on the SEGMENTS layout,
 * -1 for none. The peak sits outside the run between the notch and the value,
 * so it is invalidated on its own when it moves. The tube layout tracks its
 * own continuous marker state (s_neon_tube_peak_angle) instead - see below. */
static int s_neon_peak_idx = -1;
/* Tube layout: the peak tell-tale is a continuous arc centred exactly on the
 * peak's sweep angle (no segment snapping), always drawn while a peak is
 * recorded. These two hold where it was last drawn so update_neon() can
 * invalidate exactly the old/new spans when it moves. */
static bool s_neon_tube_peak_vis;
static float s_neon_tube_peak_angle = NAN;
/* Whether the lit run covered the peak segment last frame (segments layout
 * only). The overlay is suppressed while it does, so this transition changes
 * the segment's appearance without changing its index - the one case a
 * "did the index move?" test would miss. The tube never suppresses: its
 * marker is a permanent landmark in a fixed dim colour, and popping it in
 * and out as the run crossed a segment boundary was the flicker at the
 * peak. */
static bool s_neon_peak_in_run;
/* Last readout composition actually painted. The tenths cell changes every
 * sample while the higher cells almost never do, so repainting the whole
 * 350x160 readout box each frame cost more than the entire ring. */
static char s_neon_cell_ch[BOOST_NEON_MAX_CELLS];
static int16_t s_neon_cell_x[BOOST_NEON_MAX_CELLS];
static uint8_t s_neon_cell_n;
static bool s_neon_sign_drawn;
static int16_t s_neon_sign_x;   /* where the sign was last painted */
static boost_neon_layout_t s_neon_layout;

/* Scale one centre-geometry value about the face centre on the marquee
 * layout only (identity elsewhere). Every readout/bar/stack/word constant
 * that positions the centre composition goes through this so the spread
 * rings and the centre agree about how much room there is. */
static inline int neon_mq(int v)
{
    return (s_neon_layout == BOOST_NEON_MARQUEE)
        ? (int)lroundf((float)v * NEON_MARQUEE_CENTER_SCALE)
        : v;
}

/* The marquee readout's vertical offset from centre: the scaled NEON_READOUT_TOP
 * plus the lift. The centre scale pulls everything toward the face centre, so
 * at 0.87 the readout would sit LOWER than it did at 0.91 without this - the
 * lift keeps it up so the bar and the peak/psi stack below have room to
 * breathe. Shared by the draw and the invalidation so they cannot disagree. */
static int neon_readout_top_off(void)
{
    return neon_mq(neon_font()->readout_top) - (s_neon_layout == BOOST_NEON_MARQUEE
        ? NEON_MARQUEE_READOUT_LIFT : 0);
}

#if BOOST_NEON_GLYPH_SPRITES
/* One PSRAM block holding every baked glyph, for every zone colour, at the
 * one sprite size every layout now shares (112x120): the font's own measured
 * union ink box plus a 14 px glow
 * margin on every side so the NEON_GLOW_BLUR_R glow has room to read before
 * the tile edge clips it.
 * The width covers the union of every glyph centred on its own ADVANCE
 * (advances differ: '3' leans to -37.9, '5' to +55.2 = 93.1 px) plus
 * margin, not the widest single ink. 12 glyphs (0-9, '.', '-') plus one sign
 * slot. '-' is never blitted: SF keeps its sliced bars and Doto draws three
 * modules matching the decimal dot. Marquee
 * used to carry its own 130 px font and sprite set; unifying the readout
 * across layouts removed it, saving ~1.16 MB of PSRAM and the scene-switch
 * rebake. PSRAM cost at this margin, measured via BOOST_NEON_DRAW_STATS
 * logging in neon_bake_glyph_sprites(): ~874 KB - comfortably under the
 * 1.6 MB/font budget against 8 MB of PSRAM total. */
#define NEON_SPR_GLOW_MARGIN 14
#define NEON_SPR_BIG_W  112
#define NEON_SPR_BIG_H  120
#define NEON_DOTO_SIGN_DOTS 3
/* 12 digits/punctuation plus one slot for the custom minus geometry - see
 * neon_bake_sign_sprite(). */
#define NEON_GLYPH_COUNT 12
#define NEON_SIGN_SLOT   NEON_GLYPH_COUNT
#define NEON_SPRITE_COUNT (NEON_GLYPH_COUNT + 1)
/* Glow strength. Gain was 60% of core coverage; pushed to 90% so the halo
 * reads as bright neon spill instead of a faint rim. The CORE ink itself is
 * unaffected: cov = max(core, glow), and core coverage saturates at 255
 * inside the glyph's own solid ink, so the interior stays exactly
 * neon_lit()'s colour regardless of this gain - only pixels OUTSIDE the raw
 * glyph (where core is 0 or partial) can be lifted by the glow term. */
#define NEON_GLOW_GAIN_PCT 115
/* Box-blur radius for the glow, applied twice (see neon_bake_glyph_sprites).
 * Was 3 (effective spread ~2*3=6 px into the margin); 5 spreads further
 * (~10 px) for a visibly bigger halo, still inside the 14 px margin above
 * with room to spare. */
#define NEON_GLOW_BLUR_R 5
static const char k_neon_glyph_chars[NEON_GLYPH_COUNT] = {
    '0', '1', '2', '3', '4', '5', '6', '7', '8', '9', '.', '-'
};
/* ONE coverage plane per glyph, shared by every zone.
 *
 * These were opaque RGB565 tiles, baked once per zone colour. That could not
 * work: an opaque tile paints its own black margin, so two neighbouring cells
 * could not overlap, and at the readout's cell pitch they always do - the
 * later blit erased the earlier glyph's glow and, for the widest digit pairs,
 * several columns of its actual ink. Every workaround pushed the same lever:
 * widen the cells until the black margins stopped colliding. That is what made
 * the readout too wide, and it is why the decimal had to have its glow margin
 * cropped to zero, which is what cut its halo off square at the top and sides.
 *
 * A8 removes the cause rather than trading against it. LVGL blends an
 * untransformed A8 image as a solid colour through this plane as a MASK, so
 * zero coverage contributes nothing and overlapping glows composite the way
 * light actually does. Three consequences follow: cells can be packed as
 * tightly as the ink allows, the decimal keeps a full glow margin, and the
 * plane is colour-independent - so the zone dimension disappears (~6x less
 * PSRAM) and the ink colour becomes a per-blit recolor that tracks the live
 * accent exactly instead of a value frozen at bake time. */
static void *s_neon_glyph_buf;
static lv_image_dsc_t s_neon_glyph_img[NEON_SPRITE_COUNT];
static bool s_neon_glyph_sprites_ready;
/* Memoisation, the same trick s_vault_bg_buf uses for its own expensive static
 * art: keep the baked tiles across scene switches and rebake only when an
 * input to them changes. Measured on the board, switching to neon cost ~350 ms
 * against 45-100 ms for every other theme, which is the delay that made it
 * feel like the slow one.
 *
 * The cache key is the LAYOUT plus the FONT, which it can be only because the
 * tiles are A8 coverage: they carry no colour, so a palette edit, a preset
 * change or a zone flip cannot invalidate them. Layout and font are the two
 * inputs that matter, because together they select the rendered glyphs.
 * Switching away to another theme and back is therefore free. */
static boost_neon_layout_t s_neon_sprite_layout = (boost_neon_layout_t)0xFF;
static boost_neon_font_t s_neon_sprite_font = (boost_neon_font_t)0xFF;
static bool s_neon_sprites_reused;
static int s_neon_spr_w, s_neon_spr_h;
static uint32_t s_neon_spr_stride;
/* Screen-space offset from a cell's live draw anchor (cx + cell.x, top) to
 * the sprite's top-left corner. Computed once at bake time from the same
 * centred layout lv_draw_label() already used, so a sprite blit lands on the
 * identical pixels a label draw would, plus the baked-in glow. */
static int s_neon_spr_dx, s_neon_spr_dy;
/* Per-glyph tight bbox (own ink + glow margin, NOT the full uniform tile),
 * in tile-local coordinates, shared by all 3 zones since it is pure
 * geometry. The full tile is sized to the WIDEST glyph so every character
 * shares one anchor; blitting that full tile for every cell would paint each
 * glyph's black margin over its neighbour whenever the cell pitch (as little
 * as 33 px for a '.' cell) is narrower than the tile (93/125 px) - which it
 * always is. Blitting only this tight bbox keeps each glyph's opaque paint
 * inside its own actual content, matching what the alpha-blended label draw
 * already painted (nothing outside the glyph's own ink/glow). */
static int16_t s_neon_glyph_bbox[NEON_SPRITE_COUNT][4]; /* x0,y0,x1,y1 inclusive */

/* Marquee-only pre-scaled copies of the tiles above. The active font set is
 * drawn at NEON_MARQUEE_CENTER_SCALE through LVGL's per-frame transform, which
 * host A/B measured at ~35-40% of every readout repaint (plain blit p50
 * 0.09 ms vs transform p50 0.14 ms on the same dirty regions, max 0.45 vs
 * 2.15 ms). So the marquee bake produces a second 0.87-size A8 set ONCE per
 * scene build and the live blits become plain stride-copy blends. The scaled
 * pixels are captured by running the SAME lv_draw_image transform into a
 * scratch canvas, so they are identical to what the per-frame transform used
 * to paint; each slot's bbox_s is the tile's screen-space offset from the
 * blit anchor (anchor + bbox_s), pre-baked so the blit carries no transform
 * machinery. NULL set = allocation failed, keep the per-frame transform. */
static void *s_neon_glyph_buf_s;
static lv_image_dsc_t s_neon_glyph_img_s[NEON_SPRITE_COUNT];
static int16_t s_neon_glyph_bbox_s[NEON_SPRITE_COUNT][4];

/* Segments layout only: colour-independent A8 coverage for each segment's
 * three lit bands (halo/body/cap), baked at scene build so a changed segment
 * repaints as three recolored blits instead of three lv_draw_arc primitives.
 * Each tile is cropped to that band's actual painted extent (ink bbox of the
 * arc rendered in white, plus its AA fringe) and positioned by the offset
 * from the face centre to the tile's top-left corner - so a blit at
 * (px_icx() + off_x, px_icy() + off_y) lands on the exact pixels the arc
 * rasterized, at any burn-in shift. Coverage carries no colour, so the ink is
 * a per-blit recolor like the glyph tiles. A NULL data pointer means that
 * band has no tile and the segment falls back to the live arcs.
 *
 * The buffer is a sibling of the glyph cache and shares its lifecycle:
 * freed in neon_free_glyph_sprites() (which runs only from the scene-build
 * path, after destroy_scene() has drained draw units), so it outlives every
 * draw callback that references it. */
typedef struct {
    lv_image_dsc_t img;
    int16_t off_x, off_y;
} neon_seg_band_tile_t;
static neon_seg_band_tile_t s_neon_seg_tile[NEON_NSEG][3];
static void *s_neon_seg_buf;
static bool s_neon_seg_sprites_ready;
/* Tube layout only, same shape as the segment tiles: a_zero-aligned wedges,
 * direction 0 counterclockwise (boost side), 1 clockwise (vacuum side). */
#define NEON_TUBE_TILES NEON_NSEG
static neon_seg_band_tile_t s_neon_tube_tile[2][NEON_TUBE_TILES][4];
static void *s_neon_tube_buf;
static bool s_neon_tube_sprites_ready;
static lv_area_t s_neon_tube_box[2][NEON_TUBE_TILES];
/* Tube layout only: one radial-gradient image PER ZONE COLOUR, drawn by a
 * single lv_draw_arc with img_src instead of the three live band arcs. The
 * image is a square of the three abutting bands (dim, body, white cap) baked
 * from the exact same arc geometry as the live arcs, so the zone-flip
 * recolor - which re-rasterises the whole run - costs one arc mask pass
 * instead of three (~3x less raster), and every normal tube frame costs one
 * arc too. ALL THREE zone images are baked at scene build so a zone flip
 * only SWITCHES the image - rebuilding on the flip frame would re-pay the
 * three full-ring rasterisations that this feature exists to avoid. */
#define NEON_GRAD_ZONES 3
static void *s_neon_grad_buf[NEON_GRAD_ZONES];
static lv_image_dsc_t s_neon_grad_img[NEON_GRAD_ZONES];
static uint32_t s_neon_grad_key[NEON_GRAD_ZONES];
/* Window padding around the band bbox when rendering the arc for extraction:
 * the rasteriser can paint its AA fringe a pixel or so outside
 * lv_draw_arc_get_area()'s trig-table bound, and the crop is taken from the
 * ACTUAL painted ink, so this only has to be generous enough that nothing
 * reaches the scratch edge. */
#define NEON_SEG_SPR_MARGIN 6
/* Clip-skip box inflation: the arcs' AA fringe paints ~1-2 px past the wedge
 * and the end corner reaches sin(step)*(R-rin) beyond the geometric bbox
 * (5 px for the 54-deep band). 8 px covers both so a segment whose fringe
 * falls inside a dirty region is submitted and repaints it. */
#define NEON_BAND_SPR_MARGIN 8
/* The segments' three bands' geometry, one source for the bake and the blit
 * path so they cannot drift from each other (or from the constants the
 * fallback arcs still spell out inline). Index order inner, body, cap - the
 * draw order. The inner halo (NEON_SEG_HALO_W 20) is narrower than the body
 * (25) - the user asked for it shorter than the middle band - so the bands
 * abut 20:25:6. The tube has its own four-band table below. */
typedef struct { int radius; int width; } neon_seg_band_geom_t;
static const neon_seg_band_geom_t k_neon_seg_band_geom[3] = {
    { NEON_R - NEON_SEG_W + 1, NEON_SEG_HALO_W },          /* inner (halo, shorter than body) */
    { NEON_R - NEON_CAP_W + 1, NEON_SEG_W - NEON_CAP_W + 1 },    /* body  */
    { NEON_R, NEON_CAP_W },                                      /* cap   */
};
/* The tube's four bands' geometry, one source for the bake, the gradient
 * image and the blit path so they cannot drift from each other (or from the
 * constants the fallback arcs still spell out inline). Index order inner to
 * outer - the draw order. The halo stays NEON_TUBE_HALO_W, the track is split
 * into two equal halves, and the cap is skinny at NEON_R again. */
static const neon_seg_band_geom_t k_neon_tube_band_geom[4] = {
    { NEON_TUBE_HALO_R, NEON_TUBE_HALO_W },                 /* inner dark halo */
    { NEON_TUBE_TRACK_INNER_R, NEON_TUBE_TRACK_HALF },      /* track inner half */
    { NEON_TUBE_TRACK_OUTER_R, NEON_TUBE_TRACK_HALF },      /* track outer half */
    { NEON_R, NEON_CAP_W },                                 /* cap (skinny)    */
};

/* The zone word (VACUUM / ATMO / BOOST / OVERBOOST) gets the same treatment.
 *
 * It was a plain lv_label, so it was the one lit element on the face with no
 * glow at all - flat next to a readout that blooms. It cannot simply be given
 * one: LVGL has no text glow, and stamping the label at offsets reads as
 * fringing. Baking it through the glyphs' own blur is the same trick, and at
 * this size it is nearly free (four words, one byte per pixel, ~92 KB).
 *
 * Drawn from the face's draw callback rather than as a child object, because
 * a glow has to composite against the face beneath it. That means this code
 * owns its own invalidation on a zone flip - see update_neon(). Indexed by
 * neon_word_id(). */
#define NEON_WORD_COUNT 4
#define NEON_WORD_W 320
#define NEON_WORD_H 72
/* The layout box the word is centred in, unchanged from the lv_label it
 * replaced - the bake records its crop offsets against this box, so the two
 * have to agree. */
#define NEON_WORD_BOX_W 300
#define NEON_WORD_BOX_H 34
/* Centre of the zone word, off face centre. One value for every layout now:
 * marquee shares the ring layouts' readout metrics, so the word sits at the
 * same height on all three faces. Upward clearance is to the ring's inner
 * glow edge at radius 174 on the ring layouts, and to the innermost bulb
 * ring's inner edge (188) on marquee - "OVERBOOST" is the widest word at
 * ~200 px of ink, so its top corners sit sqrt(100^2 + 112^2) = 150 from
 * centre, ~24 px clear either way. */
#define NEON_WORD_Y (-95)
static const char *const k_neon_zone_words[NEON_WORD_COUNT] = {
    "VACUUM", "ATMO", "BOOST", "OVERBOOST"
};
static void *s_neon_word_buf;
static lv_image_dsc_t s_neon_word_img[NEON_WORD_COUNT];
/* Offset from the word box's own left/top corner to the tile's, per word -
 * each word is cropped to its own ink, so unlike the glyphs they do not share
 * one anchor. */
static int16_t s_neon_word_dx[NEON_WORD_COUNT], s_neon_word_dy[NEON_WORD_COUNT];
static bool s_neon_words_ready;
/* Which word was last painted, so a zone flip can invalidate exactly once. */
static int s_neon_word_drawn = -1;

static int neon_glyph_index(char ch)
{
    for (int i = 0; i < NEON_GLYPH_COUNT; ++i) {
        if (k_neon_glyph_chars[i] == ch) return i;
    }
    return -1;
}

/* Every glyph gets the full margin, the decimal included.
 *
 * The decimal used to be forced to 0 because its tile is the one most boxed in
 * by its neighbours, and while the tiles were opaque a margin there meant its
 * black surround erased the adjacent digits' ink. But cropping the margin does
 * not remove the glow the bake already blurred INTO it - it just cuts that
 * glow off square at the ink bbox, which is the hard edge visible along the
 * decimal's top and sides. With A8 coverage there is nothing to erase, so the
 * margin is uniform and the falloff simply runs out on its own. */
static inline int neon_glyph_glow_margin(int gi)
{
    (void)gi;
    return NEON_SPR_GLOW_MARGIN;
}
#endif /* BOOST_NEON_GLYPH_SPRITES */

static void paint_neon_background(lv_obj_t *canvas, const boost_theme_t *theme);
static void neon_inv_span(float a0, float a1);
static int neon_seg_index(float angle);
static void neon_inv_seg(int index);
static void draw_neon_live(lv_event_t *e);
static void build_neon(lv_obj_t *scr);
static void update_neon(const boost_sample_t *sample, const boost_theme_t *theme);
static lv_color_t c(uint32_t rgb);
static uint32_t lerp_rgb(uint32_t a, uint32_t b, float t);
static uint32_t neon_hsl_lighten(uint32_t rgb, float d_light);
static float clampf(float v, float lo, float hi);
static uint32_t scale_rgb(uint32_t rgb, float k);
/* The approved look is the mockup's BLOOMED appearance, not the raw palette
 * value: an additive gaussian lifts a #8B3DFF segment to about (255,113,255).
 * Everything lit on this face goes through here, so the ring, the readout and
 * the zone word bloom by the same amount. The palette entry stays the base the
 * bloom is derived from, so the colour editor still means what it says. */
/* Gain measured off the mockups, not guessed: sampling the readout ink for all
 * three zones gives 1.64, 1.63 and 1.67 on every channel that is not already
 * saturated, with saturated channels staying at 255 and zero channels at 0.
 * One multiplicative gain with clamping therefore reproduces the whole set.
 *
 * Clamped locally rather than via scale_rgb(), which does NOT clamp: at gain
 * 1.65 a channel already at 255 computes to 421 and the shift-OR folds it back
 * to 165, so boost and overboost came out darker instead of brighter. */
/* 1.65 reproduced the mockup's measured ink exactly, but the mockup also had a
 * gaussian bloom bleeding light between the segments, which this pipeline
 * cannot draw. Pushed past the measured value deliberately: the extra gain and
 * a saturation lift stand in for the light we are not spreading. Saturation is
 * applied about luma so hues open up rather than just clipping to white. */
#define NEON_BLOOM 1.92f
#define NEON_SAT   1.30f
/* How much of the gain that overflows 255 comes back as WHITE.
 *
 * This is the third attempt at handling overflow, and the first that does not
 * have to trade one defect for the other:
 *
 *   per-channel clip - every saturated palette entry pinned to the same corner
 *     of the colour cube, so vacuum, boost and overboost converged on nearly
 *     the same post-bloom colour. That was the original complaint.
 *   proportional scale - divides the whole vector by 255/peak, which preserves
 *     hue and fixed the convergence, but for a saturated colour that factor is
 *     about 0.46, so it hands back ALL the gain. The "bloomed" body came out
 *     DARKER than the raw palette halo behind it (overboost measured
 *     (255,85,0) against a raw (255,106,0)), and the ring's three bands
 *     collapsed into one flat colour. That was the two-tone going missing.
 *
 * Both treat overflow as something to squash. Real bloom does not: light past
 * full scale desaturates toward white. So normalise to peak 255 - keeping the
 * hue the proportional clamp got right - and then lift what was clipped back in
 * as a blend toward white, by the FRACTION of the gain that was lost
 * (1 - 255/peak). A colour that barely overflows stays its own hue; one that
 * overflows hard reads as a hot, whitened version of itself. The body ends up
 * clearly lighter than the unbloomed halo on every palette entry, which is what
 * makes the band structure read, while the hue stays distinct per zone, which
 * is what keeps the zones apart.
 *
 * Kept small (0.35) because it is NOT carrying the band structure on its own -
 * NEON_HALO_DIM below does that. Its only job here is to make the bloom
 * actually brighten: measured over all four palettes, the body's luminance now
 * exceeds the raw palette's in every zone, where the bare proportional clamp
 * had it lower in 11 of 12. Larger values buy contrast at the cost of zone
 * separation (at 0.75 the four palettes' worst zone pair falls from 158 to
 * 113), and separation is the thing that was hard to win back. */
#define NEON_WHITE_LIFT 0.35f
/* The ring's inner band is a DIMMED zone colour, not the raw palette entry.
 *
 * The three bands are meant to read dark -> bright -> white from the inside
 * out. They stopped doing that when neon_lit() started clamping
 * proportionally: for a saturated palette entry that divides the whole vector
 * by about 0.46, which made the "bloomed" body DARKER than the raw palette
 * colour drawn behind it. Measured across the four palettes, the ordering was
 * inverted in 11 of 12 zones - so the ring was not merely low-contrast, its
 * gradient ran backwards, which is what collapsed it into one flat colour on
 * the panel.
 *
 * Dimming the inner band fixes the ordering at its source and costs nothing in
 * zone separation, because it scales a colour rather than reshaping it. 0.55
 * matches the factor the marquee's accent bulbs already use for the same
 * "dimmed zone colour" job. Worst-case halo-to-body contrast over all four
 * palettes goes from 4 to 125. */
#define NEON_HALO_DIM 0.55f
static inline uint32_t neon_lit(uint32_t rgb)
{
    float r = (float)((rgb >> 16) & 0xFFu);
    float g = (float)((rgb >> 8) & 0xFFu);
    float b = (float)(rgb & 0xFFu);
    const float luma = 0.299f * r + 0.587f * g + 0.114f * b;
    r = (luma + (r - luma) * NEON_SAT) * NEON_BLOOM;
    g = (luma + (g - luma) * NEON_SAT) * NEON_BLOOM;
    b = (luma + (b - luma) * NEON_SAT) * NEON_BLOOM;
    r = clampf(r, 0.0f, 1.0e9f);
    g = clampf(g, 0.0f, 1.0e9f);
    b = clampf(b, 0.0f, 1.0e9f);
    const float peak = fmaxf(r, fmaxf(g, b));
    if (peak > 255.0f) {
        const float scale = 255.0f / peak;
        r *= scale;
        g *= scale;
        b *= scale;
        const float w = (1.0f - scale) * NEON_WHITE_LIFT;
        r += (255.0f - r) * w;
        g += (255.0f - g) * w;
        b += (255.0f - b) * w;
    }
    return ((uint32_t)lroundf(r) << 16) | ((uint32_t)lroundf(g) << 8)
         | (uint32_t)lroundf(b);
}

/* The tube's lit run is white + three tones, one colour per band (index order
 * inner to outer): dim halo, bloomed body, then the track's OUTER half
 * LIGHTENED via HSL lightness (hue and saturation preserved) - the band stack
 * must read as a smooth gradient dark -> bloomed -> lighter -> white, so the
 * outer half goes lighter than the middle, never darker (a deeper outer turns
 * the stack into a dark-bright-dark sandwich). One function feeds the live
 * arcs, the gradient bake and the tile blits so they cannot drift. */
static uint32_t neon_tube_band_color(uint32_t accent_rgb, int band)
{
    const uint32_t mid = scale_rgb(neon_lit(accent_rgb), NEON_TUBE_MID_SCALE);
    switch (band) {
        case 0: return scale_rgb(accent_rgb, NEON_HALO_DIM);
        case 1: return mid;
        case 2: return neon_hsl_lighten(mid, NEON_TUBE_TRACK_LIGHT);
        default: return 0xFFFFFFu;
    }
}

/* HSL hue-to-rgb component (the standard p/q/t algorithm). `t` may wrap. */
static float neon_hsl_hue2rgb(float p, float q, float t)
{
    if (t < 0.0f) t += 1.0f;
    if (t > 1.0f) t -= 1.0f;
    if (t < 1.0f / 6.0f) return p + (q - p) * 6.0f * t;
    if (t < 0.5f) return q;
    if (t < 2.0f / 3.0f) return p + (q - p) * (2.0f / 3.0f - t) * 6.0f;
    return p;
}

/* Raise a colour's HSL lightness by d_light, keeping hue AND saturation. This
 * is how the tube's outer track half is made lighter than the bloomed middle
 * without washing it out: the rejected white-lift desaturated toward the cap,
 * which is what read as "too pale" and is also why a fixed lerp cannot work
 * for every user colour. Lightness is (max+min)/2, so a saturated colour still
 * has room to brighten even when one channel is already 255. Pure black/white
 * have no hue and just scale to the same neutral. */
static uint32_t neon_hsl_lighten(uint32_t rgb, float d_light)
{
    const float r = (float)((rgb >> 16) & 0xFFu) / 255.0f;
    const float g = (float)((rgb >> 8) & 0xFFu) / 255.0f;
    const float b = (float)(rgb & 0xFFu) / 255.0f;
    const float mx = fmaxf(r, fmaxf(g, b));
    const float mn = fminf(r, fminf(g, b));
    const float d = mx - mn;
    float h = 0.0f, s = 0.0f;
    const float l = (mx + mn) * 0.5f;
    if (d > 0.0f) {
        s = (l > 0.5f) ? d / (2.0f - mx - mn) : d / (mx + mn);
        if (mx == r) h = (g - b) / d + (g < b ? 6.0f : 0.0f);
        else if (mx == g) h = (b - r) / d + 2.0f;
        else h = (r - g) / d + 4.0f;
        h *= 60.0f;
    }
    const float nl = clampf(l + d_light, 0.0f, 1.0f);
    const float q = (nl < 0.5f) ? nl * (1.0f + s) : nl + s - nl * s;
    const float p = 2.0f * nl - q;
    const float hk = h / 360.0f;
    const int nr = (int)lroundf(neon_hsl_hue2rgb(p, q, hk + 1.0f / 3.0f) * 255.0f);
    const int ng = (int)lroundf(neon_hsl_hue2rgb(p, q, hk) * 255.0f);
    const int nb = (int)lroundf(neon_hsl_hue2rgb(p, q, hk - 1.0f / 3.0f) * 255.0f);
    return ((uint32_t)nr << 16) | ((uint32_t)ng << 8) | (uint32_t)nb;
}
static uint32_t neon_zone_rgb(const boost_theme_t *t, float psi);
static float s_psi_min;
static float s_psi_max;
static inline int32_t px_icx(void);
static inline int32_t px_icy(void);
static const boost_theme_t *active_theme(void);
static float psi_to_sweep(float psi, float a0, float a1);
static lv_color_t color_for_psi(const boost_theme_t *theme, float psi);
static bool clip_reaches_radius(lv_layer_t *layer, float cx, float cy, float r);
static float s_display_psi;
static float s_peak_psi;
static float s_psi_overboost = DEFAULT_PSI_OVERBOOST;

/* x of a psi value along marquee's bar, mapped through the SAME rule the ring
 * layouts use. Feeding psi_to_sweep() a 0..width range instead of an angular one
 * makes the bar inherit zeroAngle, psiMin and psiMax from the settings exactly
 * as the arc does: a plain min..max lerp put zero at 60% of the bar while the
 * ring put it at 37.5%, so the two layouts disagreed about where zero was. */
static int neon_bar_x(int cx, float psi)
{
    const int half = neon_mq(NEON_BAR_HALF);
    return cx - half + (int)lroundf(psi_to_sweep(psi, 0.0f, (float)(half * 2)));
}

/* Bulb colour. The mockup dims the zone colour to 55% for the border so it
 * frames the readout instead of competing with it; the bloom then lifts it
 * back to roughly the palette value. Now baked into each of the three rings
 * with the ring's own zone colour. */
static uint32_t neon_bulb_accent(uint32_t accent_rgb)
{
    return neon_lit(scale_rgb(accent_rgb, 0.55f));
}

/* Centre of the i-th bulb of ring z (0 = innermost/vacuum .. 2 =
 * outermost/overboost). One place, so the bake, the live draw and the
 * invalidation cannot disagree about where the rings are.
 *
 * The offsets are precomputed once into s_neon_bulb_ox/oy (the -90 deg
 * offset puts bulb 0 at 12 o'clock on a y-down screen; every ring count is
 * even, so bulb N/2 lands exactly at 6 o'clock too). Computing lroundf(cos/sin)
 * per call made the live accent scan pay two trig calls and a rounding for
 * every accent bulb on every callback invocation - the table keeps the
 * arithmetic bit-identical but turns the call into one table load. */
static void neon_bulb_pos(int cx, int cy, int z, int i, int *bx, int *by)
{
    if (!s_neon_bulb_table_ready) {
        for (int tz = 0; tz < NEON_BULB_RINGS; ++tz) {
            const float r = (float)NEON_BULB_RING_R(tz);
            for (int ti = 0; ti < NEON_BULB_N(tz); ++ti) {
                const float rad = ((float)ti * (360.0f / (float)NEON_BULB_N(tz))
                                   - 90.0f) * (float)M_PI / 180.0f;
                s_neon_bulb_ox[tz][ti] = (int16_t)lroundf(cosf(rad) * r);
                s_neon_bulb_oy[tz][ti] = (int16_t)lroundf(sinf(rad) * r);
            }
        }
        s_neon_bulb_table_ready = true;
    }
    *bx = cx + s_neon_bulb_ox[z][i];
    *by = cy + s_neon_bulb_oy[z][i];
}

/* Bounding box of every ring segment at its widest stroke, in screen
 * coordinates. Built once at scene build.
 *
 * The draw callback runs once per DIRTY REGION, and it used to submit the whole
 * lit run every time - so a frame with three dirty regions and a 28-segment run
 * issued 28 x 3 x 3 = 252 arc primitives, of which all but a handful were
 * outside the region being repainted and got thrown away downstream. Measured
 * before this existed: 28.8 segments per cycle mean, 84 max. Tube and segments
 * flush byte-identical pixel counts, yet tube ran at 41 FPS against segments'
 * 22 on hardware, which isolates the cost to the primitive count rather than to
 * the fill. */
static lv_area_t s_neon_seg_box[NEON_NSEG];
static bool s_neon_seg_box_ready;

/* Local rather than LVGL's lv_area_is_on(), which lives in lv_area_private.h. */
static inline bool neon_area_overlaps(const lv_area_t *a, const lv_area_t *b)
{
    return a->x1 <= b->x2 && a->x2 >= b->x1 && a->y1 <= b->y2 && a->y2 >= b->y1;
}

static void neon_build_seg_boxes(void)
{
    for (int i = 0; i < NEON_NSEG; ++i) {
        const float s = neon_seg_start(i);
        lv_draw_arc_get_area(px_icx(), px_icy(), (uint16_t)NEON_R,
                             s, s + NEON_SEG_LIT,
                             (uint16_t)NEON_SEG_BAND_DEPTH,
                             false, &s_neon_seg_box[i]);
        /* Inflate by NEON_BAND_SPR_MARGIN so a dirty region that reaches only
         * the segment's AA fringe (the angle mask paints ~1-2 px past the
         * wedge's end edge, and the end corner reaches sin(step)*(R-rin)
         * beyond the bbox) still overlaps the box and the segment is
         * submitted. Without this, a neighbouring segment's region repaints
         * the canvas over the fringe and strands it: the canvas's track
         * fringe is the track colour at single-digit % coverage, which
         * RGB565 quantises to black, while the live cap arc's white fringe
         * is visible - so the partial pipeline showed black where the truth
         * showed the lit fringe. */
        s_neon_seg_box[i].x1 -= NEON_BAND_SPR_MARGIN;
        s_neon_seg_box[i].y1 -= NEON_BAND_SPR_MARGIN;
        s_neon_seg_box[i].x2 += NEON_BAND_SPR_MARGIN;
        s_neon_seg_box[i].y2 += NEON_BAND_SPR_MARGIN;
    }
    s_neon_seg_box_ready = true;
}

static void paint_neon_background(lv_obj_t *canvas, const boost_theme_t *theme)
{
    lv_layer_t layer;
    lv_canvas_init_layer(canvas, &layer);
    lv_draw_rect_dsc_t bg;
    lv_draw_rect_dsc_init(&bg);
    bg.bg_color = lv_color_black();
    bg.bg_opa = LV_OPA_COVER;
    lv_area_t full = { 0, 0, DISP_SIZE - 1, DISP_SIZE - 1 };
    lv_draw_rect(&layer, &bg, &full);
    const int cx = px_icx() - s_px_dx;
    const int cy = px_icy() - s_px_dy;
    lv_draw_arc_dsc_t arc;
    lv_draw_arc_dsc_init(&arc);
    arc.center.x = cx; arc.center.y = cy; arc.radius = NEON_R;
    arc.rounded = false; arc.opa = LV_OPA_COVER;
    /* The zero marker is the zero segment itself, painted white, rather than a
     * tick outside the ring. It reads at a glance and costs nothing extra. */
    const int zero_seg = neon_seg_index(psi_to_sweep(0.0f, (float)ARC_START,
                                                     (float)(ARC_START + ARC_RANGE)));
    if (s_neon_layout == BOOST_NEON_MARQUEE) {
        lv_draw_rect_dsc_t bulb;
        lv_draw_rect_dsc_init(&bulb);
        bulb.radius = LV_RADIUS_CIRCLE;
        bulb.bg_opa = LV_OPA_COVER;
        /* All three rings are baked as DEAD track: every one of the 216
         * bulbs is dim neutral in the background. The coloured accents are
         * drawn LIVE in draw_neon_live() - ring z's 24 accent bulbs light in
         * ring z's zone colour only when the reading has reached that zone
         * (see NEON_BULB_IS_ACCENT / the stage-ladder comment). Baking them
         * track means a zone flip repaints only the changed rings' 12
         * pair-boxes instead of the whole border, and the two-tone rest
         * state (only the innermost ring coloured) comes free. */
        for (int z = 0; z < NEON_BULB_RINGS; ++z) {
            for (int i = 0; i < NEON_BULB_N(z); ++i) {
                bulb.bg_color = c(theme->track);
                int bx, by;
                neon_bulb_pos(cx, cy, z, i, &bx, &by);
                lv_area_t a = { bx - NEON_BULB_HALF, by - NEON_BULB_HALF,
                                bx + NEON_BULB_HALF, by + NEON_BULB_HALF };
                lv_draw_rect(&layer, &bulb, &a);
            }
        }
        lv_draw_rect_dsc_t track;
        lv_draw_rect_dsc_init(&track);
        track.radius = 8; track.bg_opa = LV_OPA_COVER; track.bg_color = c(theme->track);
        lv_area_t bar = { cx - neon_mq(NEON_BAR_HALF), cy + neon_mq(NEON_BAR_Y),
                          cx + neon_mq(NEON_BAR_HALF),
                          cy + neon_mq(NEON_BAR_Y) + neon_mq(NEON_BAR_H) };
        lv_draw_rect(&layer, &track, &bar);
    } else if (s_neon_layout == BOOST_NEON_TUBE) {
        arc.start_angle = (float)ARC_START;
        arc.end_angle = (float)(ARC_START + ARC_RANGE);
        arc.color = c(theme->track);
        /* Unlit track spans the track + cap footprint (NEON_R down to the
         * halo's outer edge), a bit wider than the old body width. */
        arc.width = NEON_TUBE_TRACK_W;
        lv_draw_arc(&layer, &arc);
        const float zero = psi_to_sweep(0.0f, (float)ARC_START,
                                        (float)(ARC_START + ARC_RANGE));
        arc.start_angle = zero - NEON_TUBE_ZERO_DEG + NEON_TUBE_ZERO_CENTER;
        arc.end_angle = zero + NEON_TUBE_ZERO_DEG + NEON_TUBE_ZERO_CENTER;
        arc.color = lv_color_white();
        /* Full lit depth (NEON_TUBE_BAND_DEPTH): the zero marker is a bright
         * full-band landmark spanning the whole ring width, restored to its
         * original design (the 2026-08-12 "inside the track" request was
         * about the PEAK/max marker only - shortening the zero marker was a
         * mistake). Baked here so the marker still shows when nothing is lit
         * and the live pass never runs; the live pass in draw_neon_live()
         * redraws it on top of the run. */
        arc.width = NEON_TUBE_BAND_DEPTH;
        lv_draw_arc(&layer, &arc);
    } else for (int i = 0; i < NEON_NSEG; ++i) {
        arc.start_angle = neon_seg_start(i);
        arc.end_angle = arc.start_angle + NEON_SEG_LIT;
        /* The zero marker is drawn at the LIT width so it has the same
         * length and shape as a coloured segment and reads as a marker
         * rather than as a brighter piece of track. */
        arc.color = (i == zero_seg) ? lv_color_white() : c(theme->track);
        arc.width = (i == zero_seg) ? NEON_SEG_BAND_DEPTH : NEON_SEG_W;
        lv_draw_arc(&layer, &arc);
    }
    /* No scale numerals. Inside the ring the lit segments' inner band reaches
     * over them; outside, a 466 px round panel puts them under the bezel. The
     * SCALE ITSELF is unchanged - the lit run is still mapped through
     * psi_to_sweep(), so zeroAngle, psiMin and psiMax from the settings drive
     * it exactly as they drive every other face. Only the numerals are gone. */
    /* (Numerals were removed rather than left disabled: any future revival must
     * re-check the ring-bezel clearance measured when they were dropped.) */

    /* Hairline rule between the unit mark and the peak readout. It never
     * moves, so it is baked rather than drawn live. */
    lv_draw_rect_dsc_t rule;
    lv_draw_rect_dsc_init(&rule);
    rule.bg_color = c(theme->muted);
    rule.bg_opa = LV_OPA_COVER;
    /* Same offset from the unit mark and the peak on every layout; the lower
     * stack sits at one rhythm everywhere now. */
    const int rule_y = cy + neon_mq(NEON_RULE_Y);
    const int rule_half = neon_mq(62);
    lv_area_t ra = { cx - rule_half, rule_y, cx + rule_half, rule_y + 1 };
    lv_draw_rect(&layer, &rule, &ra);

    lv_canvas_finish_layer(canvas, &layer);
}

/* The ONE place the neon zone colour is decided. Drawing and flip detection
 * must agree: the colour is chosen here and flips are detected here. Using
 * color_for_psi() for the flip test while drawing from a different threshold
 * set left the readout recolouring at 0.05 psi with nothing invalidated. */
static uint32_t neon_zone_rgb(const boost_theme_t *t, float psi)
{
    return (psi >= s_psi_overboost) ? t->overboost
         : (psi > 0.05f) ? t->boost : t->vacuum;
}

/* The peak tell-tale's fixed ink, shared by the tube and segments layouts:
 * the DARKER of the vacuum state's inner-ring colours (scale_rgb(vacuum,
 * NEON_HALO_DIM) - the same dim factor the halo band uses). Deliberately NOT
 * the peak value's zone colour: a marker in the live zone colour stood out
 * jarringly against the track and re-tinted every time the peak crossed a
 * zone threshold. The constant vacuum tone makes the marker read as a
 * reference mark rather than as another lit band, and it never restyles, so
 * its invalidation has no colour-flip case. */
static uint32_t neon_peak_color(const boost_theme_t *t)
{
    return scale_rgb(t->vacuum, NEON_HALO_DIM);
}

/* Draw-cost counters. The audit measures FLUSHED pixels, which is the dirty
 * area and says nothing about how much rasterisation happened inside it. These
 * count the work instead: how many times the callback ran per render cycle (one
 * per dirty region) and how many arc primitives it submitted. Compiled out
 * unless BOOST_NEON_DRAW_STATS is defined. */
#if BOOST_NEON_DRAW_STATS
uint32_t g_neon_cb_calls;
uint32_t g_neon_arcs;
uint32_t g_neon_arcs_clipped;
uint32_t g_neon_labels;
uint32_t g_neon_sign_bars;
uint32_t g_neon_sprite_blits;
#define NEON_STAT_CB()      (g_neon_cb_calls++)
#define NEON_STAT_ARC()     (g_neon_arcs++)
#define NEON_STAT_SKIP()    (g_neon_arcs_clipped++)
#define NEON_STAT_LABEL()   (g_neon_labels++)
#define NEON_STAT_SIGN()    (g_neon_sign_bars++)
#define NEON_STAT_SPRITE()  (g_neon_sprite_blits++)
#else
#define NEON_STAT_CB()      ((void)0)
#define NEON_STAT_ARC()     ((void)0)
#define NEON_STAT_SKIP()    ((void)0)
#define NEON_STAT_LABEL()   ((void)0)
#define NEON_STAT_SIGN()    ((void)0)
#define NEON_STAT_SPRITE()  ((void)0)
#endif

#if BOOST_NEON_GLYPH_SPRITES
/* Mirrors the two-tier threshold in neon_zone_rgb() exactly. Kept as its own
 * one-line function, rather than refactoring neon_zone_rgb() to share it, so
 * the existing (already relied upon) function is not touched by this work.
 * Lives OUTSIDE the sprite guard: the marquee's live accent bulbs and the
 * live accent bulbs call it, and those bulbs are drawn with plain lv_draw_rect
 * whether or not glyph sprites exist. */
#endif
static inline int neon_zone_id(float psi)
{
    return (psi >= s_psi_overboost) ? 2 : (psi > 0.05f) ? 1 : 0;
}

/* ATMO is a display-only word around zero. It deliberately does not add a
 * fourth colour stage: the readout, rings and marquee keep their established
 * vacuum/boost/overboost thresholds and cadence behaviour. */
static inline int neon_word_id(float psi)
{
    if (psi >= s_psi_overboost) return 3;
    if (psi >= 0.35f) return 2;
    if (psi > -0.35f) return 1;
    return 0;
}

static inline uint32_t neon_word_rgb(const boost_theme_t *theme, float psi)
{
    return neon_word_id(psi) == 1 ? theme->text : neon_zone_rgb(theme, psi);
}
#if BOOST_NEON_GLYPH_SPRITES

static void neon_free_glyph_sprites(void)
{
    if (s_neon_glyph_buf != NULL) {
        BG_FREE(s_neon_glyph_buf);
        s_neon_glyph_buf = NULL;
    }
    memset(s_neon_glyph_img, 0, sizeof(s_neon_glyph_img));
    if (s_neon_glyph_buf_s != NULL) {
        BG_FREE(s_neon_glyph_buf_s);
        s_neon_glyph_buf_s = NULL;
    }
    memset(s_neon_glyph_img_s, 0, sizeof(s_neon_glyph_img_s));
    memset(s_neon_glyph_bbox_s, 0, sizeof(s_neon_glyph_bbox_s));
    s_neon_glyph_sprites_ready = false;
    s_neon_sprite_layout = (boost_neon_layout_t)0xFF;
    /* Segment band tiles are layout-independent but kept only while the
     * segments layout is active; dropping them here (the same scene-build-only
     * path) keeps them from eating PSRAM on the tube/marquee faces. */
    if (s_neon_seg_buf != NULL) {
        BG_FREE(s_neon_seg_buf);
        s_neon_seg_buf = NULL;
    }
    memset(s_neon_seg_tile, 0, sizeof(s_neon_seg_tile));
    s_neon_seg_sprites_ready = false;
    /* Tube run tiles: a_zero-dependent, so kept only while the tube layout is
     * active; same lifecycle rule as the segment tiles. */
    if (s_neon_tube_buf != NULL) {
        BG_FREE(s_neon_tube_buf);
        s_neon_tube_buf = NULL;
    }
    memset(s_neon_tube_tile, 0, sizeof(s_neon_tube_tile));
    memset(s_neon_tube_box, 0, sizeof(s_neon_tube_box));
    s_neon_tube_sprites_ready = false;
    /* Tube radial-gradient arc image. Same lifecycle as the tube tiles:
     * scene-build-only, freed here so it does not eat PSRAM on the
     * segments/marquee faces. */
    for (int z = 0; z < NEON_GRAD_ZONES; ++z) {
        if (s_neon_grad_buf[z] != NULL) {
            BG_FREE(s_neon_grad_buf[z]);
            s_neon_grad_buf[z] = NULL;
        }
    }
    memset(s_neon_grad_img, 0, sizeof(s_neon_grad_img));
    memset(s_neon_grad_key, 0, sizeof(s_neon_grad_key));
}

/* Deliberately does NOT touch the zone-word tiles. They are baked once and
 * never freed or rebaked: nothing they depend on can change at runtime - three
 * fixed strings, one fixed font, one fixed box - and coverage carries no
 * colour, so not even a palette change reaches them. There is no free
 * counterpart for them on purpose; a function that is never called would just
 * be dead code claiming otherwise. */

/* Top-left corner of the box the zone word is laid out in. The word used to
 * be a 300x34 lv_label aligned to the face centre with a per-layout y offset;
 * keeping that exact box means the bake's recorded offsets place the sprite
 * on the same pixels the label occupied. */
static void neon_word_box_origin(int cx, int cy, int *x, int *y)
{
    *x = cx - NEON_WORD_BOX_W / 2;
    *y = cy + NEON_WORD_Y - NEON_WORD_BOX_H / 2;
}

/* Separable box blur over an 8-bit coverage plane, in place. w and h are
 * bounded well under 256 by every caller (largest tile in use is the
 * marquee's padded coverage window), so a fixed on-stack scratch row is
 * enough - no per-call heap traffic in a routine run 3 zones x 12 glyphs x
 * 2 passes per scene build.
 *
 * Sliding-window running sum, not a re-summed kernel per pixel: the naive
 * form re-adds all (2r+1) samples at every x, which is O(w*r) per row and
 * got directly more expensive when NEON_GLOW_BLUR_R grew from 3 to 5. This
 * carries one running sum/count across the row (or column), adding the pixel
 * entering the window and dropping the one leaving it, which is O(w)
 * regardless of r - the result is bit-for-bit the same box average, just
 * without recomputing it from scratch every step. */
/* Sized for the widest thing blurred, which is no longer a glyph tile (~132)
 * but the zone-word scratch (360). The cost is one stack buffer of this many
 * bytes, and every caller runs at scene-build time on the display task, not
 * in a draw path - so this is 128 bytes of build-time stack, not a per-frame
 * cost. A scratch wider than this is REJECTED rather than clipped, which is
 * how the first zone-word bake failed: "words stay unglowed", silently
 * correct and visibly flat. */
#define NEON_BLUR_MAXDIM 384
static void neon_box_blur(uint8_t *cov, int w, int h, int r)
{
    if (w <= 0 || h <= 0 || w > NEON_BLUR_MAXDIM || h > NEON_BLUR_MAXDIM) return;
    uint8_t line[NEON_BLUR_MAXDIM];
    /* Horizontal pass, row by row. */
    for (int y = 0; y < h; ++y) {
        uint8_t *row = cov + (size_t)y * (size_t)w;
        int sum = 0, count = 0;
        for (int k = 0; k <= r && k < w; ++k) { sum += row[k]; count++; }
        for (int x = 0; x < w; ++x) {
            line[x] = (uint8_t)(sum / count);
            const int add = x + r + 1;
            const int drop = x - r;
            if (add < w) { sum += row[add]; count++; }
            if (drop >= 0) { sum -= row[drop]; count--; }
        }
        memcpy(row, line, (size_t)w);
    }
    /* Vertical pass, column by column. */
    for (int x = 0; x < w; ++x) {
        int sum = 0, count = 0;
        for (int k = 0; k <= r && k < h; ++k) { sum += cov[(size_t)k * (size_t)w + (size_t)x]; count++; }
        for (int y = 0; y < h; ++y) {
            line[y] = (uint8_t)(sum / count);
            const int add = y + r + 1;
            const int drop = y - r;
            if (add < h) { sum += cov[(size_t)add * (size_t)w + (size_t)x]; count++; }
            if (drop >= 0) { sum -= cov[(size_t)drop * (size_t)w + (size_t)x]; count--; }
        }
        for (int y = 0; y < h; ++y) cov[(size_t)y * (size_t)w + (size_t)x] = line[y];
    }
}

/* Zero a window of the scratch canvas directly against its backing buffer,
 * bypassing lv_draw_rect()'s style/blend dispatch for a plain opaque black
 * fill. Run up to 48 times per scene build (12 geometry-pass glyphs over the
 * whole canvas, 36 colour-pass glyphs over just the crop window - see the
 * call sites), so the dispatch overhead and, for the colour pass, the area
 * cleared both mattered. x0/y0/w/h are assumed already clamped to
 * [0, canvas width) x [0, canvas height) by the caller. */
static void neon_scratch_clear(lv_obj_t *scratch, int x0, int y0, int w, int h)
{
    lv_draw_buf_t *db = lv_canvas_get_draw_buf(scratch);
    for (int y = 0; y < h; ++y) {
        uint8_t *row = db->data + (size_t)(y0 + y) * db->header.stride + (size_t)x0 * 2u;
        memset(row, 0, (size_t)w * 2u);
    }
}

static void neon_draw_sign_pass(lv_layer_t *layer,
                                const boost_neon_bar_t bars[BOOST_NEON_SIGN_BARS],
                                uint32_t color);
static void neon_draw_dot_sign(lv_layer_t *layer, int cx, int cy, int width,
                               uint32_t color);

/* Fold one glyph's core and blurred coverage into the single 8-bit plane that
 * gets blitted, and publish the windowed image descriptor for it.
 *
 * cov = max(core, glow*gain) is unchanged from the RGB565 version - what
 * changes is that the result is stored as coverage rather than immediately
 * multiplied into an ink colour, so the ink can be chosen per blit. Inside the
 * glyph's solid ink core saturates at 255 and the gain cannot touch it, so the
 * body still reads as exactly the accent colour and only the surround glows. */
static void neon_store_coverage(int slot, const uint8_t *core, const uint8_t *glow,
                                int cov_w, int pad, int spr_w, int spr_h,
                                uint32_t spr_stride, size_t glyph_bytes)
{
    const bool use_glow = boost_theme_neon_font() != BOOST_NEON_FONT_DOTO;
    uint8_t *dst_bytes = (uint8_t *)s_neon_glyph_buf + (size_t)slot * glyph_bytes;
    for (int y = 0; y < spr_h; ++y) {
        uint8_t *dst = dst_bytes + (size_t)y * spr_stride;
        for (int x = 0; x < spr_w; ++x) {
            const int cxi = x + pad, cyi = y + pad;
            const int core_v = core[(size_t)cyi * (size_t)cov_w + (size_t)cxi];
            int glow_v = use_glow
                ? (glow[(size_t)cyi * (size_t)cov_w + (size_t)cxi] * NEON_GLOW_GAIN_PCT) / 100
                : 0;
            if (glow_v > 255) glow_v = 255;
            dst[x] = (uint8_t)(core_v > glow_v ? core_v : glow_v);
        }
    }

    /* Store the TIGHT-BBOX WINDOW, not the full tile. The tile is one uniform
     * size shared by every sprite so they can share a single anchor, but a
     * narrow glyph's tile is mostly empty, and blitting the empty part is
     * wasted fill even now that it no longer erases anything. Baking the crop
     * here means draw time never has to build a windowed descriptor on the
     * stack. */
    const int16_t *bb = s_neon_glyph_bbox[slot];
    const int bw = bb[2] - bb[0] + 1;
    const int bh = bb[3] - bb[1] + 1;
    lv_image_dsc_t *img = &s_neon_glyph_img[slot];
    memset(img, 0, sizeof(*img));
    img->header.magic = LV_IMAGE_HEADER_MAGIC;
    img->header.cf = LV_COLOR_FORMAT_A8;
    img->header.w = (uint32_t)bw;
    img->header.h = (uint32_t)bh;
    img->header.stride = spr_stride;
    img->data_size = (uint32_t)((size_t)spr_stride * (size_t)bh);
    img->data = (const uint8_t *)s_neon_glyph_buf + (size_t)slot * glyph_bytes +
                (size_t)bb[1] * spr_stride + (size_t)bb[0];
}

/* Blit one baked coverage tile as `ink`, anchored the way the live label draw
 * anchors its box. Returns false if the slot was never baked, which is the
 * caller's cue to fall back to drawing the thing live. */
static bool neon_blit_sprite_scaled(lv_layer_t *layer, int slot,
                                    int anchor_x, int anchor_y, uint32_t ink,
                                    float scale);
/* Scaled variant for the marquee: draws the SAME baked tile at scale S, so
 * the one shared sprite set serves every layout. The anchor is the cell
 * centre already scaled about the face centre (the caller scales cell.x and
 * the bake-time spr offsets by S); the bbox offsets are sprite-local and
 * must scale with them. coords is the FULL-size rect (LVGL derives the
 * transformed area from coords + scale + pivot), positioned so that the
 * transform pivot - the image centre - lands on the scaled ink centre:
 * anchor + S*bb + S*(bw/2, bh/2), i.e. gx = anchor + S*bb + (S-1)*bw/2. The
 * clip test against the full-size rect is conservative (the drawn area is
 * smaller), which is correct. */
static bool neon_blit_sprite_scaled(lv_layer_t *layer, int slot,
                                    int anchor_x, int anchor_y, uint32_t ink,
                                    float scale)
{
    /* Pre-scaled marquee set: a plain blit of the baked 0.87-size tile at
     * anchor + bbox_s. The pixels are identical to what the per-frame
     * transform used to paint (same lv_draw_image call, once at bake), so
     * this is a pure cost win with no visual change. */
    if (scale != 1.0f && s_neon_glyph_buf_s != NULL) {
        const lv_image_dsc_t *img = &s_neon_glyph_img_s[slot];
        if (img->data == NULL) return false;
        const int16_t *bb = s_neon_glyph_bbox_s[slot];
        const int bw = (int)img->header.w;
        const int bh = (int)img->header.h;
        lv_area_t a = { anchor_x + bb[0], anchor_y + bb[1],
                        anchor_x + bb[0] + bw - 1, anchor_y + bb[1] + bh - 1 };
        if (!neon_area_overlaps(&a, &layer->_clip_area)) return true;
        NEON_STAT_SPRITE();
        lv_draw_image_dsc_t idsc; lv_draw_image_dsc_init(&idsc);
        idsc.src = img;
        idsc.opa = LV_OPA_COVER;
        /* A8 source: LVGL blends `recolor` through the plane as the ink. */
        idsc.recolor = c(ink);
        idsc.recolor_opa = LV_OPA_COVER;
        lv_draw_image(layer, &idsc, &a);
        return true;
    }
    const lv_image_dsc_t *img = &s_neon_glyph_img[slot];
    if (img->data == NULL) return false;
    const int16_t *bb = s_neon_glyph_bbox[slot];
    const int bw = (int)img->header.w;
    const int bh = (int)img->header.h;
    const int gx = (int)lroundf((float)anchor_x + scale * (float)bb[0] +
                                (scale - 1.0f) * (float)bw / 2.0f);
    const int gy = (int)lroundf((float)anchor_y + scale * (float)bb[1] +
                                (scale - 1.0f) * (float)bh / 2.0f);
    lv_area_t a = { gx, gy, gx + bw - 1, gy + bh - 1 };
    if (!neon_area_overlaps(&a, &layer->_clip_area)) return true;
    NEON_STAT_SPRITE();
    lv_draw_image_dsc_t idsc; lv_draw_image_dsc_init(&idsc);
    idsc.src = img;
    idsc.opa = LV_OPA_COVER;
    /* For an A8 source LVGL blends `recolor` through the plane regardless of
     * recolor_opa, so this is the ink, not a tint applied on top of one. */
    idsc.recolor = c(ink);
    idsc.recolor_opa = LV_OPA_COVER;
    if (scale != 1.0f) {
        idsc.scale_x = idsc.scale_y = (uint16_t)lroundf(256.0f * scale);
        idsc.pivot.x = bw / 2;
        idsc.pivot.y = bh / 2;
    }
    lv_draw_image(layer, &idsc, &a);
    return true;
}

/*
 * Bake the minus mark into the same coverage pipeline as the digits.
 *
 * For SF Alien the mark cannot come from the font: that typeface's '-' has no
 * contour, so it has always been drawn as two sheared parallelogram bars from
 * boost_neon_sign_bars(). Its glow used to be faked by running that same
 * geometry a second time with every edge pushed out NEON_SIGN_GLOW px in a dim
 * colour. That does not read as glow at this scale. The bars are only ~6 px
 * tall on an ~8 px pitch, so a 5 px inflation overlapped the two bars by 8 px
 * and flooded the 2 px gap between them - the mark came out as one solid slab
 * with a slot in it, nothing like the digits beside it.
 *
 * Baking it instead means the mark gets the identical two-pass box blur the
 * digits get, so the two match by construction rather than by tuning. It is
 * drawn into the scratch canvas at the same anchor the live code uses (box
 * centre horizontally, top + line_h/2 vertically), which is what lets the blit
 * reuse the glyphs' own dx/dy mapping. Doto uses three round modules matching
 * its decimal dot, kept shorter than its wide built-in hyphen so it clears the
 * ring - same slot, same pipeline.
 */
static void neon_bake_sign_sprite(lv_obj_t *scratch, int safe_w, int safe_h,
                                  int cx0, int cy0, int bake_y,
                                  int font_px, int sign_w,
                                  const neon_font_style_t *nfs,
                                  uint8_t *core, uint8_t *glow,
                                  int cov_w, int cov_h, int pad,
                                  int spr_w, int spr_h,
                                  uint32_t spr_stride, size_t glyph_bytes)
{
    const lv_font_t *font = nfs->font;
    const int line_h = (int)lv_font_get_line_height(font);

    lv_layer_t layer;
    lv_canvas_init_layer(scratch, &layer);
    neon_scratch_clear(scratch, 0, 0, safe_w, safe_h);
    if (nfs->sign_is_dots) {
        neon_draw_dot_sign(&layer, safe_w / 2, bake_y + line_h / 2,
                           sign_w, 0xFFFFFFu);
    } else {
        boost_neon_bar_t bars[BOOST_NEON_SIGN_BARS];
        boost_neon_sign_bars(safe_w / 2, bake_y + line_h / 2,
                             font_px, sign_w, bars);
        neon_draw_sign_pass(&layer, bars, 0xFFFFFFu);
    }
    lv_canvas_finish_layer(scratch, &layer);

    const lv_draw_buf_t *db = lv_canvas_get_draw_buf(scratch);
    memset(core, 0, (size_t)cov_w * (size_t)cov_h);
    int ix0 = safe_w, iy0 = safe_h, ix1 = -1, iy1 = -1;
    for (int y = 0; y < cov_h; ++y) {
        const int sy = cy0 - pad + y;
        if (sy < 0 || sy >= safe_h) continue;
        const lv_color16_t *row =
            (const lv_color16_t *)(db->data + (size_t)sy * db->header.stride);
        for (int x = 0; x < cov_w; ++x) {
            const int sx = cx0 - pad + x;
            if (sx < 0 || sx >= safe_w) continue;
            const uint8_t v = (uint8_t)(row[sx].red * 255 / 31);
            core[(size_t)y * (size_t)cov_w + (size_t)x] = v;
            if (v) {
                if (sx < ix0) ix0 = sx;
                if (sx > ix1) ix1 = sx;
                if (sy < iy0) iy0 = sy;
                if (sy > iy1) iy1 = sy;
            }
        }
    }
    if (ix1 < ix0 || iy1 < iy0) {
        /* No ink found - leave the slot unpublished so the draw path falls
         * back to the live triangle mark rather than blitting a blank tile. */
        s_neon_glyph_img[NEON_SIGN_SLOT].data = NULL;
        return;
    }

    memcpy(glow, core, (size_t)cov_w * (size_t)cov_h);
    neon_box_blur(glow, cov_w, cov_h, NEON_GLOW_BLUR_R);
    neon_box_blur(glow, cov_w, cov_h, NEON_GLOW_BLUR_R);

    int bx0 = ix0 - NEON_SPR_GLOW_MARGIN - cx0;
    int by0 = iy0 - NEON_SPR_GLOW_MARGIN - cy0;
    int bx1 = ix1 + NEON_SPR_GLOW_MARGIN - cx0;
    int by1 = iy1 + NEON_SPR_GLOW_MARGIN - cy0;
    if (bx0 < 0) bx0 = 0;
    if (by0 < 0) by0 = 0;
    if (bx1 > spr_w - 1) bx1 = spr_w - 1;
    if (by1 > spr_h - 1) by1 = spr_h - 1;
    bx0 &= ~(LV_DRAW_BUF_ALIGN - 1);
    by0 &= ~1;
    s_neon_glyph_bbox[NEON_SIGN_SLOT][0] = (int16_t)bx0;
    s_neon_glyph_bbox[NEON_SIGN_SLOT][1] = (int16_t)by0;
    s_neon_glyph_bbox[NEON_SIGN_SLOT][2] = (int16_t)bx1;
    s_neon_glyph_bbox[NEON_SIGN_SLOT][3] = (int16_t)by1;

    neon_store_coverage(NEON_SIGN_SLOT, core, glow, cov_w, pad,
                        spr_w, spr_h, spr_stride, glyph_bytes);
}

/* Bake the three zone words as blurred coverage tiles.
 *
 * Mirrors neon_bake_glyph_sprites() but keeps each word on its OWN crop
 * rather than a shared anchor: there are only three, they differ hugely in
 * width, and a shared tile would be sized for OVERBOOST and mostly empty for
 * BOOST. The label box the live code positions against is
 * NEON_WORD_BOX_W x NEON_WORD_BOX_H, so the recorded offsets are measured
 * from that box's top-left corner and the draw side needs no knowledge of
 * where the ink landed inside it.
 */
static void neon_bake_zone_words(lv_obj_t *scr)
{
    if (s_neon_words_ready) return;   /* layout-independent; bake once, ever */
    const int safe_w = NEON_WORD_W + 40;
    const int safe_h = NEON_WORD_H + 40;
    const int box_x = (safe_w - NEON_WORD_BOX_W) / 2;
    const int box_y = 20;

    const uint32_t scratch_bytes =
        LV_CANVAS_BUF_SIZE(safe_w, safe_h, 16, LV_DRAW_BUF_STRIDE_ALIGN);
    void *scratch_buf = BG_ALLOC(scratch_bytes);
    if (scratch_buf == NULL) return;
    lv_obj_t *scratch = lv_canvas_create(scr);
    lv_canvas_set_buffer(scratch, scratch_buf, safe_w, safe_h, LV_COLOR_FORMAT_RGB565);
    lv_obj_add_flag(scratch, LV_OBJ_FLAG_HIDDEN);

    uint32_t stride = lv_draw_buf_width_to_stride((uint32_t)NEON_WORD_W, LV_COLOR_FORMAT_A8);
    if (stride % LV_DRAW_BUF_ALIGN != 0) {
        stride += LV_DRAW_BUF_ALIGN - (stride % LV_DRAW_BUF_ALIGN);
    }
    const size_t word_bytes = (size_t)stride * (size_t)NEON_WORD_H;
    s_neon_word_buf = BG_ALLOC(word_bytes * NEON_WORD_COUNT);
    uint8_t *core = (uint8_t *)BG_ALLOC((size_t)safe_w * (size_t)safe_h);
    uint8_t *glow = (uint8_t *)BG_ALLOC((size_t)safe_w * (size_t)safe_h);
    if (s_neon_word_buf == NULL || core == NULL || glow == NULL ||
        safe_w > NEON_BLUR_MAXDIM || safe_h > NEON_BLUR_MAXDIM) {
        ESP_LOGW(TAG, "neon zone word bake alloc failed; words stay unglowed");
        BG_FREE(core); BG_FREE(glow);
        BG_FREE(s_neon_word_buf); s_neon_word_buf = NULL;
        lv_obj_delete(scratch);
        BG_FREE(scratch_buf);
        return;
    }
    memset(s_neon_word_buf, 0, word_bytes * NEON_WORD_COUNT);

    for (int wi = 0; wi < NEON_WORD_COUNT; ++wi) {
        neon_scratch_clear(scratch, 0, 0, safe_w, safe_h);
        lv_layer_t layer;
        lv_canvas_init_layer(scratch, &layer);
        lv_draw_label_dsc_t dsc; lv_draw_label_dsc_init(&dsc);
        dsc.font = NEON_LABEL;
        dsc.align = LV_TEXT_ALIGN_CENTER;
        dsc.color = lv_color_white();
        /* Must match the label styling this replaces, or the words shift. */
        dsc.letter_space = 2;
        dsc.text = k_neon_zone_words[wi];
        dsc.text_local = 0;
        lv_area_t box = { box_x, box_y,
                          box_x + NEON_WORD_BOX_W - 1, box_y + NEON_WORD_BOX_H - 1 };
        lv_draw_label(&layer, &dsc, &box);
        lv_canvas_finish_layer(scratch, &layer);

        const lv_draw_buf_t *db = lv_canvas_get_draw_buf(scratch);
        memset(core, 0, (size_t)safe_w * (size_t)safe_h);
        int ix0 = safe_w, iy0 = safe_h, ix1 = -1, iy1 = -1;
        for (int y = 0; y < safe_h; ++y) {
            const lv_color16_t *row =
                (const lv_color16_t *)(db->data + (size_t)y * db->header.stride);
            for (int x = 0; x < safe_w; ++x) {
                const uint8_t v = (uint8_t)(row[x].red * 255 / 31);
                core[(size_t)y * (size_t)safe_w + (size_t)x] = v;
                if (v) {
                    if (x < ix0) ix0 = x;
                    if (x > ix1) ix1 = x;
                    if (y < iy0) iy0 = y;
                    if (y > iy1) iy1 = y;
                }
            }
        }
        if (ix1 < ix0) continue;

        memcpy(glow, core, (size_t)safe_w * (size_t)safe_h);
        neon_box_blur(glow, safe_w, safe_h, NEON_GLOW_BLUR_R);
        neon_box_blur(glow, safe_w, safe_h, NEON_GLOW_BLUR_R);

        int cx0 = ix0 - NEON_SPR_GLOW_MARGIN, cy0 = iy0 - NEON_SPR_GLOW_MARGIN;
        int cx1 = ix1 + NEON_SPR_GLOW_MARGIN, cy1 = iy1 + NEON_SPR_GLOW_MARGIN;
        if (cx0 < 0) cx0 = 0;
        if (cy0 < 0) cy0 = 0;
        if (cx1 > safe_w - 1) cx1 = safe_w - 1;
        if (cy1 > safe_h - 1) cy1 = safe_h - 1;
        cx0 &= ~(LV_DRAW_BUF_ALIGN - 1);
        int tw = cx1 - cx0 + 1, th = cy1 - cy0 + 1;
        if (tw > NEON_WORD_W) tw = NEON_WORD_W;
        if (th > NEON_WORD_H) th = NEON_WORD_H;

        uint8_t *dst_bytes = (uint8_t *)s_neon_word_buf + (size_t)wi * word_bytes;
        for (int y = 0; y < th; ++y) {
            uint8_t *dst = dst_bytes + (size_t)y * stride;
            for (int x = 0; x < tw; ++x) {
                const size_t si = (size_t)(cy0 + y) * (size_t)safe_w + (size_t)(cx0 + x);
                int g = (glow[si] * NEON_GLOW_GAIN_PCT) / 100;
                if (g > 255) g = 255;
                dst[x] = (uint8_t)(core[si] > g ? core[si] : g);
            }
        }
        lv_image_dsc_t *img = &s_neon_word_img[wi];
        memset(img, 0, sizeof(*img));
        img->header.magic = LV_IMAGE_HEADER_MAGIC;
        img->header.cf = LV_COLOR_FORMAT_A8;
        img->header.w = (uint32_t)tw;
        img->header.h = (uint32_t)th;
        img->header.stride = stride;
        img->data_size = (uint32_t)((size_t)stride * (size_t)th);
        img->data = (const uint8_t *)dst_bytes;
        s_neon_word_dx[wi] = (int16_t)(cx0 - box_x);
        s_neon_word_dy[wi] = (int16_t)(cy0 - box_y);
        s_neon_words_ready = true;
    }

    BG_FREE(core);
    BG_FREE(glow);
    lv_obj_delete(scratch);
    BG_FREE(scratch_buf);
}

/*
 * Bake all 12 readout glyphs plus the minus mark into one PSRAM block at the
 * active layout's font size, as 8-bit coverage planes. Called once per scene
 * build from build_neon(). Coverage is colour-independent, so a zone flip -
 * or any interpolated shade between zones - is a recolor on the blit, not a
 * rebake and not a second copy of the tiles.
 *
 * Geometry pass: render every glyph in a big scratch canvas exactly the way
 * draw_neon_live() draws it today (lv_draw_label(), LV_TEXT_ALIGN_CENTER,
 * same box height), and scan for the union ink bounding box. That union plus
 * NEON_SPR_GLOW_MARGIN on every side fixes ONE crop window, reused for every
 * glyph, so every tile shares one anchor and the tile size stays uniform
 * regardless of which character is narrower (e.g. '.', '1').
 *
 * Coverage pass: render every glyph once in white, read the anti-aliased
 * result straight off as an 8-bit coverage plane (a white-on-black render
 * already IS coverage), box-blur a copy of it twice for the glow, and store
 * max(core, glow * gain) as the tile. No colour enters the bake at all - it is
 * applied per blit as the A8 recolor.
 */
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
