ZiadAbdelati/waveshare-boost-gauge/main/boost_network.c

#include "boost_network.h"

#include <string.h>

#include "esp_check.h"
#include "esp_event.h"
#include "esp_log.h"
#include "esp_mac.h"
#include "esp_wifi.h"
#include "freertos/FreeRTOS.h"
#include "freertos/event_groups.h"
#include "freertos/semphr.h"
#include "freertos/timers.h"
#include "nvs.h"
#include "nvs_flash.h"
#include "boost_app_ble.h"

#if __has_include("boost_wifi_secrets.h")
#include "boost_wifi_secrets.h"
#endif
#ifndef BOOST_WIFI_STA_SSID
#define BOOST_WIFI_STA_SSID ""
#endif
#ifndef BOOST_WIFI_STA_PASS
#define BOOST_WIFI_STA_PASS ""
#endif

#define NVS_NS "boost_wifi"
#define NVS_KEY_MODE "mode"
#define NVS_KEY_SSID "ssid"
#define NVS_KEY_PASS "pass"
#define NVS_KEY_SAVED_CNT "saved_cnt"
#define NVS_KEY_SAVED_SSID_PFX "s_ssid_"
#define NVS_KEY_SAVED_PASS_PFX "s_pass_"

#define WIFI_BIT_GOT_IP BIT0
#define WIFI_BIT_FAIL   BIT1
#define WIFI_SCAN_ACTIVE_MIN_MS 40
#define WIFI_SCAN_ACTIVE_MAX_MS 80
/* Backoff before re-attempting a dropped station association. AP and STA share
 * one radio, so an out-of-range SSID reconnects in a tight scan->fail loop that
 * repeatedly yanks the radio off the SoftAP channel; a 10 s backoff gives the
 * AP stable airtime while the saved SSID stays in NVS and is retried quietly. */
#define WIFI_SCAN_RETRY_DELAY_MS 30000

static const char *TAG = "boost_net";

static SemaphoreHandle_t s_lock;
static EventGroupHandle_t s_events;
static boost_net_config_t s_cfg;
static char s_sta_ip[16];
static char s_ap_ssid[33];
static bool s_sta_got_ip;
static bool s_started;
static int s_rssi = 0;
static esp_netif_t *s_ap_netif;
static esp_netif_t *s_sta_netif;
static TimerHandle_t s_reconnect_timer;
static uint8_t s_try_index = 0;
static uint8_t s_ap_clients = 0;
static TaskHandle_t s_scan_conn_task;

static esp_err_t apply_sta_config(void);

static void scan_and_connect_task(void *arg)
{
    (void)arg;
    
    /* If a client is connected to SoftAP or we already have an IP, skip scanning */
    if (s_ap_clients > 0 || s_sta_got_ip) {
        ESP_LOGI(TAG, "AP client connected (%d) or STA connected; skipping background scan", s_ap_clients);
        s_scan_conn_task = NULL;
        vTaskDelete(NULL);
        return;
    }

    ESP_LOGI(TAG, "running background Wi-Fi scan for saved networks");
    
    wifi_scan_config_t scan_cfg = {
        .ssid = NULL,
        .bssid = NULL,
        .channel = 0,
        .show_hidden = false,
        .scan_type = WIFI_SCAN_TYPE_ACTIVE,
        .scan_time.active.min = WIFI_SCAN_ACTIVE_MIN_MS,
        .scan_time.active.max = WIFI_SCAN_ACTIVE_MAX_MS,
    };
    
    /* Perform blocking scan on the Wi-Fi driver */
    esp_err_t err = esp_wifi_scan_start(&scan_cfg, true);
    if (err == ESP_OK) {
        uint16_t ap_count = 0;
        esp_wifi_scan_get_ap_num(&ap_count);
        if (ap_count > 0) {
            wifi_ap_record_t *aps = calloc(ap_count, sizeof(wifi_ap_record_t));
            if (aps != NULL) {
                if (esp_wifi_scan_get_ap_records(&ap_count, aps) == ESP_OK) {
                    xSemaphoreTake(s_lock, portMAX_DELAY);
                    int best_match = -1;
                    /* Check saved networks against visible APs */
                    for (uint8_t s = 0; s < s_cfg.saved_count && best_match < 0; ++s) {
                        for (uint16_t a = 0; a < ap_count; ++a) {
                            if (aps[a].ssid[0] != '\0' && strcmp(s_cfg.saved[s].ssid, (char *)aps[a].ssid) == 0) {
                                best_match = s;
                                break;
                            }
                        }
                    }
                    if (best_match >= 0) {
                        ESP_LOGI(TAG, "scan matched saved network: %s", s_cfg.saved[best_match].ssid);
                        s_try_index = (uint8_t)best_match;
                        strlcpy(s_cfg.sta_ssid, s_cfg.saved[best_match].ssid, sizeof(s_cfg.sta_ssid));
                        strlcpy(s_cfg.sta_pass, s_cfg.saved[best_match].pass, sizeof(s_cfg.sta_pass));
                        s_cfg.has_sta_pass = s_cfg.saved[best_match].has_pass;
                        apply_sta_config();
                        xSemaphoreGive(s_lock);
                        esp_wifi_connect();
                    } else {
                        ESP_LOGI(TAG, "scan found no saved networks; will re-scan later");
                        xSemaphoreGive(s_lock);
                    }
                    free(aps);
                } else {
                    free(aps);
                }
            }
        }
    } else {
        ESP_LOGW(TAG, "scan_start failed: %d", err);
    }
    
    s_scan_conn_task = NULL;
    vTaskDelete(NULL);
}

static void reconnect_timer_cb(TimerHandle_t timer)
{
    (void)timer;
    if (s_cfg.mode == BOOST_NET_MODE_APSTA && s_cfg.saved_count > 0 && !s_sta_got_ip && s_ap_clients == 0) {
        if (s_scan_conn_task == NULL) {
            xTaskCreate(scan_and_connect_task, "wifi_scan_conn", 4096, NULL, 3, &s_scan_conn_task);
        }
    }
}

static void defaults_from_secrets(boost_net_config_t *cfg)
{
    memset(cfg, 0, sizeof(*cfg));
    cfg->mode = BOOST_NET_MODE_AP;
    if (BOOST_WIFI_STA_SSID[0] != '\0') {
        strlcpy(cfg->sta_ssid, BOOST_WIFI_STA_SSID, sizeof(cfg->sta_ssid));
        strlcpy(cfg->sta_pass, BOOST_WIFI_STA_PASS, sizeof(cfg->sta_pass));
        cfg->has_sta_pass = cfg->sta_pass[0] != '\0';
        cfg->mode = BOOST_NET_MODE_APSTA;
        cfg->saved_count = 1;
        strlcpy(cfg->saved[0].ssid, cfg->sta_ssid, sizeof(cfg->saved[0].ssid));
        strlcpy(cfg->saved[0].pass, cfg->sta_pass, sizeof(cfg->saved[0].pass));
        cfg->saved[0].has_pass = cfg->has_sta_pass;
    }
}

static esp_err_t save_locked(void)
{
    nvs_handle_t h;
    esp_err_t err = nvs_open(NVS_NS, NVS_READWRITE, &h);
    if (err != ESP_OK) {
        return err;
    }
    err = nvs_set_u8(h, NVS_KEY_MODE, (uint8_t)s_cfg.mode);
    if (err == ESP_OK) {
        err = nvs_set_str(h, NVS_KEY_SSID, s_cfg.sta_ssid);
    }
    if (err == ESP_OK) {
        err = nvs_set_str(h, NVS_KEY_PASS, s_cfg.sta_pass);
    }
    if (err == ESP_OK) {
        err = nvs_set_u8(h, NVS_KEY_SAVED_CNT, s_cfg.saved_count);
    }
    for (uint8_t i = 0; err == ESP_OK && i < BOOST_NET_MAX_SAVED; ++i) {
        char k_ssid[16], k_pass[16];
        snprintf(k_ssid, sizeof(k_ssid), "%s%u", NVS_KEY_SAVED_SSID_PFX, (unsigned)i);
        snprintf(k_pass, sizeof(k_pass), "%s%u", NVS_KEY_SAVED_PASS_PFX, (unsigned)i);
        if (i < s_cfg.saved_count) {
            err = nvs_set_str(h, k_ssid, s_cfg.saved[i].ssid);
            if (err == ESP_OK) {
                err = nvs_set_str(h, k_pass, s_cfg.saved[i].pass);
            }
        } else {
            nvs_erase_key(h, k_ssid);
            nvs_erase_key(h, k_pass);
        }
    }
    if (err == ESP_OK) {
        err = nvs_commit(h);
    }
    nvs_close(h);
    return err;
}

static void load_config(void)
{
    defaults_from_secrets(&s_cfg);
    nvs_handle_t h;
    if (nvs_open(NVS_NS, NVS_READONLY, &h) != ESP_OK) {
        return;
    }
    uint8_t mode = (uint8_t)s_cfg.mode;
    if (nvs_get_u8(h, NVS_KEY_MODE, &mode) == ESP_OK) {
        s_cfg.mode = (mode == BOOST_NET_MODE_APSTA) ? BOOST_NET_MODE_APSTA : BOOST_NET_MODE_AP;
    }
    size_t len = sizeof(s_cfg.sta_ssid);
    char ssid[sizeof(s_cfg.sta_ssid)] = {0};
    if (nvs_get_str(h, NVS_KEY_SSID, ssid, &len) == ESP_OK) {
        strlcpy(s_cfg.sta_ssid, ssid, sizeof(s_cfg.sta_ssid));
    }
    len = sizeof(s_cfg.sta_pass);
    char pass[sizeof(s_cfg.sta_pass)] = {0};
    if (nvs_get_str(h, NVS_KEY_PASS, pass, &len) == ESP_OK) {
        strlcpy(s_cfg.sta_pass, pass, sizeof(s_cfg.sta_pass));
    }
    s_cfg.has_sta_pass = s_cfg.sta_pass[0] != '\0';

    uint8_t saved_cnt = 0;
    if (nvs_get_u8(h, NVS_KEY_SAVED_CNT, &saved_cnt) == ESP_OK) {
        if (saved_cnt > BOOST_NET_MAX_SAVED) {
            saved_cnt = BOOST_NET_MAX_SAVED;
        }
        s_cfg.saved_count = 0;
        for (uint8_t i = 0; i < saved_cnt; ++i) {
            char k_ssid[16], k_pass[16];
            snprintf(k_ssid, sizeof(k_ssid), "%s%u", NVS_KEY_SAVED_SSID_PFX, (unsigned)i);
            snprintf(k_pass, sizeof(k_pass), "%s%u", NVS_KEY_SAVED_PASS_PFX, (unsigned)i);
            char s_buf[sizeof(s_cfg.saved[0].ssid)] = {0};
            char p_buf[sizeof(s_cfg.saved[0].pass)] = {0};
            size_t s_len = sizeof(s_buf), p_len = sizeof(p_buf);
            if (nvs_get_str(h, k_ssid, s_buf, &s_len) == ESP_OK && s_buf[0] != '\0') {
                nvs_get_str(h, k_pass, p_buf, &p_len);
                strlcpy(s_cfg.saved[s_cfg.saved_count].ssid, s_buf, sizeof(s_cfg.saved[0].ssid));
                strlcpy(s_cfg.saved[s_cfg.saved_count].pass, p_buf, sizeof(s_cfg.saved[0].pass));
                s_cfg.saved[s_cfg.saved_count].has_pass = p_buf[0] != '\0';
                s_cfg.saved_count++;
            }
        }
    } else if (s_cfg.sta_ssid[0] != '\0') {
        /* Migration from single-credential NVS */
        s_cfg.saved_count = 1;
        strlcpy(s_cfg.saved[0].ssid, s_cfg.sta_ssid, sizeof(s_cfg.saved[0].ssid));
        strlcpy(s_cfg.saved[0].pass, s_cfg.sta_pass, sizeof(s_cfg.saved[0].pass));
        s_cfg.saved[0].has_pass = s_cfg.has_sta_pass;
    }

    /* NVS present with empty SSID forces SoftAP-only even if secrets exist. */
    if (s_cfg.sta_ssid[0] == '\0') {
        s_cfg.mode = BOOST_NET_MODE_AP;
    } else if (s_cfg.mode == BOOST_NET_MODE_APSTA && !s_cfg.has_sta_pass) {
        /* open STA allowed */
    }
    nvs_close(h);
}

static void fill_ap_ssid(void)
{
    uint8_t mac[6] = {0};
    esp_read_mac(mac, ESP_MAC_WIFI_SOFTAP);
    snprintf(s_ap_ssid, sizeof(s_ap_ssid), "BoostGauge-%02X%02X", mac[4], mac[5]);
}

static esp_err_t apply_ap_config(void)
{
    wifi_config_t ap = {0};
    strlcpy((char *)ap.ap.ssid, s_ap_ssid, sizeof(ap.ap.ssid));
    strlcpy((char *)ap.ap.password, BOOST_AP_PASSWORD, sizeof(ap.ap.password));
    ap.ap.ssid_len = strlen(s_ap_ssid);
    ap.ap.channel = 6;
    ap.ap.max_connection = 4;
    ap.ap.authmode = WIFI_AUTH_WPA_WPA2_PSK;
    return esp_wifi_set_config(WIFI_IF_AP, &ap);
}

static esp_err_t apply_sta_config(void)
{
    wifi_config_t sta = {0};
    const size_t ssid_len = strlen(s_cfg.sta_ssid);
    if (ssid_len == 0 || ssid_len >= sizeof(sta.sta.ssid)) {
        return ESP_ERR_INVALID_ARG;
    }
    memcpy(sta.sta.ssid, s_cfg.sta_ssid, ssid_len);
    strlcpy((char *)sta.sta.password, s_cfg.sta_pass, sizeof(sta.sta.password));
    sta.sta.threshold.authmode = s_cfg.sta_pass[0] ? WIFI_AUTH_WPA2_PSK : WIFI_AUTH_OPEN;
    sta.sta.pmf_cfg.capable = true;
    sta.sta.pmf_cfg.required = false;
    return esp_wifi_set_config(WIFI_IF_STA, &sta);
}
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
