ZiadAbdelati/waveshare-boost-gauge/main/boost_obd_ble.c

#include "boost_obd_ble.h"
#include "boost_app_ble.h"

#include <stdbool.h>
#include <stdint.h>
#include <string.h>

#include "esp_log.h"
#include "esp_timer.h"
#include "esp_heap_caps.h"
#include "freertos/FreeRTOS.h"
#include "freertos/queue.h"
#include "freertos/task.h"
#include "nvs.h"
#include "nvs_flash.h"
#include "os/os_mbuf.h"

#include "nimble/nimble_port.h"
#include "nimble/nimble_port_freertos.h"
#include "host/ble_hs.h"
#include "host/ble_gap.h"
#include "host/ble_gatt.h"
#include "host/util/util.h"

/*
 * NimBLE host task -> driver task mailbox. The driver task owns every
 * ble_gap/ble_gattc call, so writes and the connect/discover/subscribe
 * sequence are serialised on one thread; the host callbacks only post events.
 *
 * Note: this NimBLE version removed ble_gattc_subscribe(); subscribing to the
 * adapter's RX characteristic is done by writing 0x0001 (notify) to its CCCD
 * descriptor.
 */
#define OBD_EV_QUEUE_LEN   12
#define OBD_MAX_WRITE      64
#define OBD_MAX_RX         256
#define OBD_MAX_CHR_CAND   8
#define OBD_ADV_SCAN_MS    3000
#define OBD_RECONNECT_MS   10000
/* When the adapter is consistently unreachable (bench, adapter unplugged) the
 * old loop scanned every ~13 s forever, saturating the shared 2.4 GHz radio
 * and spiking web latency. Back off the scan interval exponentially after each
 * failed cycle, capped, so an absent peer stops hammering the radio while a
 * present one is still found within one scan period. Reset on any connect. */
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
